fsguerreiro/My_thesis/figs/schemes.pptx

Measurements:
Air flow rate
Air flow temperature
Air flow relative humidity

FRONT VIEW

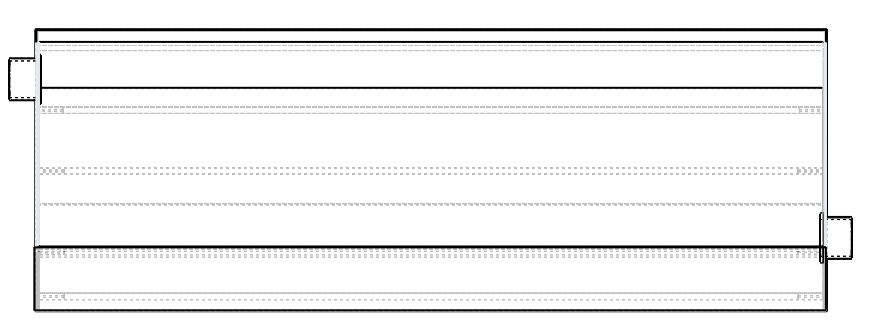
[picture p1: figure]

FAN

OUTLET

INLET

Pressure meter
ΔP = Poutlet - Pinlet

Measurements:
Air flow temperature
Air flow relative humidity

## Slide 2

Material and Instruments for 1 collector

Component | Dimension | | Instrument | Quantity | Range
Reflector Sheet | 1.32m x 1.25m | | Air Flow Meter | 1 | 0 - 20 m/s or 0 - 120 ft³/min
Tempered, Low-e Glass | 270mm x 1246mm x 4 mm | | Fan/Blower | 1 | 10 W
Wool | 1.32m x 1.25m x 5cm | | Pressure Meter | 1 | 0 - 100 Pa or 0 - 10 mmHg
Aluminium Sheet | 1.5m x 1.3m x 1.5mm | | Humidity Meter | 2 | 0 - 100% RH
2 Pipe Connection w/ flange | 10 cm long; 2.5 in of inner diameter | | Thermocouple | 14 | 0 - 200 ºC
Type of experiments w/ control system:
1. Set-point of air flow rate;
2. Set-point of outlet air temperature by manipulating air flow;
3. Set-point of energy delivered by manipulating air flow.

## Slide 3

## Slide 4

l

Absorber
surface

Absorber
hole

dH

## Slide 5

Absorber
hole

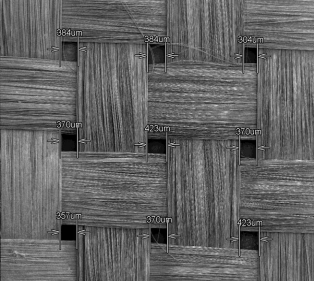
[picture p2: figure]

Absorber surface

l

φh

## Slide 6

y-axis (vertical)

Solar ray

xz plane (top view)

xy plane (cross section view)

z-axis

y-axis (vertical)

Solar ray

αs

z-axis

Solar ray

x-axis (south)

x-axis (south)

γs

γs

αs

x-axis (south)

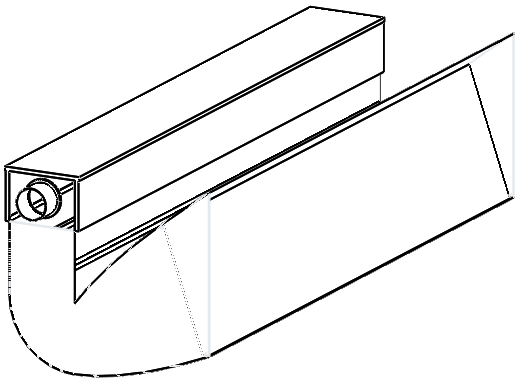
[picture p3: figure]

y-axis

z-axis

x-axis

## Slide 7

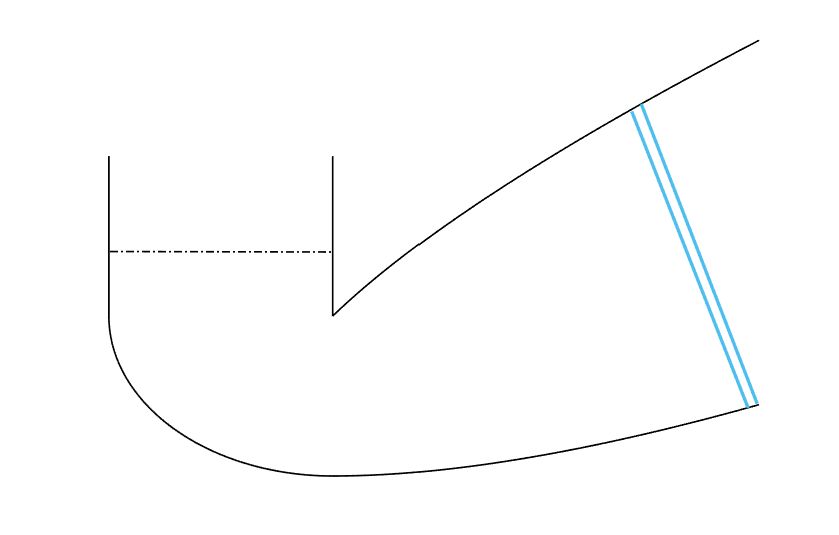
[picture p4: figure]

SOLAR
RADIATION

USEFUL
HEAT

CONVECTION
LOSS

Absorber

RADIATION
LOSS

SOLAR
RADIATION

CONVECTION
LOSS

Glazing

RADIATION
LOSS

## Slide 8

RADIAÇÃO
SOLAR

CALOR
ÚTIL

Absorvedor

PERDAS
CONVECTIVAS

PERDAS
RADIATIVAS

RADIAÇÃO
SOLAR
ABSORVIDA

PERDAS
CONVECTIVAS

Vidro

PERDAS
RADIATIVAS

## Slide 9

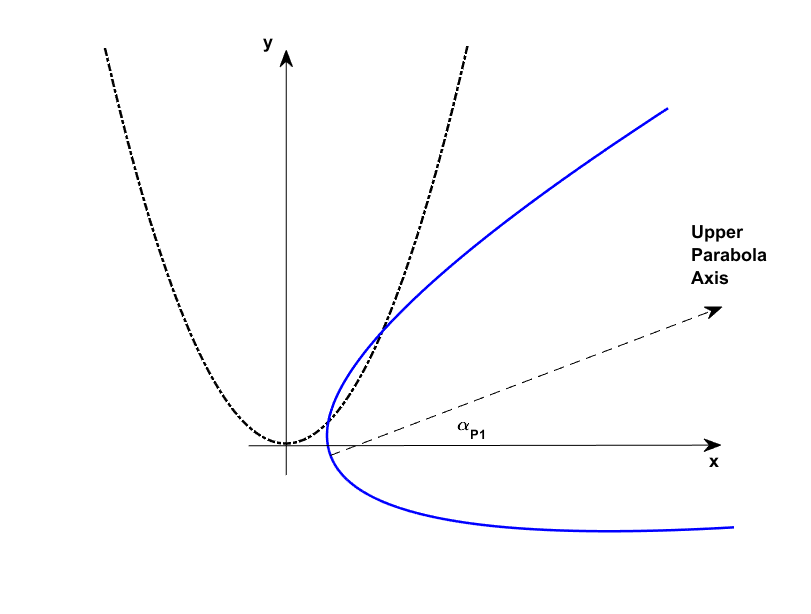
[picture p5: figure]

## Slide 10

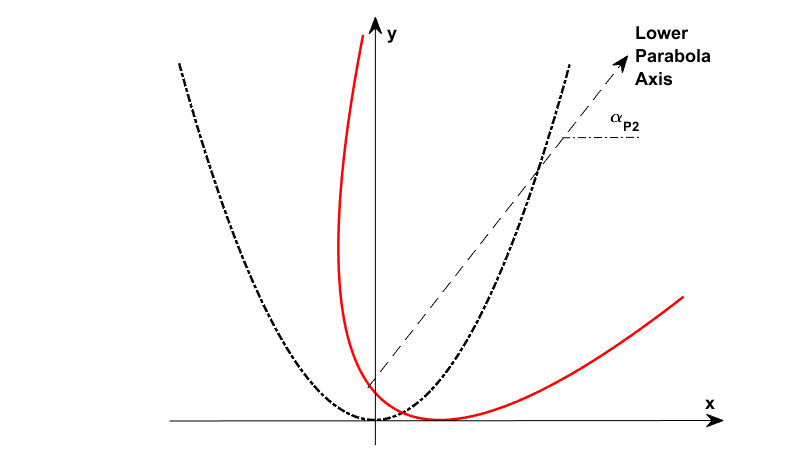
[picture p6: figure]

## Slide 11

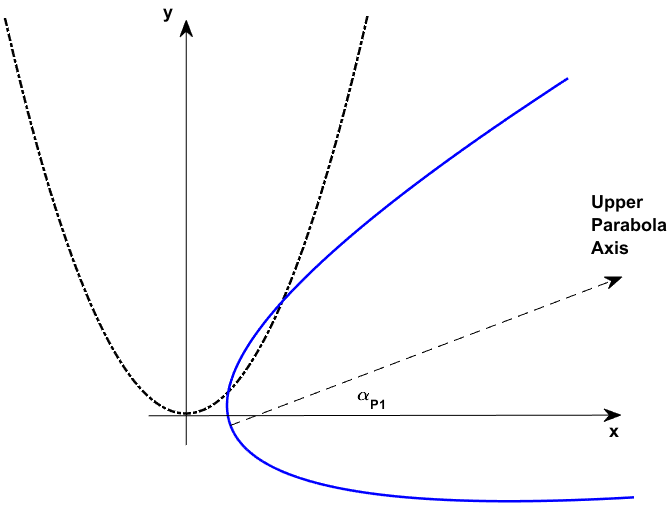
[picture p7: figure]
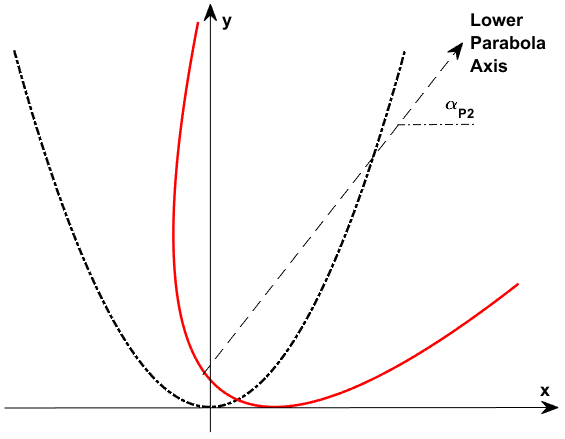
[picture p8: figure]

(a)

(b)

## Slide 12

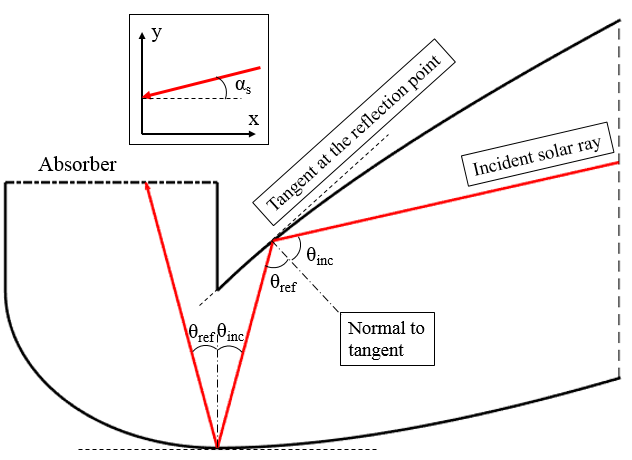
[picture p9: figure]
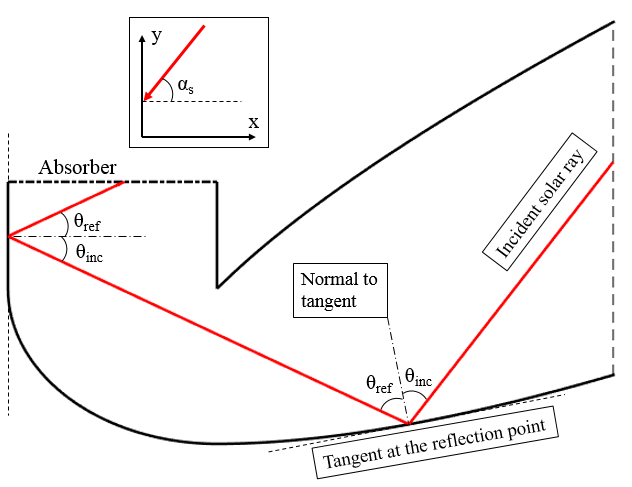
[picture p10: figure]

## Slide 13

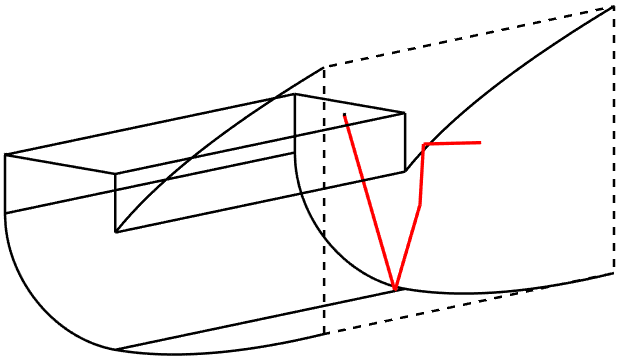
[picture p11: figure]

(a)

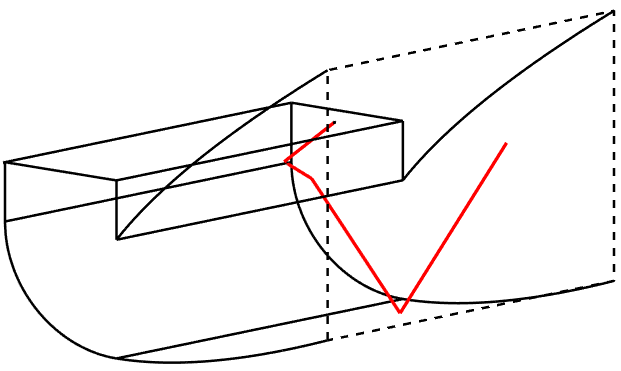
[picture p12: figure]

(d)

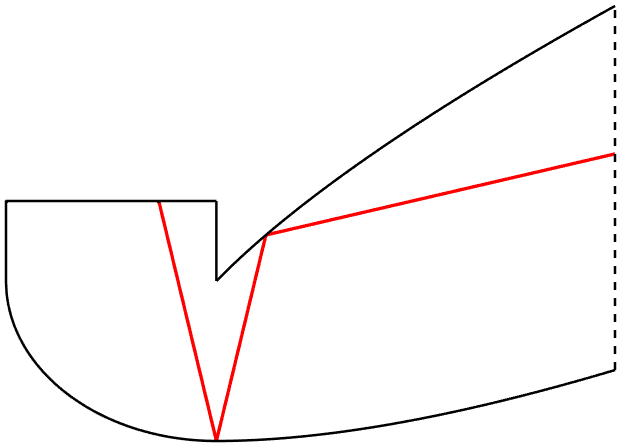
[picture p13: figure]

(b)

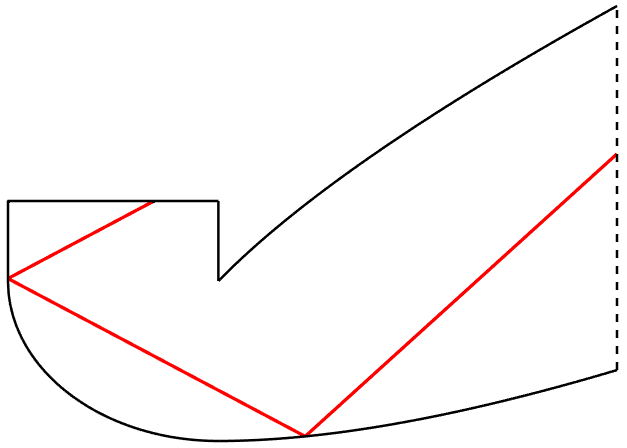
[picture p14: figure]

(e)

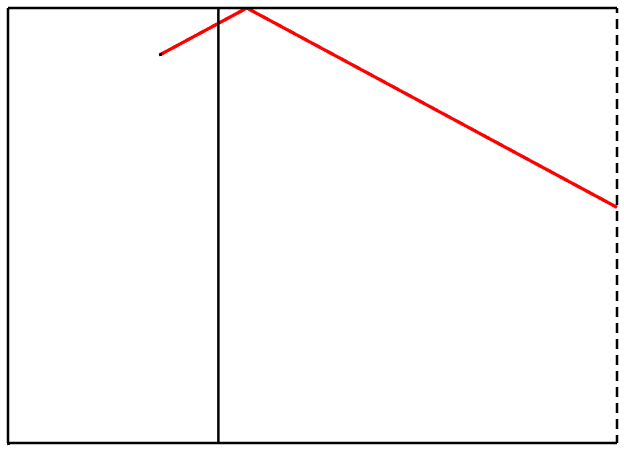
[picture p15: figure]
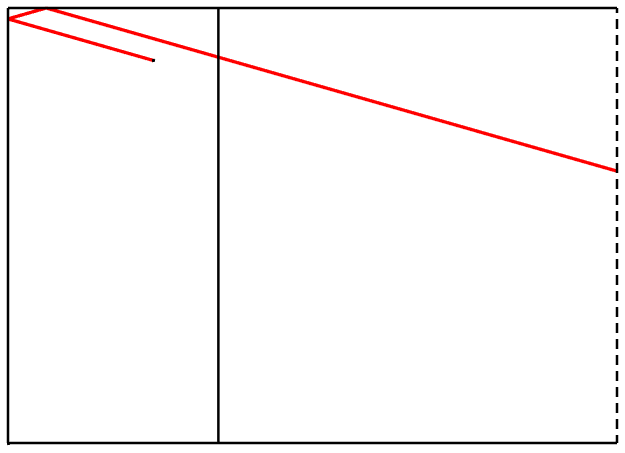
[picture p16: figure]

(c)

(f)

## Slide 14

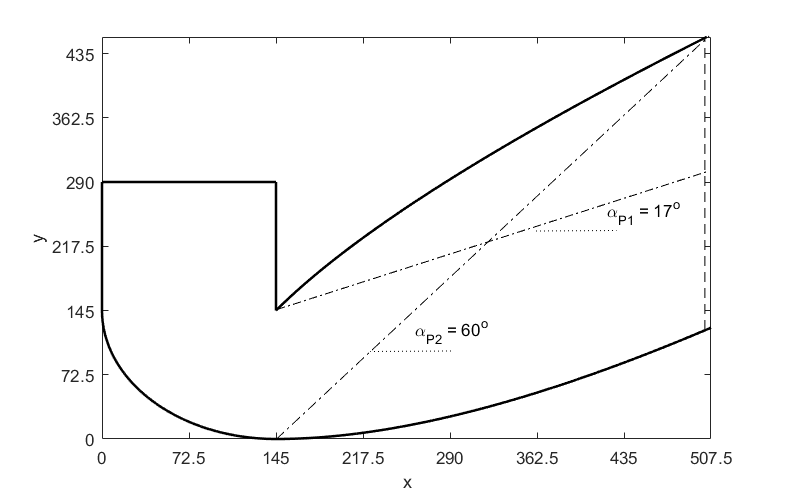
[picture p17: figure]

## Slide 15

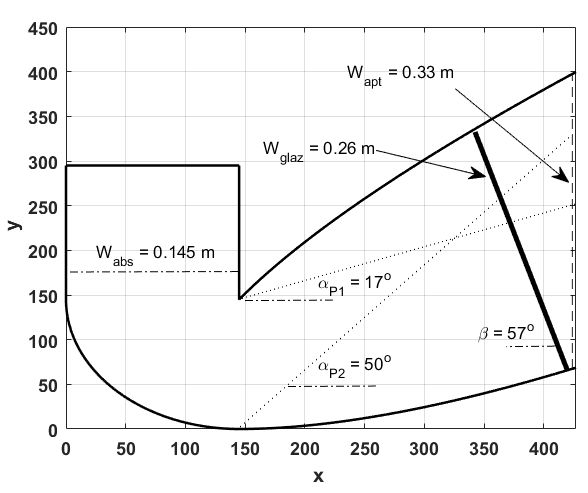
[picture p18: figure]

## Slide 16

POWERSUPPLY

FAN

OUTLET

PROTOTYPE

INLET

## Slide 17

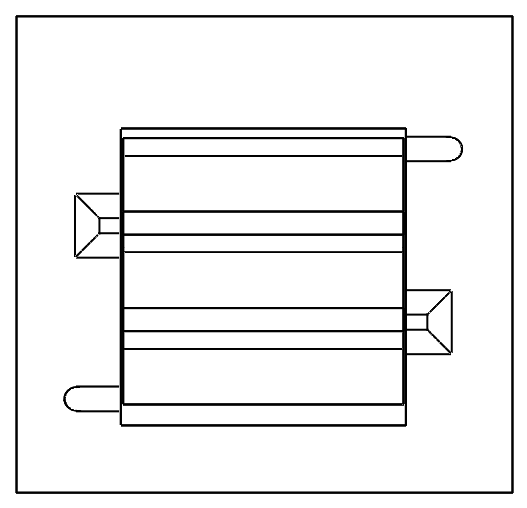
[picture p19: figure]

outlet

IACPC 3

IACPC 2

IACPC 1

inlet

## Slide 18

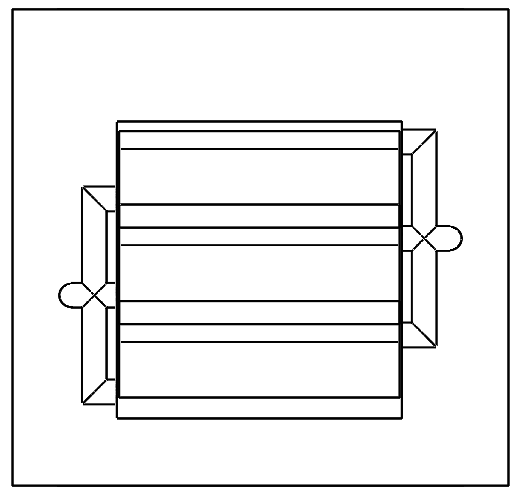
[picture p20: figure]

IACPC 3

IACPC 2

outlet

inlet

IACPC 1

## Slide 19

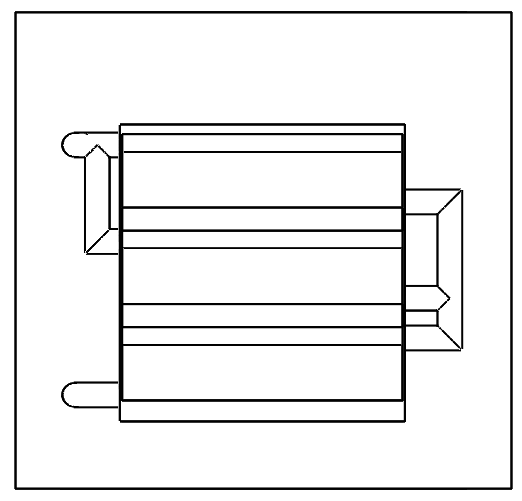
[picture p21: figure]

outlet

IACPC 3

IACPC 2

IACPC 1

inlet

## Slide 20

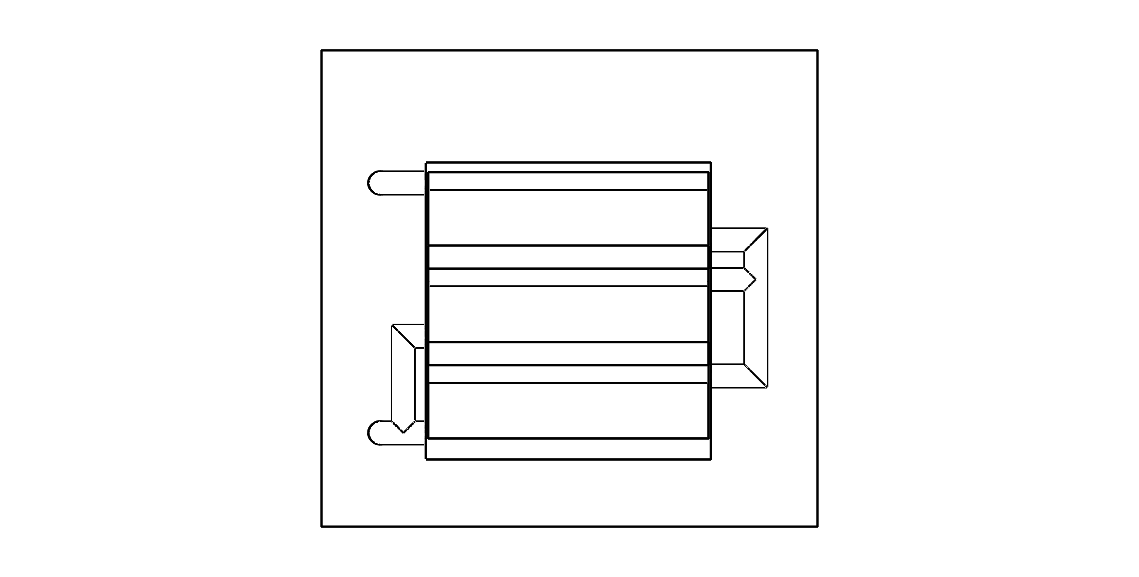
[picture p22: figure]

outlet

IACPC 3

IACPC 2

IACPC 1

inlet

## Slide 21

Main heater (gas burner)

Barley dryer

Auxiliary system (solar collector(s))
