fsguerreiro/My_thesis/figs/schematics_intro-eps-converted-to.pdf

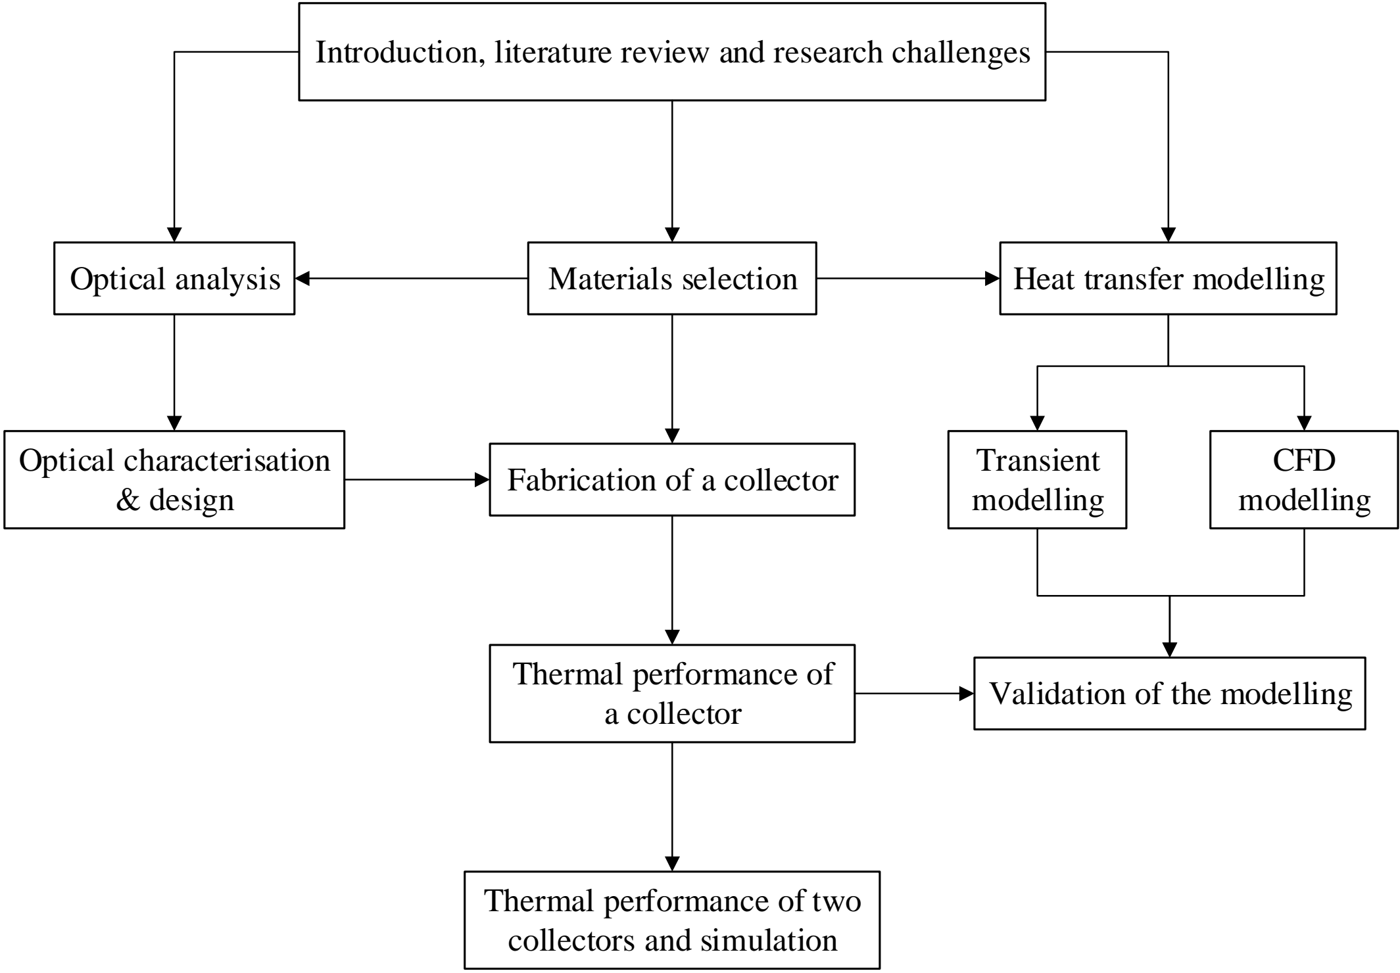
[picture p23: figure]
Materials selection; Fabrication of a collector; Optical analysis; Heat transfer modelling; Transient modelling; CFD modelling; Optical characterisation & design; Thermal performance of; a collector; Validation of the modelling; Thermal performance of two collectors and simulation

Introduction, literature review and research challenges
