fsguerreiro/My_thesis/figs/block_diagram-eps-converted-to.pdf

## AIR HEATING SYSTEM’S HEAT TRANSFER MODEL

Outlet air temperature (Tout)

Thermal efficiency (ηth)

Useful energy rate (Qu)

Airflow rate (Gair)

Ambient temperature (Tamb) and wind speed (vw)

Solar radiation (IT)

Inlet air temperature (Tin)
