fsguerreiro/My_thesis/figs/case_ch4-eps-converted-to.pdf

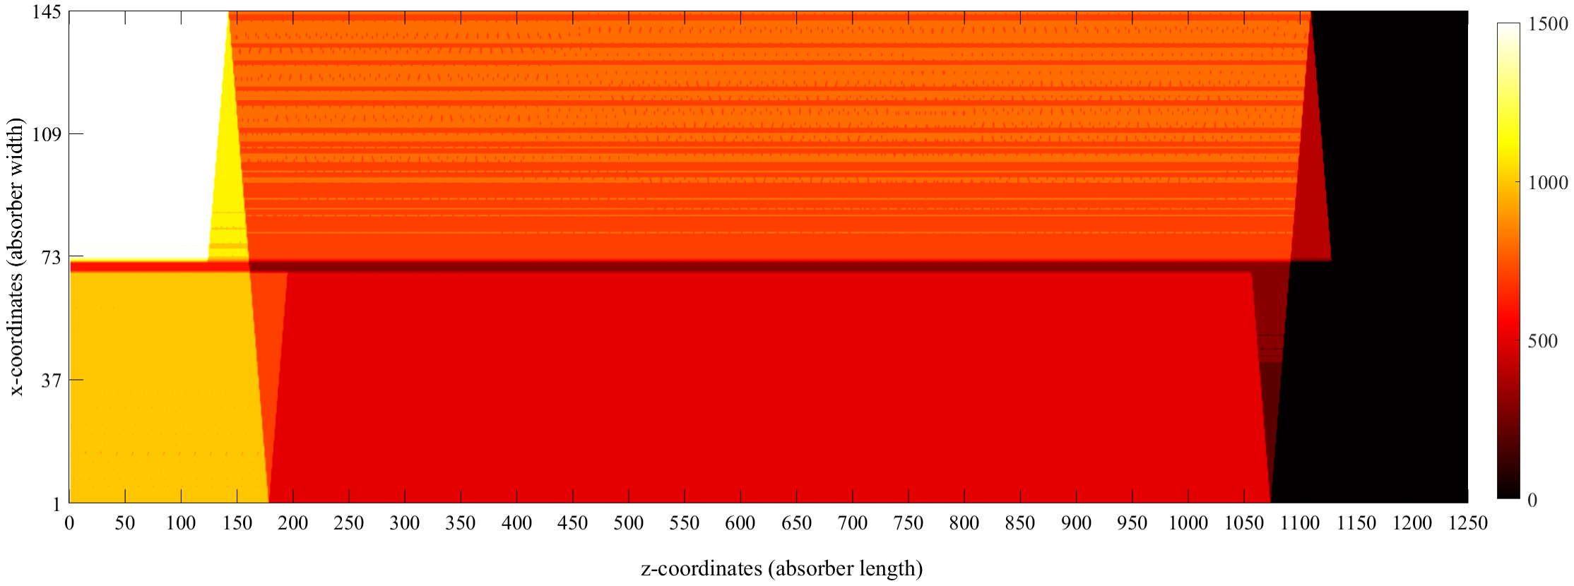
[picture p29: page 1]
