fsguerreiro/My_thesis/figs/3D-diagram-15-eps-converted-to.pdf

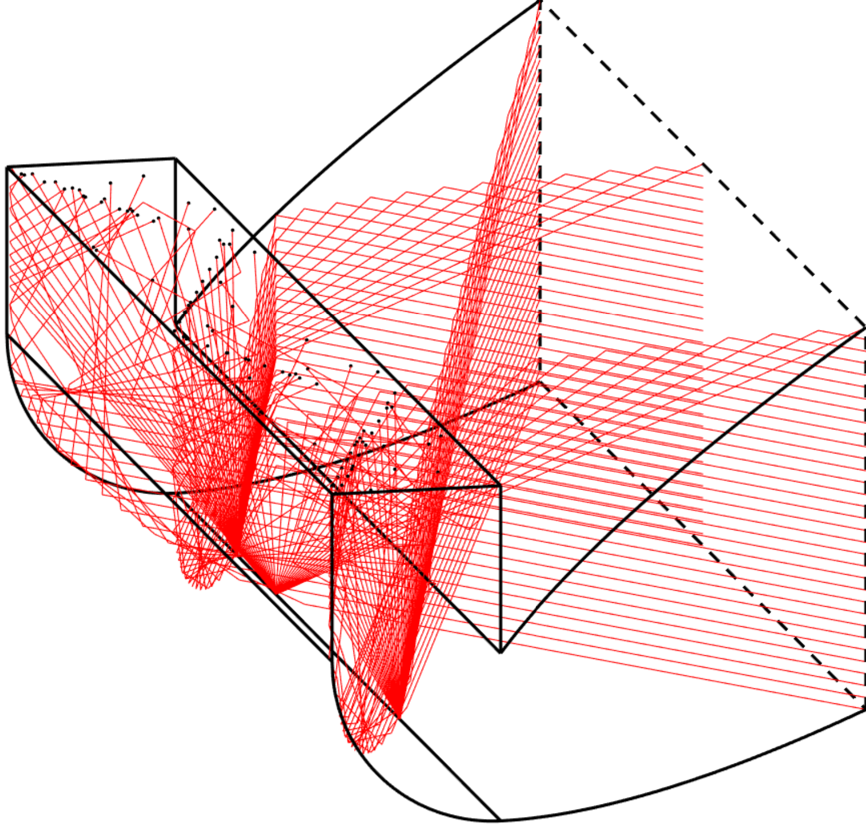
[picture p30: page 1]
