fsguerreiro/My_thesis/figs/3D-diagram-60-eps-converted-to.pdf

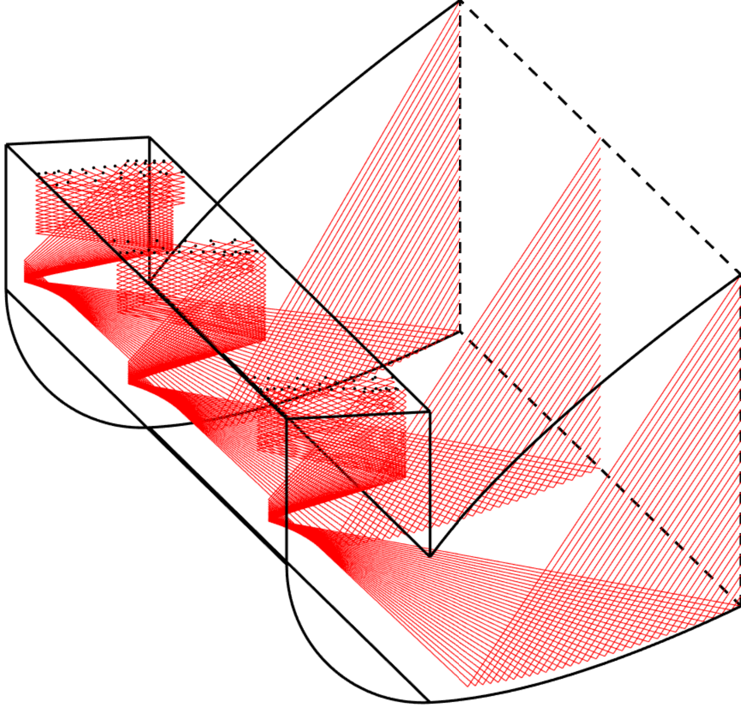
[picture p31: page 1]
