fsguerreiro/My_thesis/figs/cdf_Q-eps-converted-to.pdf

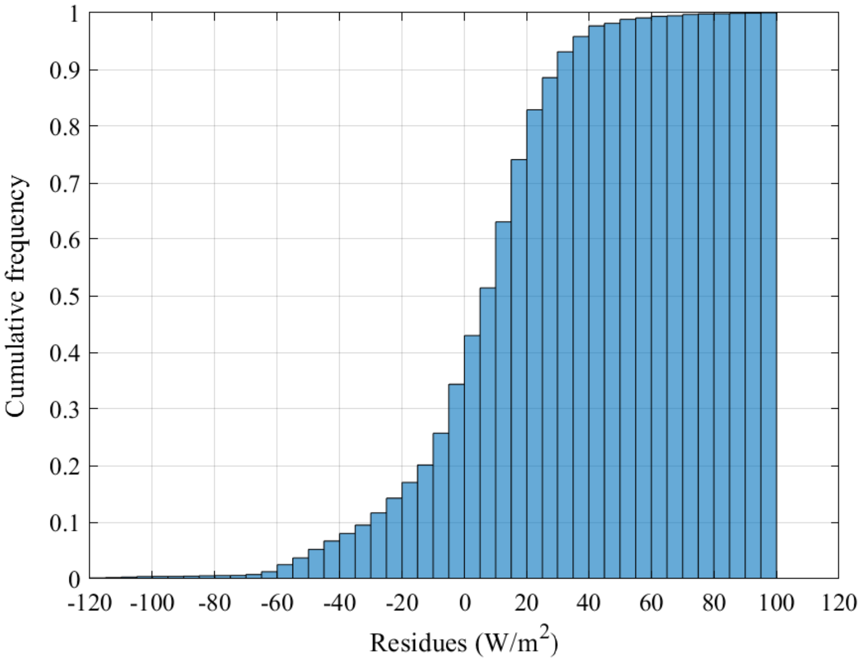
[picture p32: page 1]
