fsguerreiro/My_thesis/figs/cdf_T-eps-converted-to.pdf

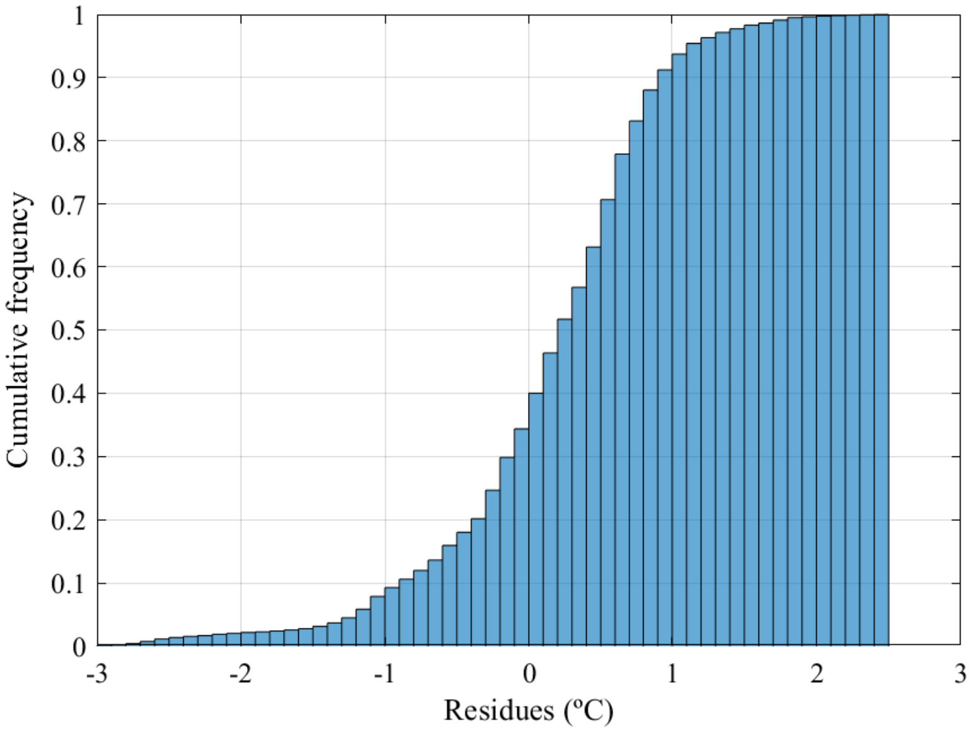
[picture p33: page 1]
