fsguerreiro/My_thesis/figs/collector3p-eps-converted-to.pdf

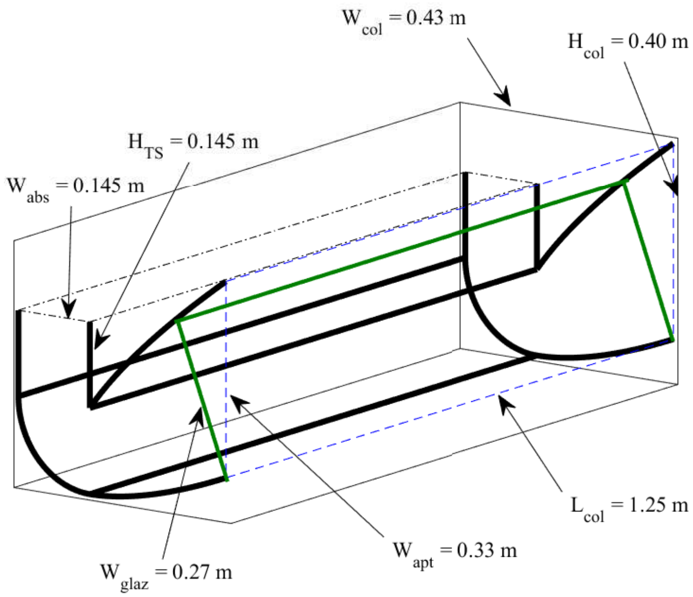
[picture p34: page 1]
