fsguerreiro/My_thesis/figs/energy-54-49-hts0-eps-converted-to.pdf

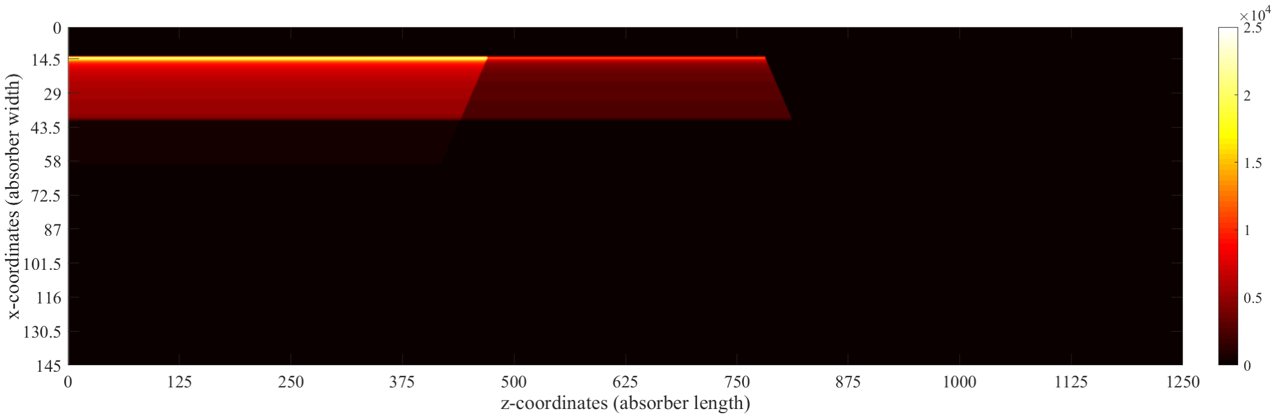
[picture p35: page 1]
