fsguerreiro/My_thesis/figs/Energy2D-hts0-eps-converted-to.pdf

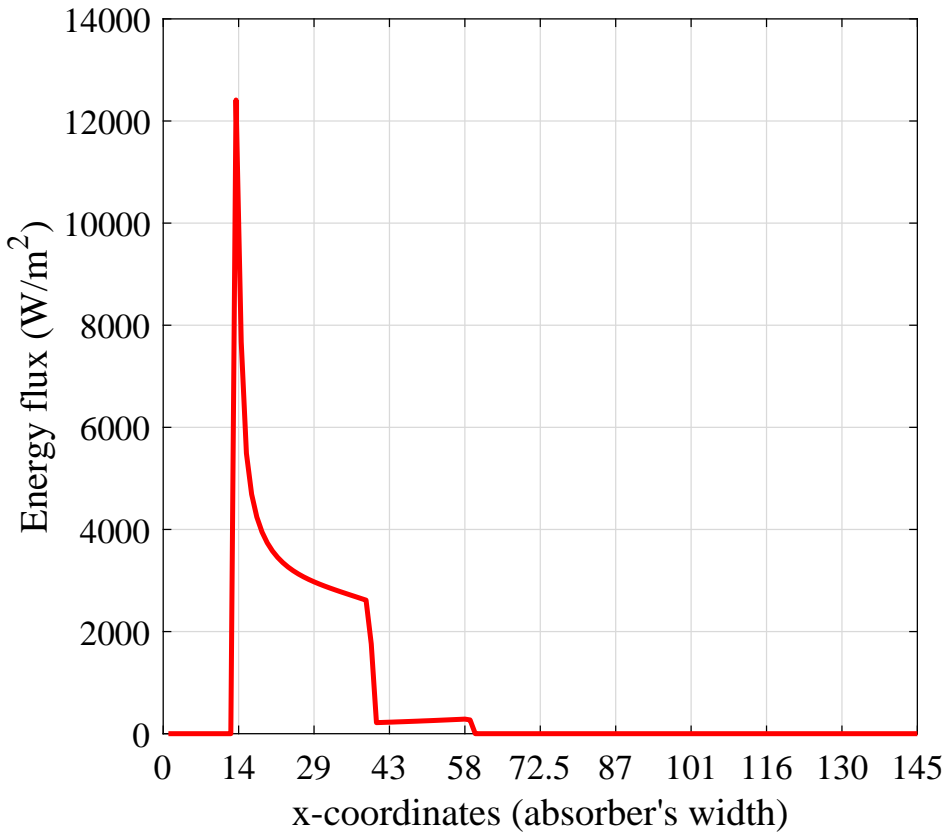
[picture p36: figure]
x-coordinates (absorber's width); Energy flux (W/m
