fsguerreiro/My_thesis/figs/Energy2D-hts145-eps-converted-to.pdf

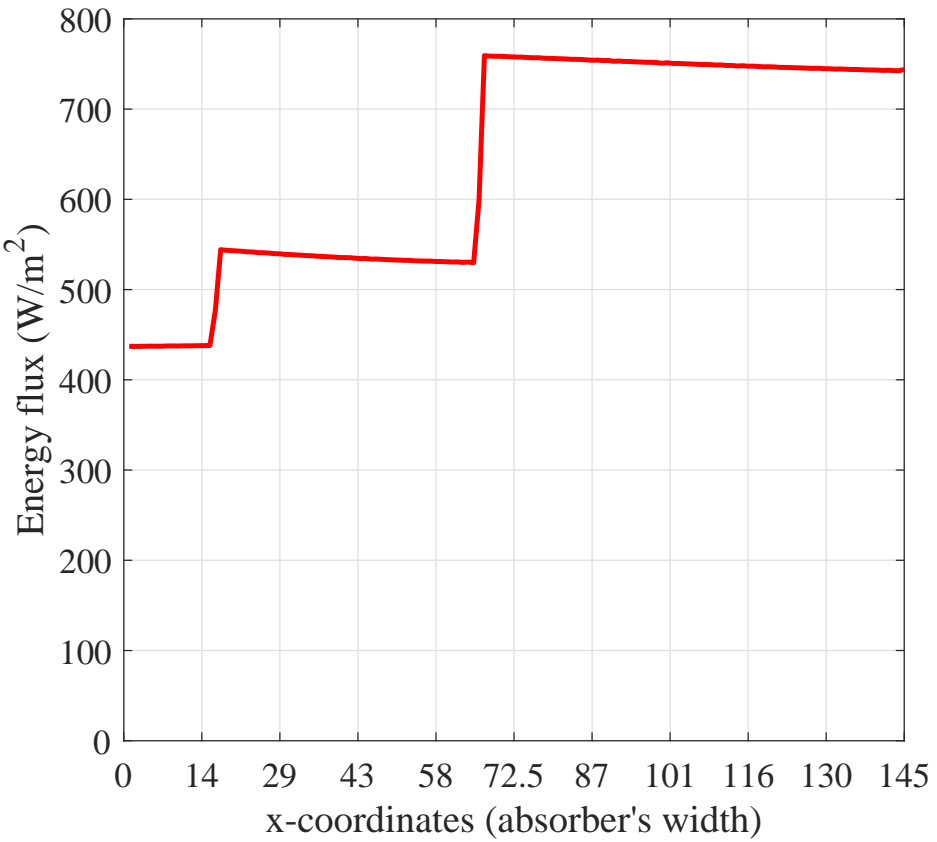
[picture p37: figure]
x-coordinates (absorber's width); Energy flux (W/m
