fsguerreiro/My_thesis/figs/Energy2D-hts72-eps-converted-to.pdf

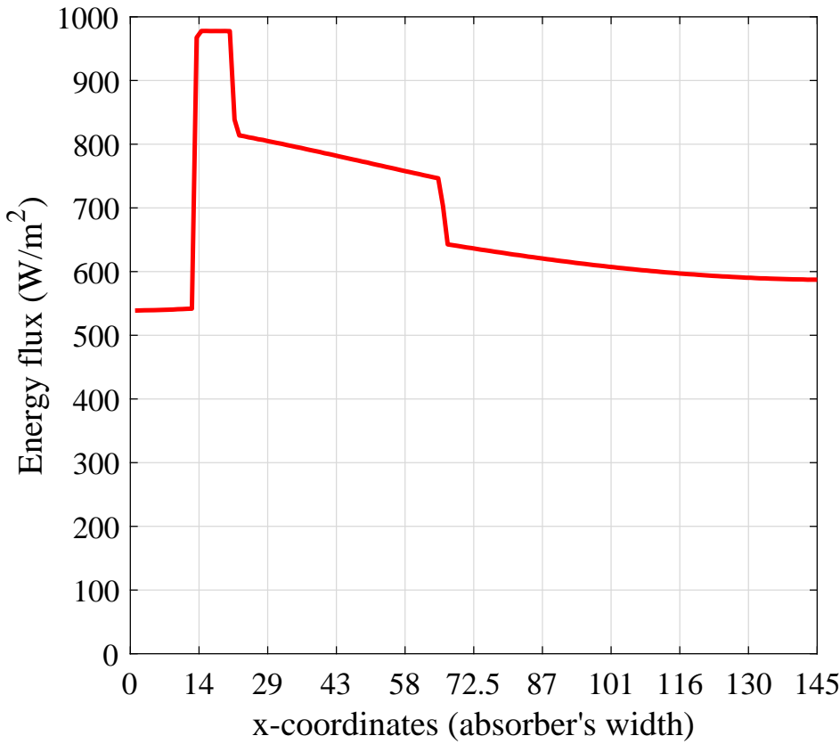
[picture p38: figure]
x-coordinates (absorber's width); Energy flux (W/m
