fsguerreiro/My_thesis/figs/Energy3D-hts0-eps-converted-to.pdf

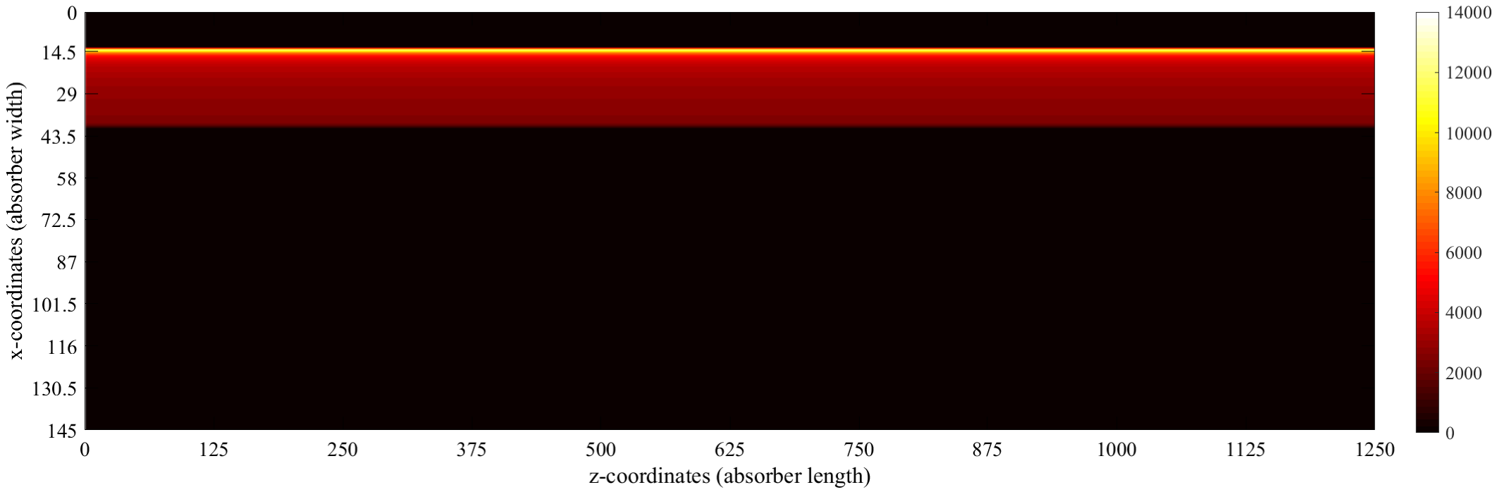
[picture p39: page 1]
