fsguerreiro/My_thesis/figs/opt-eff-time-eps-converted-to.pdf

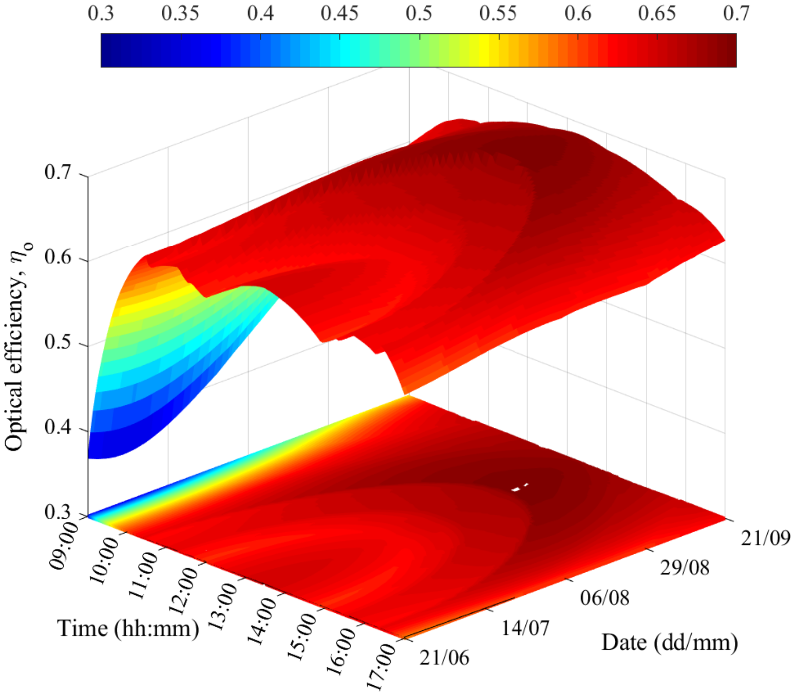
[picture p40: page 1]
