fsguerreiro/My_thesis/figs/2D-diagram-15.png

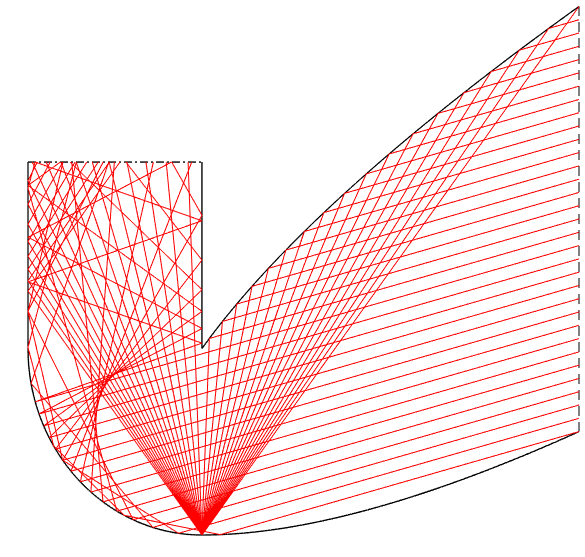
figs/2D-diagram-15.png
