fsguerreiro/My_thesis/figs/2D-diagram-60.png

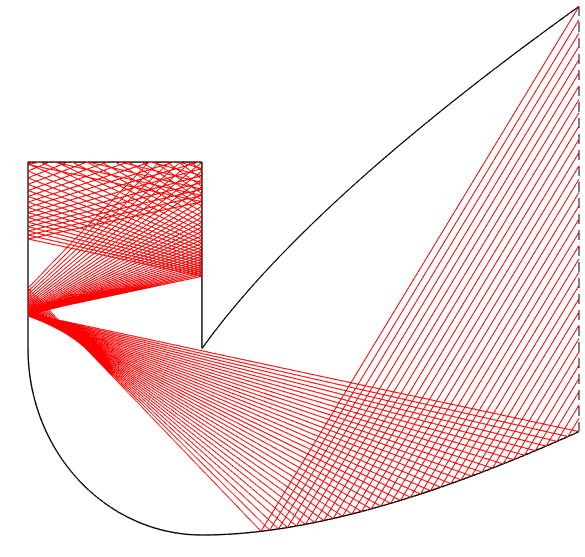
figs/2D-diagram-60.png
