fsguerreiro/My_thesis/figs/3D-diagram-1.png

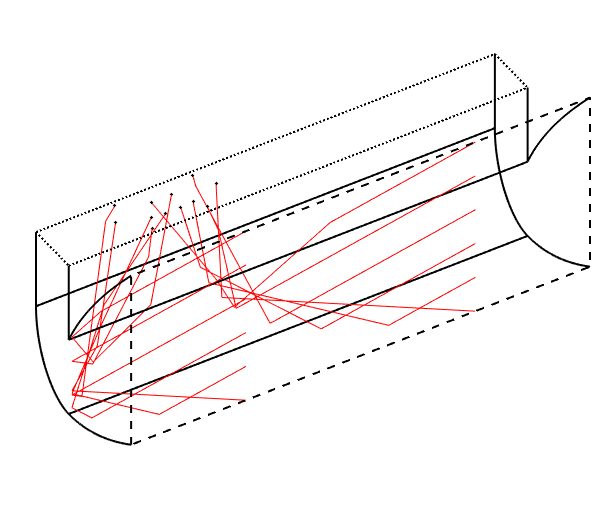
figs/3D-diagram-1.png
