fsguerreiro/My_thesis/figs/3D-diagram-15.png

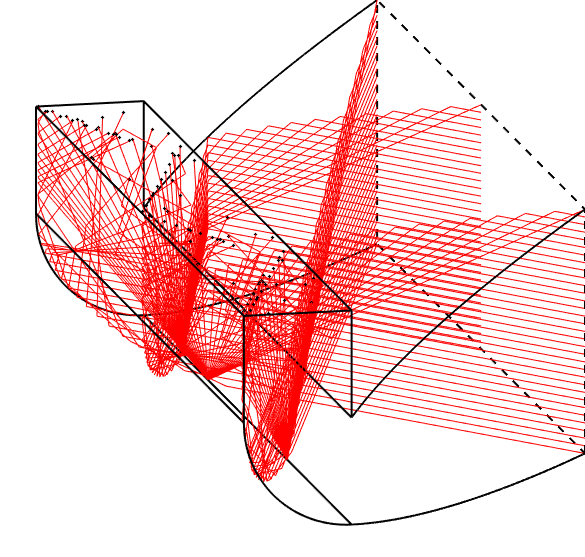
figs/3D-diagram-15.png
