fsguerreiro/My_thesis/figs/3D-diagram-60.png

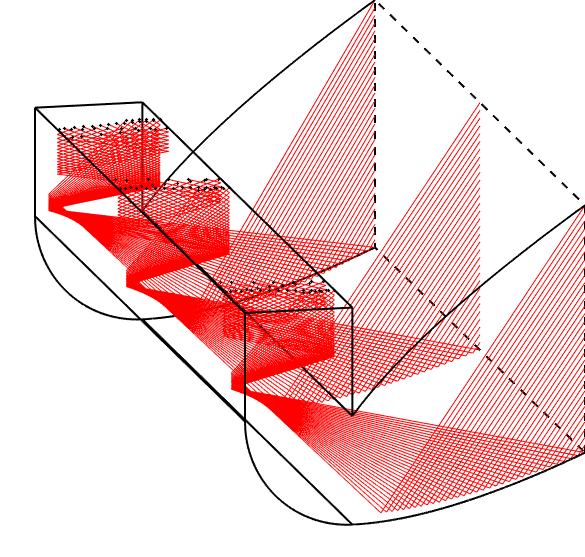
figs/3D-diagram-60.png
