fsguerreiro/My_thesis/figs/004-1.png

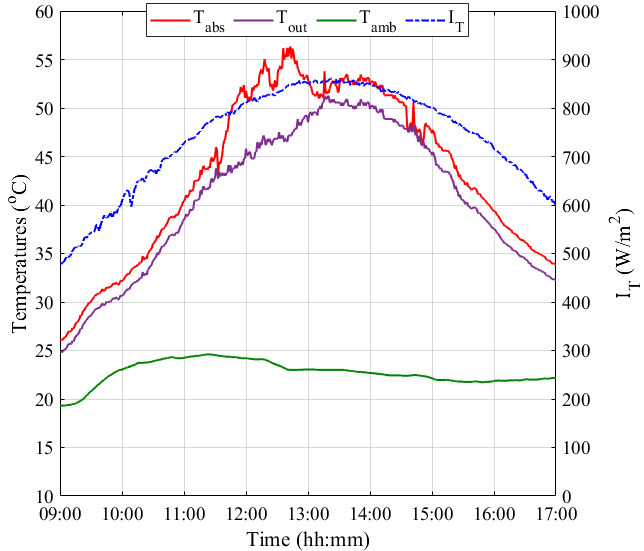
figs/004-1.png
