fsguerreiro/My_thesis/figs/004-2.png

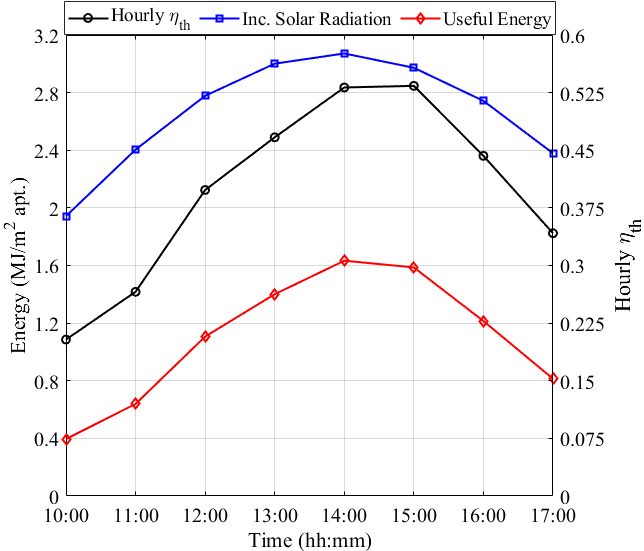
figs/004-2.png
