fsguerreiro/My_thesis/figs/004-3.png

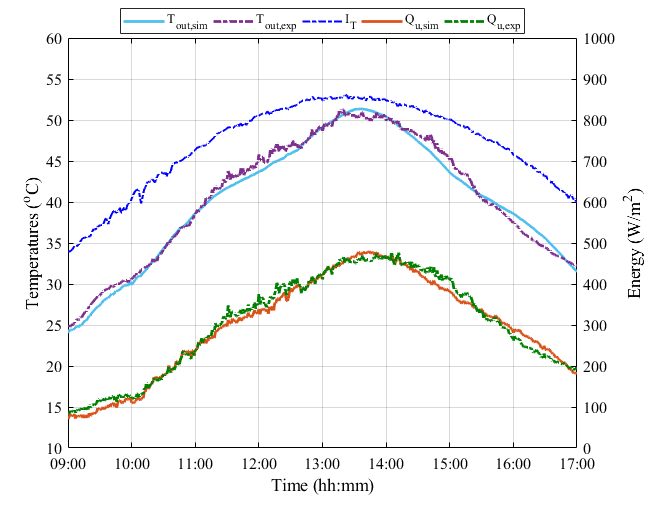
figs/004-3.png
