fsguerreiro/My_thesis/figs/004-residue-1.png

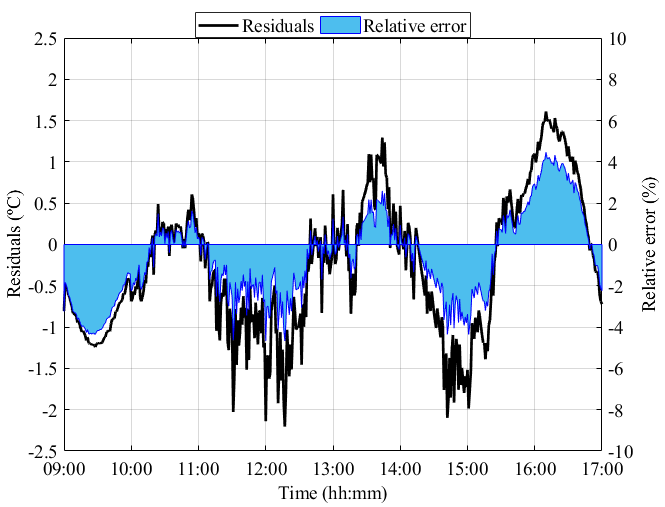
figs/004-residue-1.png
