fsguerreiro/My_thesis/figs/004-residue-2.png

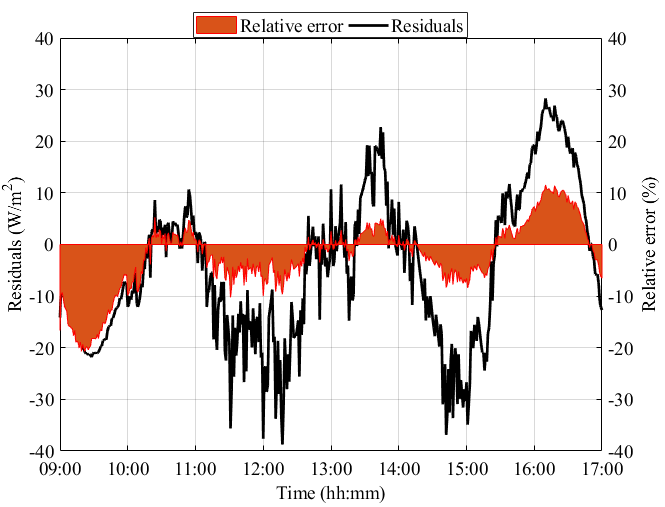
figs/004-residue-2.png
