fsguerreiro/My_thesis/figs/004-residue-3.png

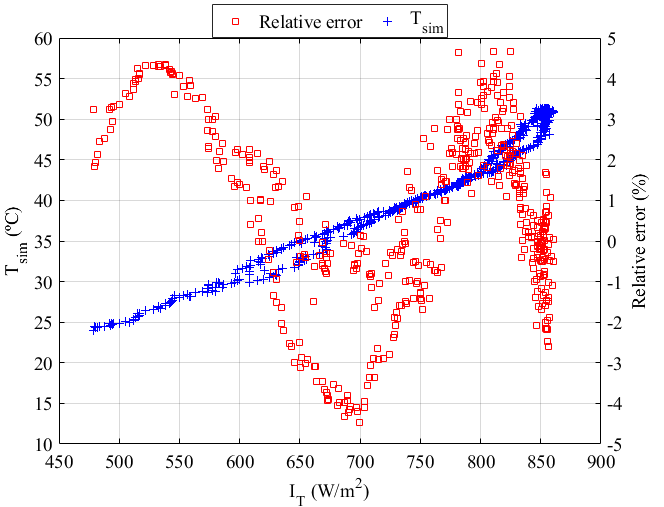
figs/004-residue-3.png
