fsguerreiro/My_thesis/figs/004-residue-4.png

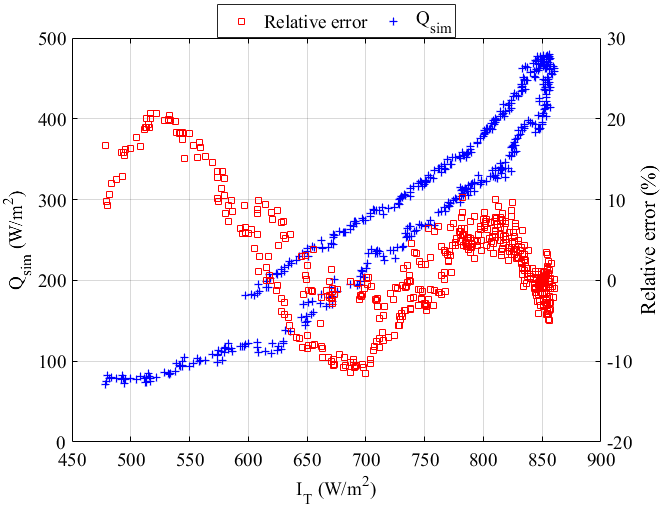
figs/004-residue-4.png
