fsguerreiro/My_thesis/figs/004-residue-5.png

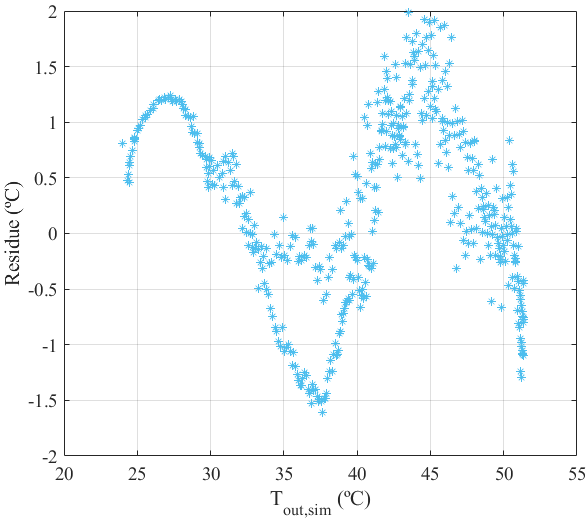
figs/004-residue-5.png
