fsguerreiro/My_thesis/figs/004-residue-6.png

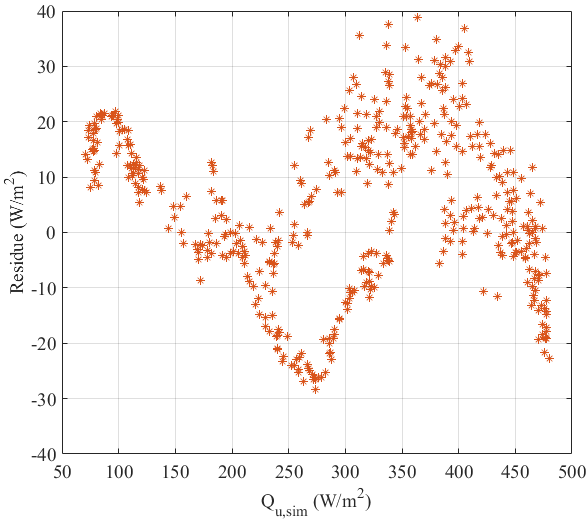
figs/004-residue-6.png
