fsguerreiro/My_thesis/figs/007-1.png

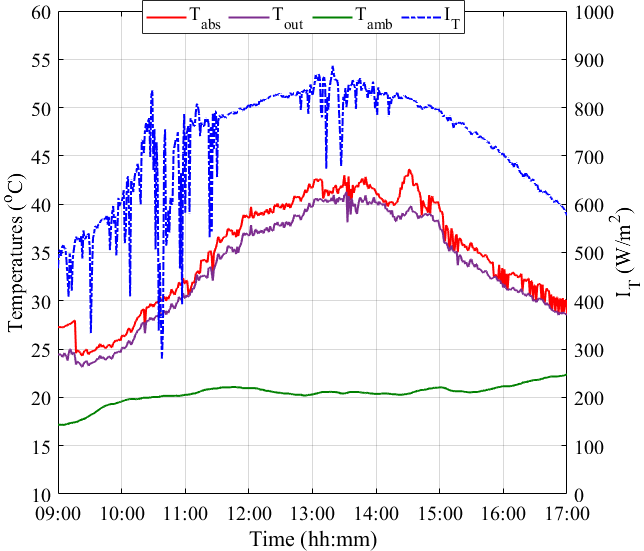
figs/007-1.png
