fsguerreiro/My_thesis/figs/007-2.png

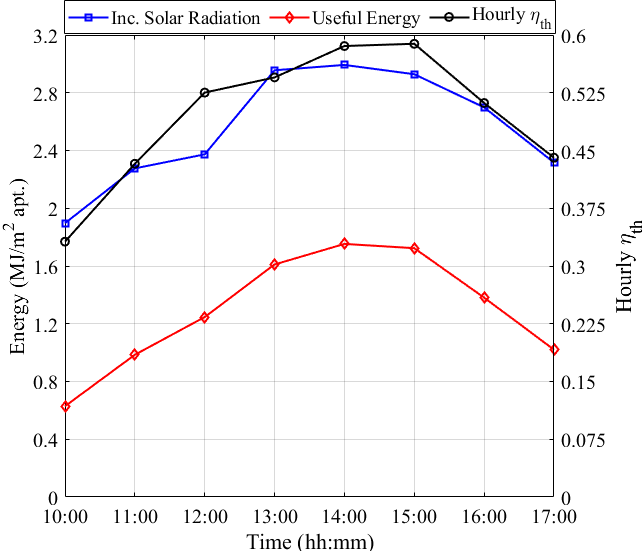
figs/007-2.png
