fsguerreiro/My_thesis/figs/007-3.png

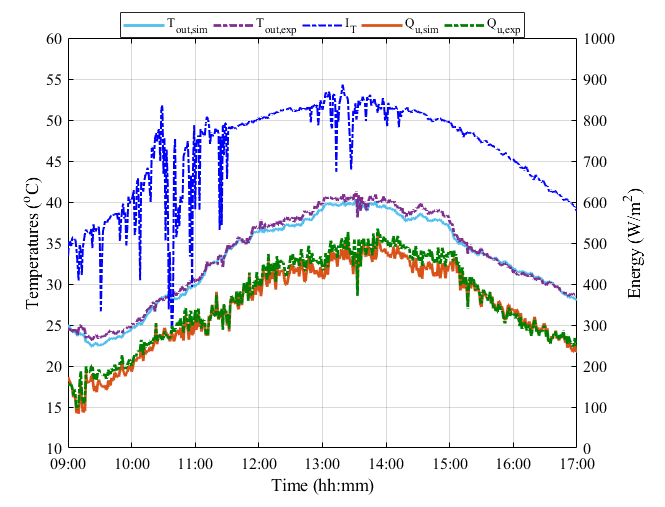
figs/007-3.png
