fsguerreiro/My_thesis/figs/007-residue-1.png

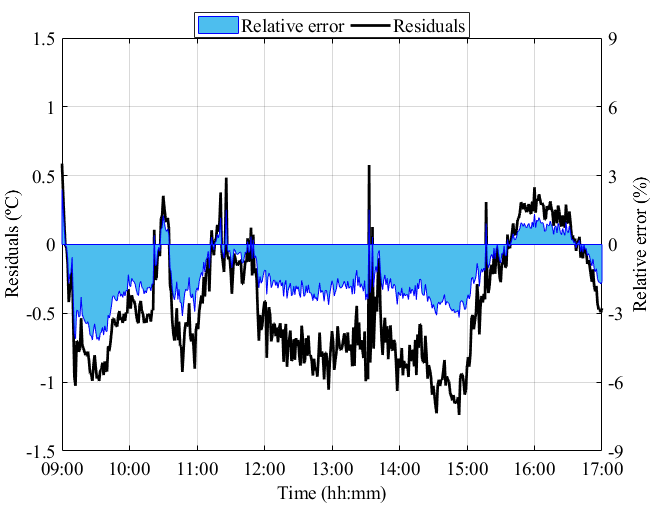
figs/007-residue-1.png
