fsguerreiro/My_thesis/figs/007-residue-2.png

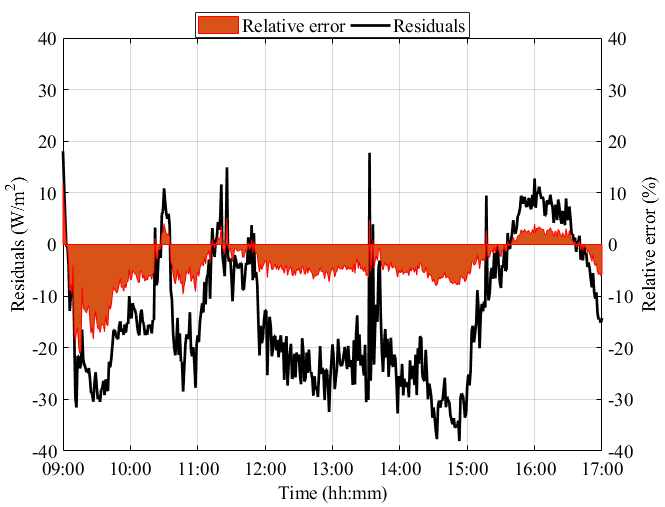
figs/007-residue-2.png
