fsguerreiro/My_thesis/figs/007-residue-3.png

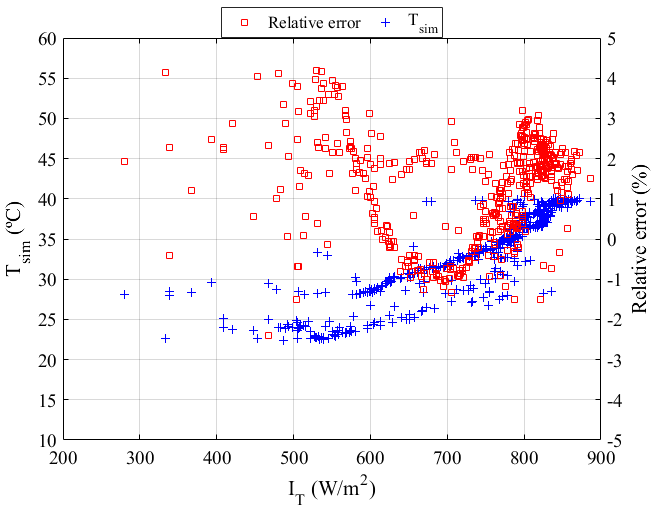
figs/007-residue-3.png
