fsguerreiro/My_thesis/figs/007-residue-4.png

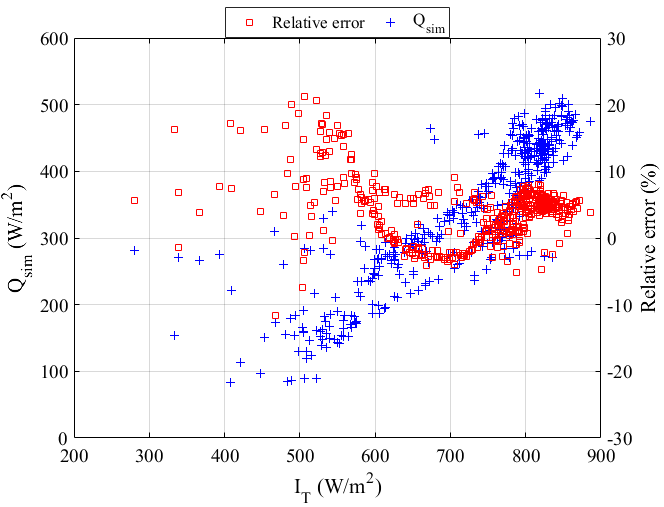
figs/007-residue-4.png
