fsguerreiro/My_thesis/figs/007-residue-5.png

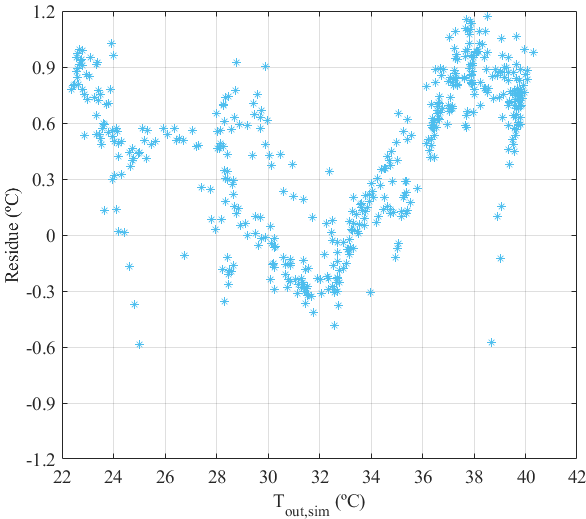
figs/007-residue-5.png
