fsguerreiro/My_thesis/figs/007-residue-6.png

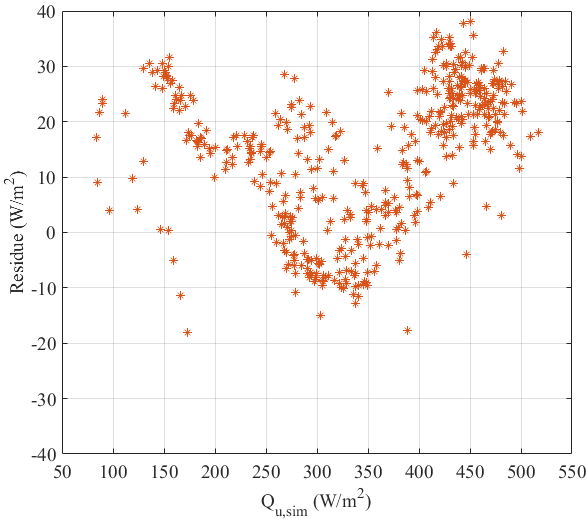
figs/007-residue-6.png
