fsguerreiro/My_thesis/figs/009-1.png

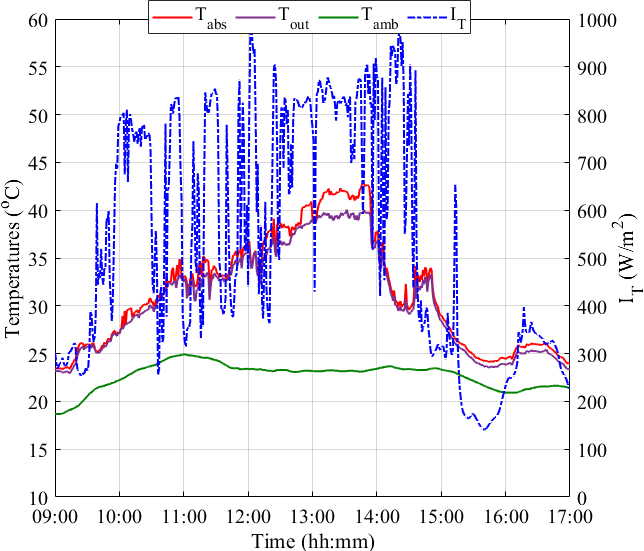
figs/009-1.png
