fsguerreiro/My_thesis/figs/009-2.png

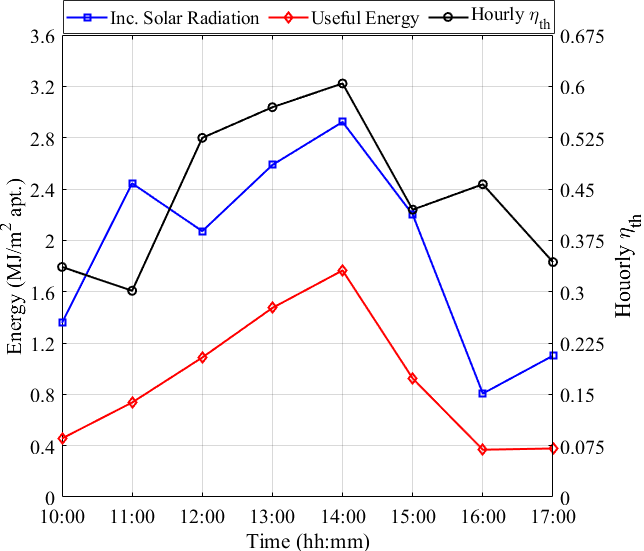
figs/009-2.png
