fsguerreiro/My_thesis/figs/009-3.png

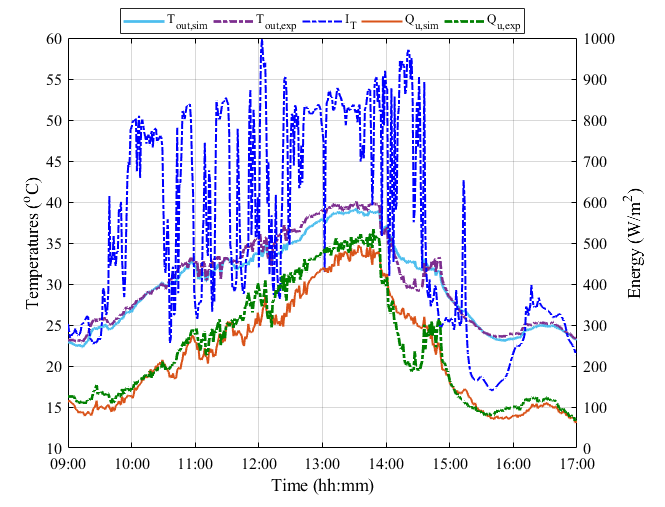
figs/009-3.png
