fsguerreiro/My_thesis/figs/009-residue-1.png

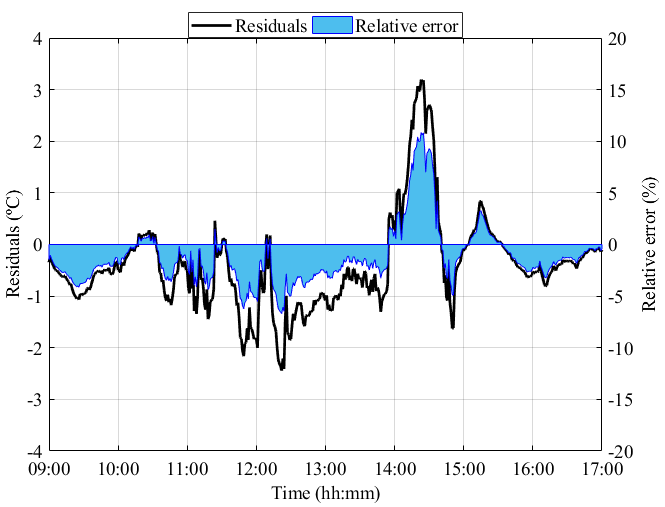
figs/009-residue-1.png
