fsguerreiro/My_thesis/figs/009-residue-2.png

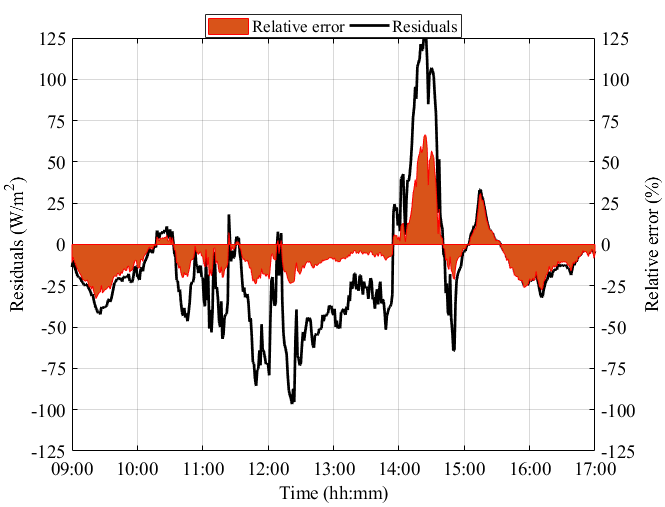
figs/009-residue-2.png
