fsguerreiro/My_thesis/figs/009-residue-3.png

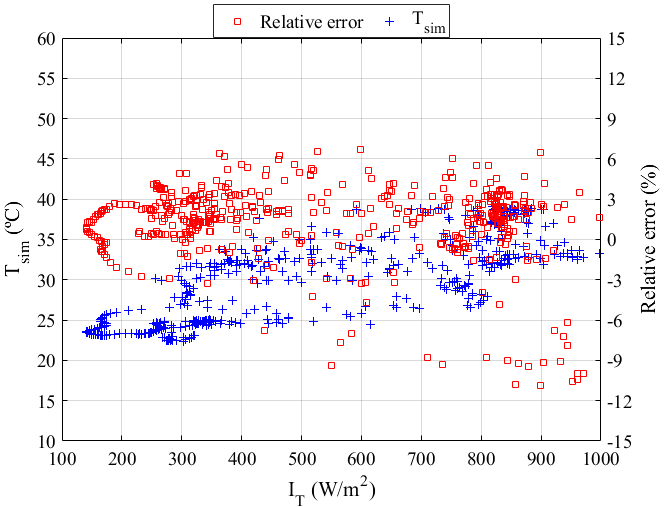
figs/009-residue-3.png
