fsguerreiro/My_thesis/figs/009-residue-4.png

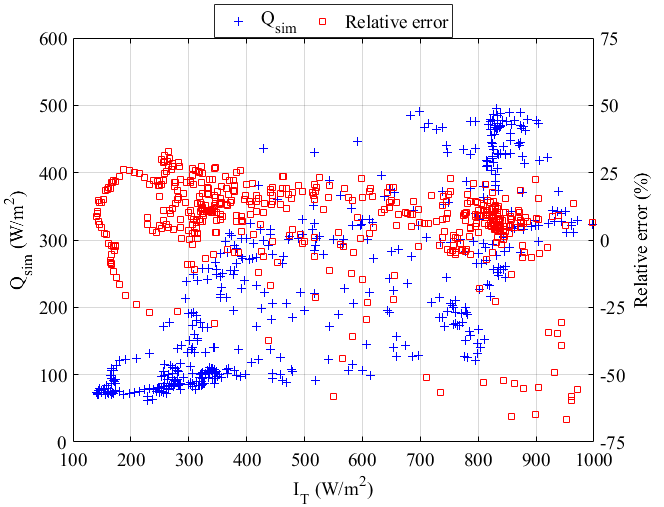
figs/009-residue-4.png
