fsguerreiro/My_thesis/figs/009-residue-5.png

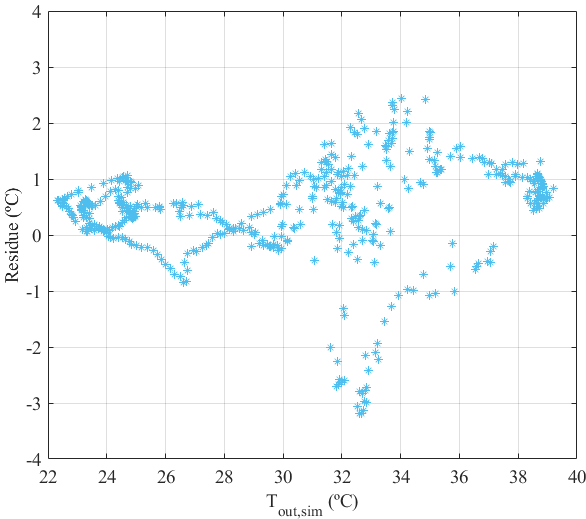
figs/009-residue-5.png
