fsguerreiro/My_thesis/figs/009-residue-6.png

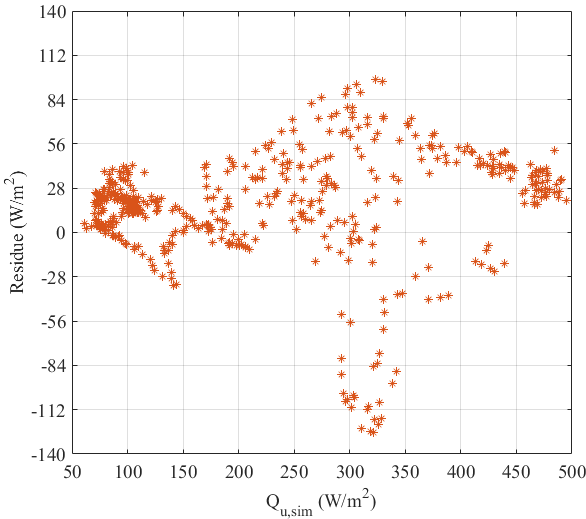
figs/009-residue-6.png
