fsguerreiro/My_thesis/figs/0055-1.png

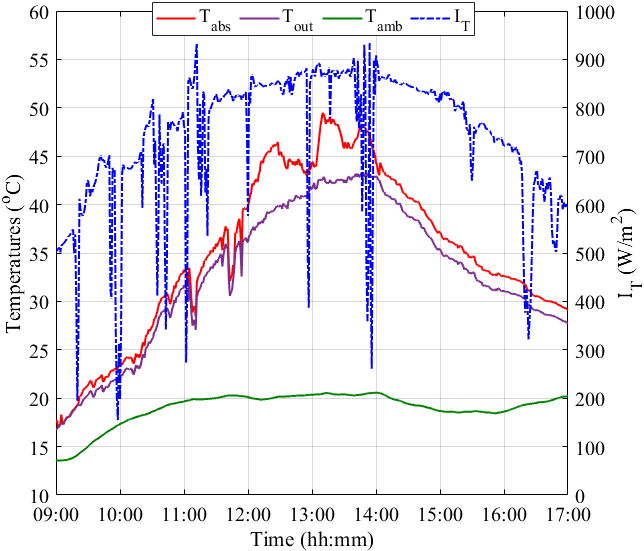
figs/0055-1.png
