fsguerreiro/My_thesis/figs/0055-2.png

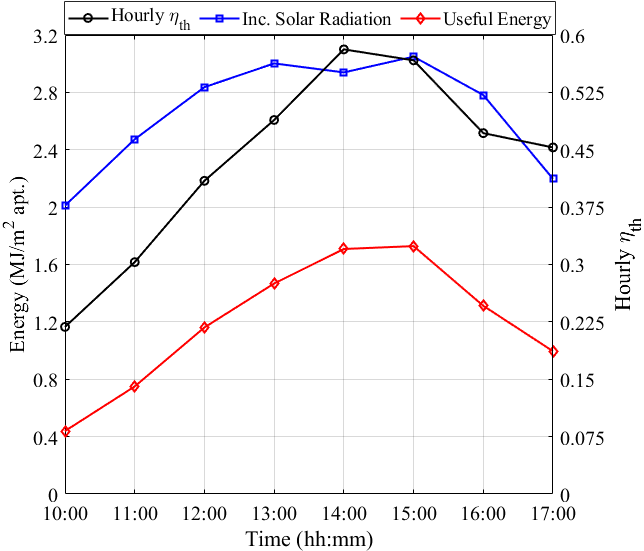
figs/0055-2.png
