fsguerreiro/My_thesis/figs/0055-residue-2.png

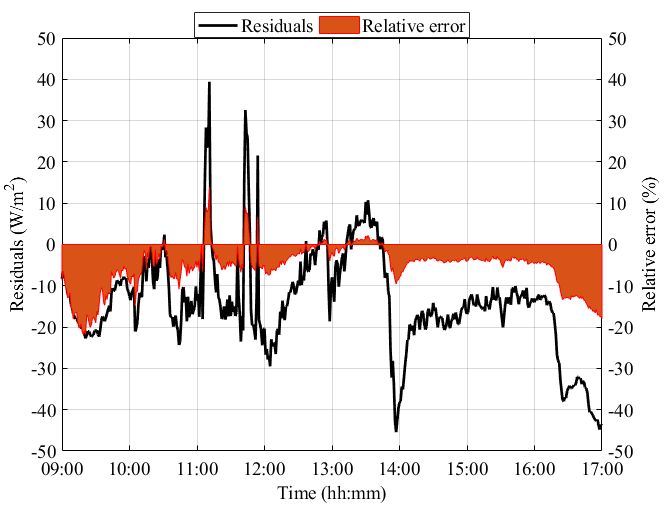
figs/0055-residue-2.png
