fsguerreiro/My_thesis/figs/0055-residue-3.png

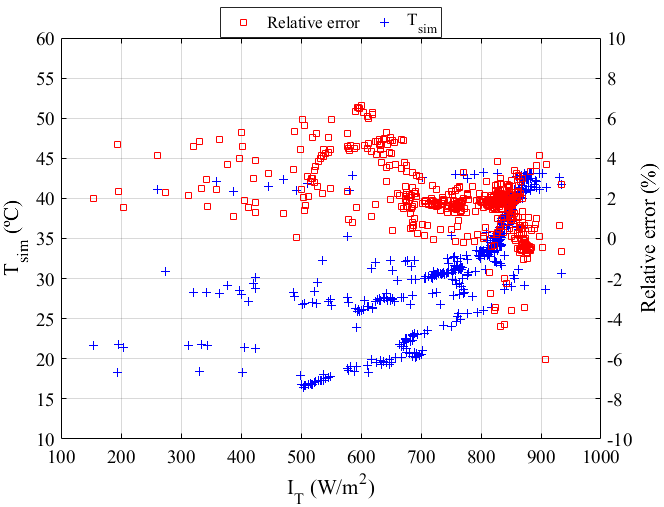
figs/0055-residue-3.png
