fsguerreiro/My_thesis/figs/0055-residue-4.png

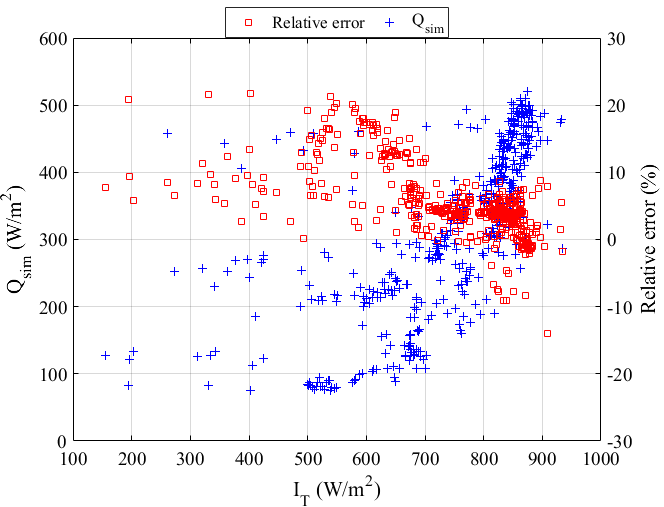
figs/0055-residue-4.png
