fsguerreiro/My_thesis/figs/0055-residue-5.png

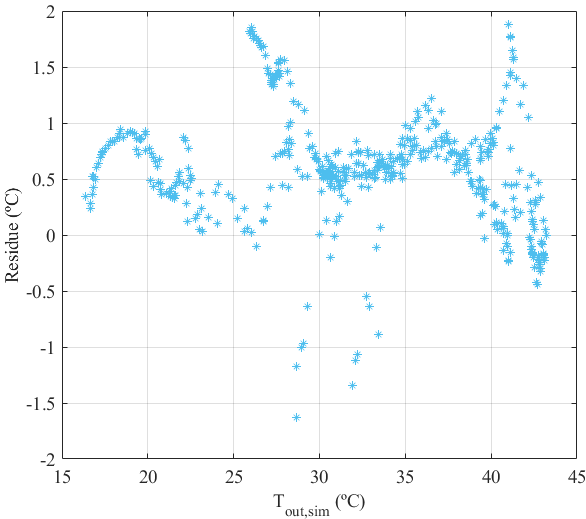
figs/0055-residue-5.png
