fsguerreiro/My_thesis/figs/0055-residue-6.png

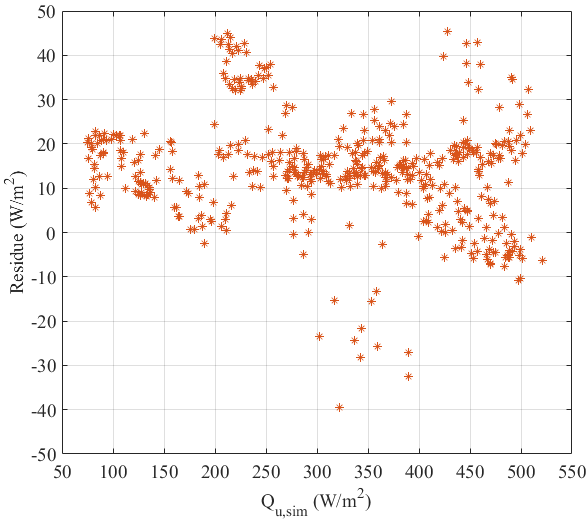
figs/0055-residue-6.png
