fsguerreiro/My_thesis/figs/0115-1.png

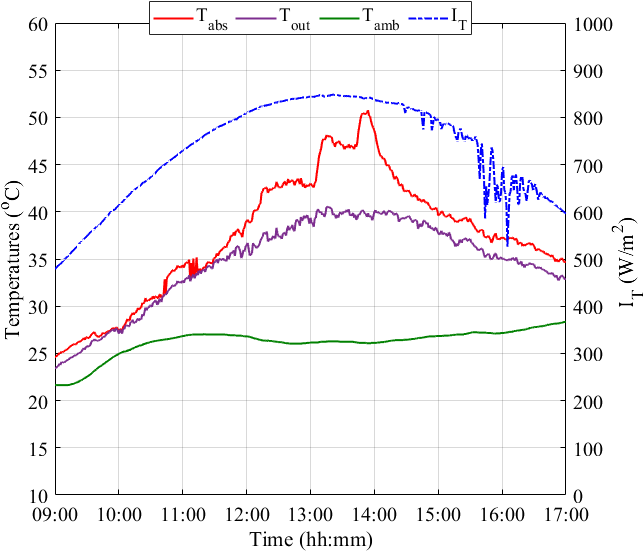
figs/0115-1.png
