fsguerreiro/My_thesis/figs/0115-2.png

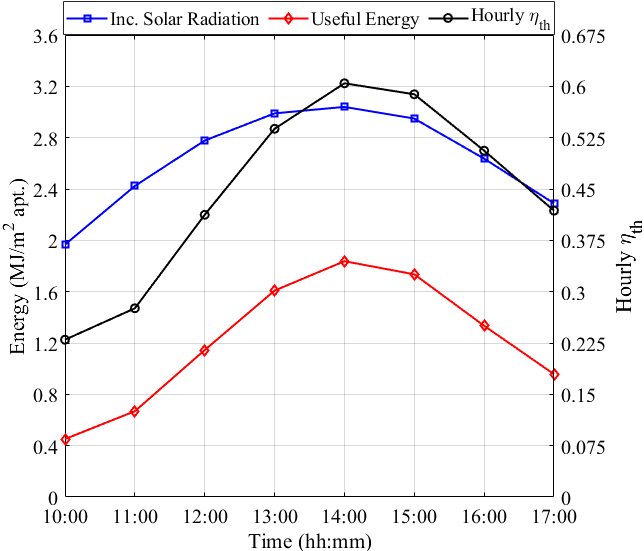
figs/0115-2.png
