fsguerreiro/My_thesis/figs/0115-3.png

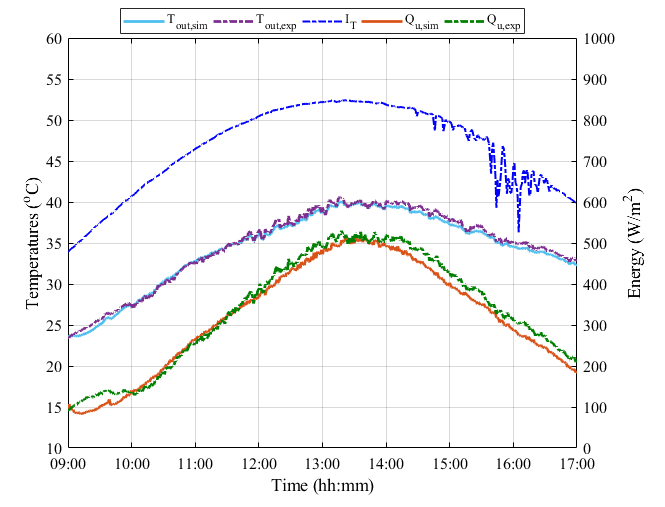
figs/0115-3.png
