fsguerreiro/My_thesis/figs/0115-residue-1.png

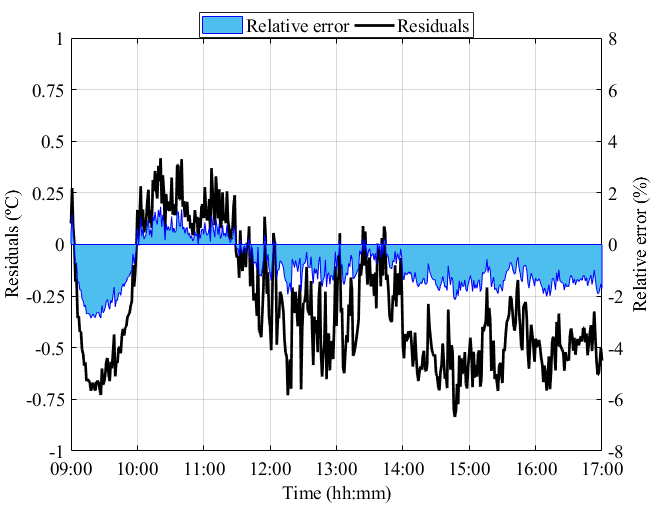
figs/0115-residue-1.png
