fsguerreiro/My_thesis/figs/0115-residue-2.png

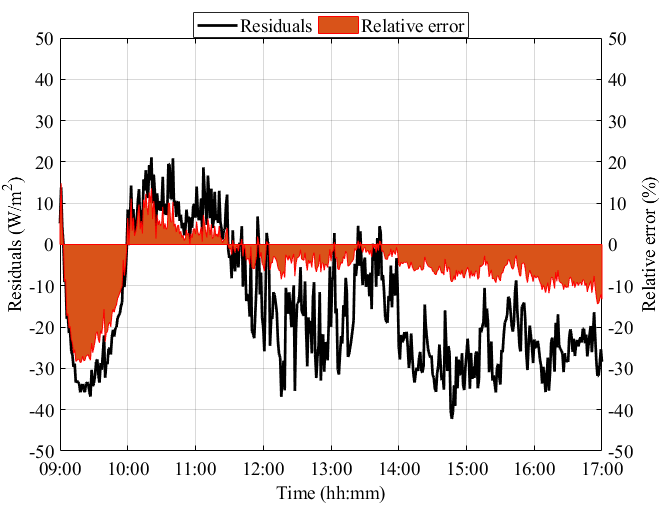
figs/0115-residue-2.png
