fsguerreiro/My_thesis/figs/0115-residue-3.png

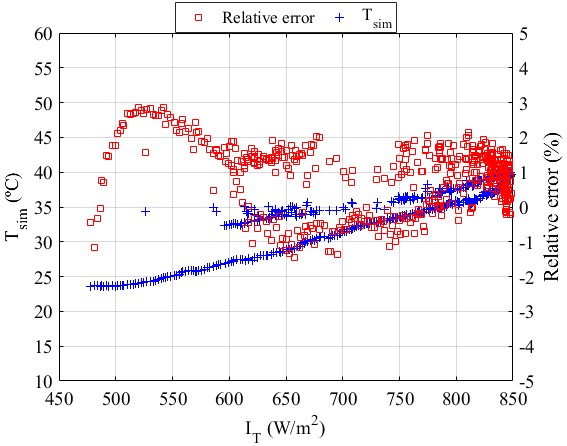
figs/0115-residue-3.png
