fsguerreiro/My_thesis/figs/0115-residue-4.png

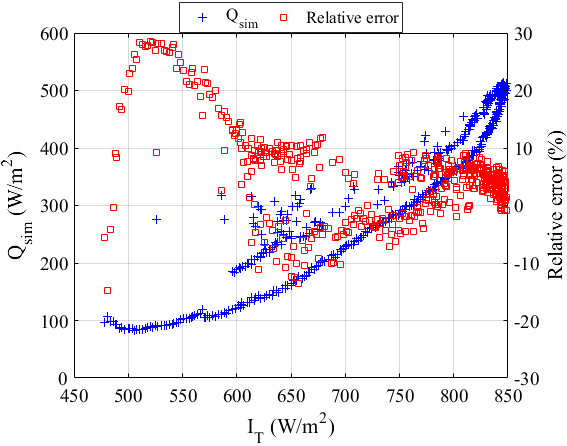
figs/0115-residue-4.png
