fsguerreiro/My_thesis/figs/0115-residue-5.png

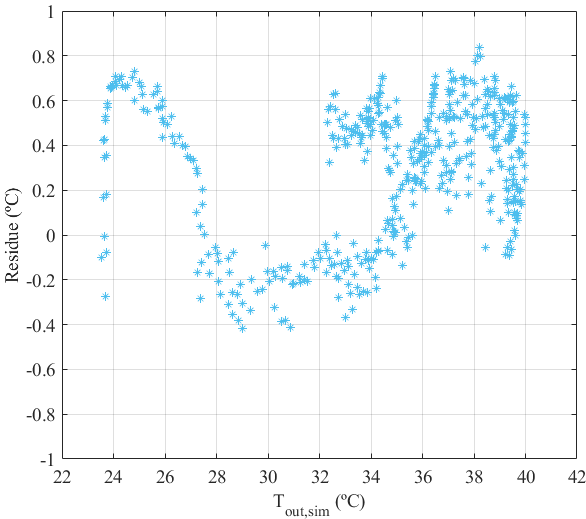
figs/0115-residue-5.png
