fsguerreiro/My_thesis/figs/0115-residue-6.png

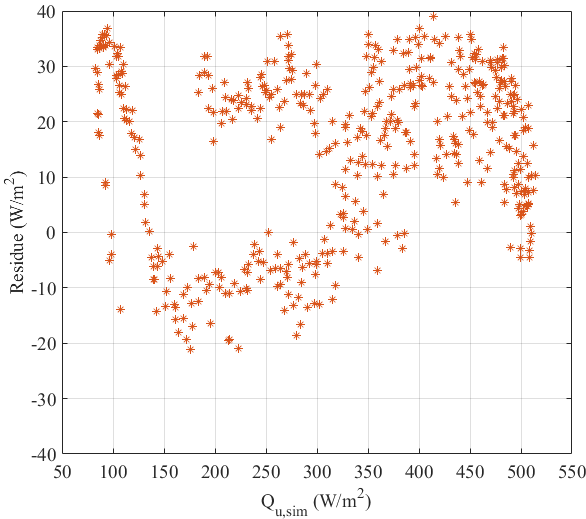
figs/0115-residue-6.png
