fsguerreiro/My_thesis/figs/absorber_thermocouple.PNG

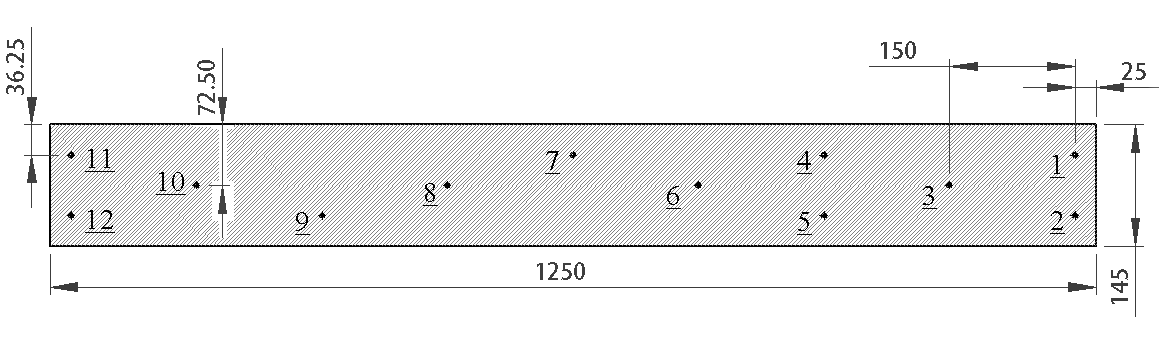
figs/absorber_thermocouple.PNG
