fsguerreiro/My_thesis/figs/acceptance-graph.png

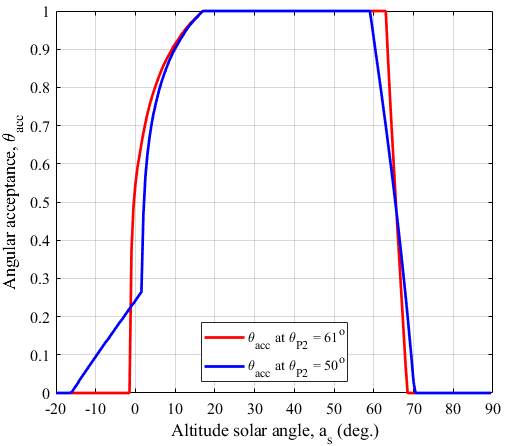
figs/acceptance-graph.png
