fsguerreiro/My_thesis/figs/ACPC.png

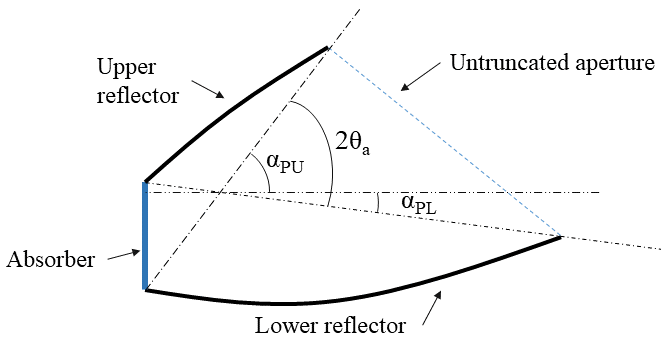
figs/ACPC.png
