fsguerreiro/My_thesis/figs/ACPCzac.PNG

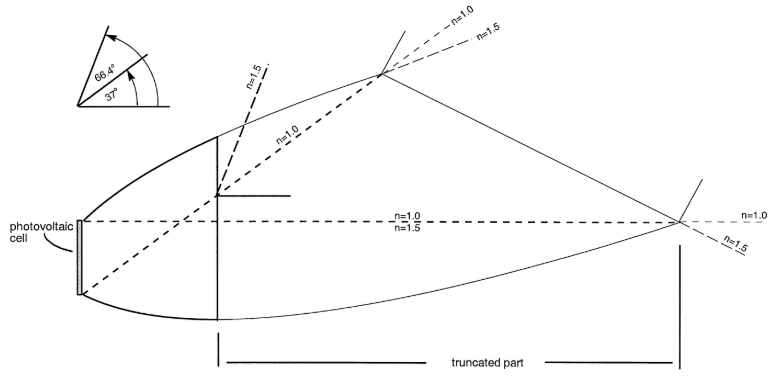
figs/ACPCzac.PNG
