fsguerreiro/My_thesis/figs/airflow_effect.png

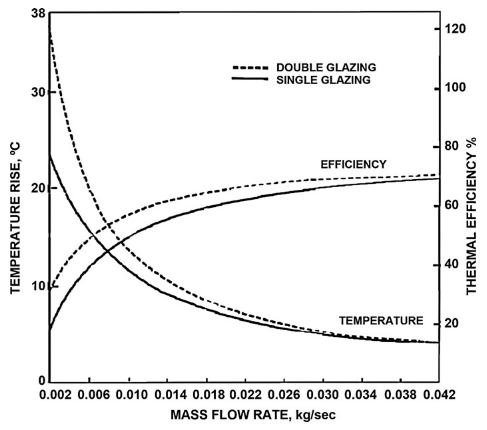
figs/airflow_effect.png
