fsguerreiro/My_thesis/figs/Alt_Azz2.png

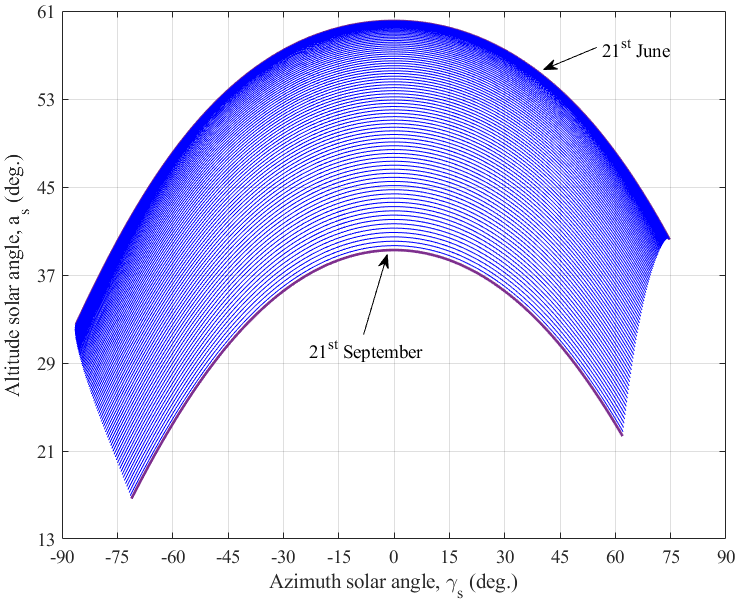
figs/Alt_Azz2.png
