fsguerreiro/My_thesis/figs/ang_acc2.jpg

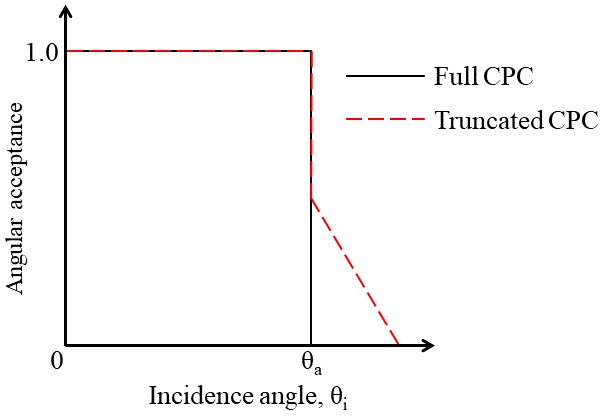
figs/ang_acc2.jpg
