fsguerreiro/My_thesis/figs/ang_acc.png

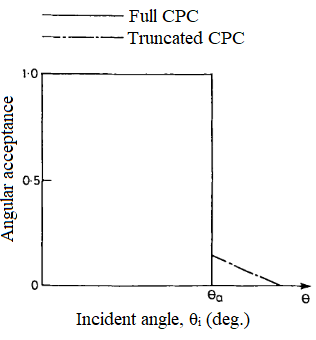
figs/ang_acc.png
