fsguerreiro/My_thesis/figs/array1.png

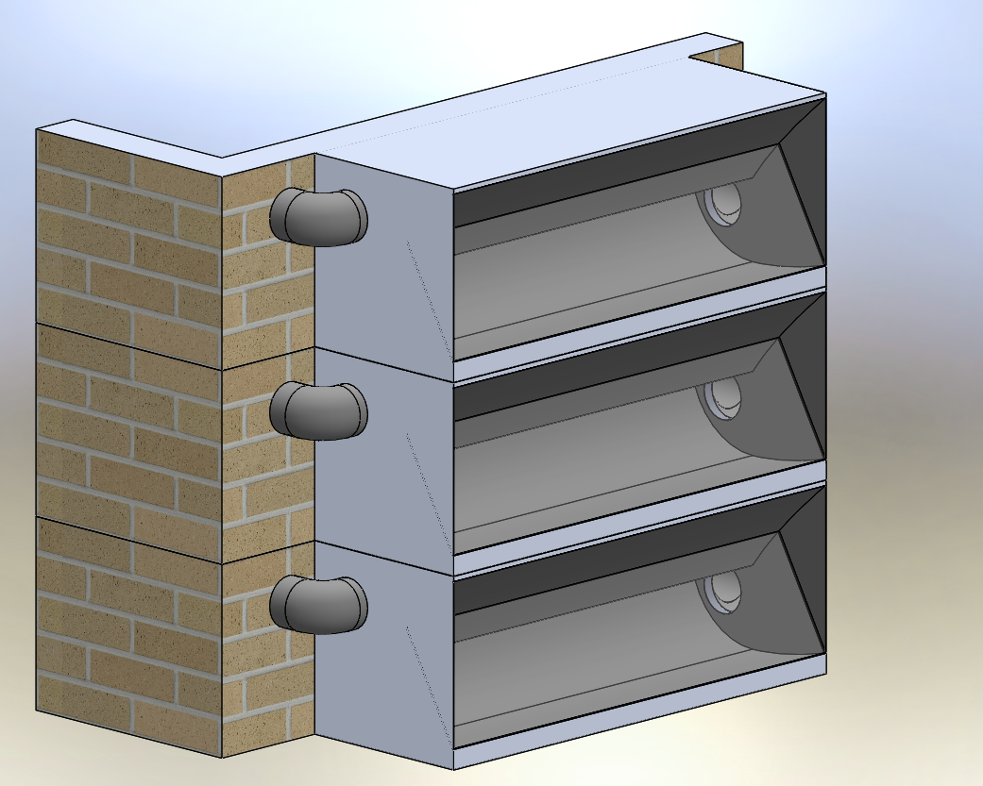
figs/array1.png
