fsguerreiro/My_thesis/figs/auxiliary.png

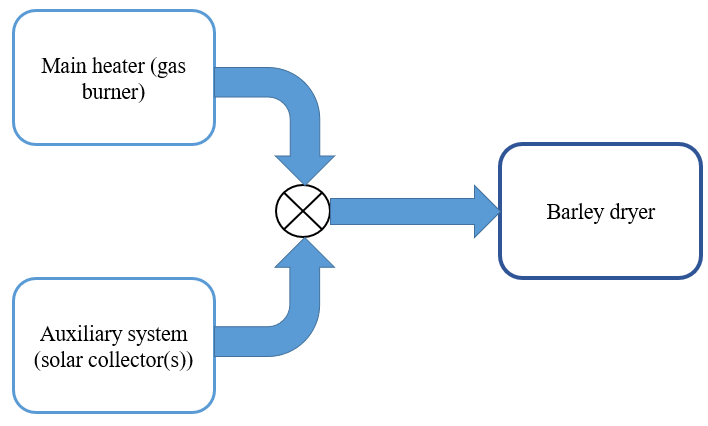
figs/auxiliary.png
