fsguerreiro/My_thesis/figs/block_diagram.png

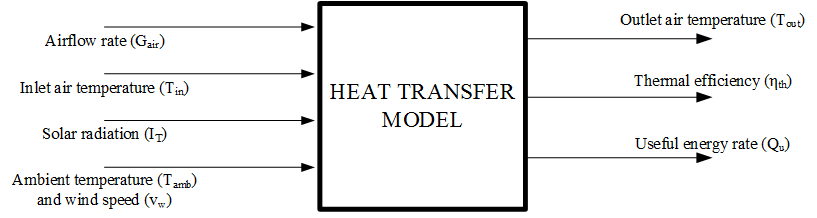
figs/block_diagram.png
