fsguerreiro/My_thesis/figs/carbonfiber2.png

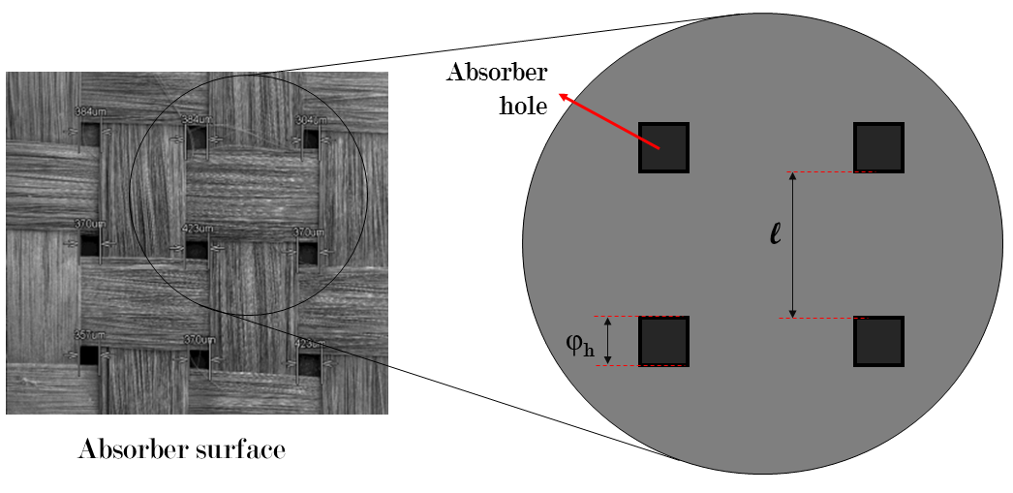
figs/carbonfiber2.png
