fsguerreiro/My_thesis/figs/CCPC.PNG

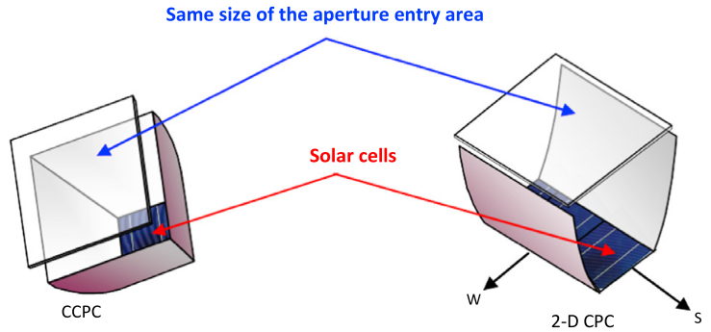
figs/CCPC.PNG
