fsguerreiro/My_thesis/figs/cdf_Q.png

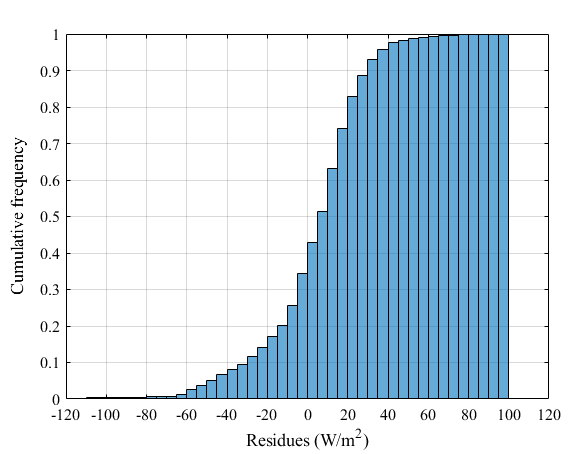
figs/cdf_Q.png
