fsguerreiro/My_thesis/figs/cdf_T.png

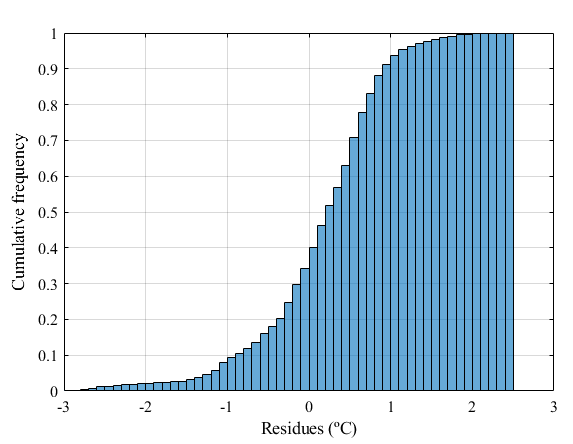
figs/cdf_T.png
