fsguerreiro/My_thesis/figs/CFmag.png

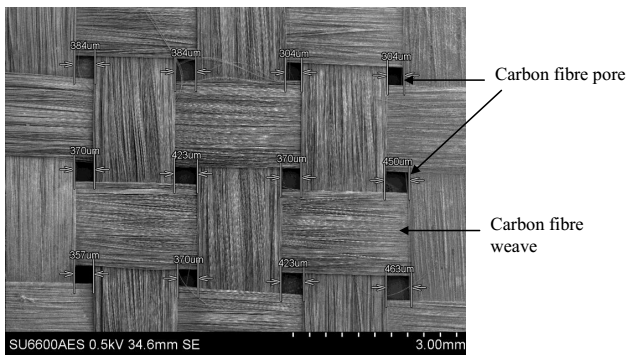
figs/CFmag.png
