fsguerreiro/My_thesis/figs/CFphoto.PNG

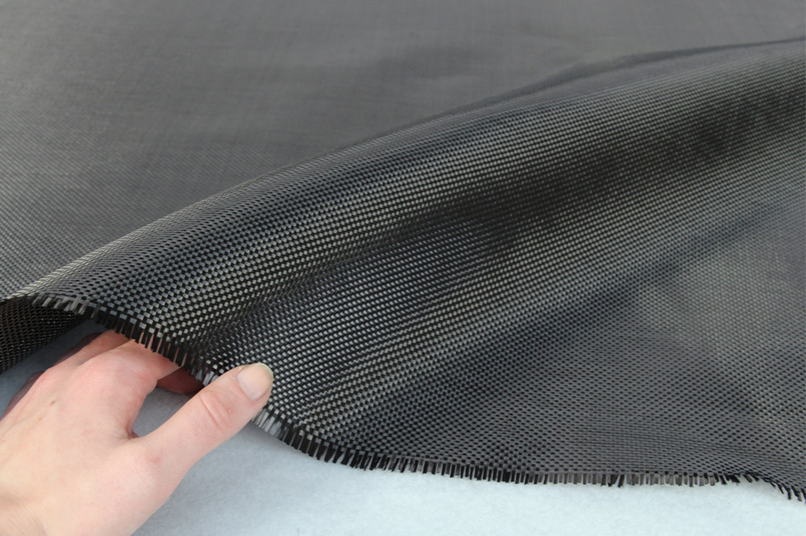
figs/CFphoto.PNG
