fsguerreiro/My_thesis/figs/col_rev.png

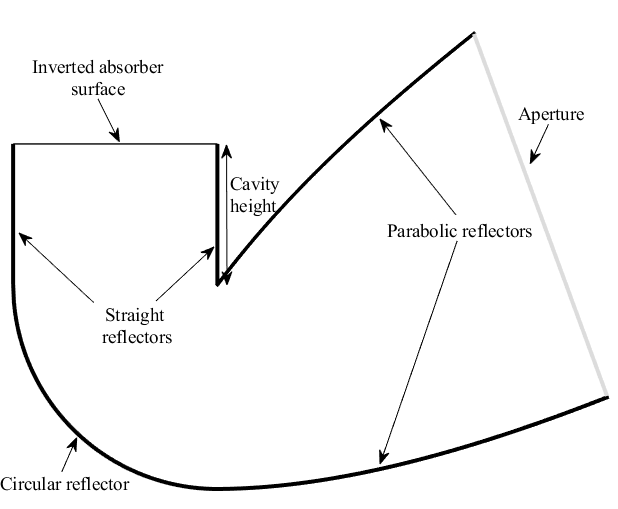
figs/col_rev.png
