fsguerreiro/My_thesis/figs/collector2p.png

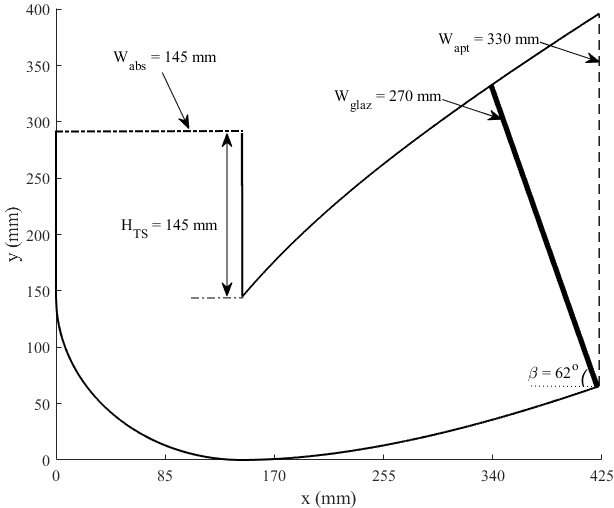
figs/collector2p.png
