fsguerreiro/My_thesis/figs/collector3D-3.PNG

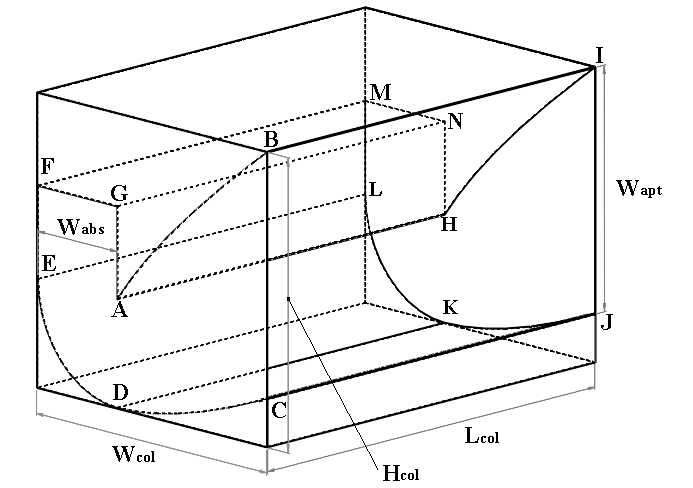
figs/collector3D-3.PNG
