fsguerreiro/My_thesis/figs/collector3D-c.PNG

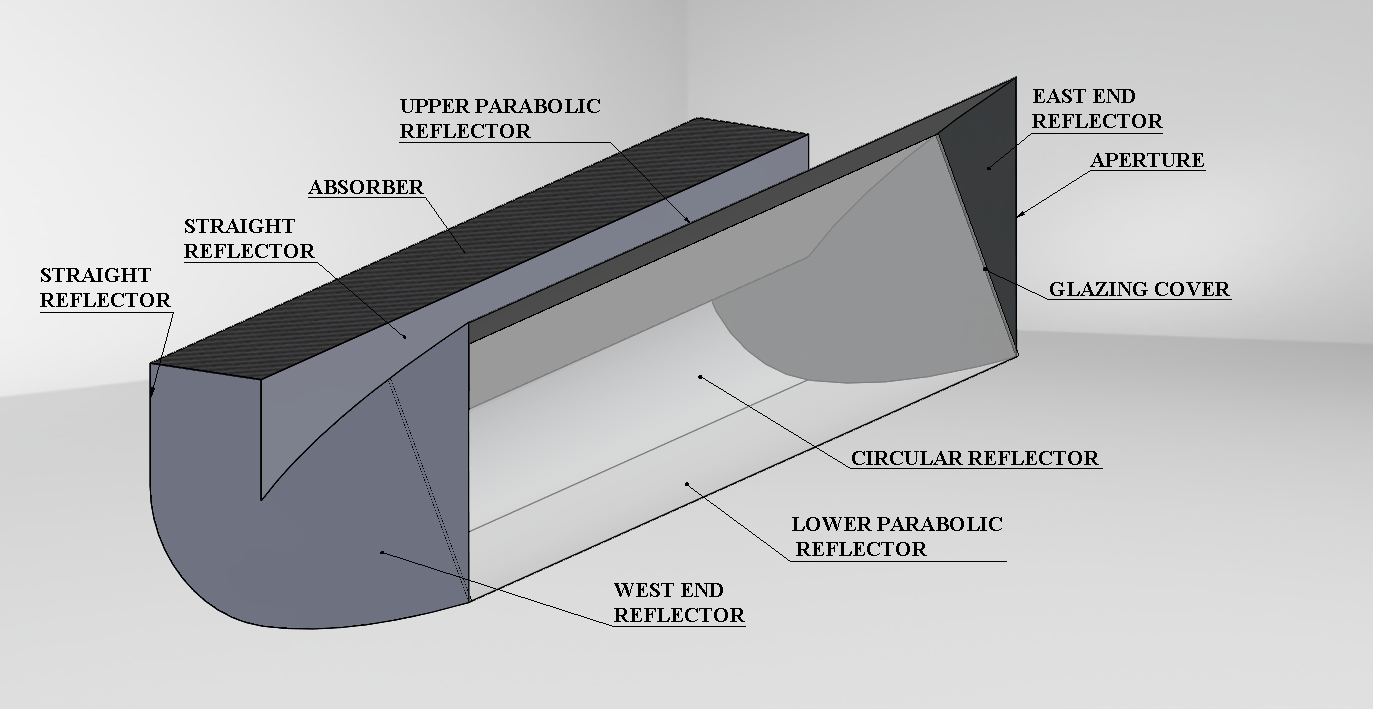
figs/collector3D-c.PNG
