fsguerreiro/My_thesis/figs/collector3D.PNG

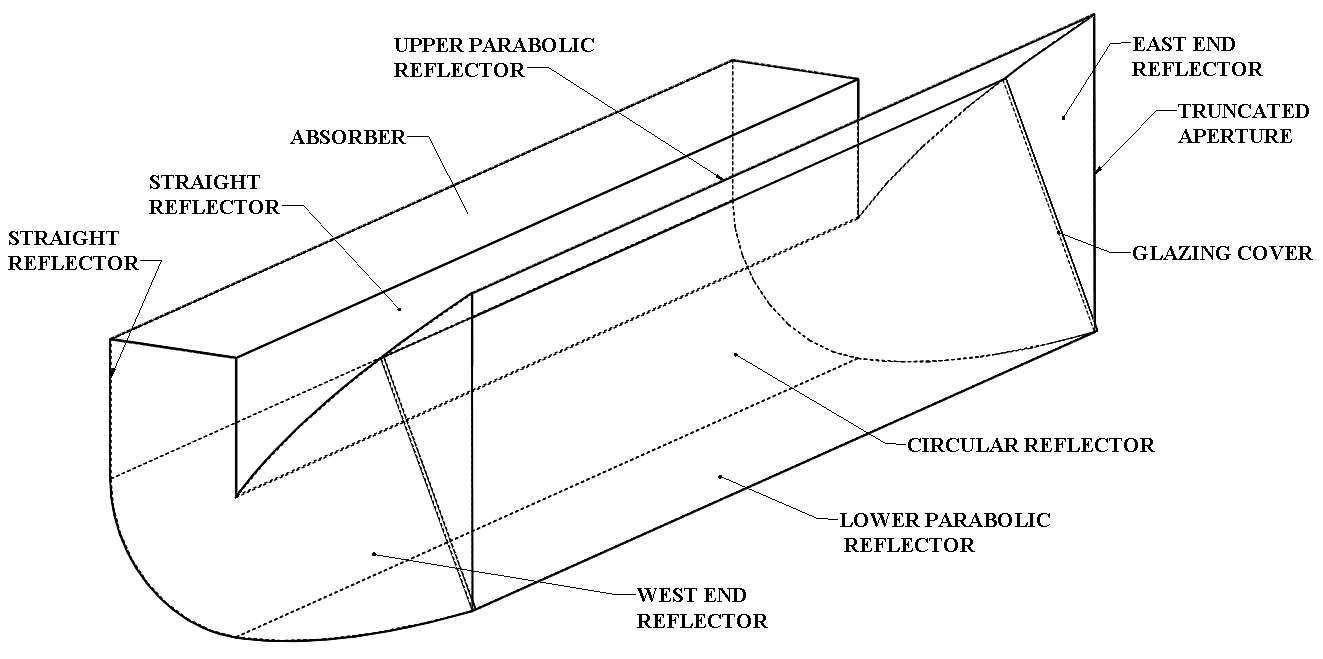
figs/collector3D.PNG
