fsguerreiro/My_thesis/figs/collector3p.jpg

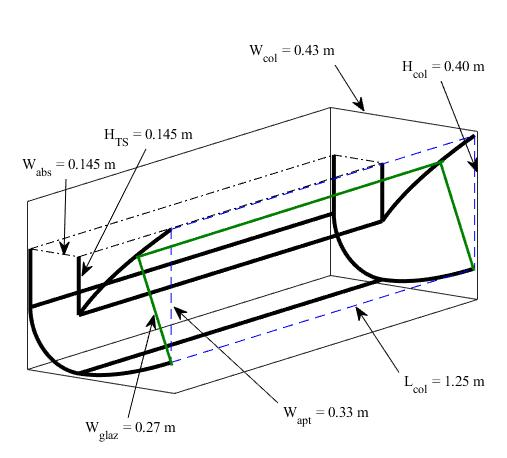
figs/collector3p.jpg
