fsguerreiro/My_thesis/figs/collector_HT.png

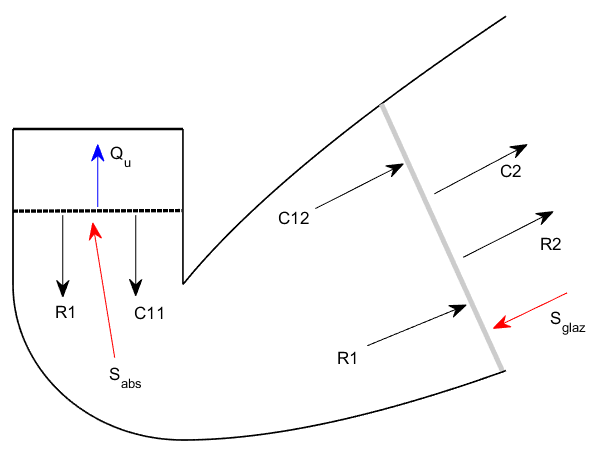
figs/collector_HT.png
