fsguerreiro/My_thesis/figs/collectors-61-50.png

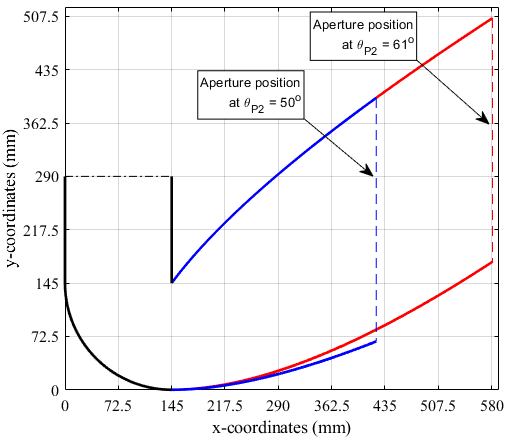
figs/collectors-61-50.png
