fsguerreiro/My_thesis/figs/combo1-23.png

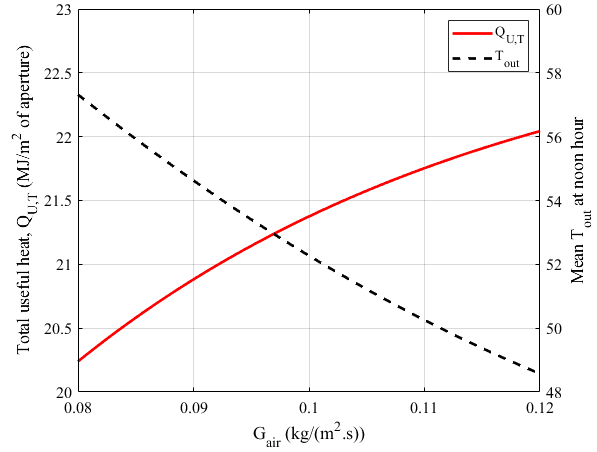
figs/combo1-23.png
