fsguerreiro/My_thesis/figs/combo12-3.png

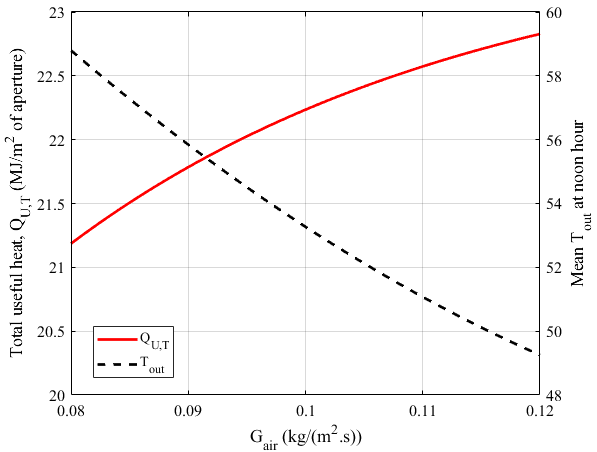
figs/combo12-3.png
