fsguerreiro/My_thesis/figs/contour_dT.png

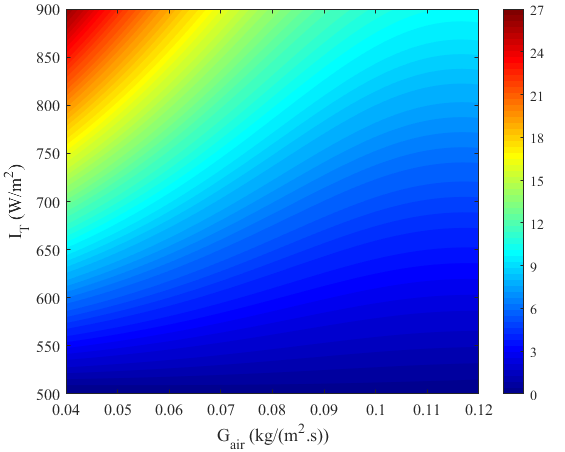
figs/contour_dT.png
