fsguerreiro/My_thesis/figs/contour_Q.png

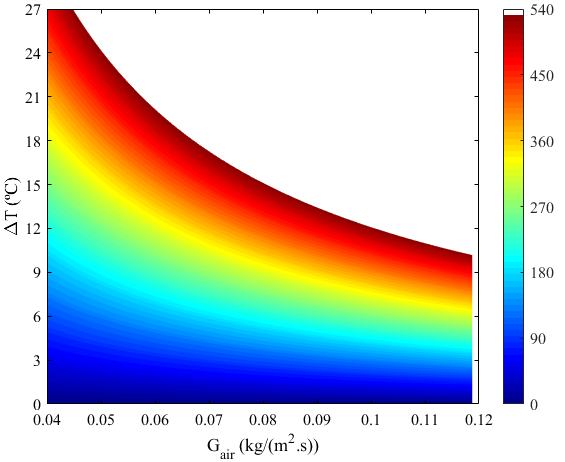
figs/contour_Q.png
