fsguerreiro/My_thesis/figs/cooker.PNG

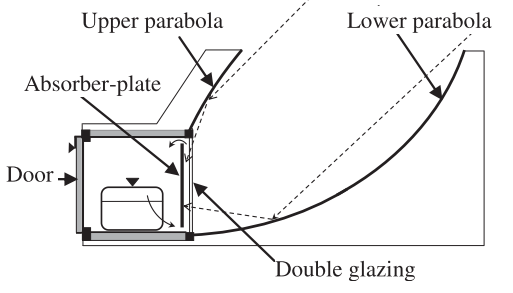
figs/cooker.PNG
