fsguerreiro/My_thesis/figs/CPC1.png

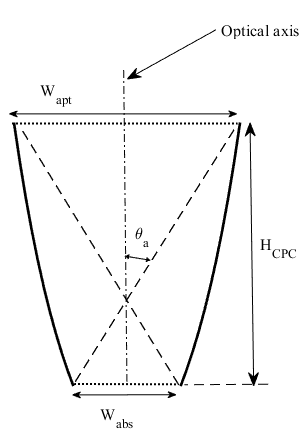
figs/CPC1.png
