fsguerreiro/My_thesis/figs/CPC3.png

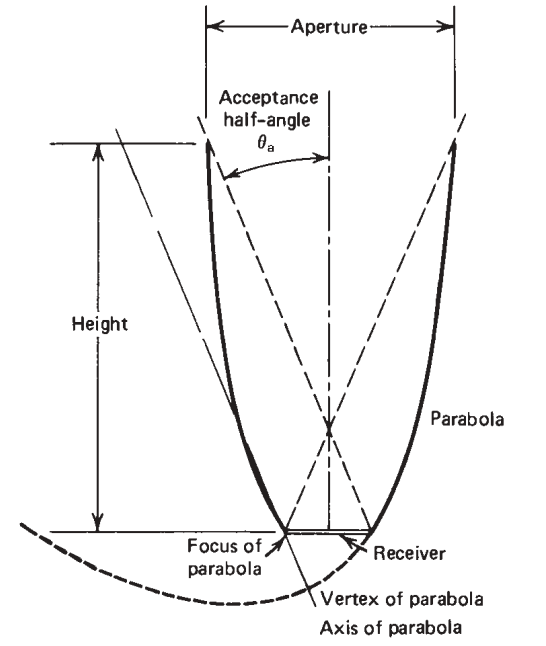
figs/CPC3.png
