fsguerreiro/My_thesis/figs/CPC-2D-3D.png

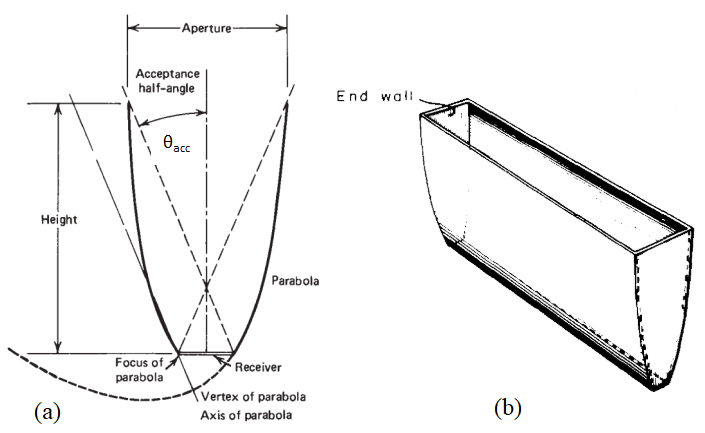
figs/CPC-2D-3D.png
