fsguerreiro/My_thesis/figs/CPCbasic.png

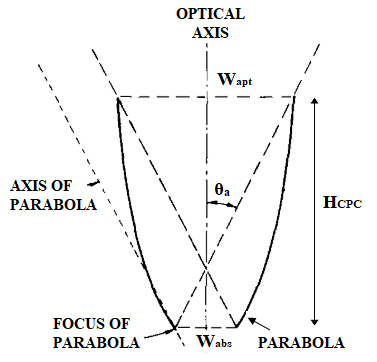
figs/CPCbasic.png
