fsguerreiro/My_thesis/figs/CSview2.png

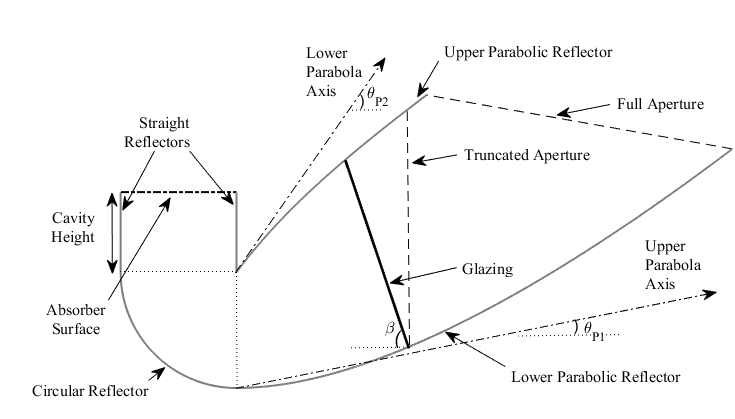
figs/CSview2.png
