fsguerreiro/My_thesis/figs/curve_efficiency1.png

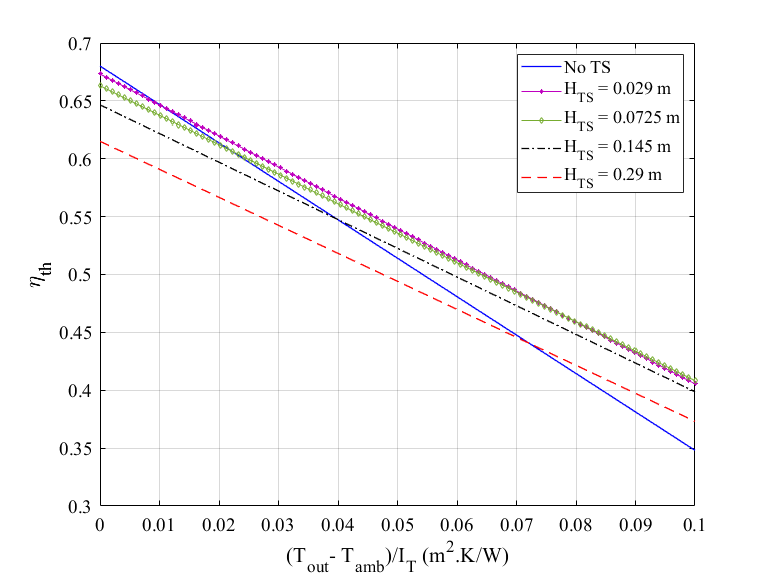
figs/curve_efficiency1.png
