fsguerreiro/My_thesis/figs/D-Combo1-23.png

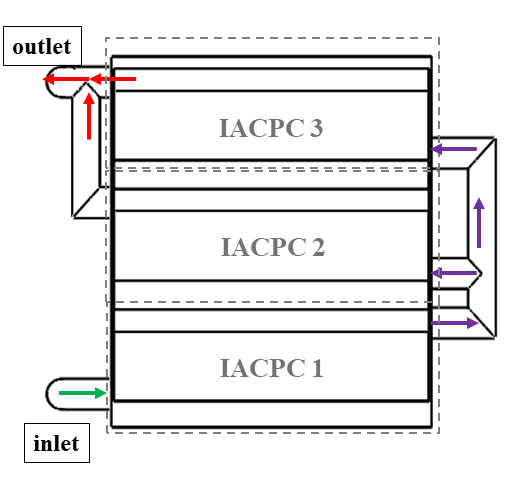
figs/D-Combo1-23.png
