fsguerreiro/My_thesis/figs/D-Combo12-3.png

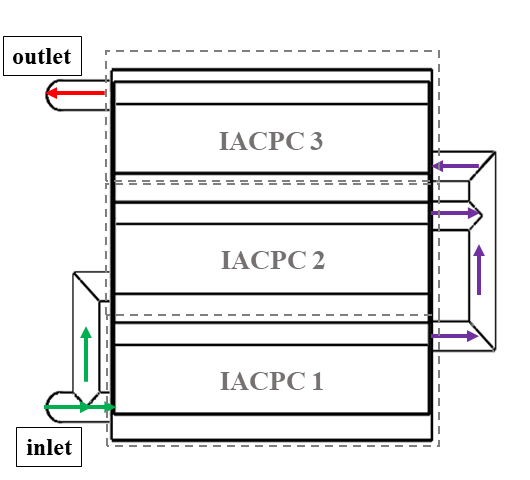
figs/D-Combo12-3.png
