fsguerreiro/My_thesis/figs/D-Parallel.png

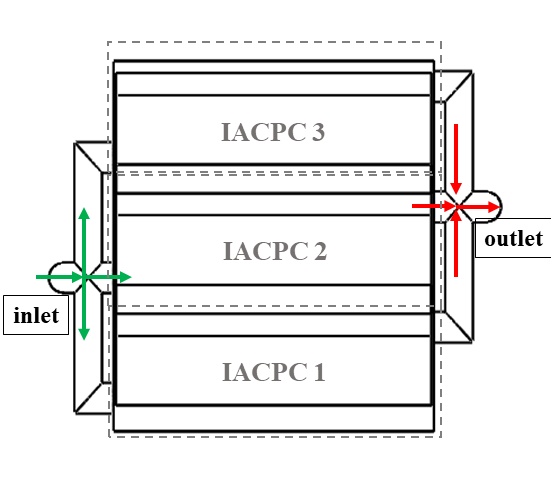
figs/D-Parallel.png
