fsguerreiro/My_thesis/figs/double_pass.png

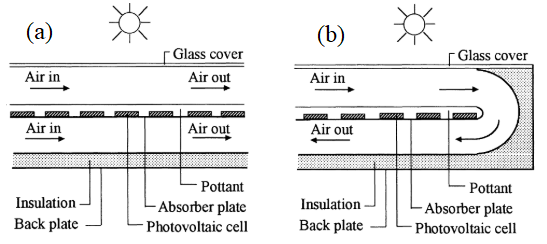
figs/double_pass.png
