fsguerreiro/My_thesis/figs/dP-Gair.png

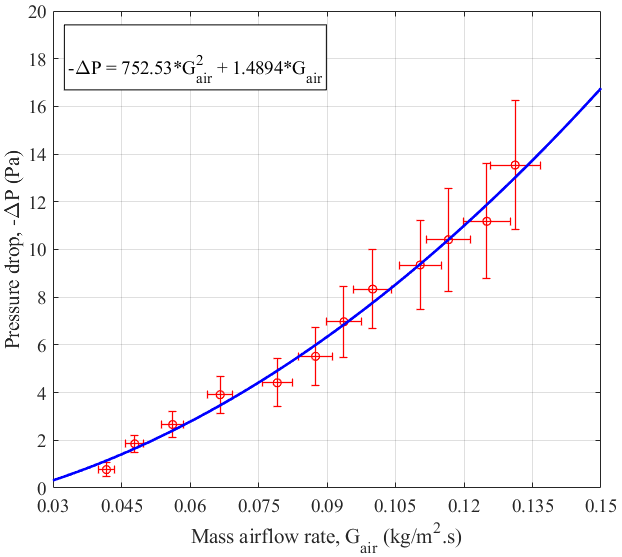
figs/dP-Gair.png
