fsguerreiro/My_thesis/figs/Drawing-Series.png

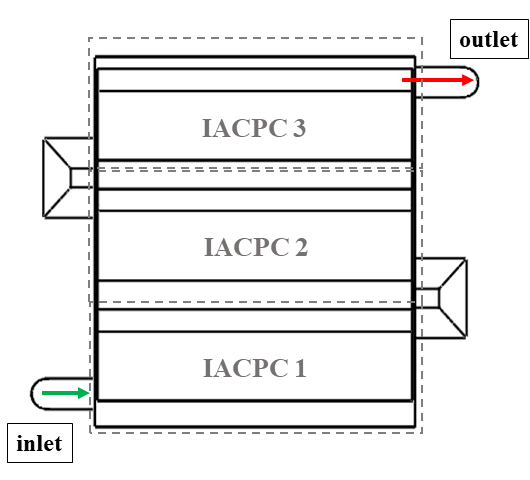
figs/Drawing-Series.png
