fsguerreiro/My_thesis/figs/drawing_connection_series.PNG

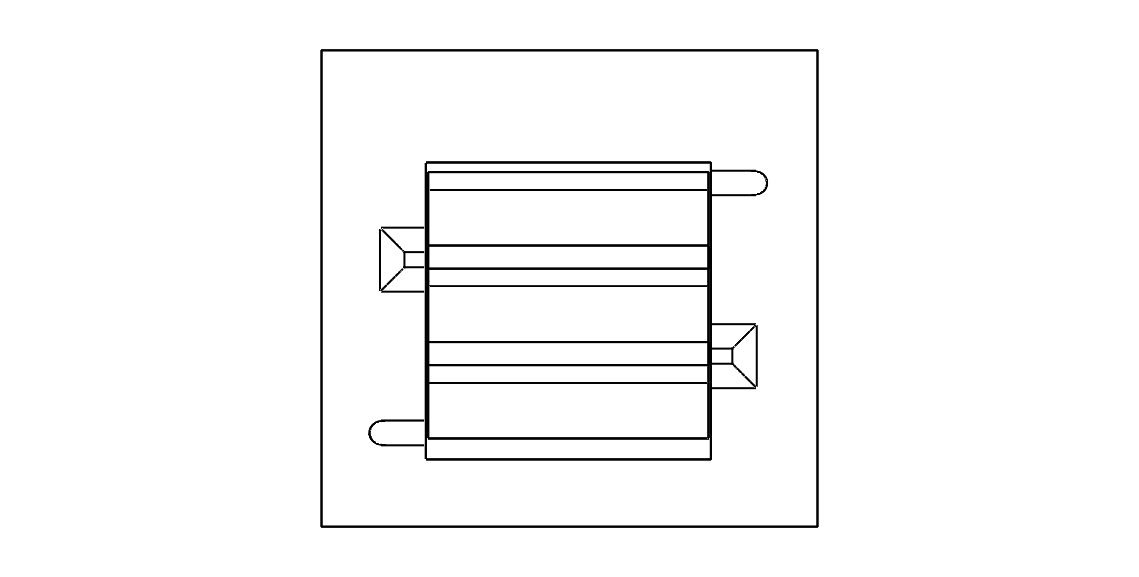
figs/drawing_connection_series.PNG
