fsguerreiro/My_thesis/figs/dry_high_1col.png

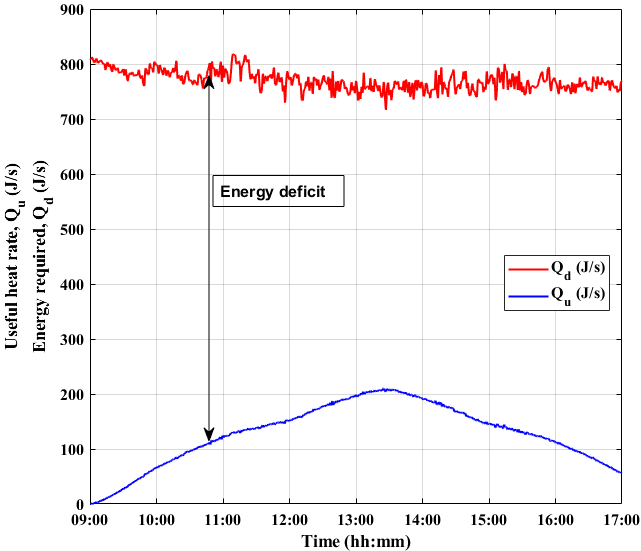
figs/dry_high_1col.png
