fsguerreiro/My_thesis/figs/dry_high_2col.png

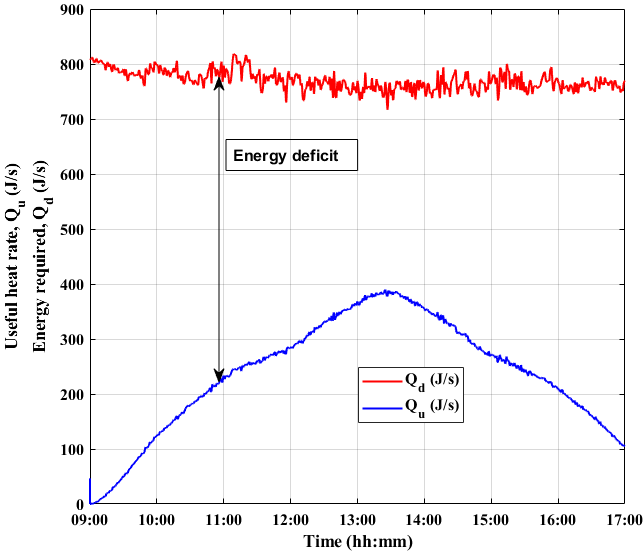
figs/dry_high_2col.png
