fsguerreiro/My_thesis/figs/dry_high_3col.png

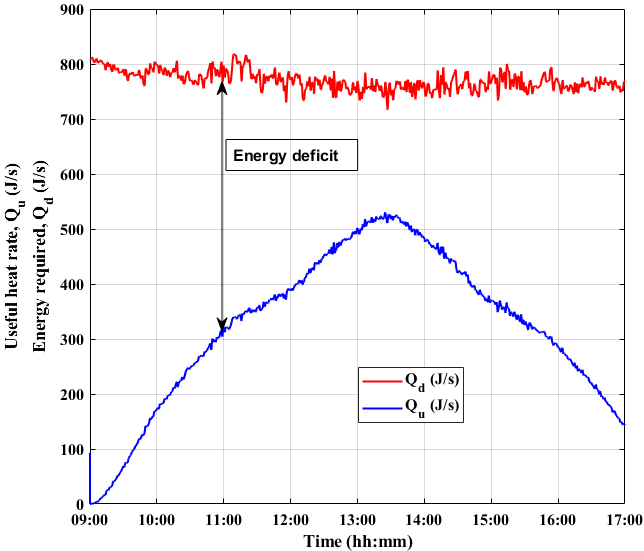
figs/dry_high_3col.png
