fsguerreiro/My_thesis/figs/dry_low_1col.png

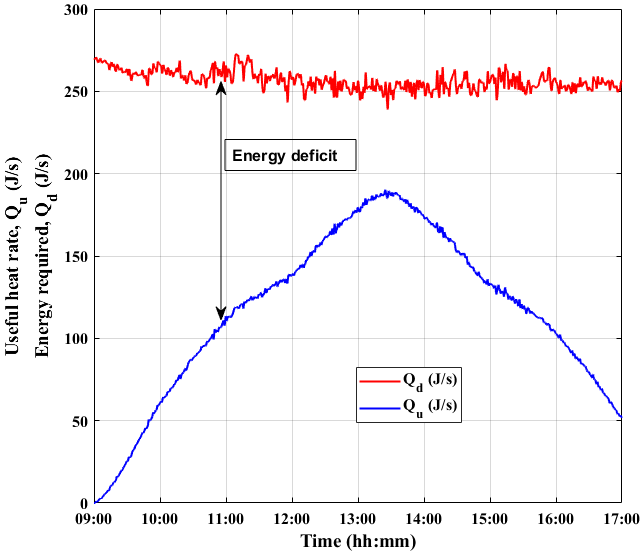
figs/dry_low_1col.png
