fsguerreiro/My_thesis/figs/dry_low_2col.png

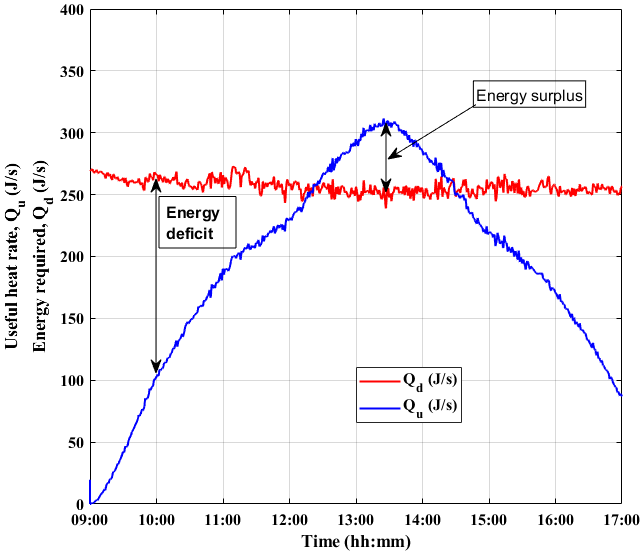
figs/dry_low_2col.png
