fsguerreiro/My_thesis/figs/dry_low_3col.png

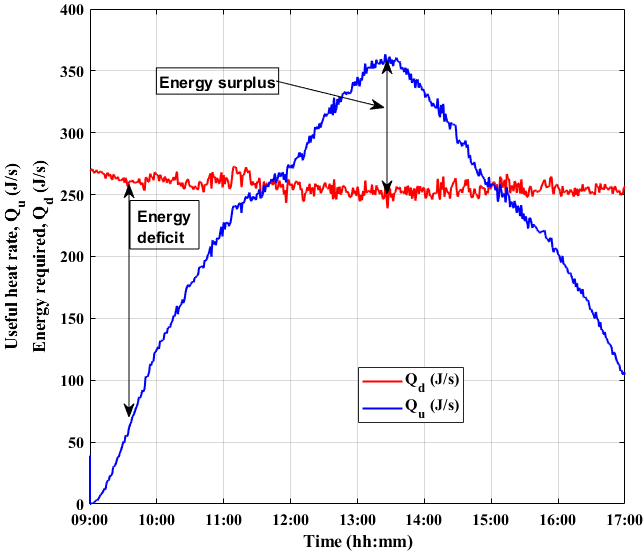
figs/dry_low_3col.png
