fsguerreiro/My_thesis/figs/dT-Gair2.png

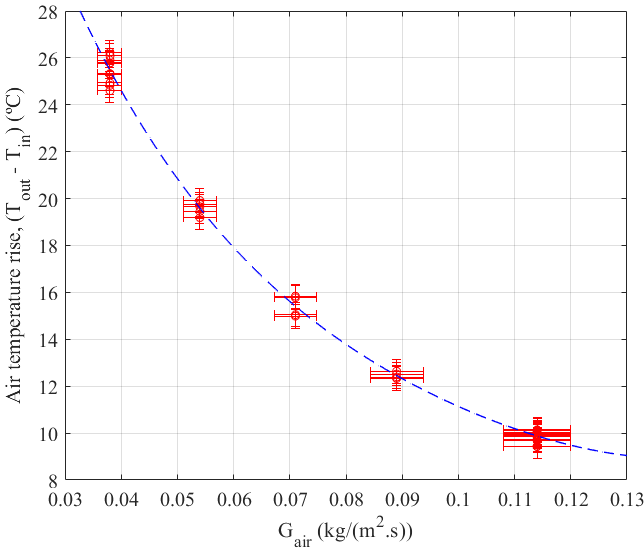
figs/dT-Gair2.png
