fsguerreiro/My_thesis/figs/ef-Gair2.png

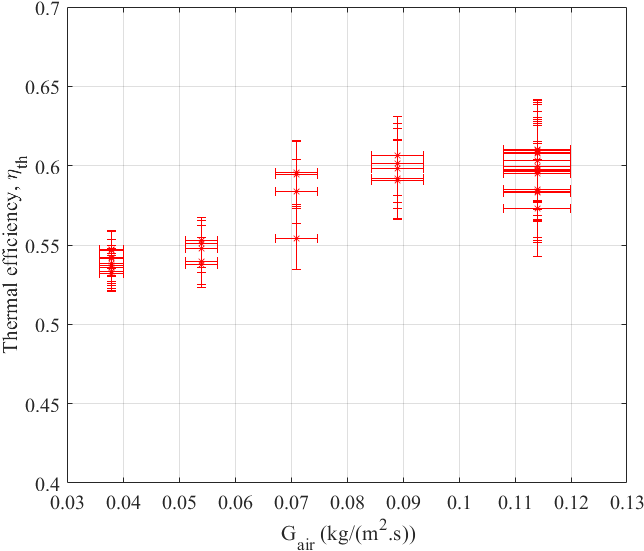
figs/ef-Gair2.png
