fsguerreiro/My_thesis/figs/ef_curve2.png

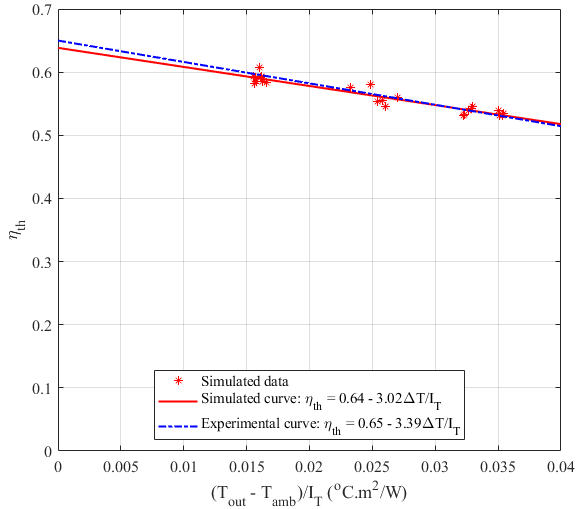
figs/ef_curve2.png
