fsguerreiro/My_thesis/figs/ef_curve.png

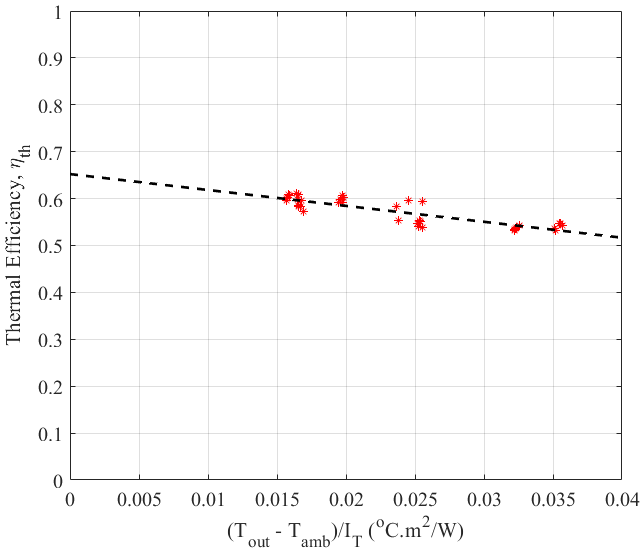
figs/ef_curve.png
