fsguerreiro/My_thesis/figs/eff-alphaP2.png

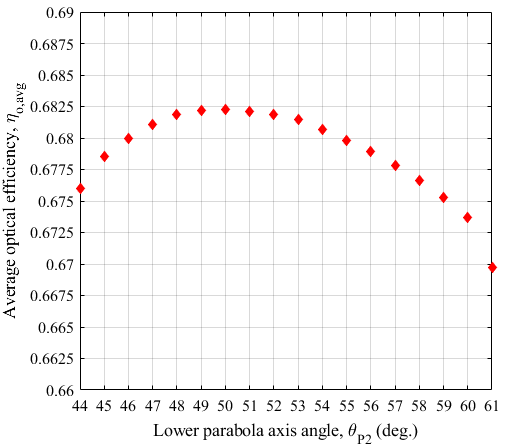
figs/eff-alphaP2.png
