fsguerreiro/My_thesis/figs/eff-length.jpg

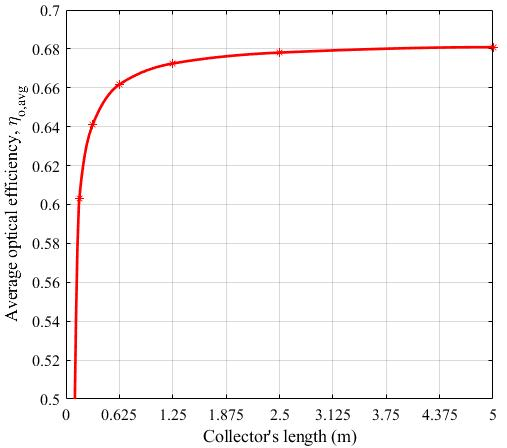
figs/eff-length.jpg
