fsguerreiro/My_thesis/figs/eff-time-L.png

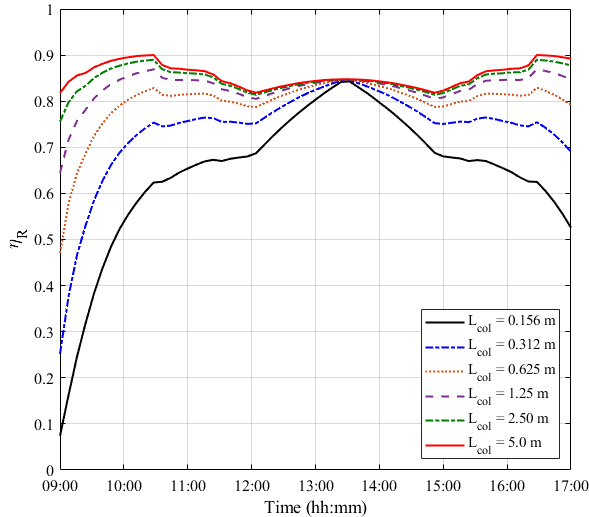
figs/eff-time-L.png
