fsguerreiro/My_thesis/figs/eff-time-paxis.png

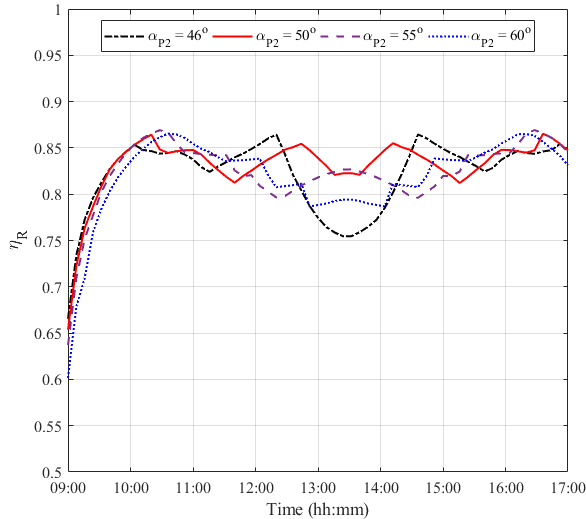
figs/eff-time-paxis.png
