fsguerreiro/My_thesis/figs/eff_curve_series.png

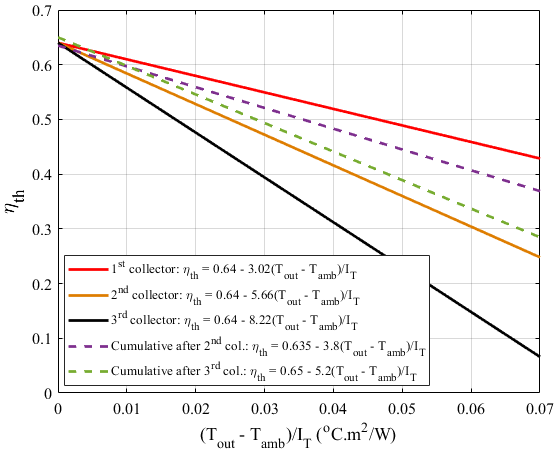
figs/eff_curve_series.png
