fsguerreiro/My_thesis/figs/eff_L.png

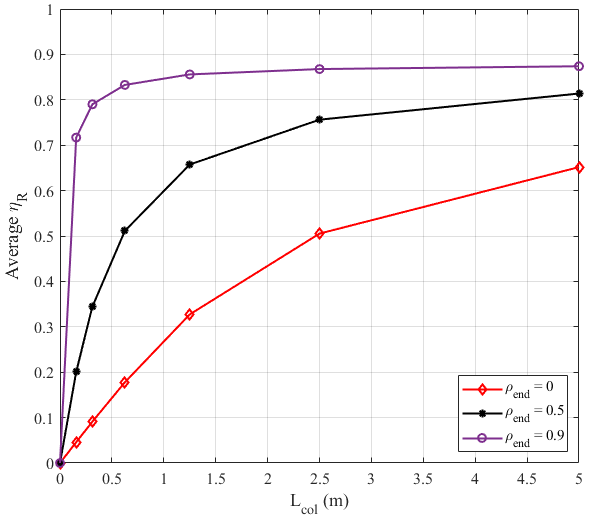
figs/eff_L.png
