fsguerreiro/My_thesis/figs/eff_length.png

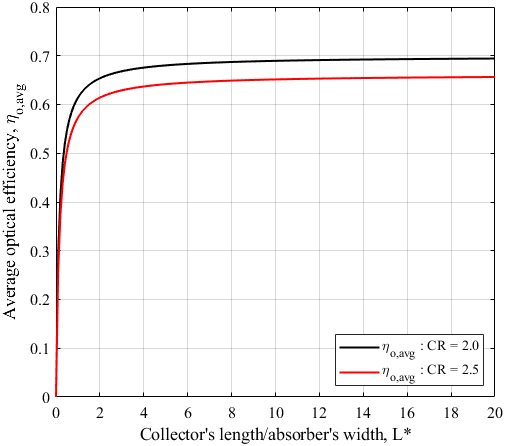
figs/eff_length.png
