fsguerreiro/My_thesis/figs/eff_Paxis_tilt.png

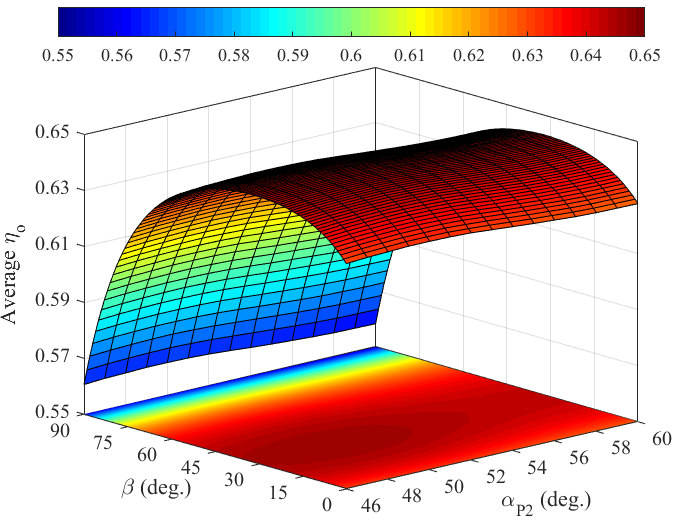
figs/eff_Paxis_tilt.png
