fsguerreiro/My_thesis/figs/eff_time_ref.png

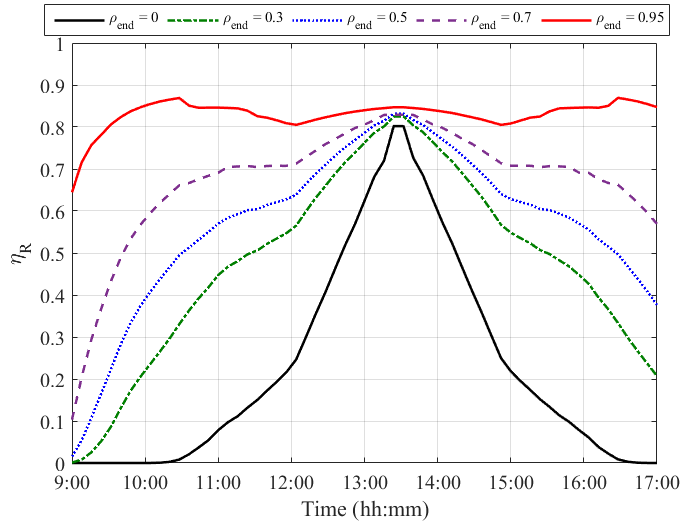
figs/eff_time_ref.png
