fsguerreiro/My_thesis/figs/Energy2D-hts0.png

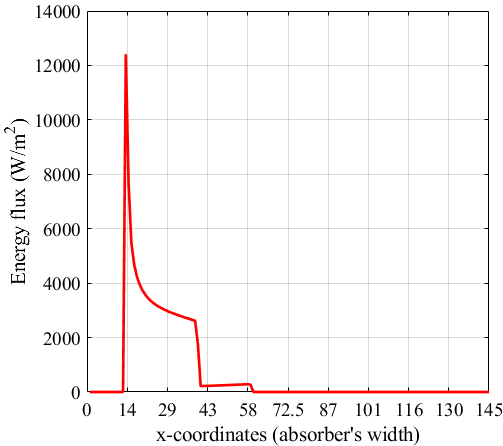
figs/Energy2D-hts0.png
