fsguerreiro/My_thesis/figs/Energy2D-hts72.png

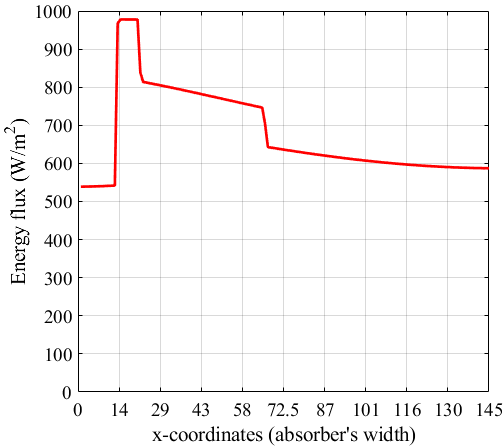
figs/Energy2D-hts72.png
