fsguerreiro/My_thesis/figs/Energy2D-hts145.png

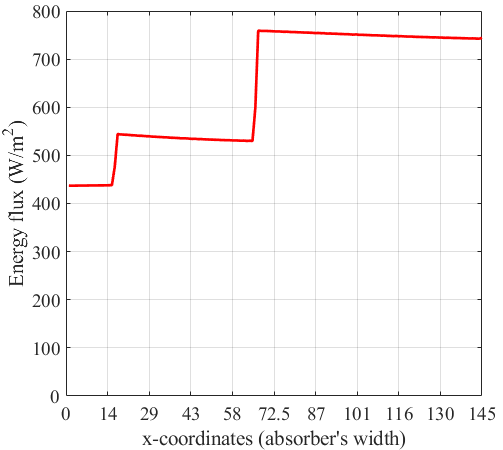
figs/Energy2D-hts145.png
