fsguerreiro/My_thesis/figs/energy-54-49-hts145.png

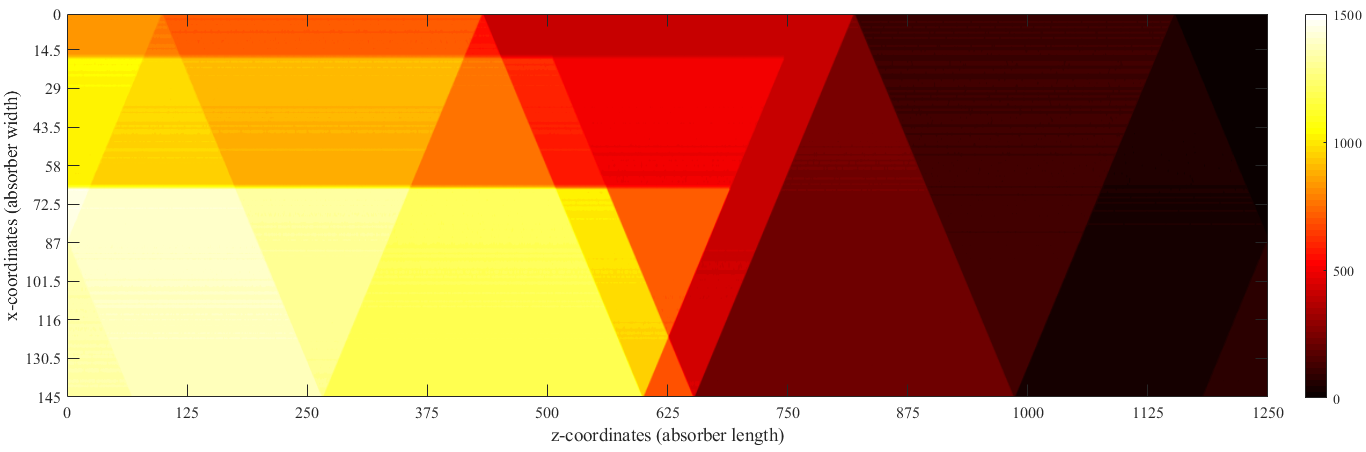
figs/energy-54-49-hts145.png
