fsguerreiro/My_thesis/figs/exp_curve.png

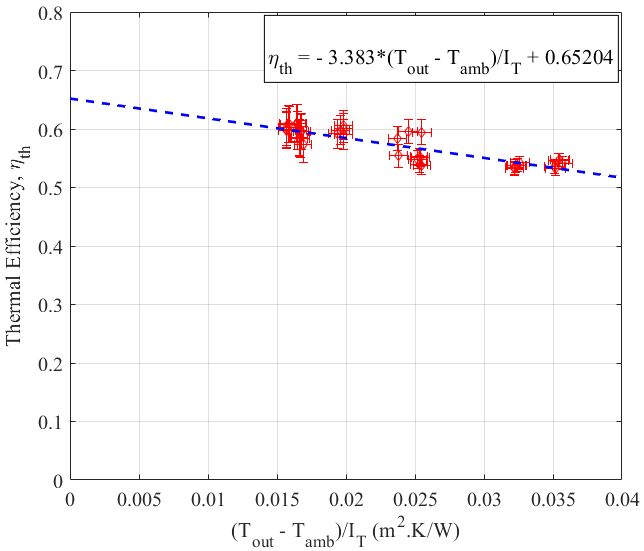
figs/exp_curve.png
