fsguerreiro/My_thesis/figs/fig_primary3.PNG

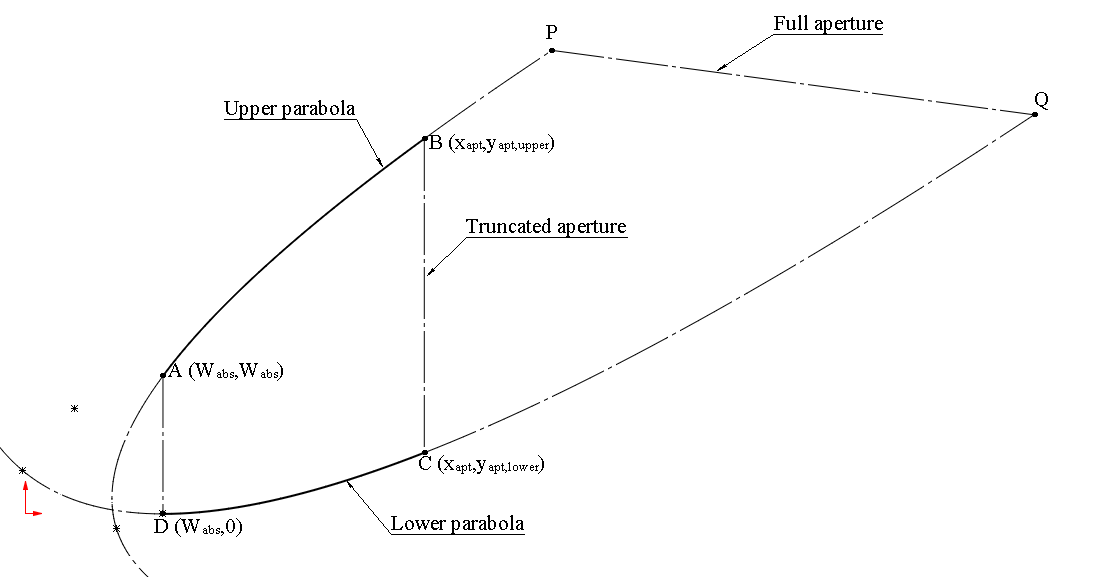
figs/fig_primary3.PNG
