fsguerreiro/My_thesis/figs/figTS.png

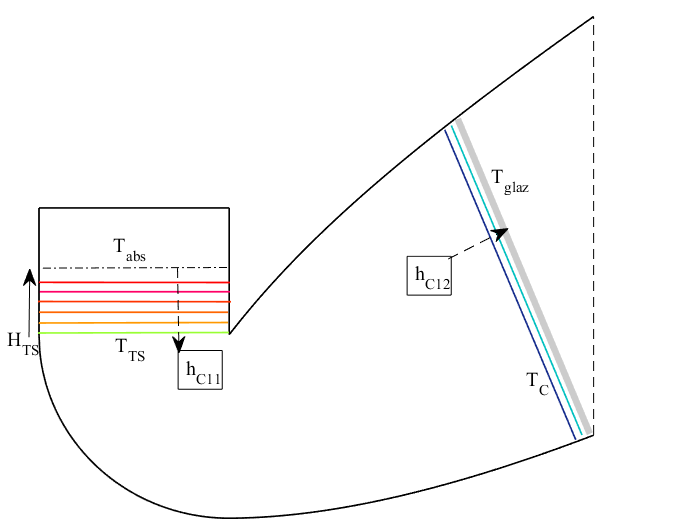
figs/figTS.png
