fsguerreiro/My_thesis/figs/Figure_orientation.png

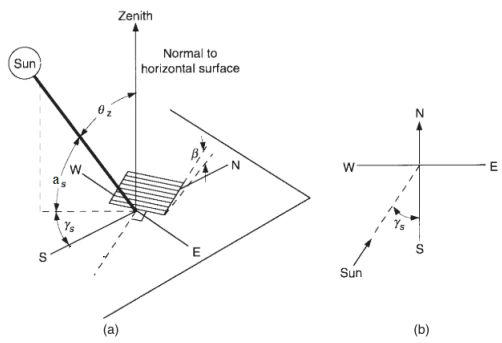
figs/Figure_orientation.png
