fsguerreiro/My_thesis/figs/Gair_V.png

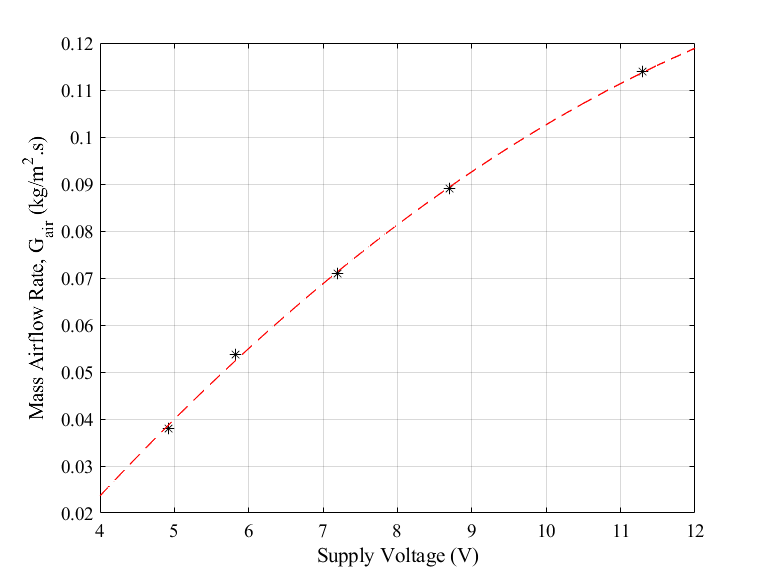
figs/Gair_V.png
