fsguerreiro/My_thesis/figs/glass_thermocouple.PNG

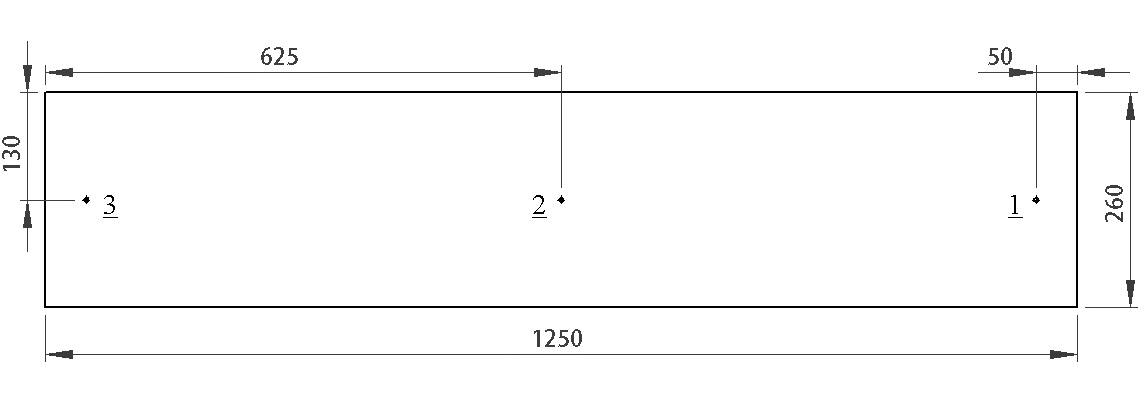
figs/glass_thermocouple.PNG
