fsguerreiro/My_thesis/figs/glazed.png

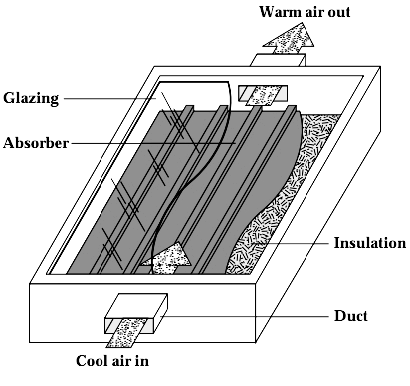
figs/glazed.png
