fsguerreiro/My_thesis/figs/hyperboloid2.PNG

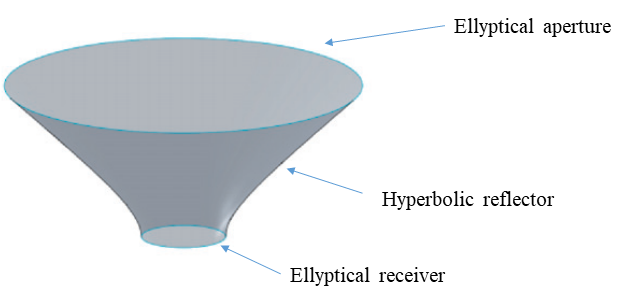
figs/hyperboloid2.PNG
