fsguerreiro/My_thesis/figs/ICS.PNG

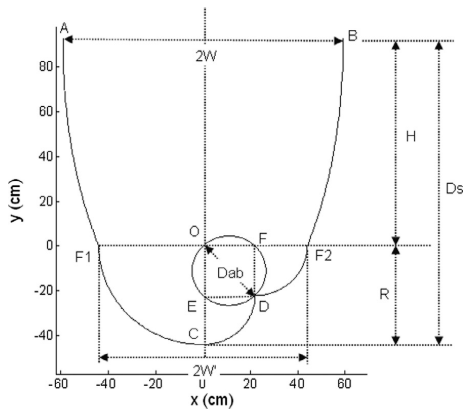
figs/ICS.PNG
