fsguerreiro/My_thesis/figs/length.png

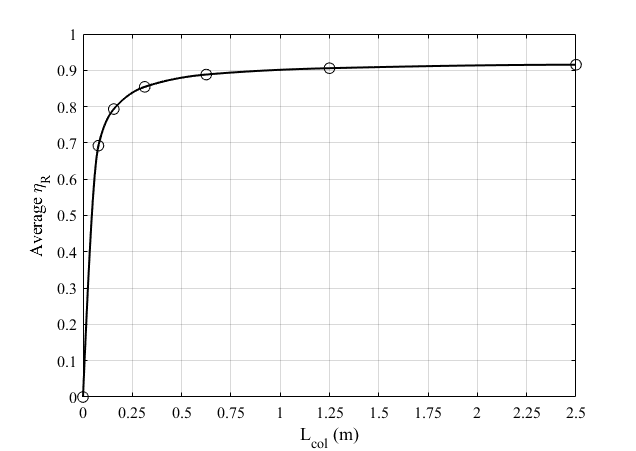
figs/length.png
