fsguerreiro/My_thesis/figs/modified_area.png

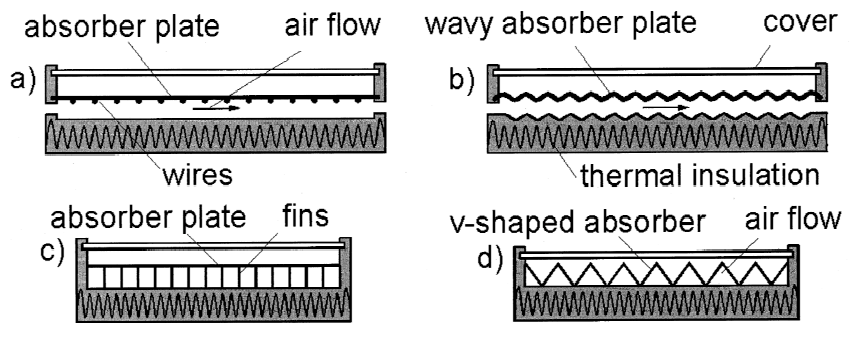
figs/modified_area.png
