fsguerreiro/My_thesis/figs/opt-avg-hts.png

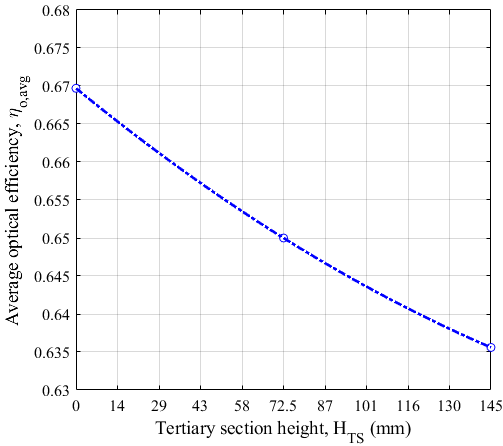
figs/opt-avg-hts.png
