fsguerreiro/My_thesis/figs/opt-eff-3hts.png

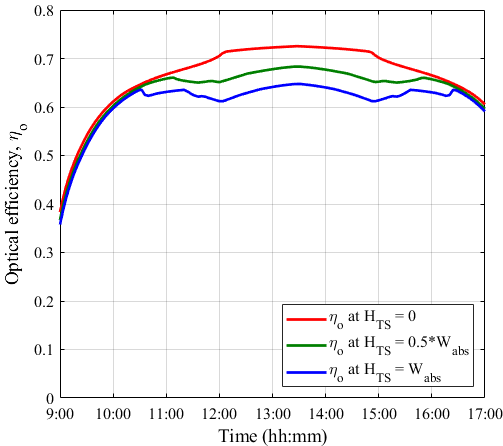
figs/opt-eff-3hts.png
