fsguerreiro/My_thesis/figs/optical_fluxogram.png

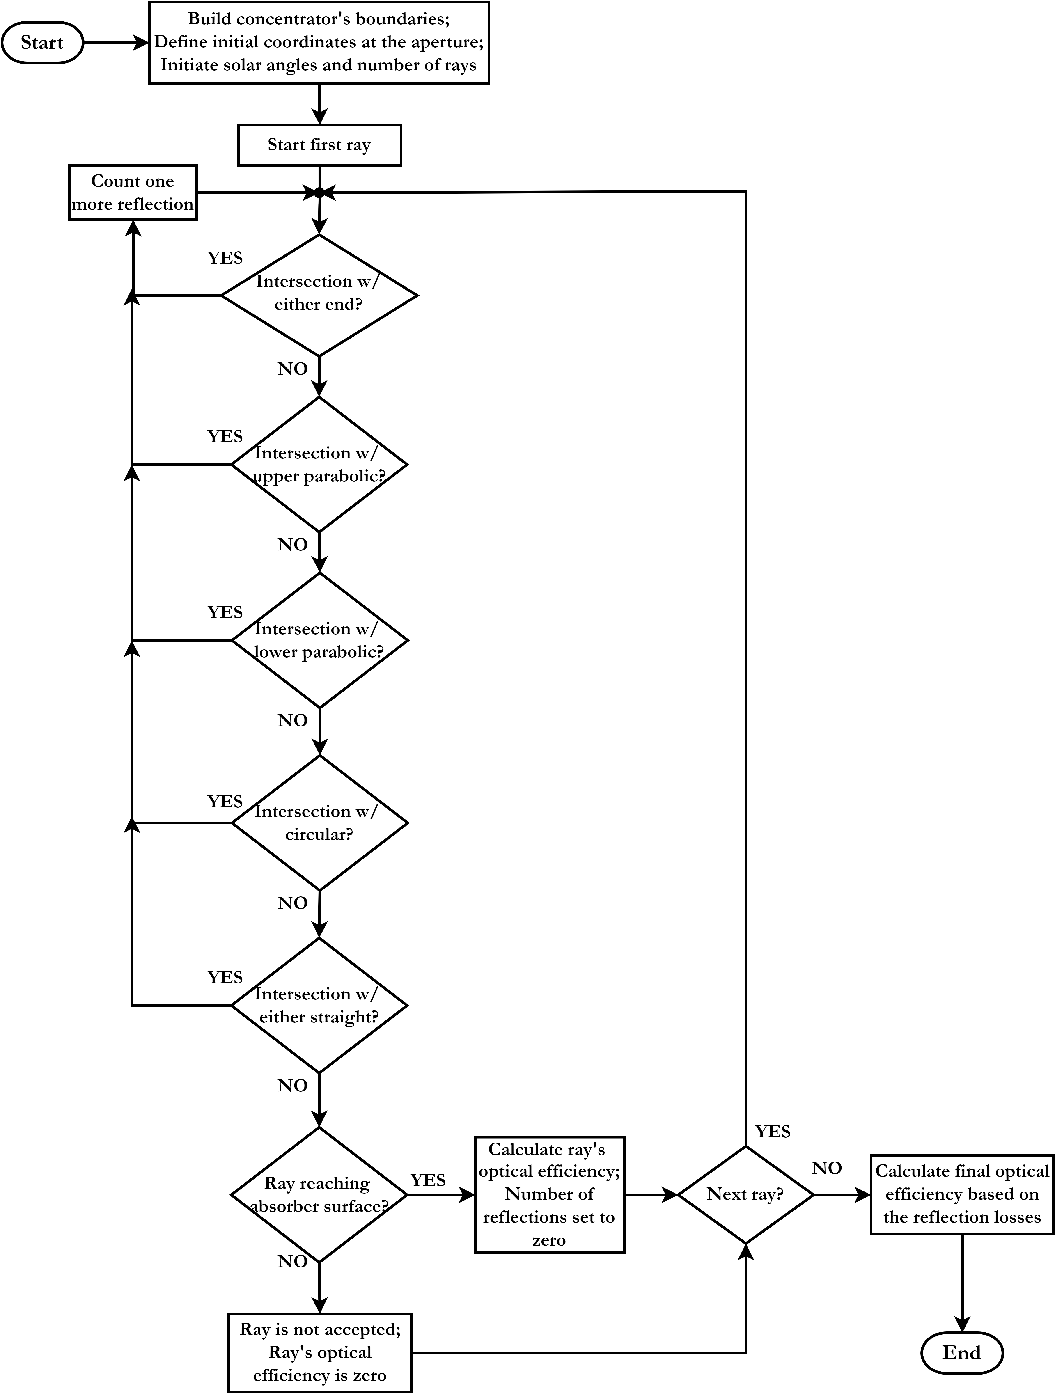
figs/optical_fluxogram.png
