fsguerreiro/My_thesis/figs/orientation3D.png

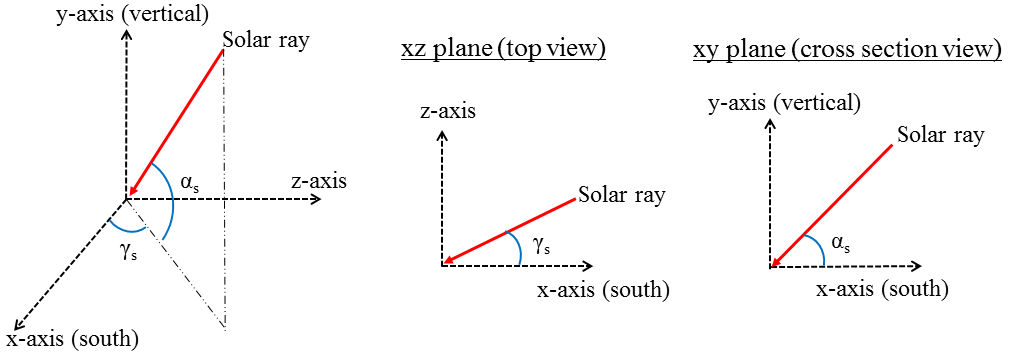
figs/orientation3D.png
