fsguerreiro/My_thesis/figs/P_V.png

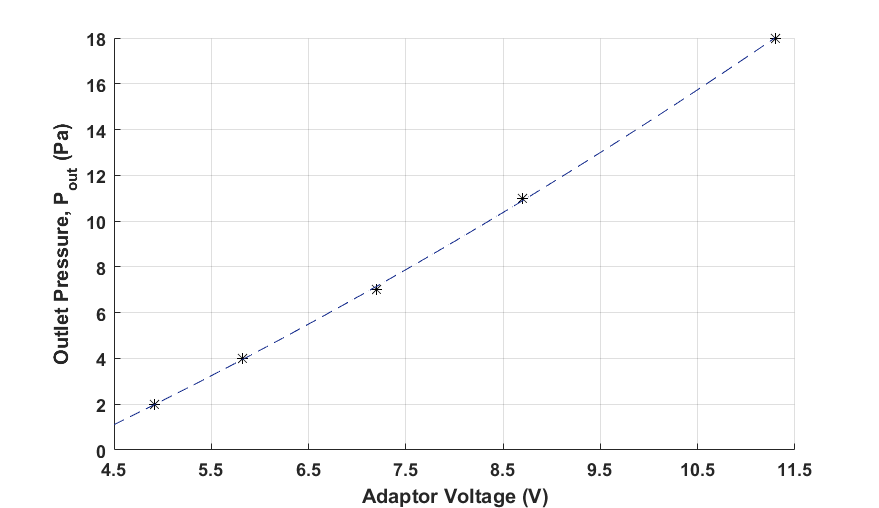
figs/P_V.png
