fsguerreiro/My_thesis/figs/pitch.png

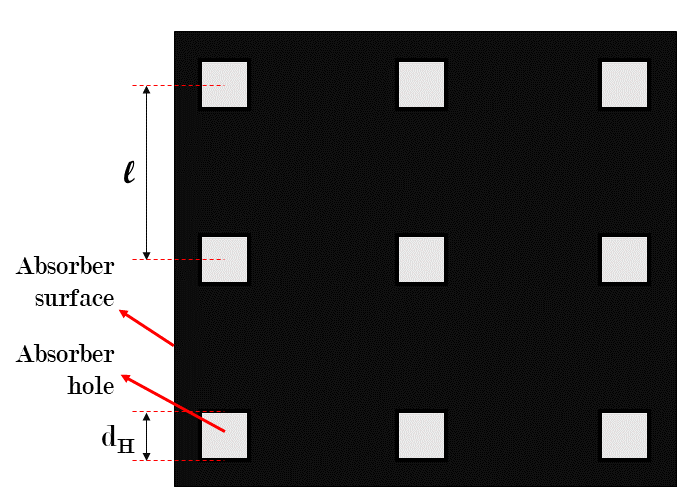
figs/pitch.png
