fsguerreiro/My_thesis/figs/QL_QU_x_hTS.png

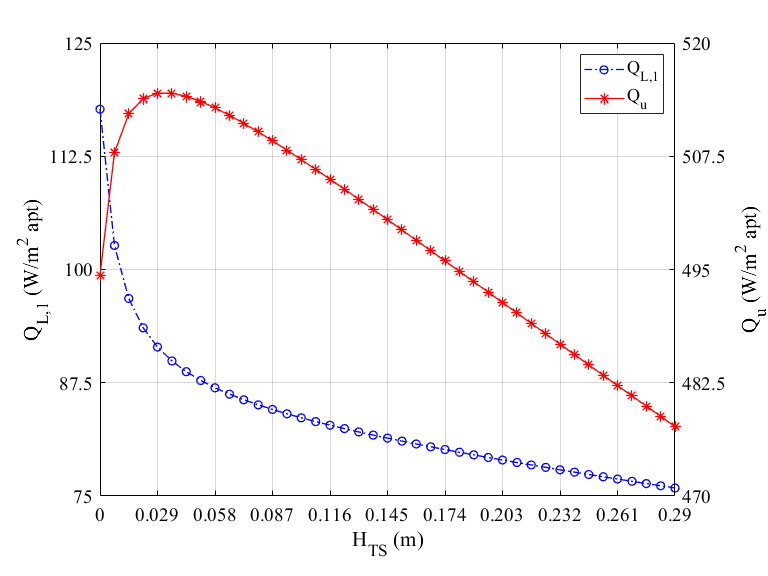
figs/QL_QU_x_hTS.png
