fsguerreiro/My_thesis/figs/QL_x_GT_emit.png

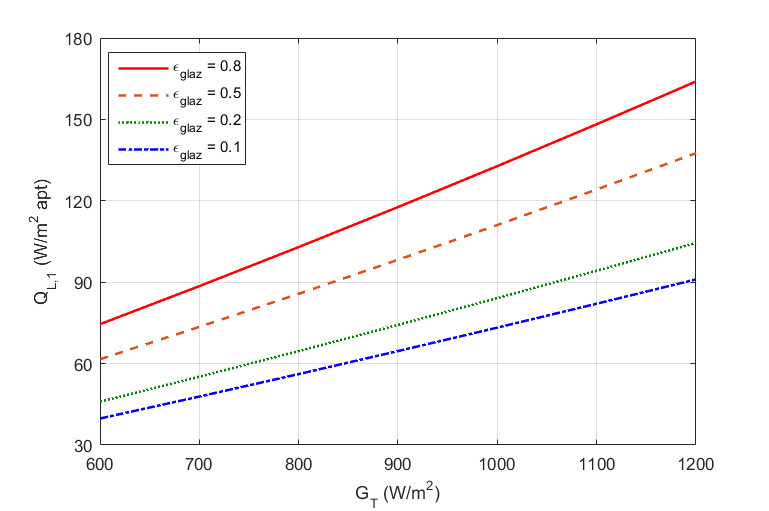
figs/QL_x_GT_emit.png
