fsguerreiro/My_thesis/figs/Qu-Tout-Gair-parallel.png

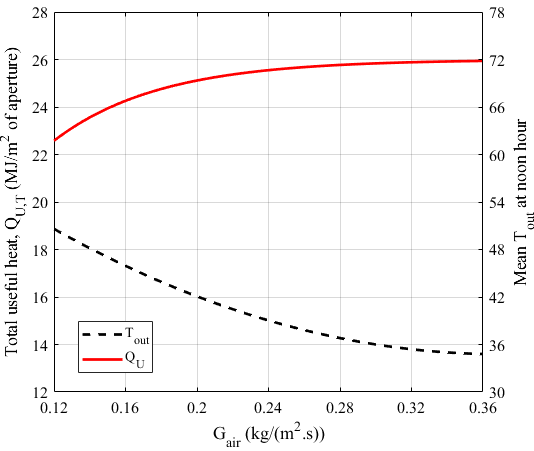
figs/Qu-Tout-Gair-parallel.png
