fsguerreiro/My_thesis/figs/Qu-Tout-Gair-series.png

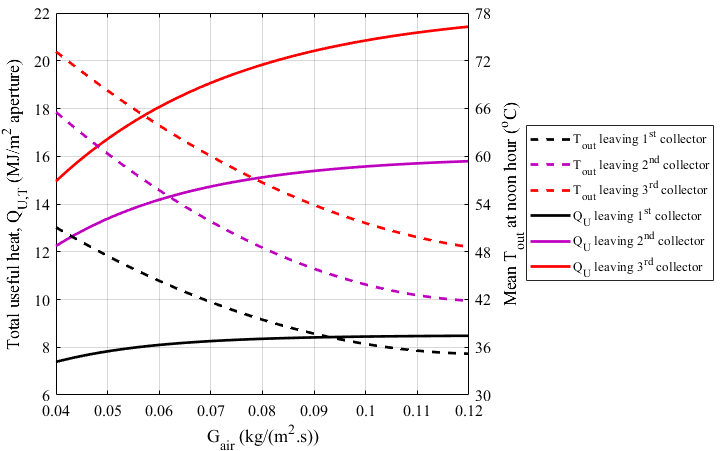
figs/Qu-Tout-Gair-series.png
