fsguerreiro/My_thesis/figs/QU_Tout_Gair.png

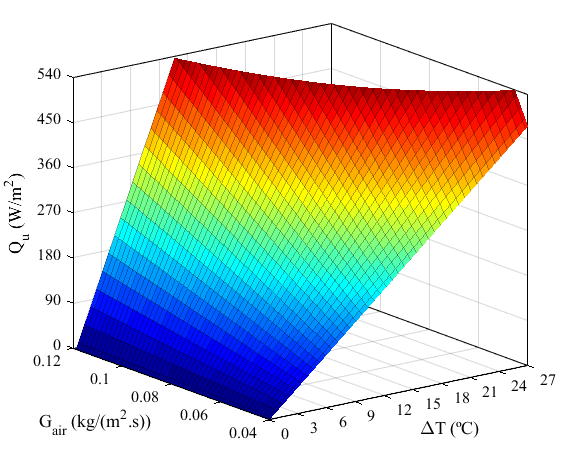
figs/QU_Tout_Gair.png
