fsguerreiro/My_thesis/figs/Qut-all.png

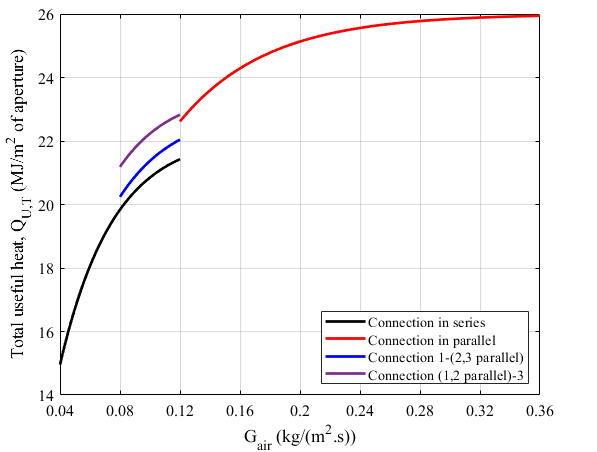
figs/Qut-all.png
