fsguerreiro/My_thesis/figs/ref_point.png

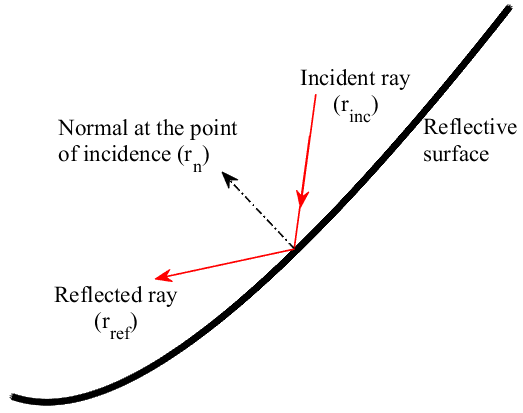
figs/ref_point.png
