fsguerreiro/My_thesis/figs/reflectance.png

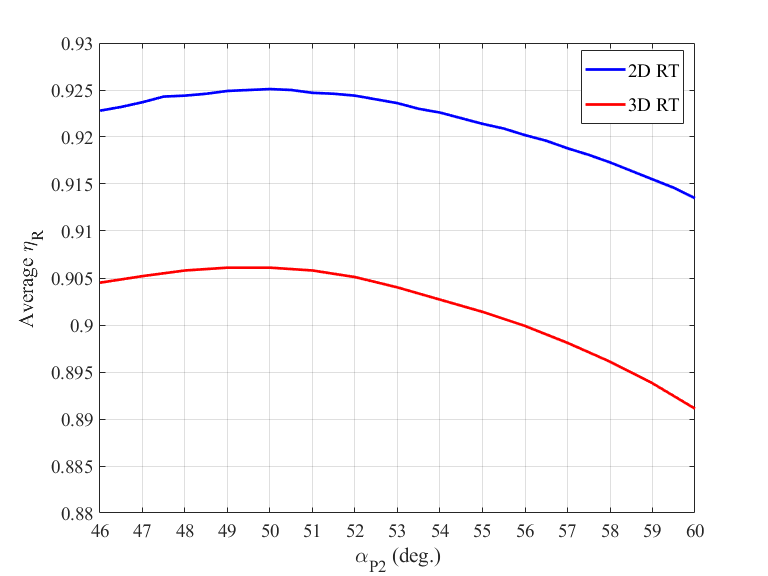
figs/reflectance.png
