fsguerreiro/My_thesis/figs/reflector_region.png

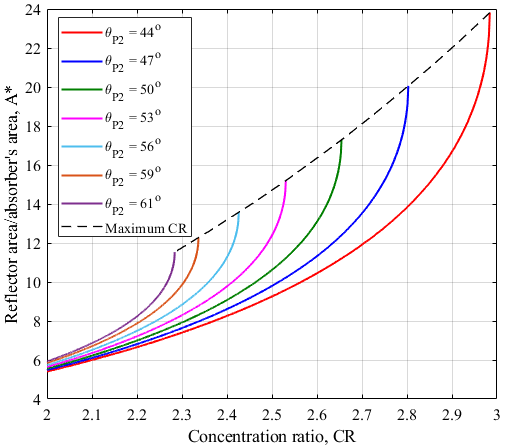
figs/reflector_region.png
