fsguerreiro/My_thesis/figs/residueQ_it.png

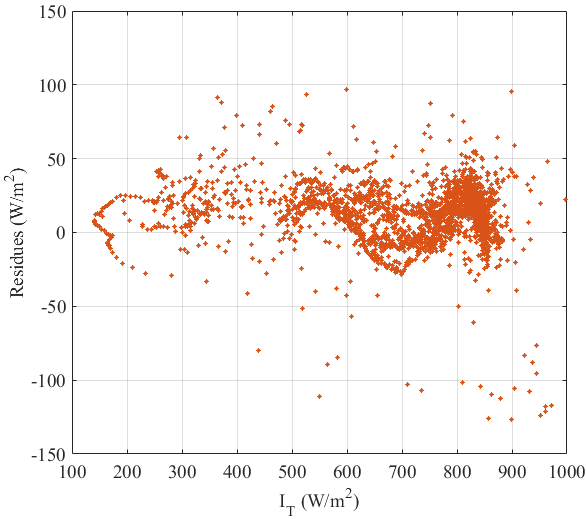
figs/residueQ_it.png
