fsguerreiro/My_thesis/figs/residueT_it.png

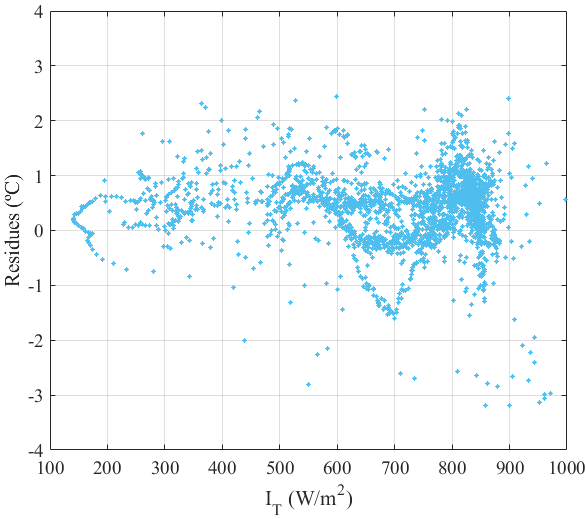
figs/residueT_it.png
