fsguerreiro/My_thesis/figs/resistances.png

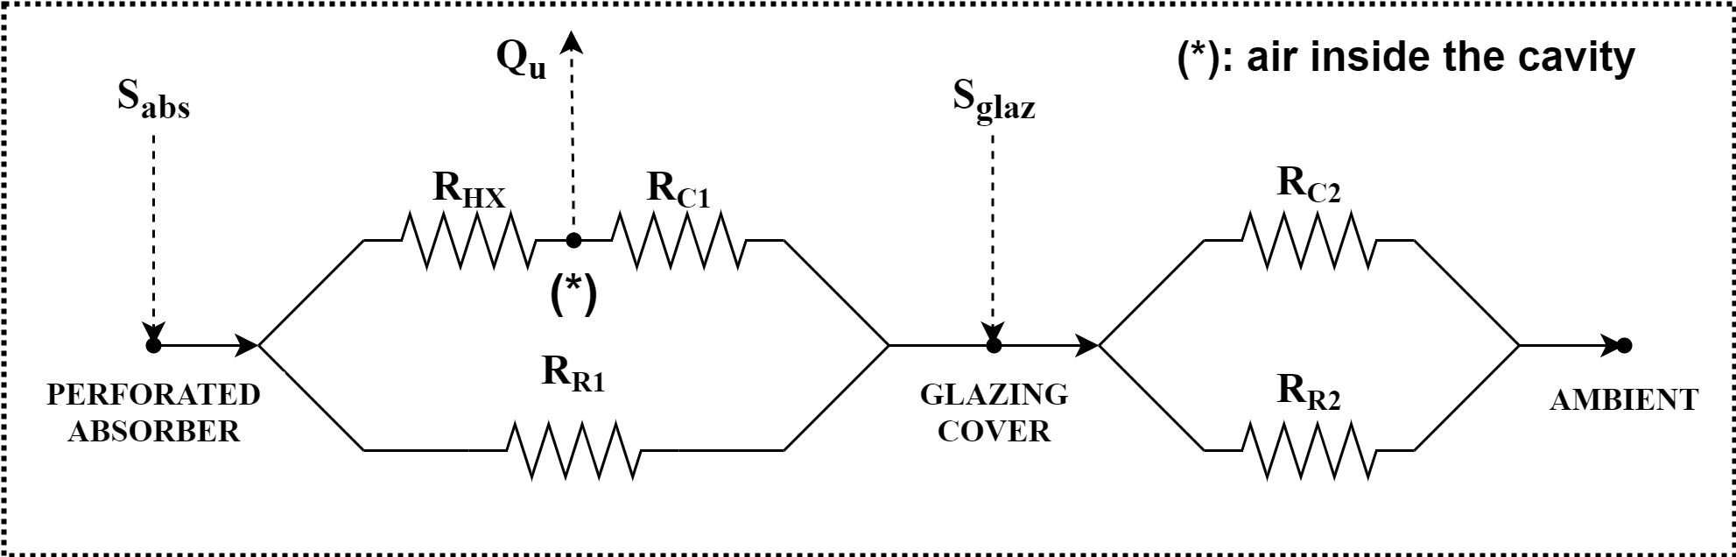
figs/resistances.png
