fsguerreiro/My_thesis/figs/rotCPC.PNG

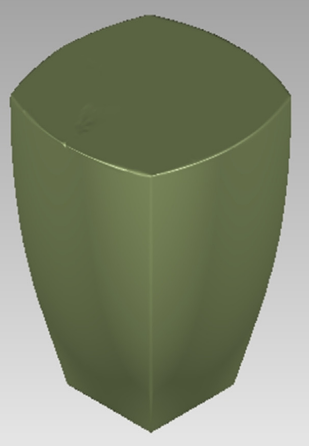
figs/rotCPC.PNG
