fsguerreiro/My_thesis/figs/RT2D-hts0.png

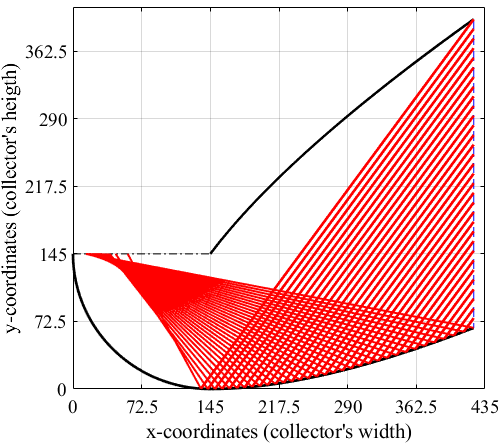
figs/RT2D-hts0.png
