fsguerreiro/My_thesis/figs/RT2D-hts72.png

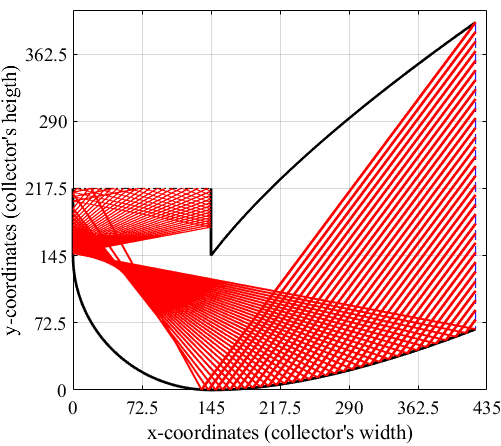
figs/RT2D-hts72.png
