fsguerreiro/My_thesis/figs/RT3D.png

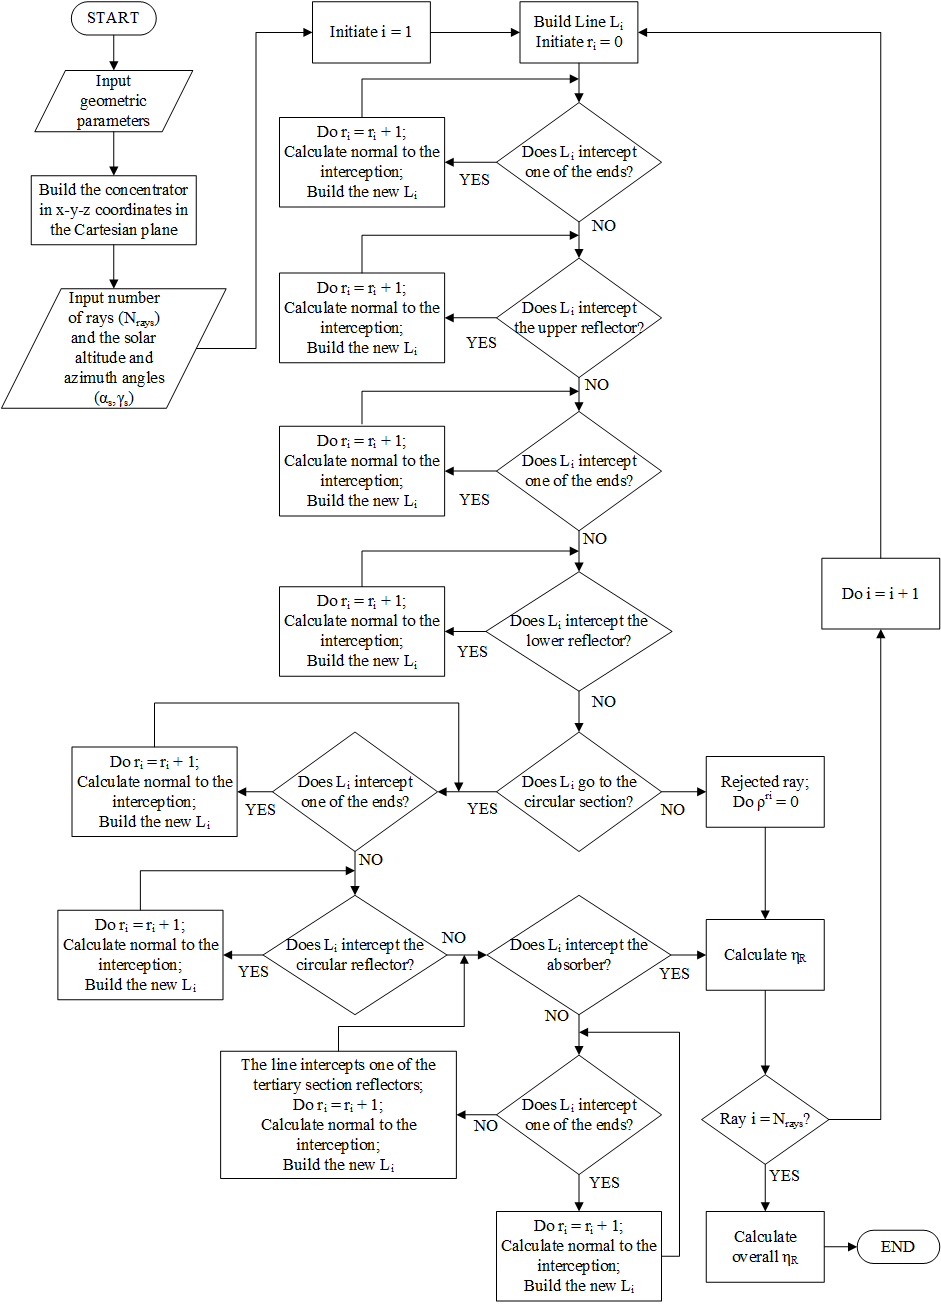
figs/RT3D.png
