fsguerreiro/My_thesis/figs/RTvisual2D.png

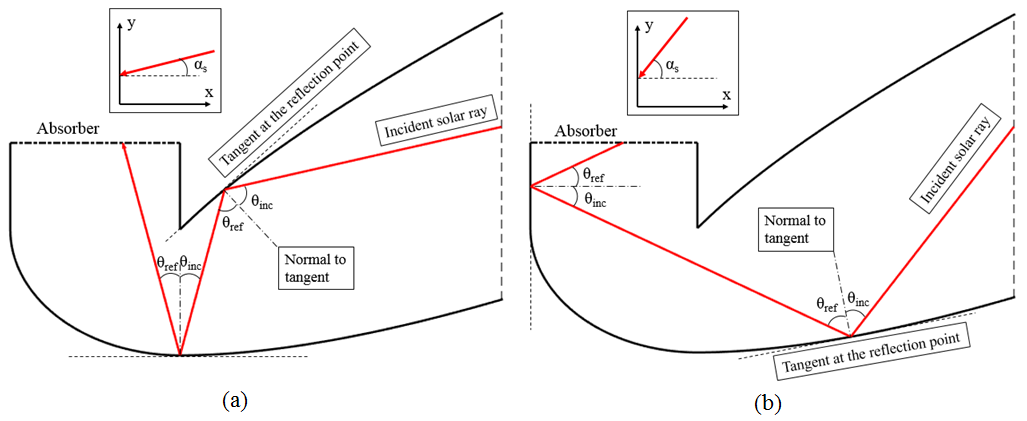
figs/RTvisual2D.png
