fsguerreiro/My_thesis/figs/scheme_prototype.jpg

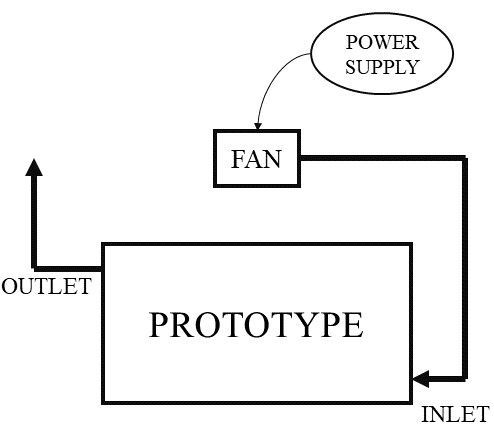
figs/scheme_prototype.jpg
