fsguerreiro/My_thesis/figs/scheme_prototype.png

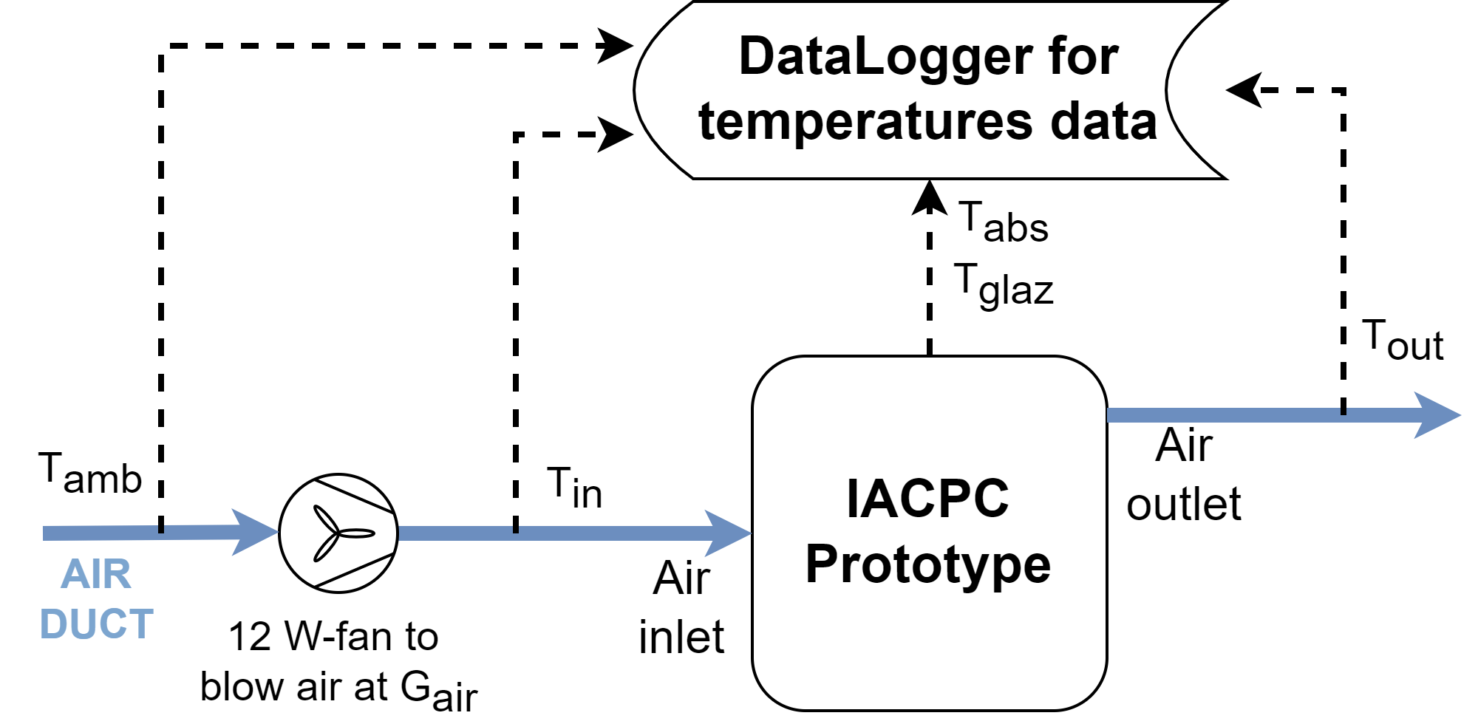
figs/scheme_prototype.png
