fsguerreiro/My_thesis/figs/series-parallel.png

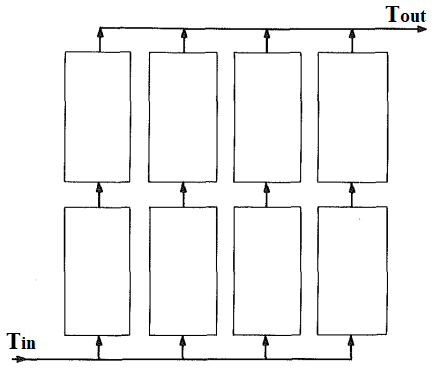
figs/series-parallel.png
