fsguerreiro/My_thesis/figs/series_1.png

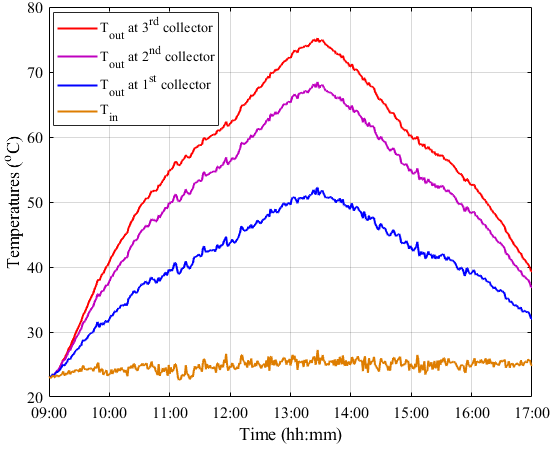
figs/series_1.png
