fsguerreiro/My_thesis/figs/series_1st.png

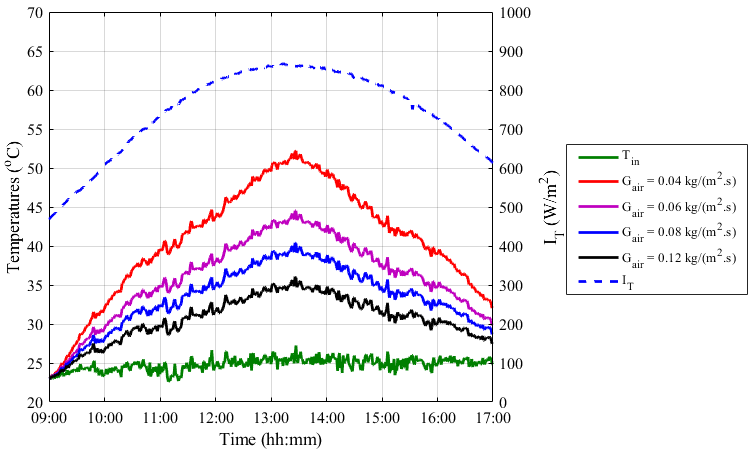
figs/series_1st.png
