fsguerreiro/My_thesis/figs/series_2.png

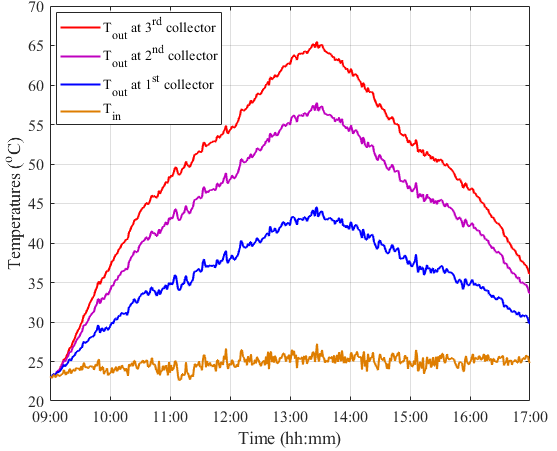
figs/series_2.png
