fsguerreiro/My_thesis/figs/series_2nd.png

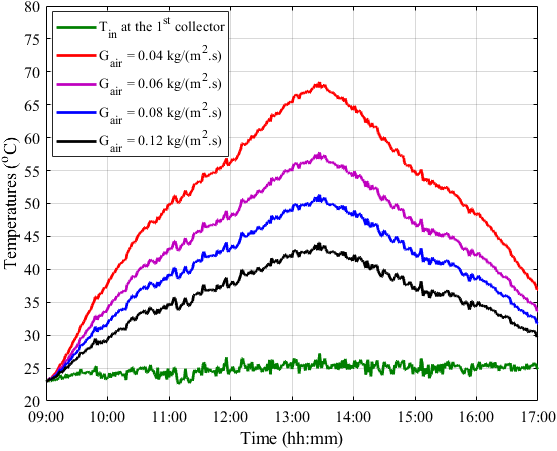
figs/series_2nd.png
