fsguerreiro/My_thesis/figs/series_3.png

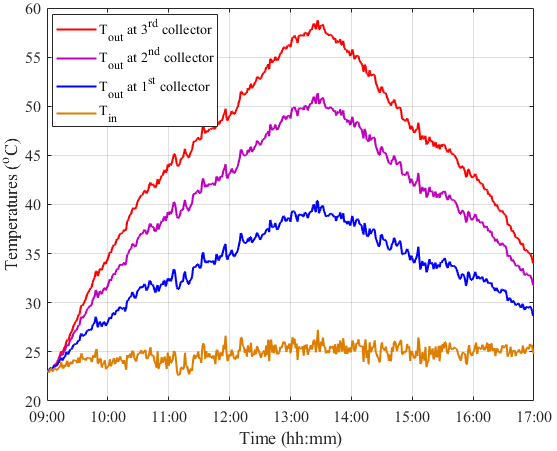
figs/series_3.png
