fsguerreiro/My_thesis/figs/series_3rd.png

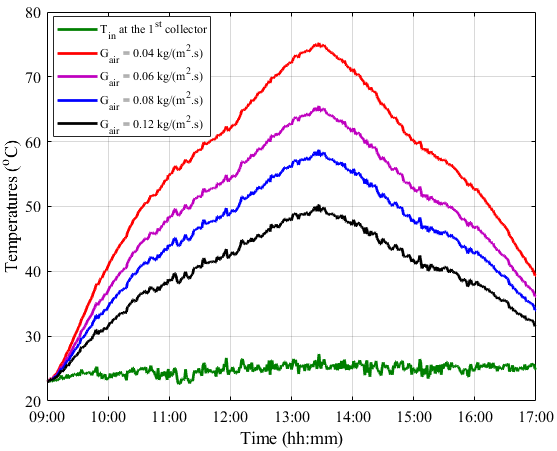
figs/series_3rd.png
