fsguerreiro/My_thesis/figs/series_4.png

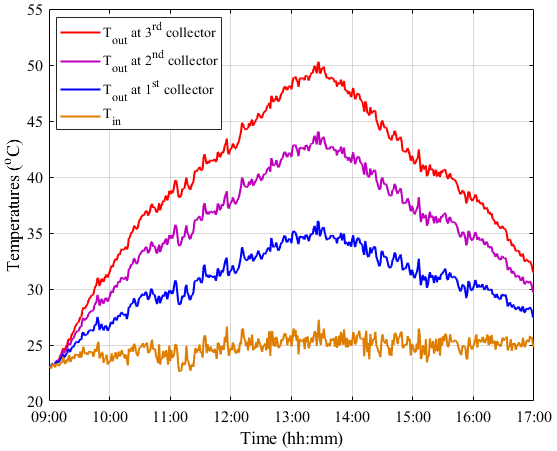
figs/series_4.png
