fsguerreiro/My_thesis/figs/series_5.png

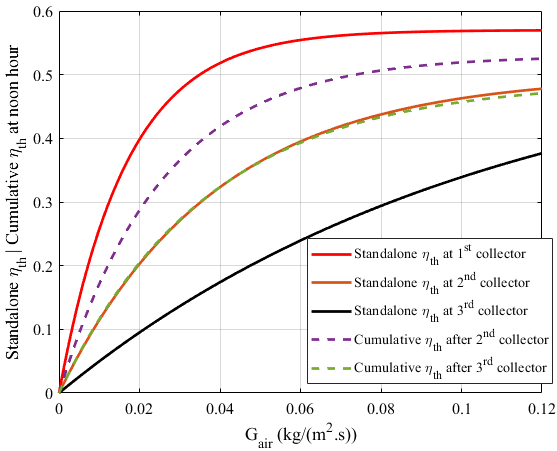
figs/series_5.png
