fsguerreiro/My_thesis/figs/series_qu.png

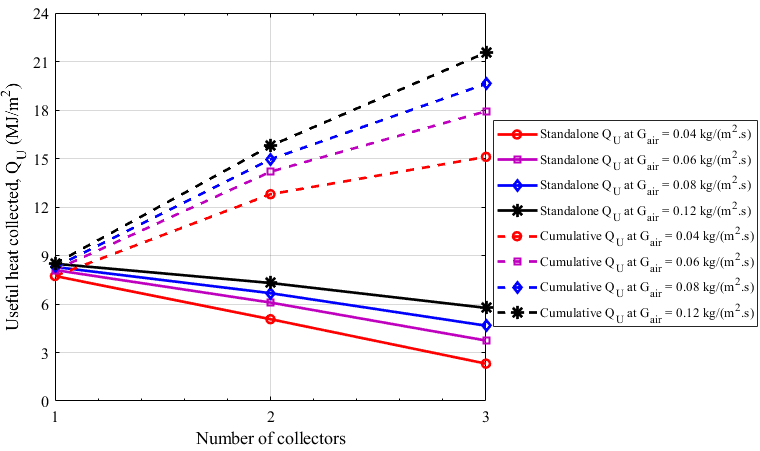
figs/series_qu.png
