fsguerreiro/My_thesis/figs/size_region2.png

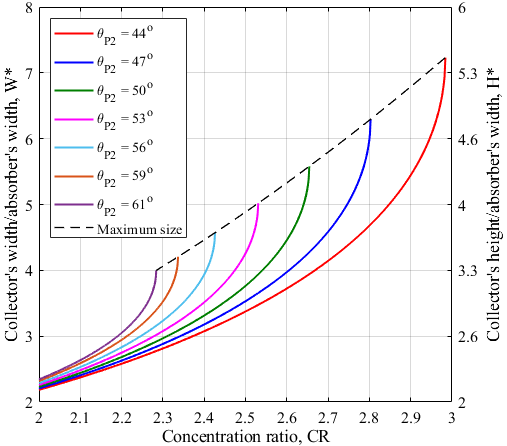
figs/size_region2.png
