fsguerreiro/My_thesis/figs/size_region3.png

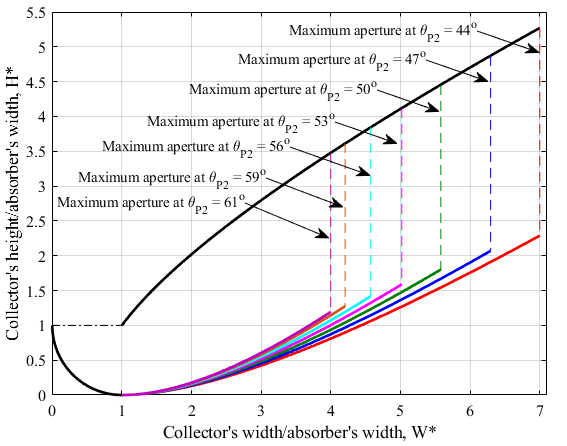
figs/size_region3.png
