fsguerreiro/My_thesis/figs/Structure1.PNG

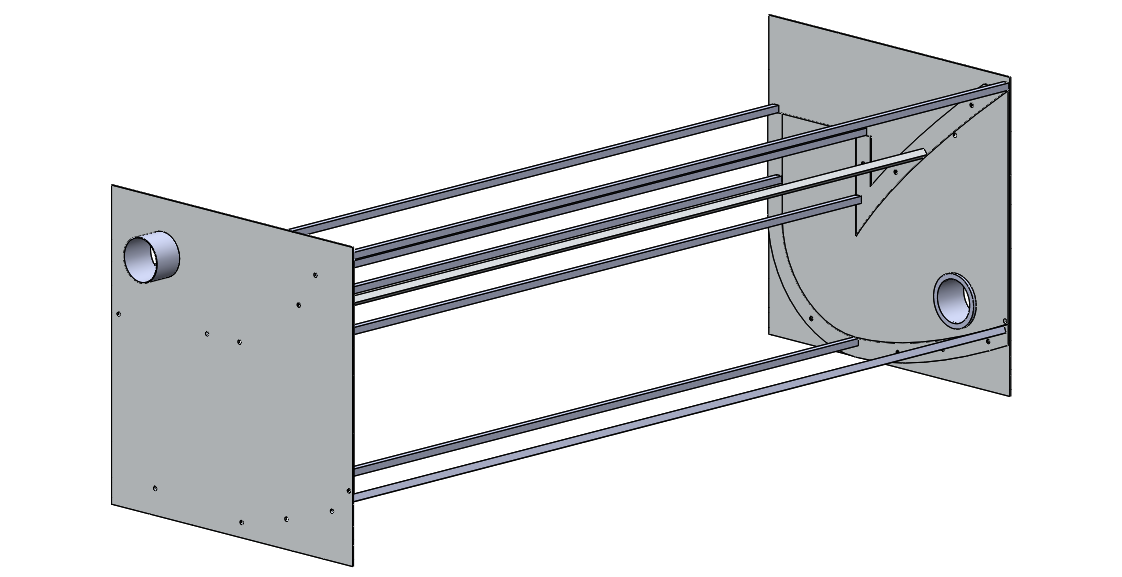
figs/Structure1.PNG
