fsguerreiro/My_thesis/figs/system-drying.png

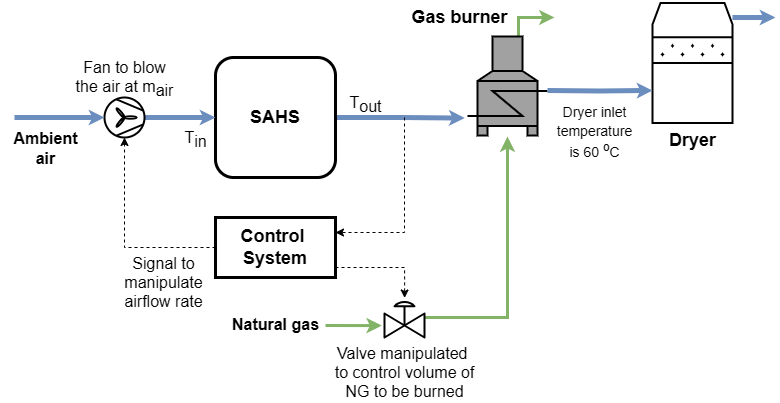
figs/system-drying.png
