fsguerreiro/My_thesis/figs/thermal_network.png

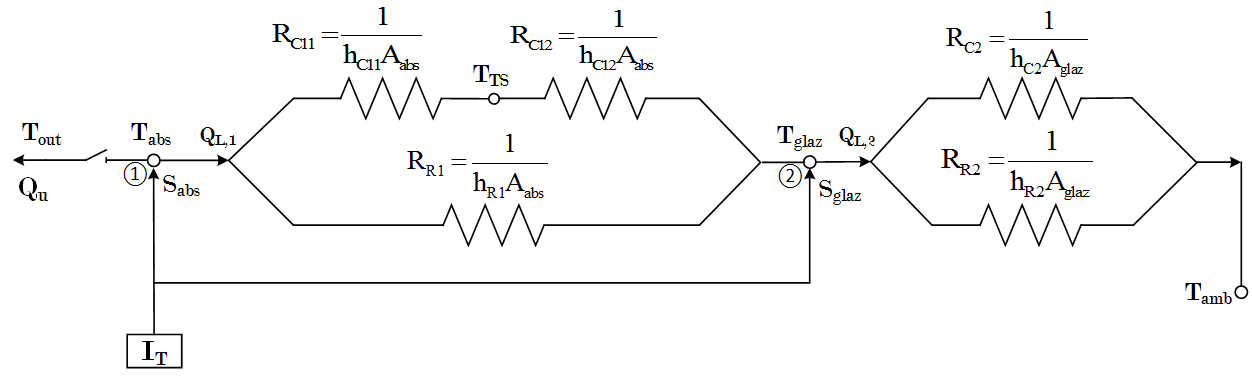
figs/thermal_network.png
