fsguerreiro/My_thesis/figs/thermocouples.png

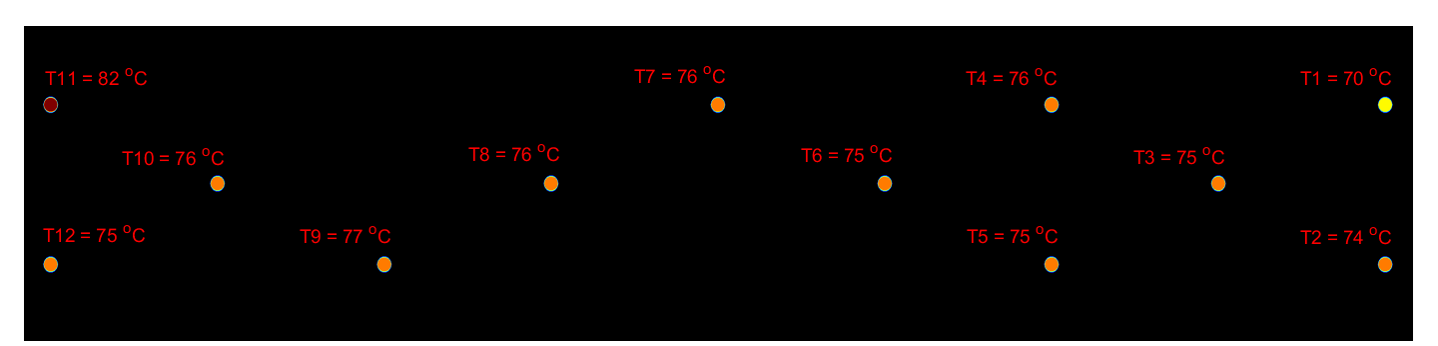
figs/thermocouples.png
