fsguerreiro/My_thesis/figs/three_sections.PNG

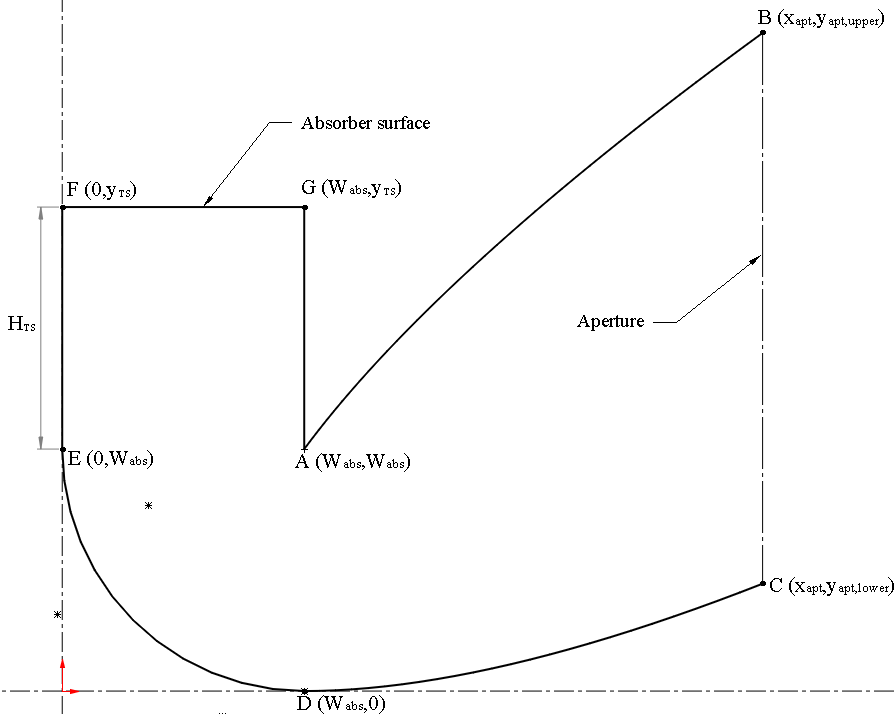
figs/three_sections.PNG
