fsguerreiro/My_thesis/figs/time_and_date.png

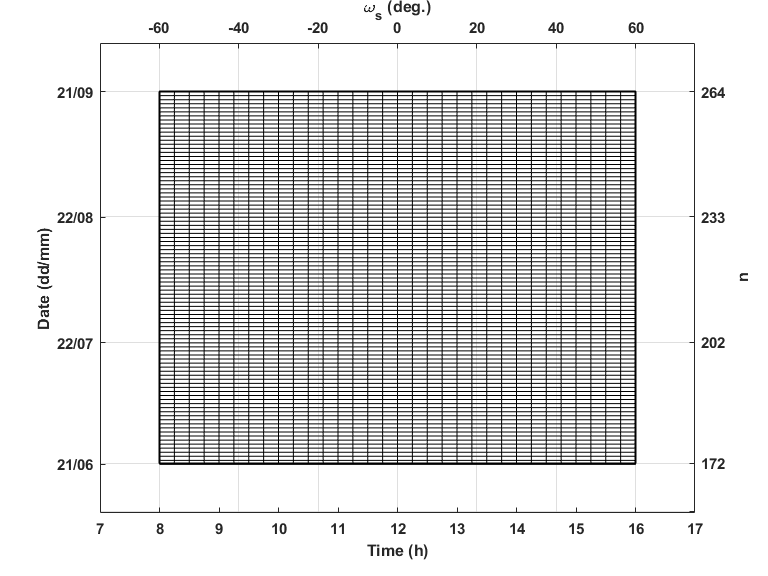
figs/time_and_date.png
