fsguerreiro/My_thesis/figs/totalE_dry_1col.png

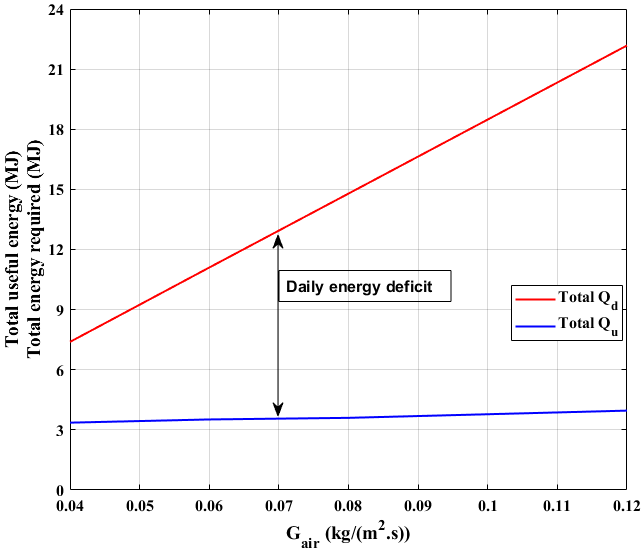
figs/totalE_dry_1col.png
