fsguerreiro/My_thesis/figs/Tout-all.png

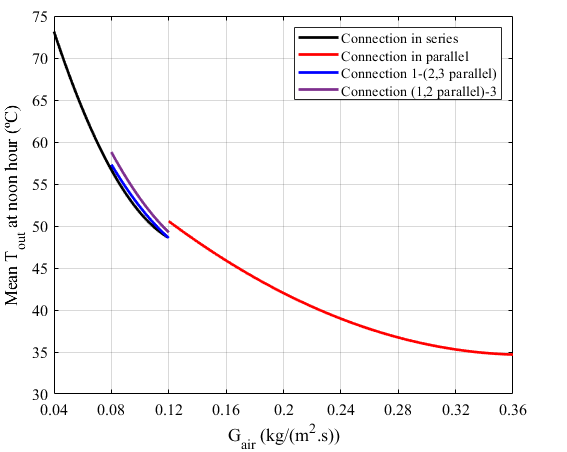
figs/Tout-all.png
