fsguerreiro/My_thesis/figs/Tout-Gair.png

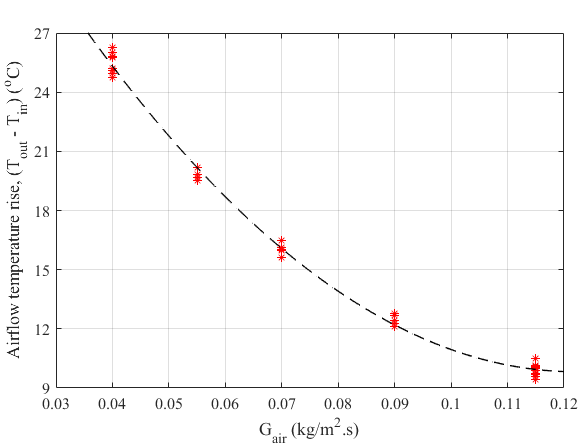
figs/Tout-Gair.png
