fsguerreiro/My_thesis/figs/Touts_sim.png

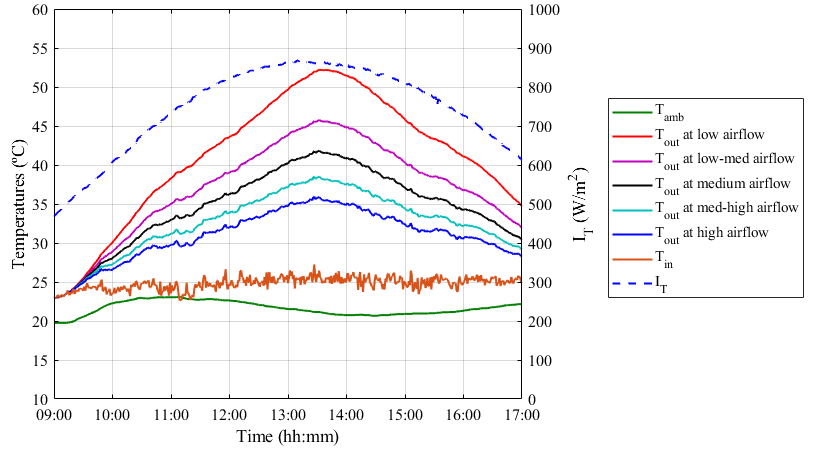
figs/Touts_sim.png
