fsguerreiro/My_thesis/figs/transm-time.png

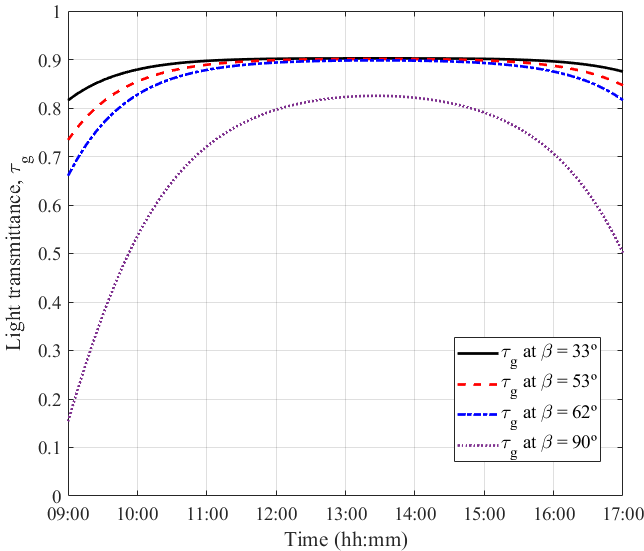
figs/transm-time.png
