fsguerreiro/My_thesis/figs/transm.png

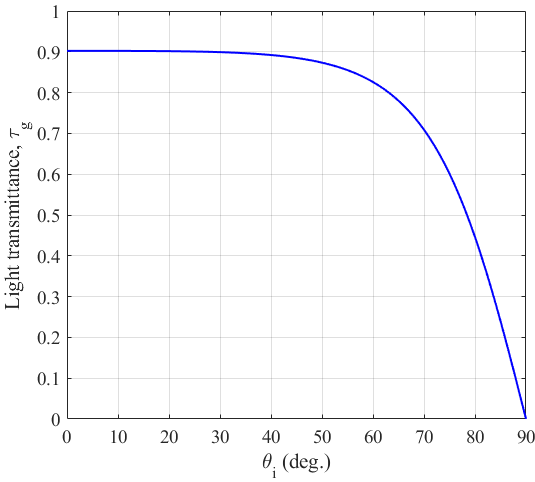
figs/transm.png
