fsguerreiro/My_thesis/figs/TS0-1.png

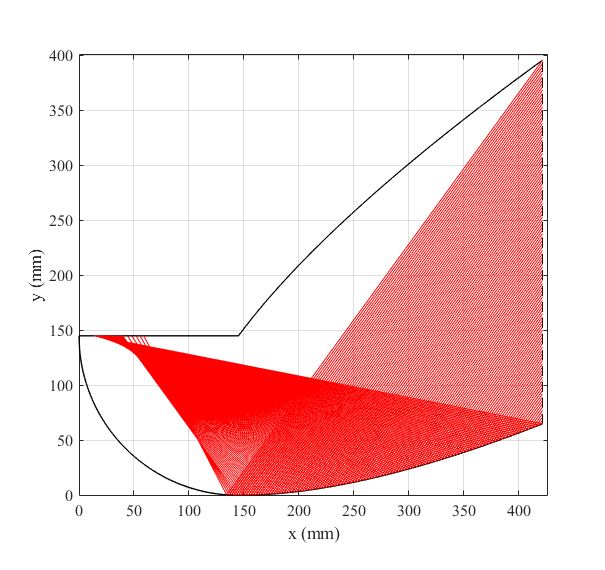
figs/TS0-1.png
