fsguerreiro/My_thesis/figs/TS0-22.png

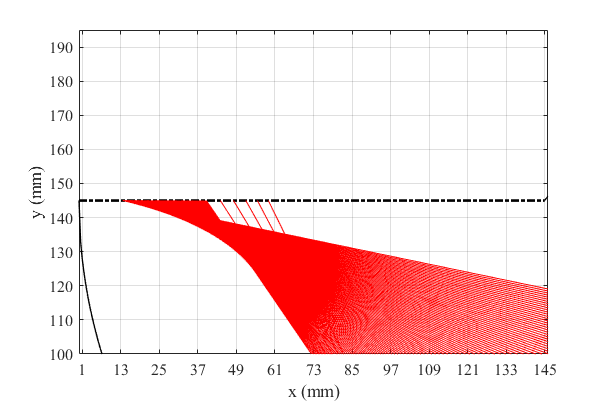
figs/TS0-22.png
