fsguerreiro/My_thesis/figs/TS0_Energy.png

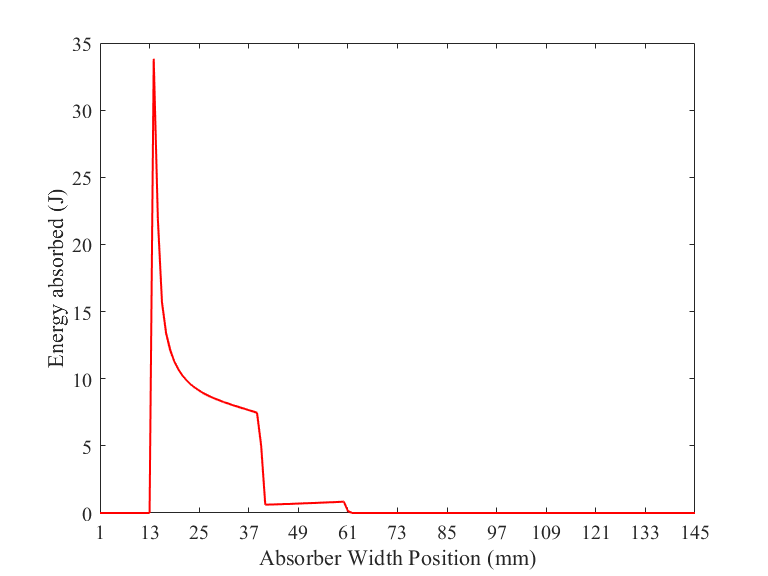
figs/TS0_Energy.png
