fsguerreiro/My_thesis/figs/TS72-1.png

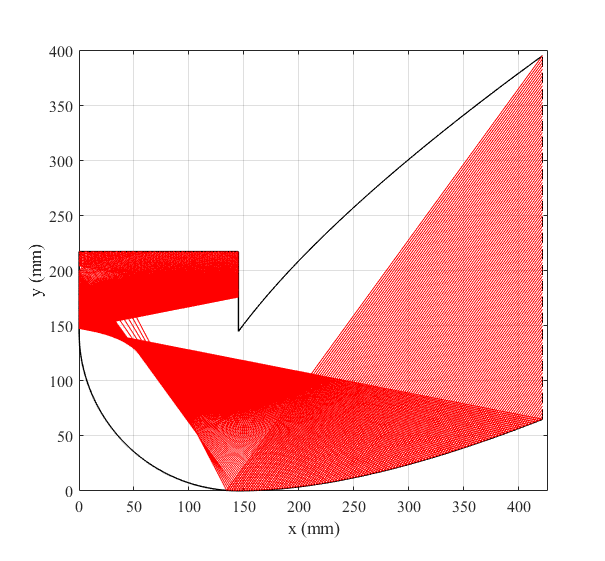
figs/TS72-1.png
