fsguerreiro/My_thesis/figs/TS72-22.png

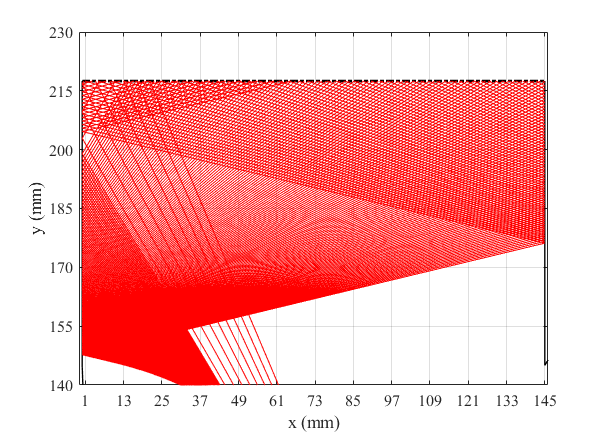
figs/TS72-22.png
