fsguerreiro/My_thesis/figs/TS72-Energy.png

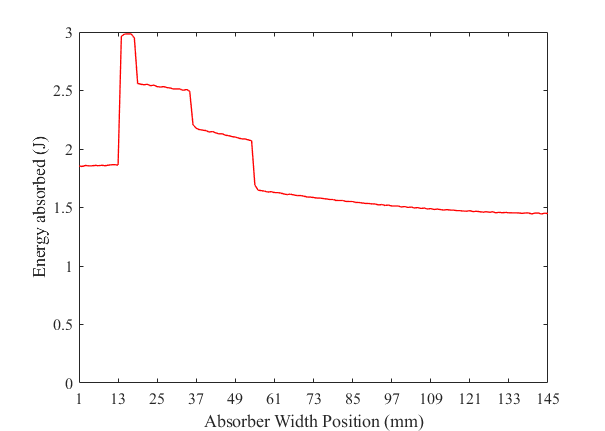
figs/TS72-Energy.png
