fsguerreiro/My_thesis/figs/TS145-1.png

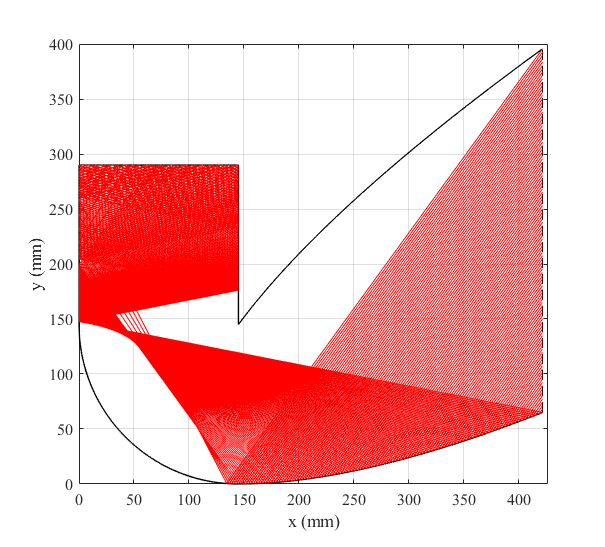
figs/TS145-1.png
