fsguerreiro/My_thesis/figs/TS145-22.png

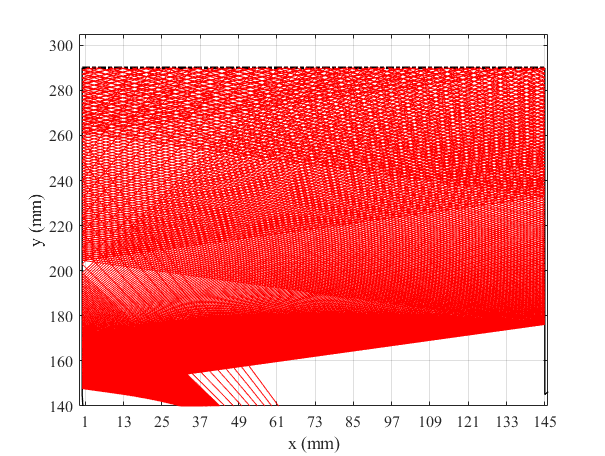
figs/TS145-22.png
