fsguerreiro/My_thesis/figs/TS145-Energy.png

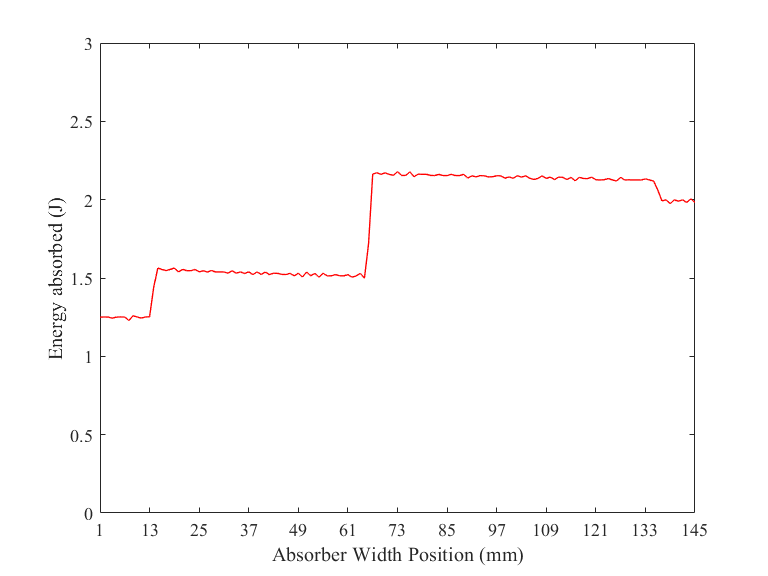
figs/TS145-Energy.png
