fsguerreiro/My_thesis/figs/unglazed-glazed.png

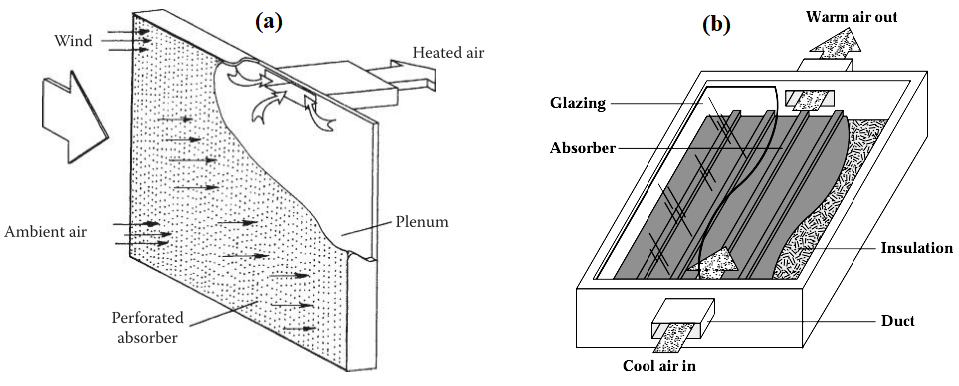
figs/unglazed-glazed.png
