fsguerreiro/My_thesis/figs/unit3.png

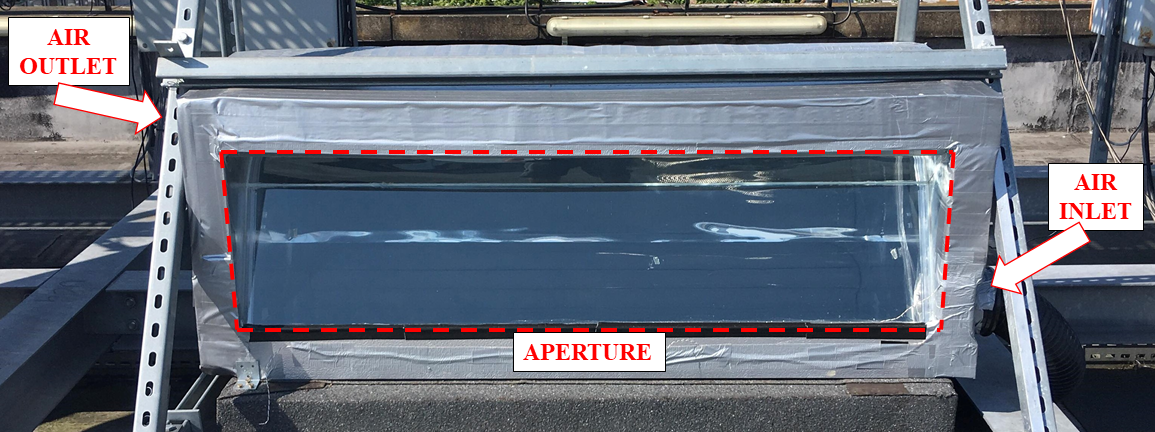
figs/unit3.png
