fsguerreiro/My_thesis/figs/untruncated.png

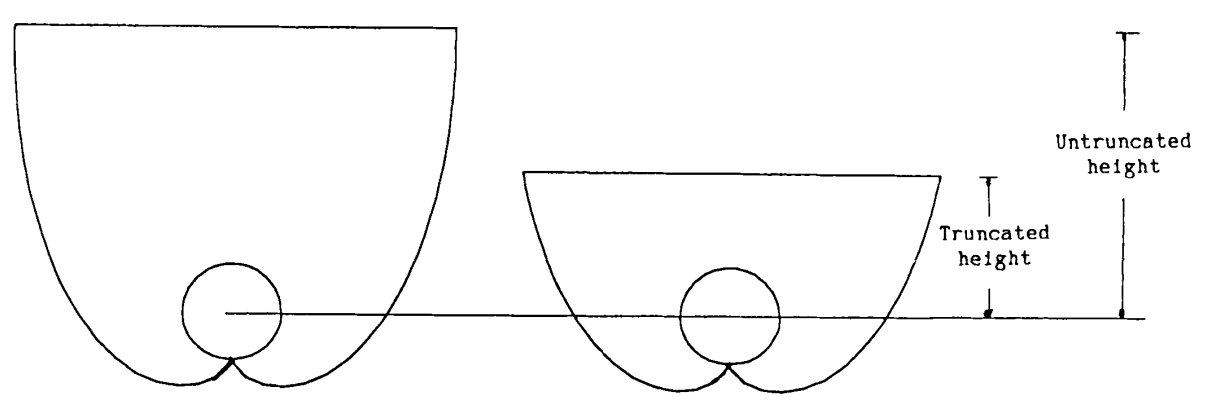
figs/untruncated.png
