fsguerreiro/My_thesis/figs/zero1.png

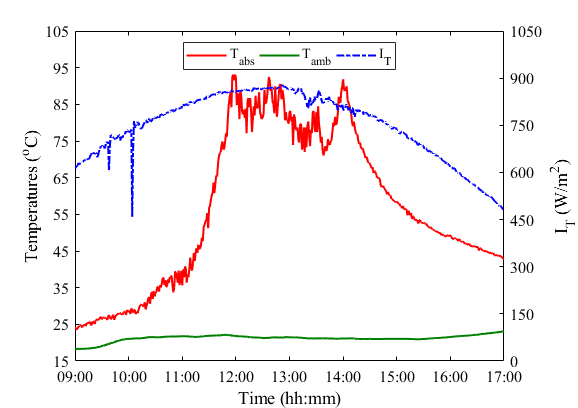
figs/zero1.png
