fsguerreiro/My_thesis/figs/zero12.png

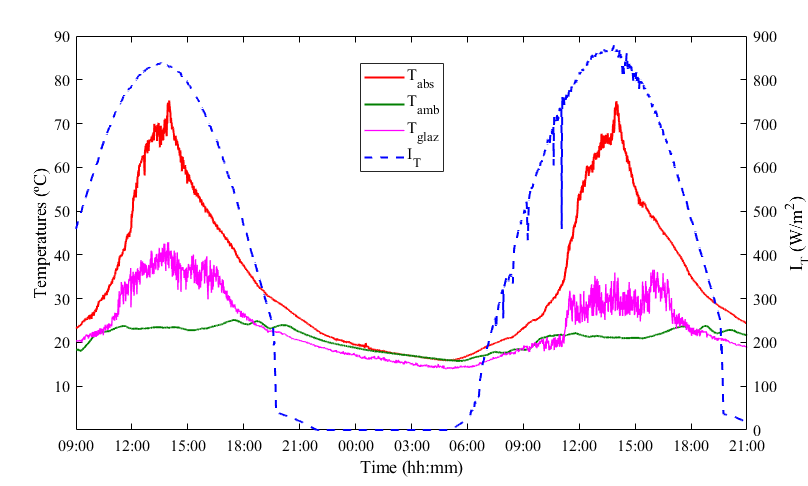
figs/zero12.png
