fsguerreiro/My_thesis/figs/cost-weight.png

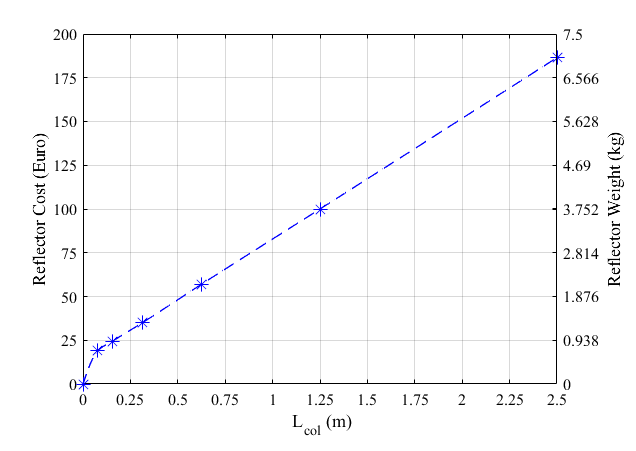
figs/cost-weight.png
