fsguerreiro/My_thesis/figs/assembly2.png

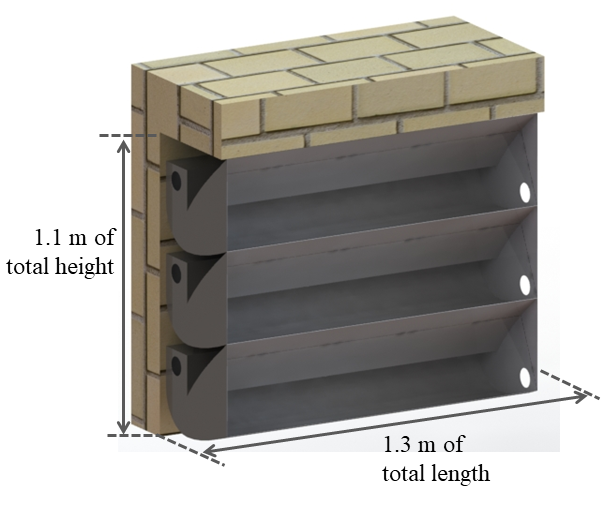
figs/assembly2.png
