fsguerreiro/My_thesis/figs/RTassembly.png

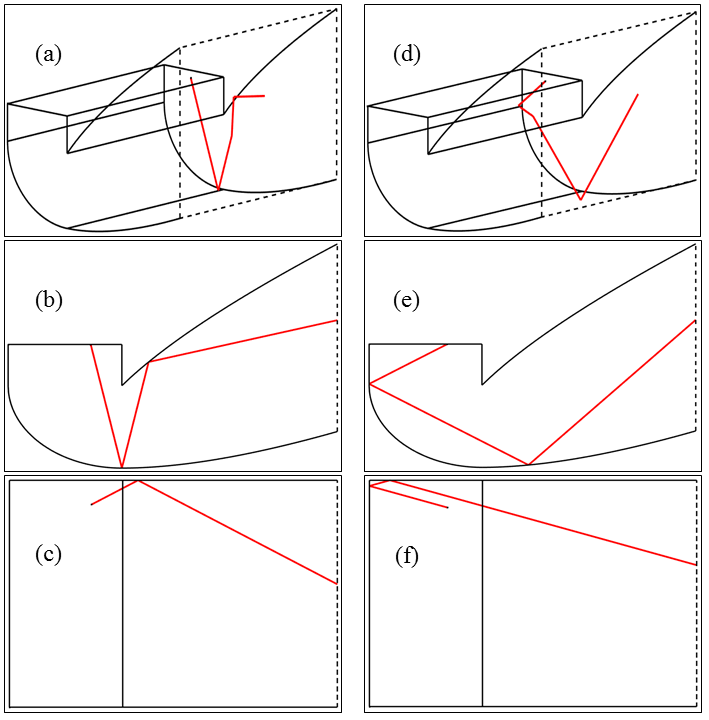
figs/RTassembly.png
