fsguerreiro/My_thesis/figs/004-3-eps-converted-to.pdf

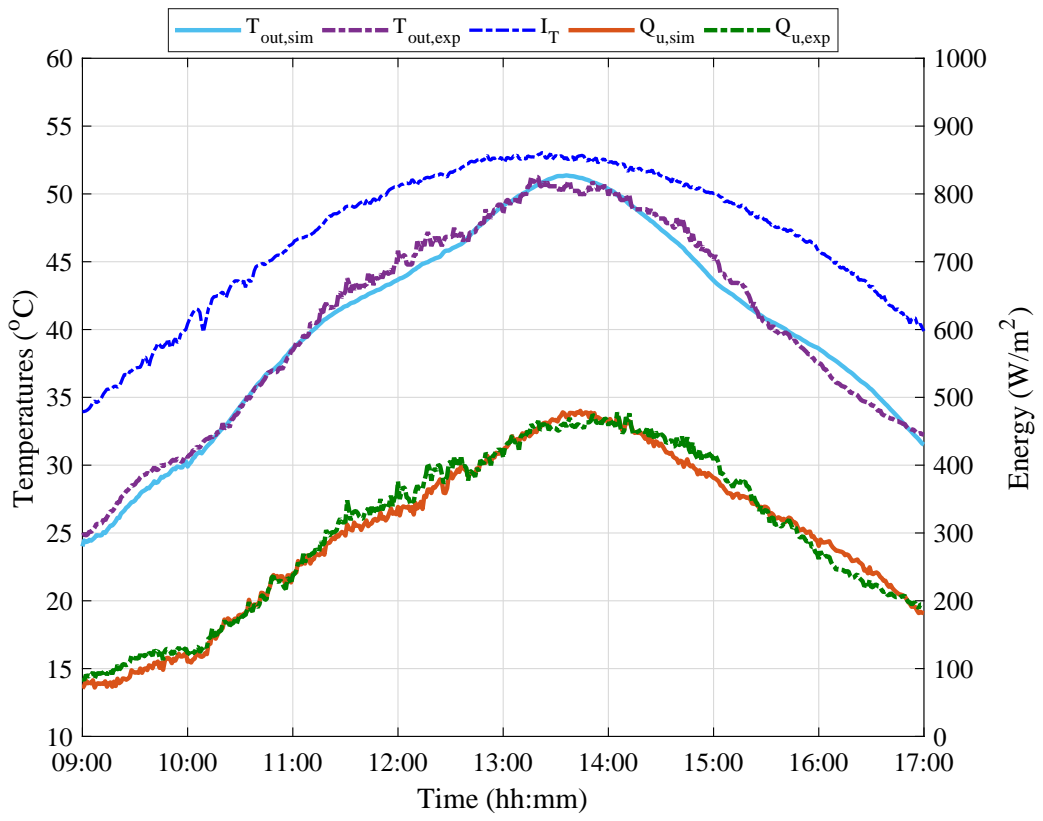
[picture p242: page 1]
Temperatures (; Energy (W/m; Tout,sim; Tout,exp; Qu,sim; Qu,exp

Time (hh:mm)
