fsguerreiro/My_thesis/figs/0055-1-eps-converted-to.pdf

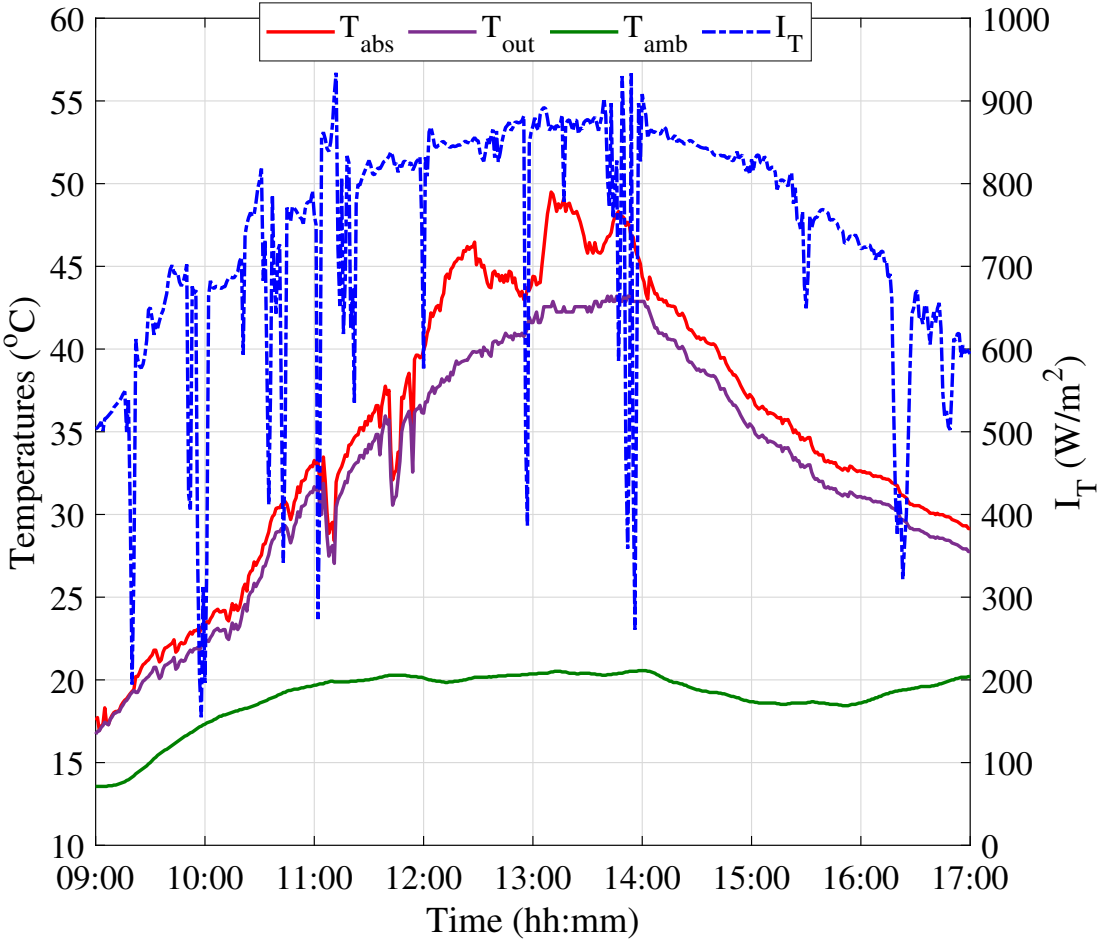
[picture p243: page 1]
Temperatures (; abs; out; amb

Time (hh:mm)
