fsguerreiro/My_thesis/figs/0055-3-eps-converted-to.pdf

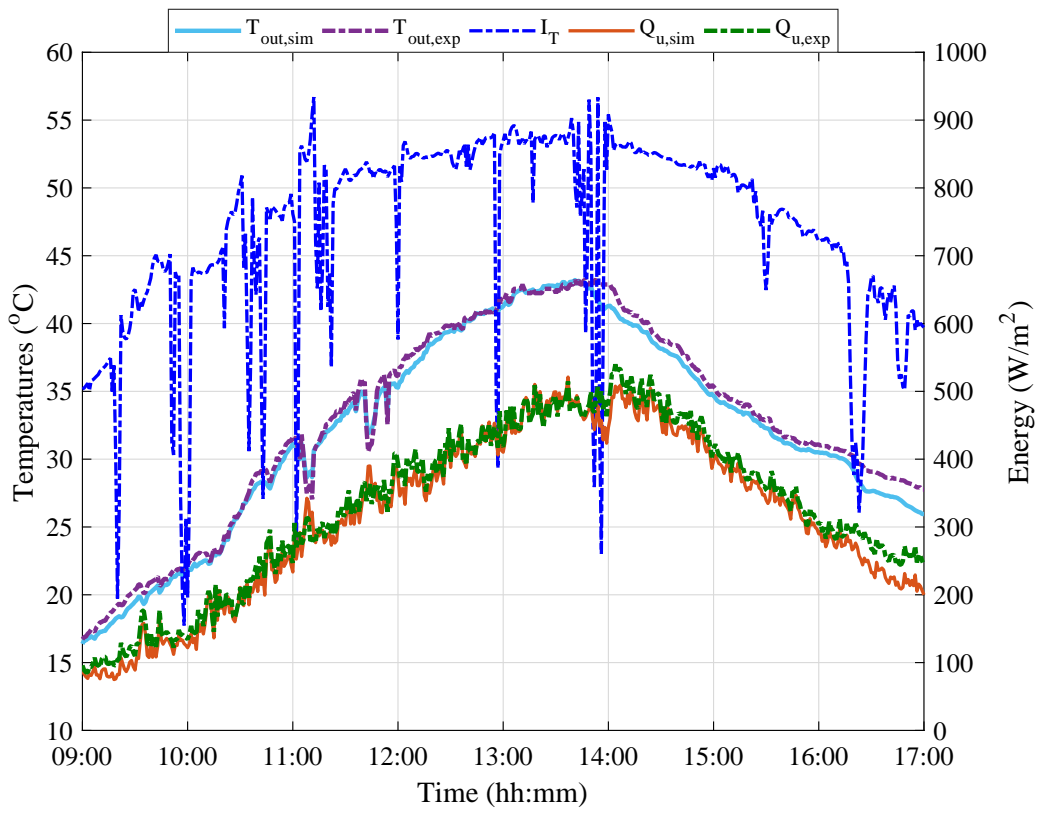
[picture p244: page 1]
Temperatures (; Energy (W/m; Tout,sim; Tout,exp; Qu,sim; Qu,exp

Time (hh:mm)
