fsguerreiro/My_thesis/figs/007-1-eps-converted-to.pdf

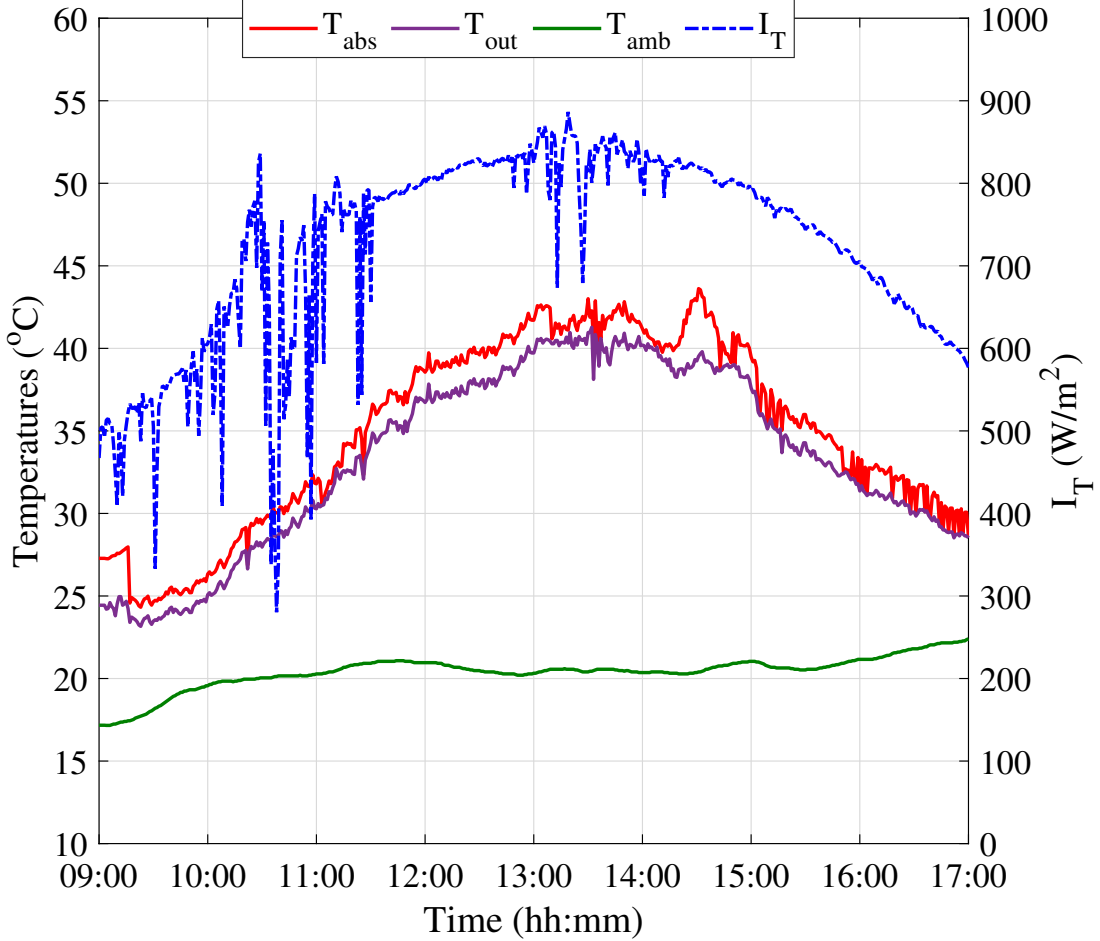
[picture p245: page 1]
Temperatures (; abs; out; amb

Time (hh:mm)
