fsguerreiro/My_thesis/figs/009-1-eps-converted-to.pdf

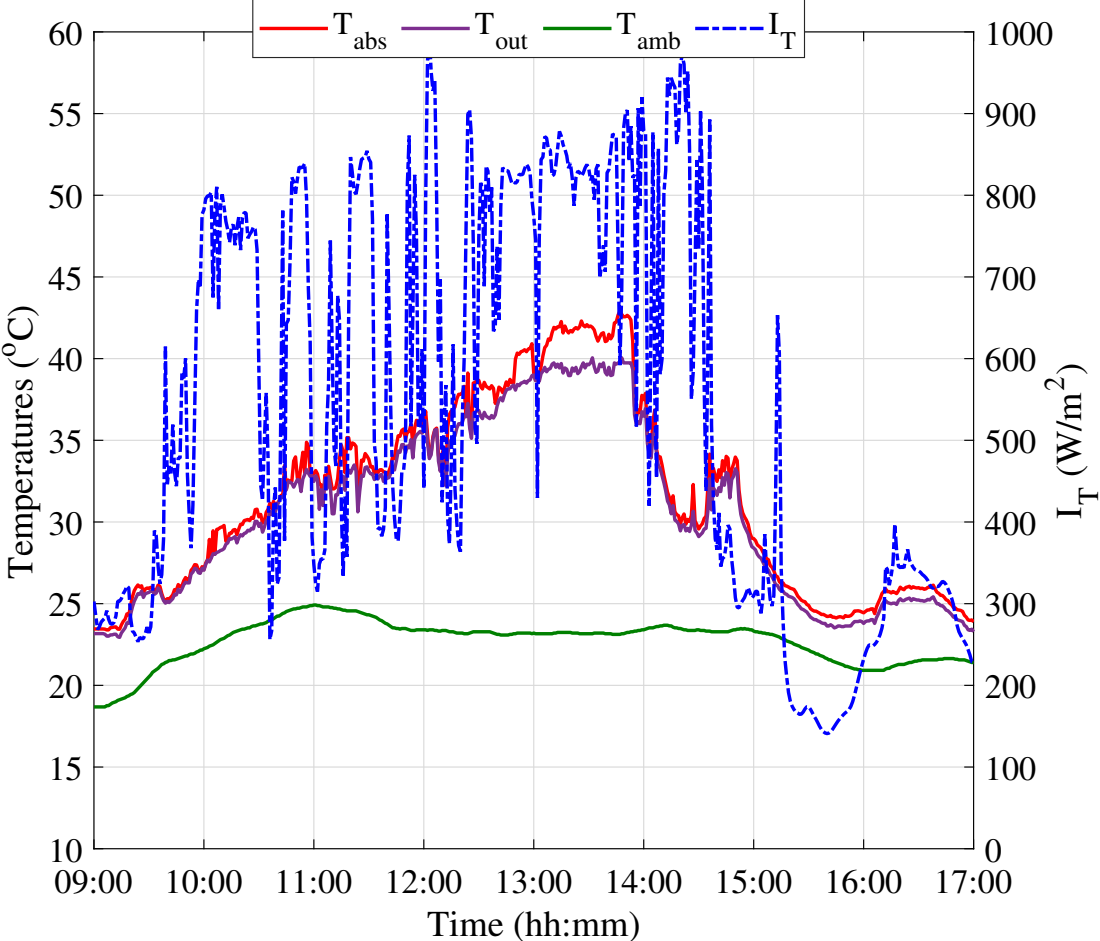
[picture p247: page 1]
Temperatures (; abs; out; amb

Time (hh:mm)
