fsguerreiro/My_thesis/figs/0115-1-eps-converted-to.pdf

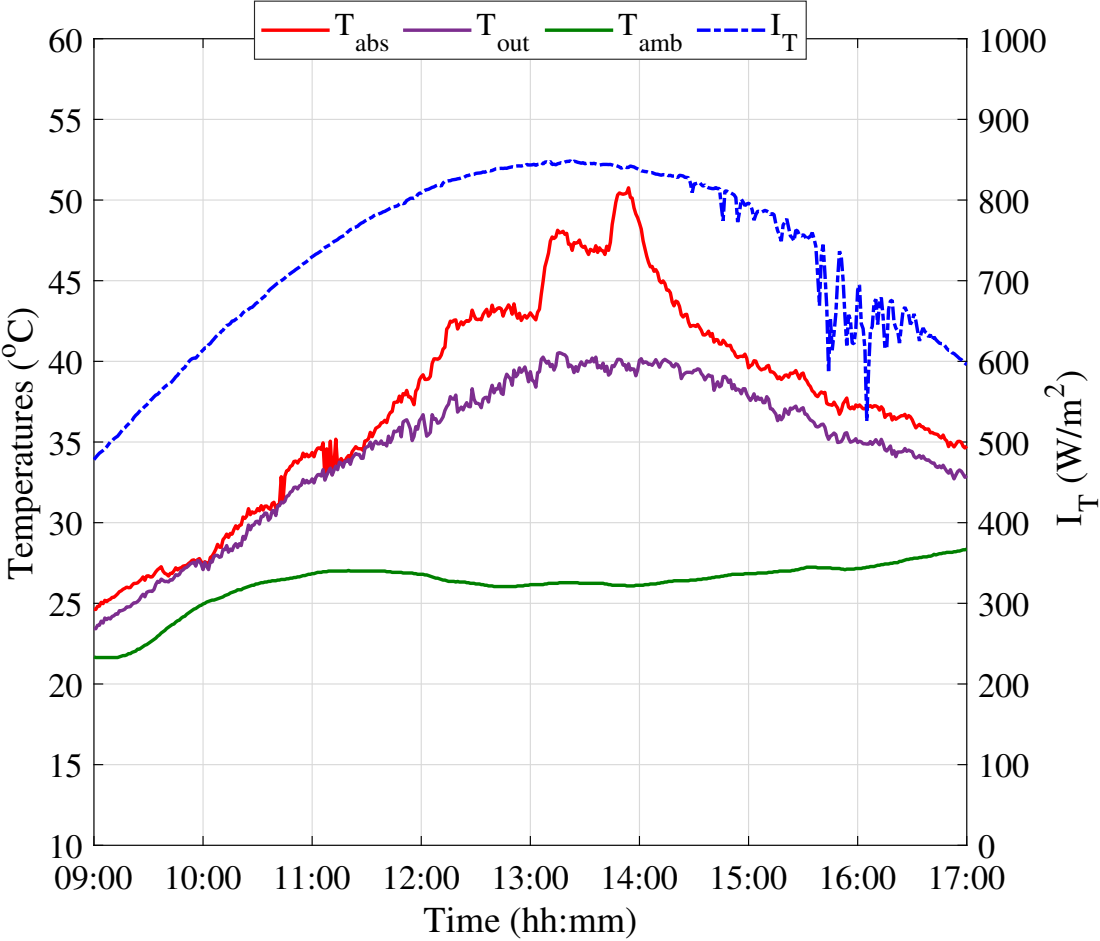
[picture p249: page 1]
Temperatures (; abs; out; amb

Time (hh:mm)
