fsguerreiro/My_thesis/figs/0115-3-eps-converted-to.pdf

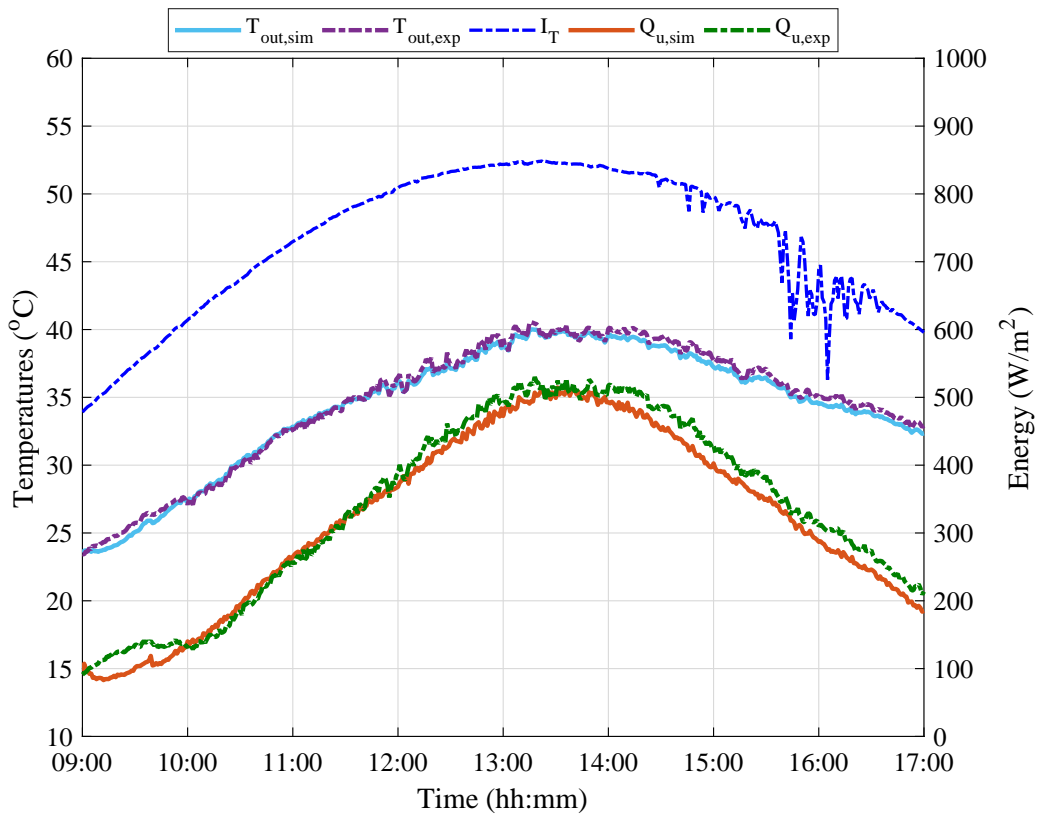
[picture p250: page 1]
Temperatures (; Energy (W/m; Tout,sim; Tout,exp; Qu,sim; Qu,exp

Time (hh:mm)
