fsguerreiro/My_thesis/figs/collector2p-eps-converted-to.pdf

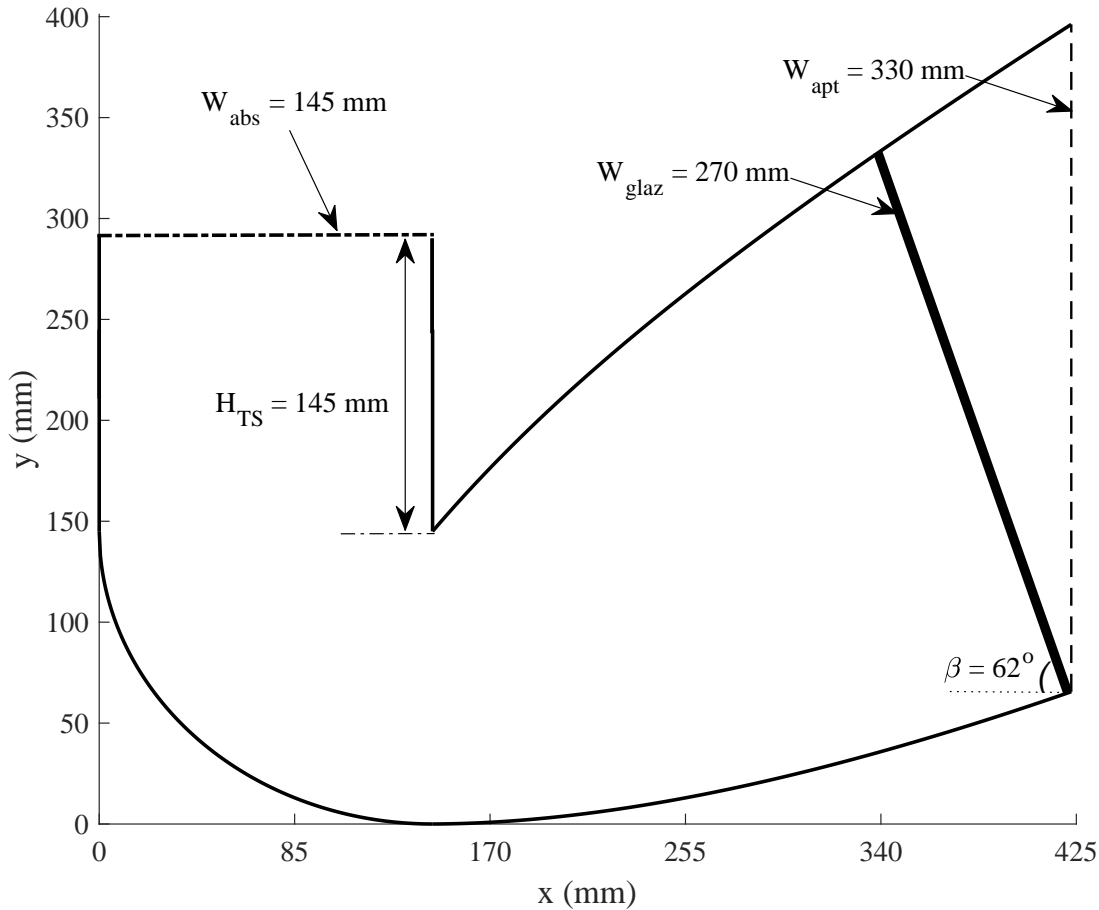
[picture p251: page 1]
apt; Wglaz = 270 mm; Wabs = 145 mm; HTS = 145 mm
