fsguerreiro/My_thesis/figs/dry_high_1col-eps-converted-to.pdf

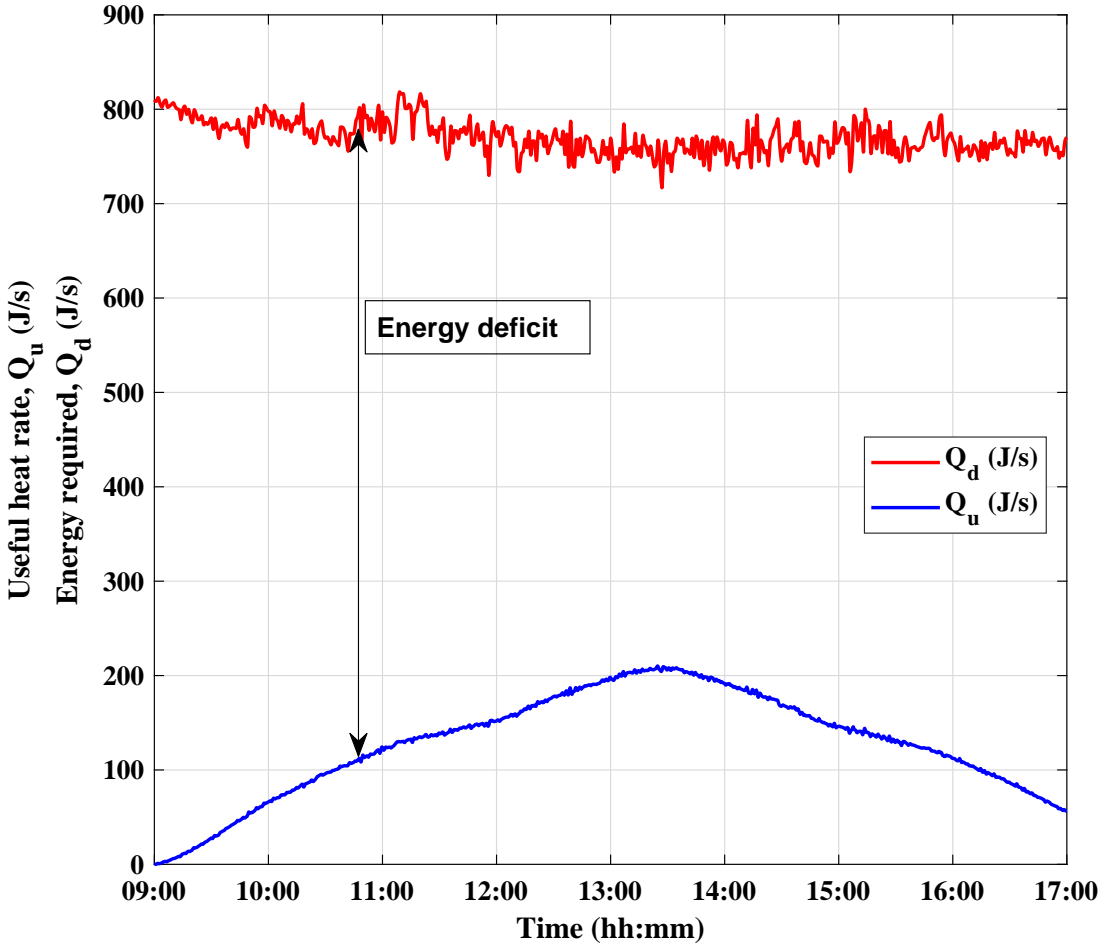
[picture p252: page 1]
Energy required, Q

Energy deficit

Useful heat rate, Q

Qd | (J/s)
Qu | (J/s)

Time (hh:mm)
