fsguerreiro/My_thesis/figs/dry_low_1col-eps-converted-to.pdf

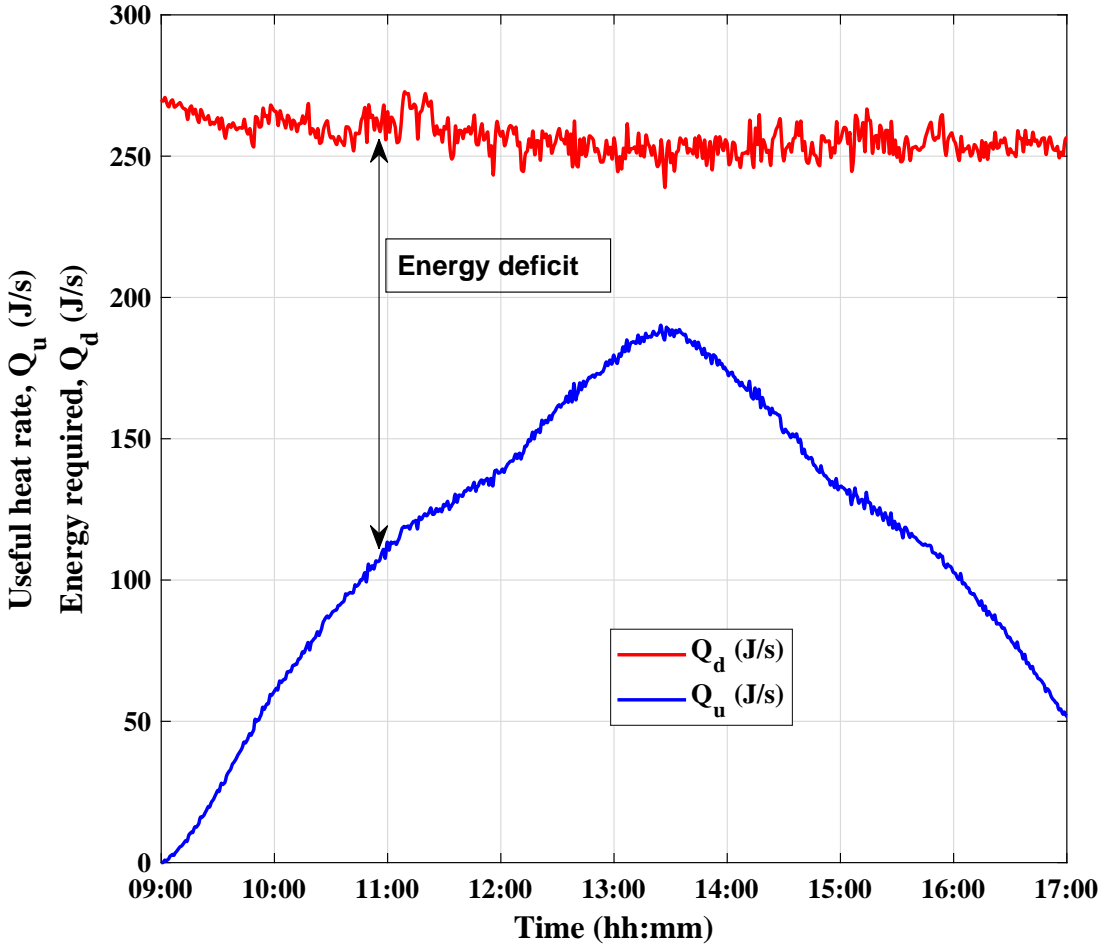
[picture p253: page 1]
Energy required, Q; Energy deficit

Useful heat rate, Q

Time (hh:mm)
