fsguerreiro/My_thesis/figs/dry_low_2col-eps-converted-to.pdf

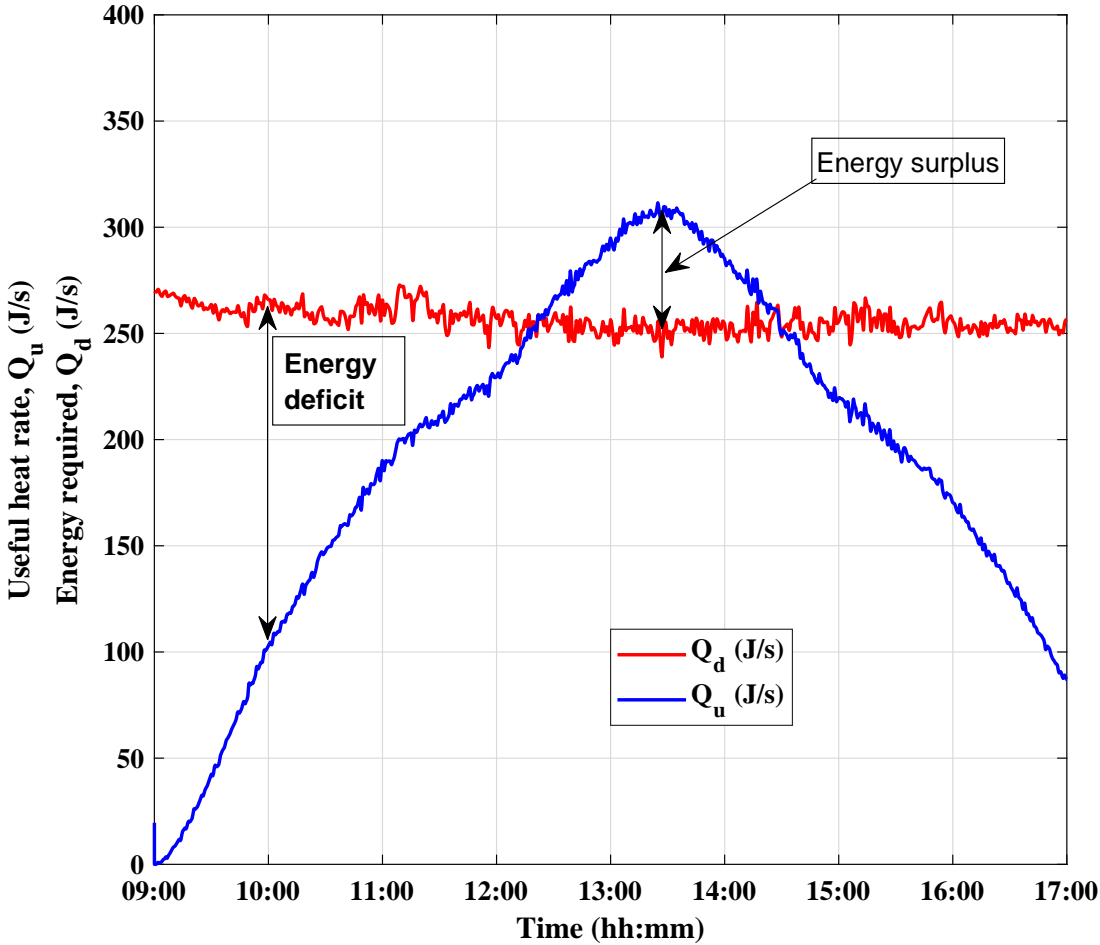
[picture p254: page 1]
Energy required, Q; Energy deficit; Energy surplus

Useful heat rate, Q

Qd | (J/s)
Qu | (J/s)

Time (hh:mm)
