fsguerreiro/My_thesis/figs/dT-Gair2-eps-converted-to.pdf

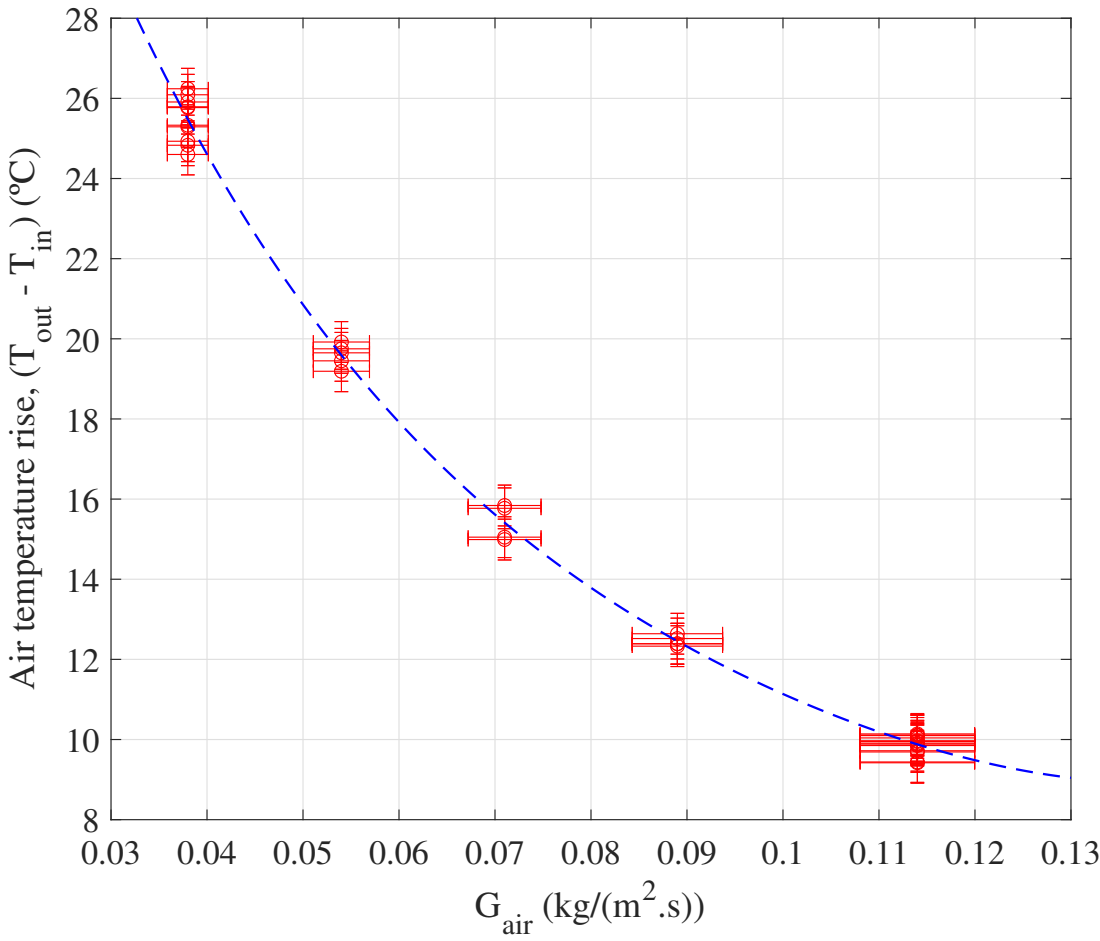
[picture p255: page 1]

Air temperature rise, (Tout - Tin) (ºC)

Gair (kg/(m²
