fsguerreiro/My_thesis/figs/Gair_V-eps-converted-to.pdf

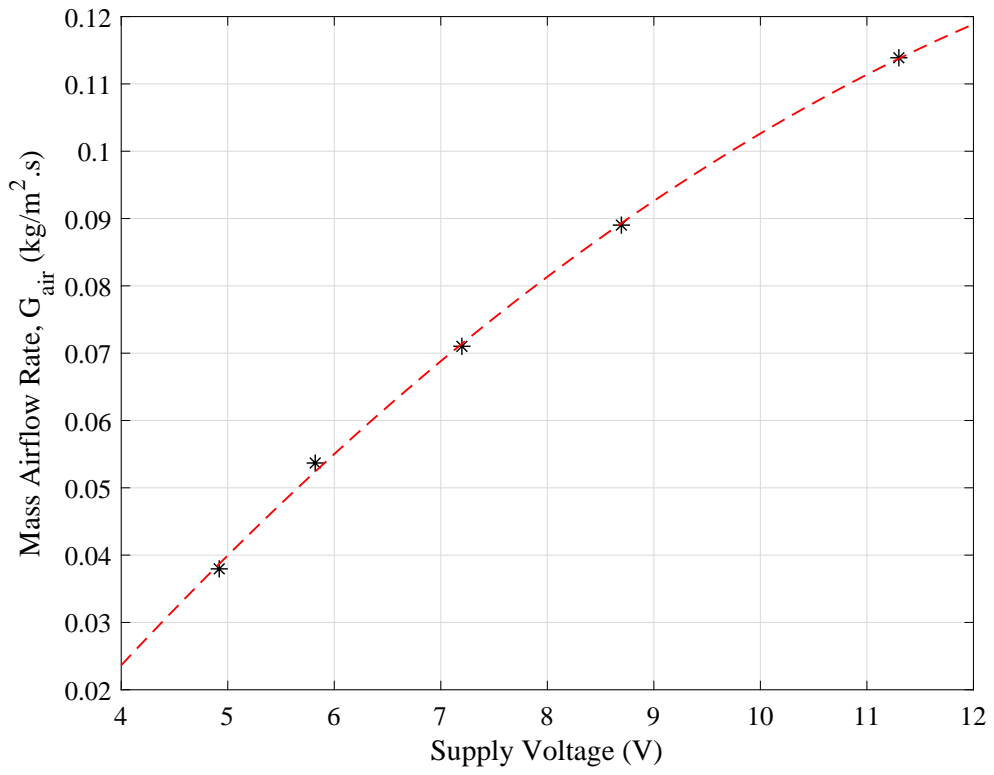
[picture p256: page 1]
Supply Voltage (V)

Mass Airflow Rate, Gair (kg/m
