fsguerreiro/My_thesis/figs/004-residue-5-eps-converted-to.pdf

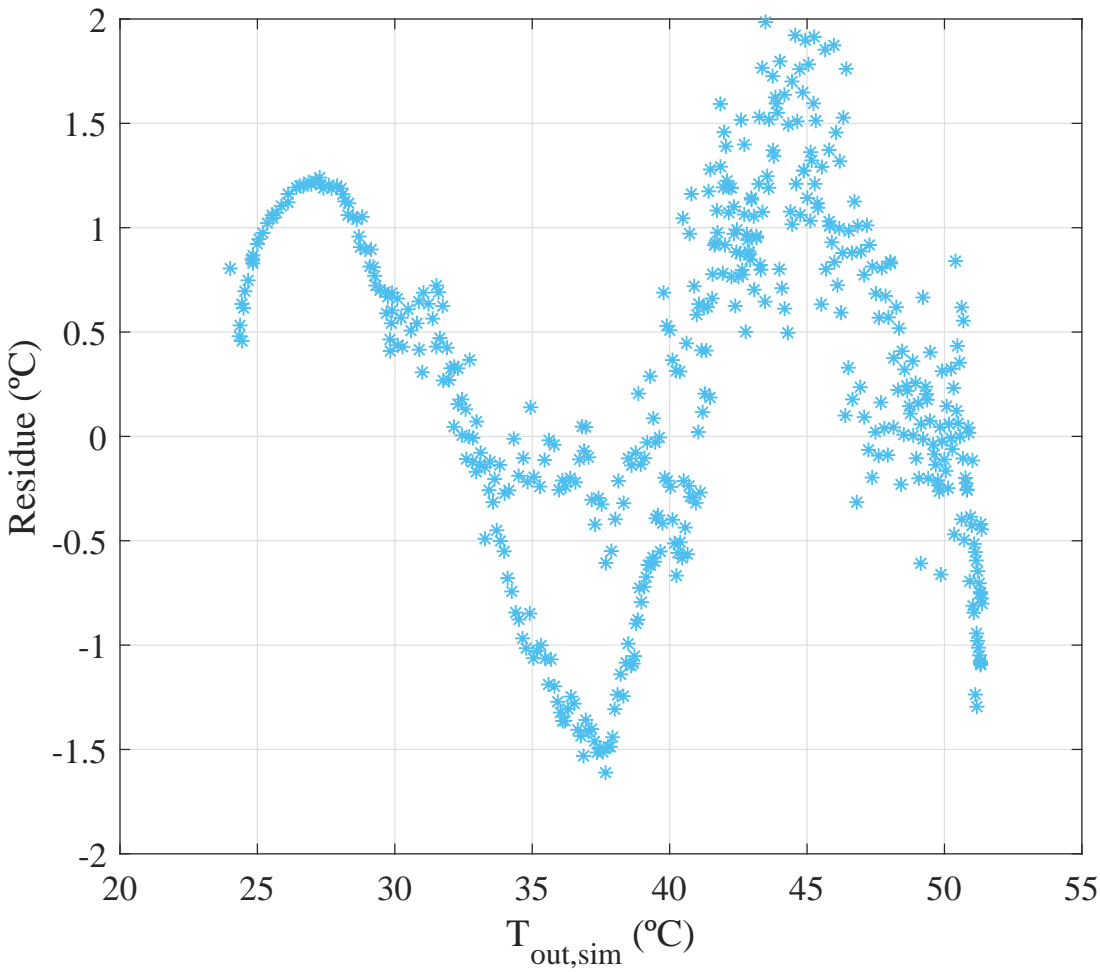
[picture p260: page 1]
Residue (ºC)

out,sim (ºC)
