fsguerreiro/My_thesis/figs/004-residue-6-eps-converted-to.pdf

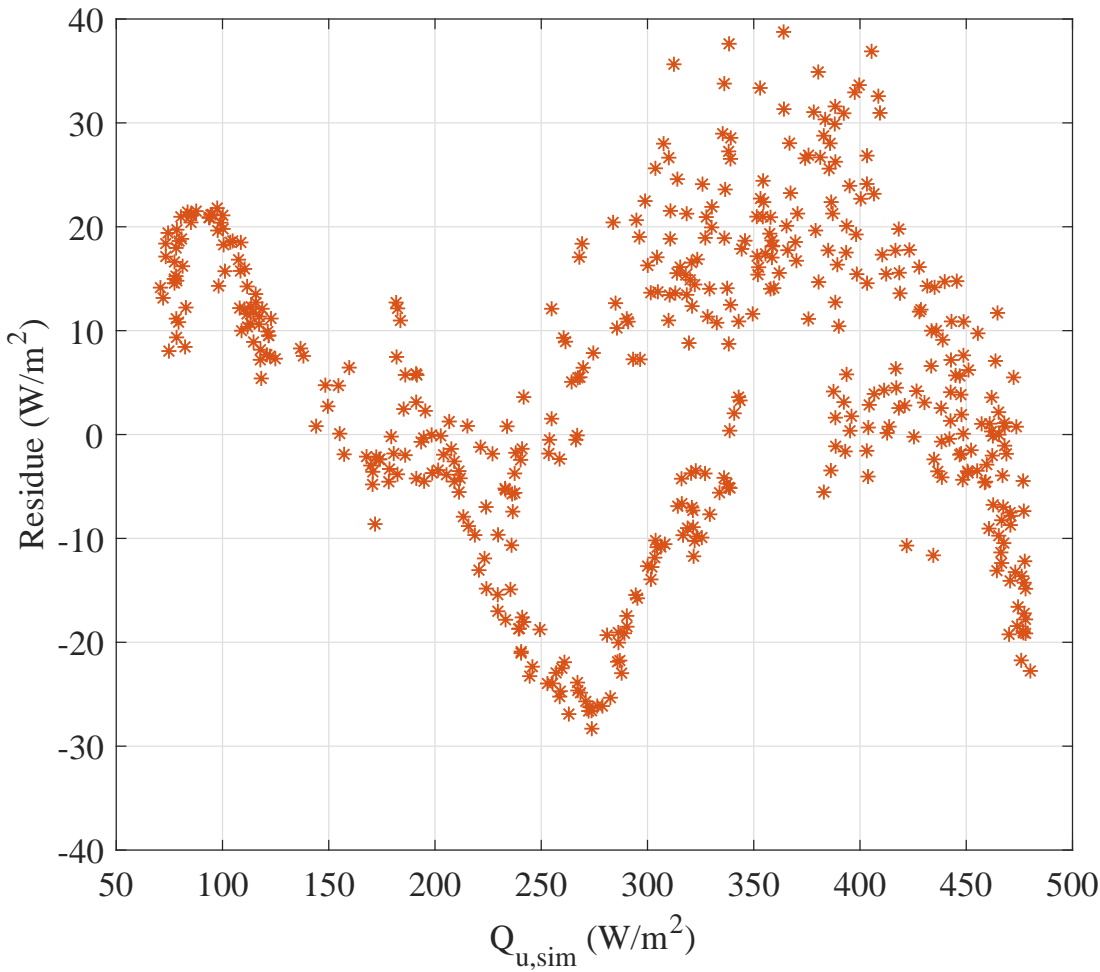
[picture p261: page 1]
Residue (W/m

Qu,sim (W/m²
