fsguerreiro/My_thesis/figs/0055-residue-5-eps-converted-to.pdf

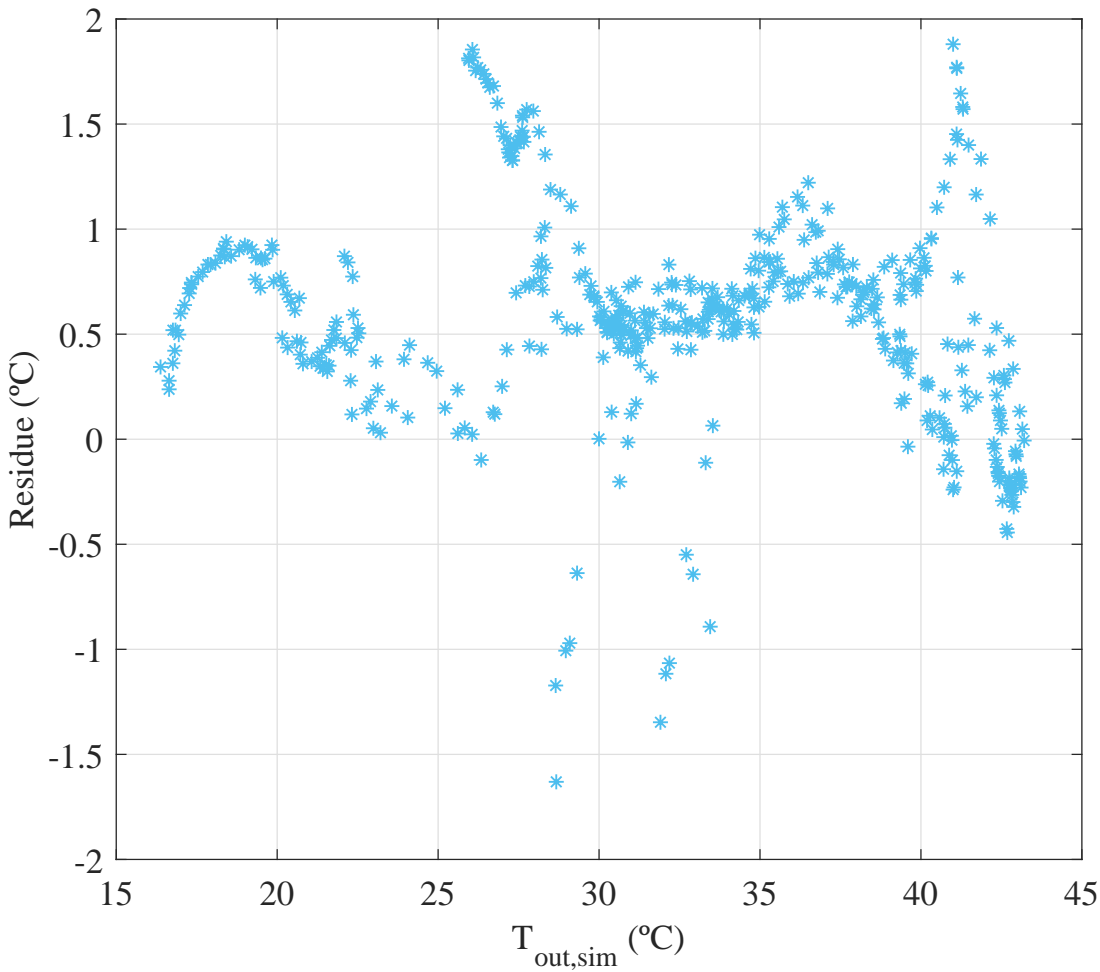
[picture p263: page 1]
Residue (ºC)

out,sim (ºC)
