fsguerreiro/My_thesis/figs/0055-residue-6-eps-converted-to.pdf

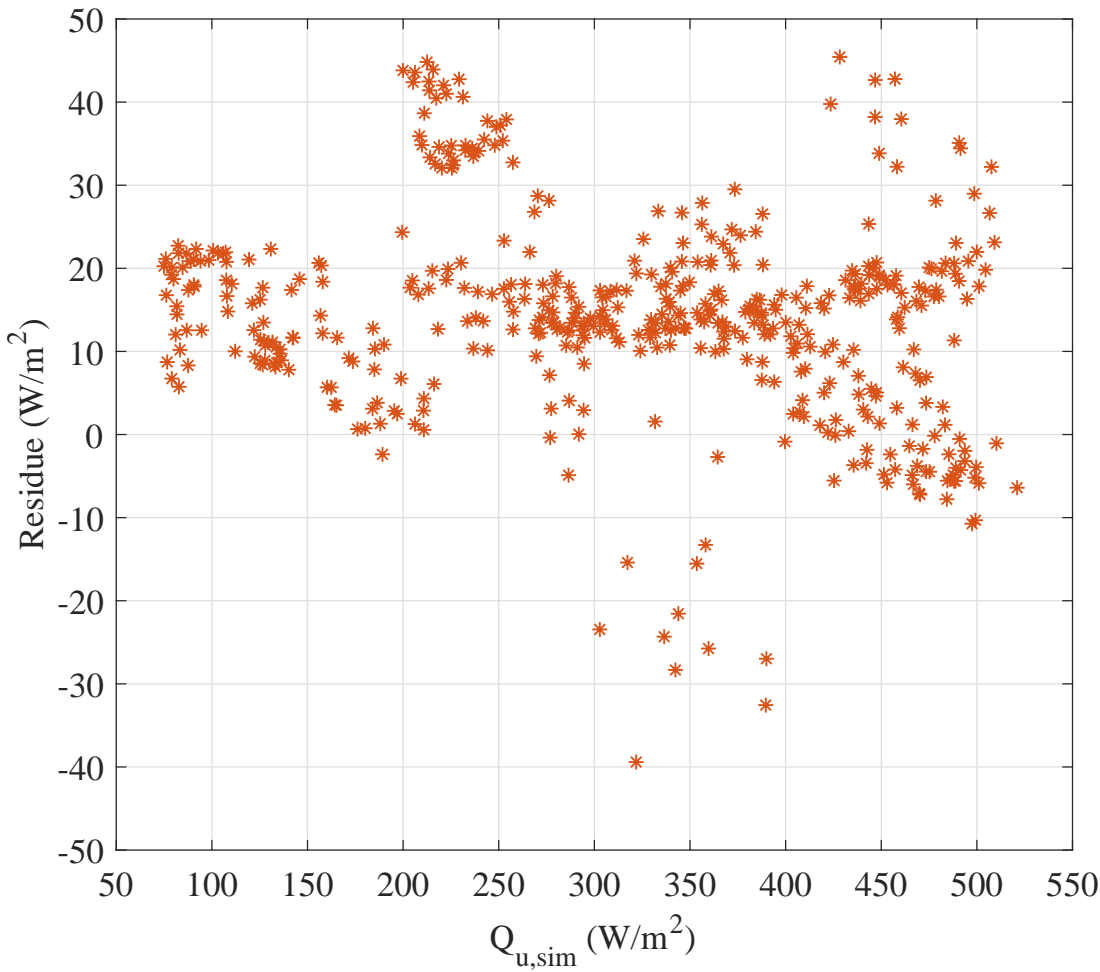
[picture p264: page 1]
Residue (W/m

Qu,sim (W/m²
