fsguerreiro/My_thesis/figs/007-residue-5-eps-converted-to.pdf

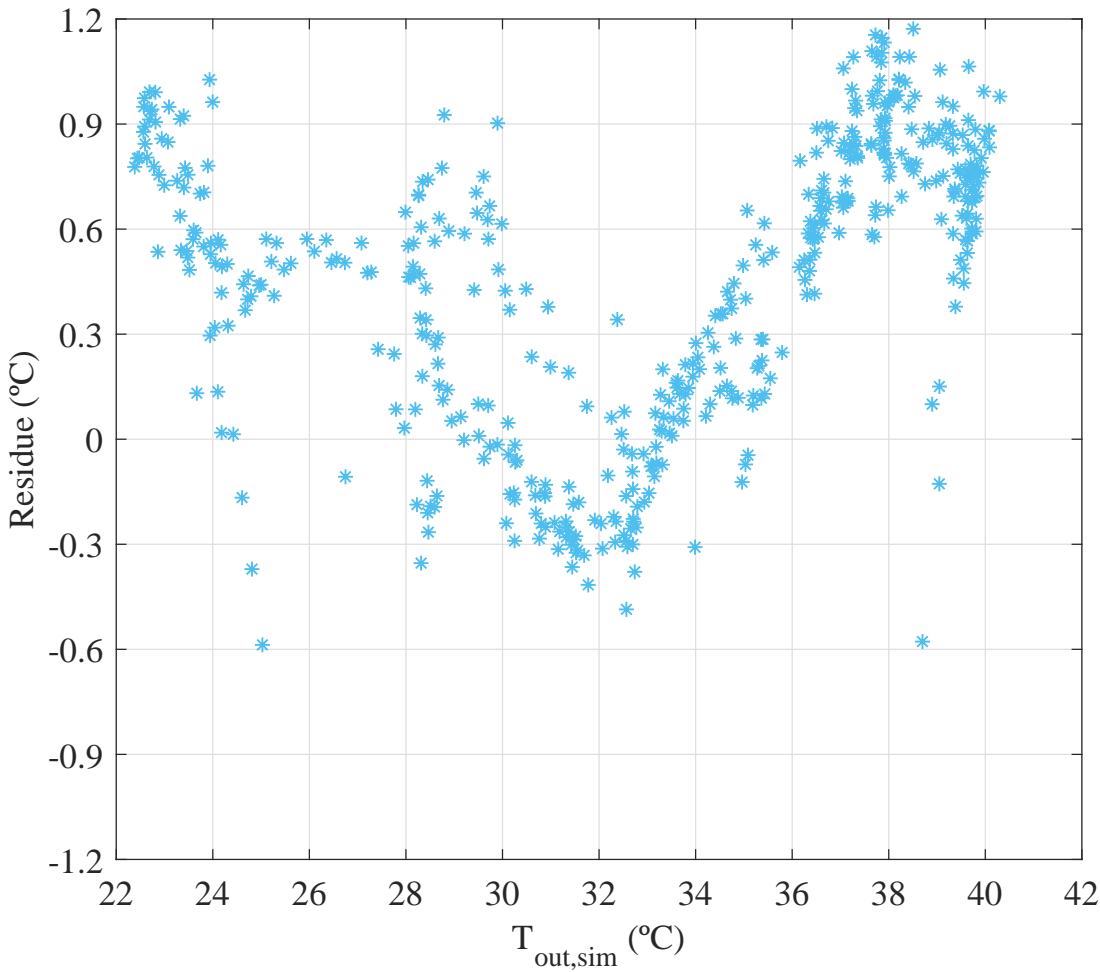
[picture p266: page 1]
Residue (ºC)

out,sim (ºC)
