fsguerreiro/My_thesis/figs/007-residue-6-eps-converted-to.pdf

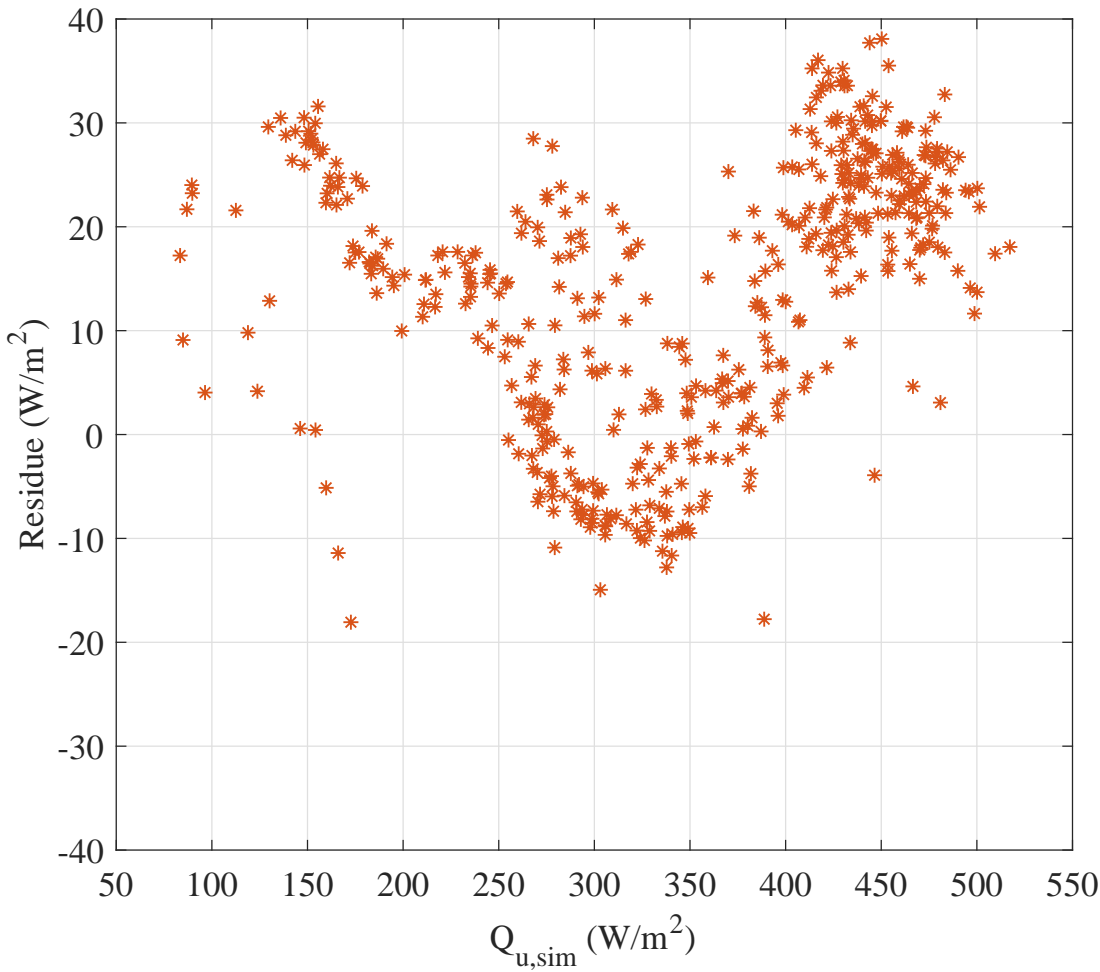
[picture p267: page 1]
Residue (W/m

Qu,sim (W/m²
