fsguerreiro/My_thesis/figs/009-2-eps-converted-to.pdf

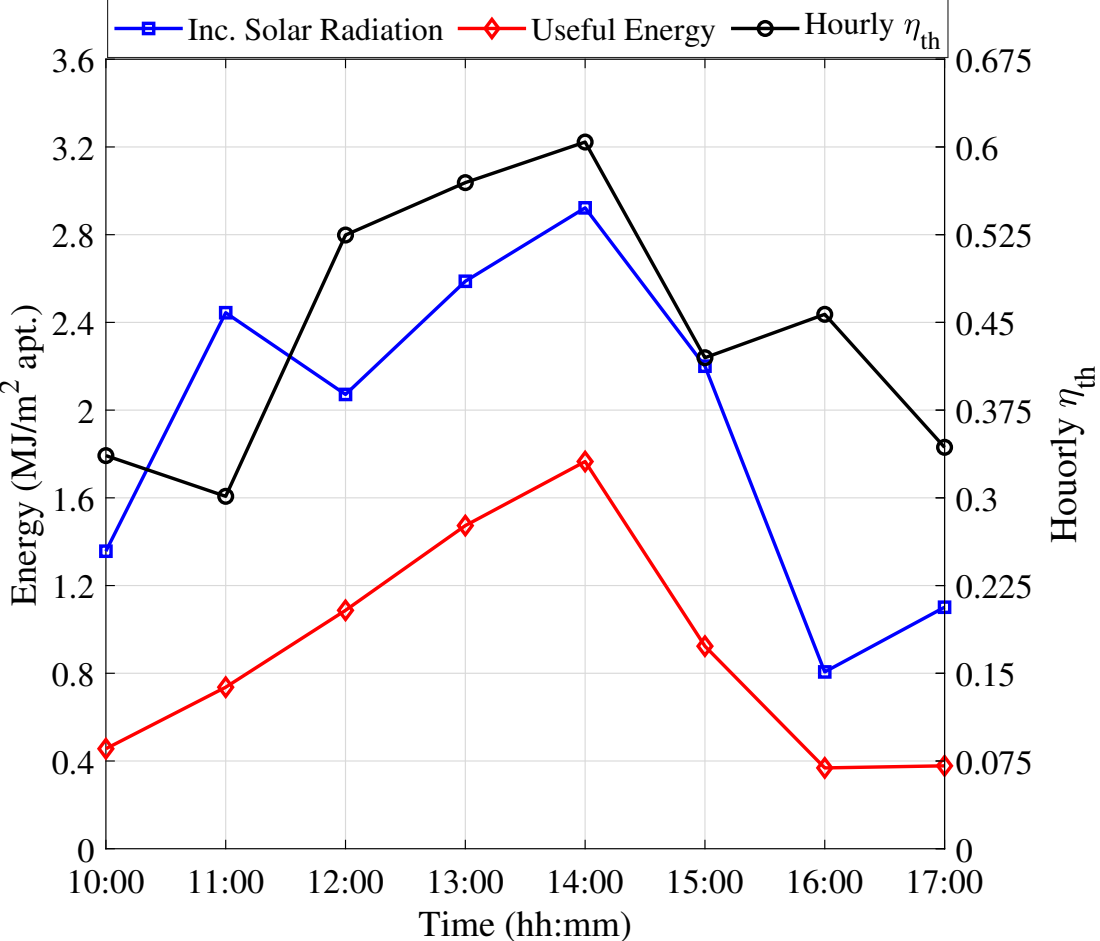
[picture p268: page 1]
Energy (MJ/m; 2 apt.); Houorly th; Inc. Solar Radiation; Useful Energy; Hourly th

Time (hh:mm)
