fsguerreiro/My_thesis/figs/009-residue-5-eps-converted-to.pdf

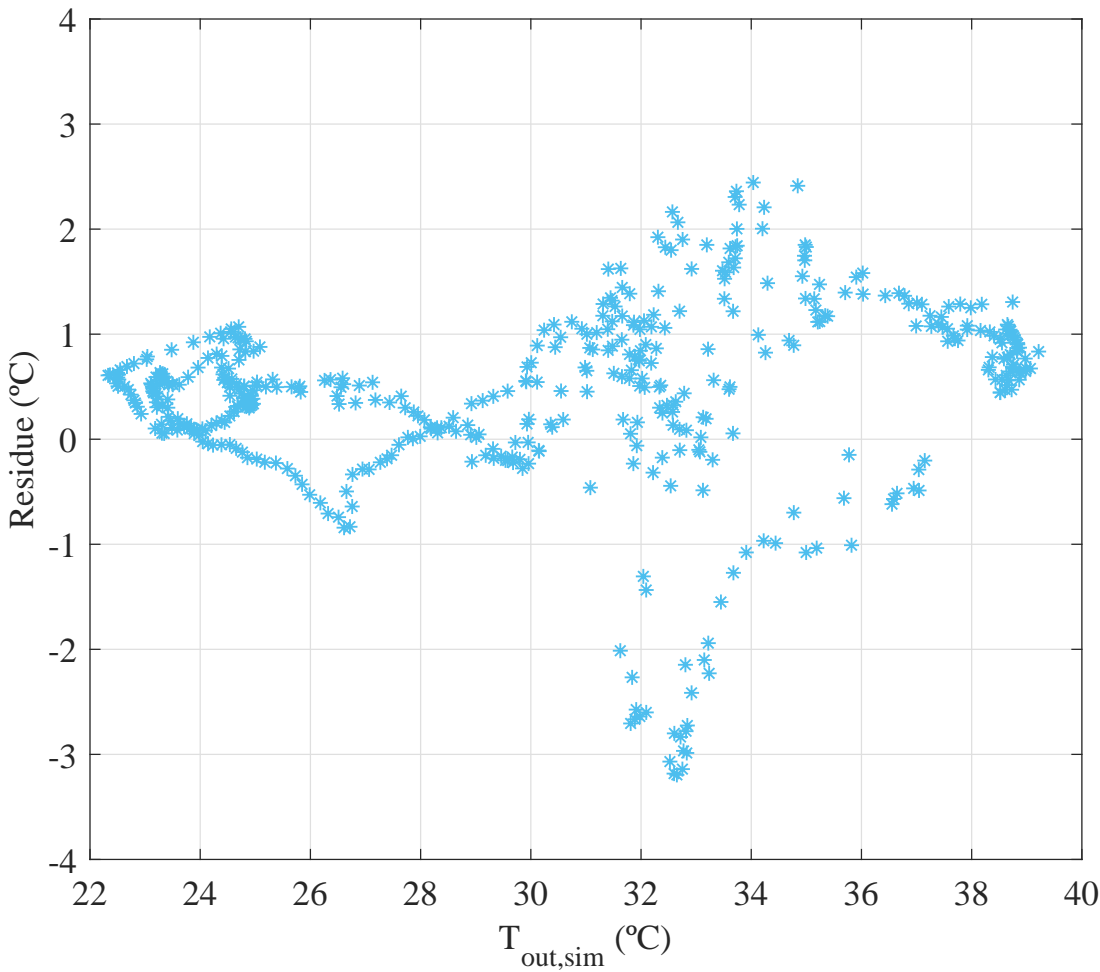
[picture p269: page 1]
Residue (ºC)

out,sim (ºC)
