fsguerreiro/My_thesis/figs/009-residue-6-eps-converted-to.pdf

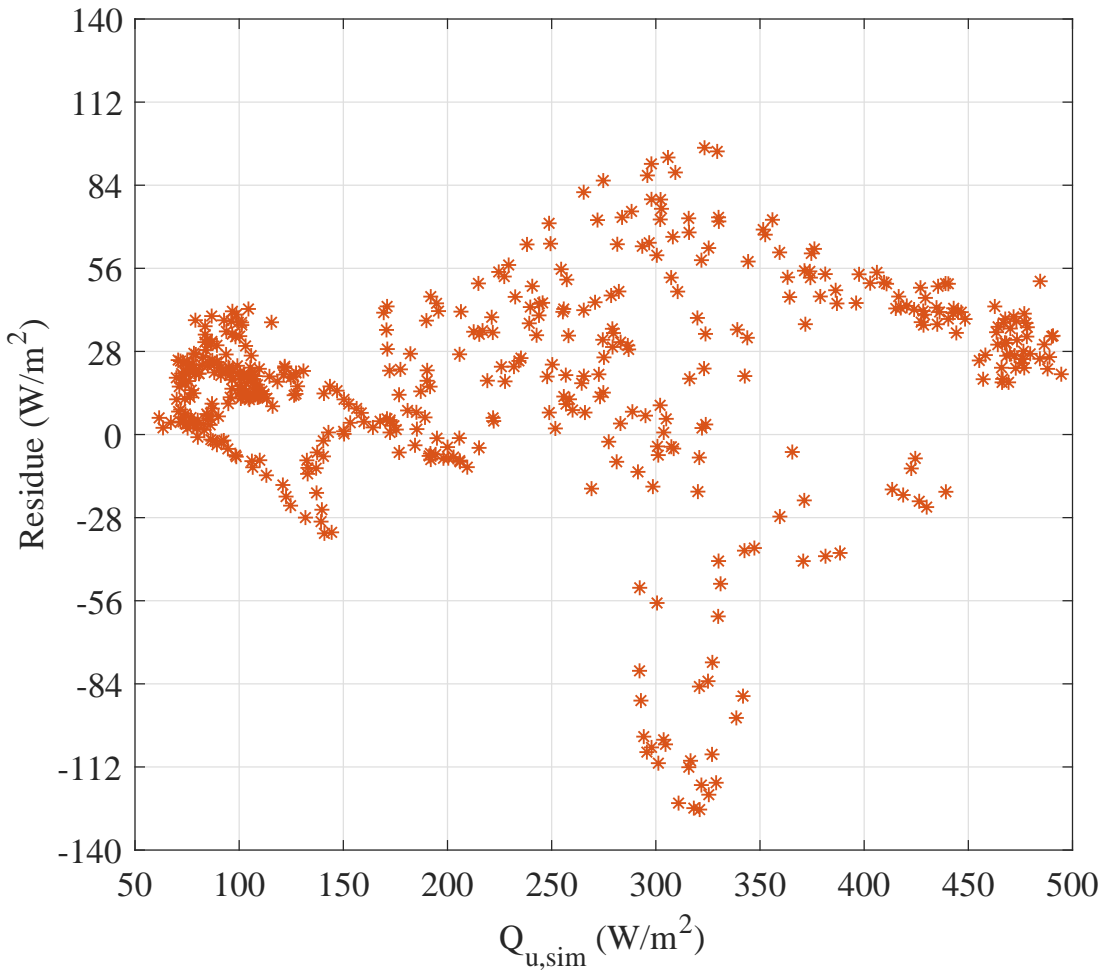
[picture p270: page 1]
Residue (W/m

Qu,sim (W/m²
