fsguerreiro/My_thesis/figs/0115-2-eps-converted-to.pdf

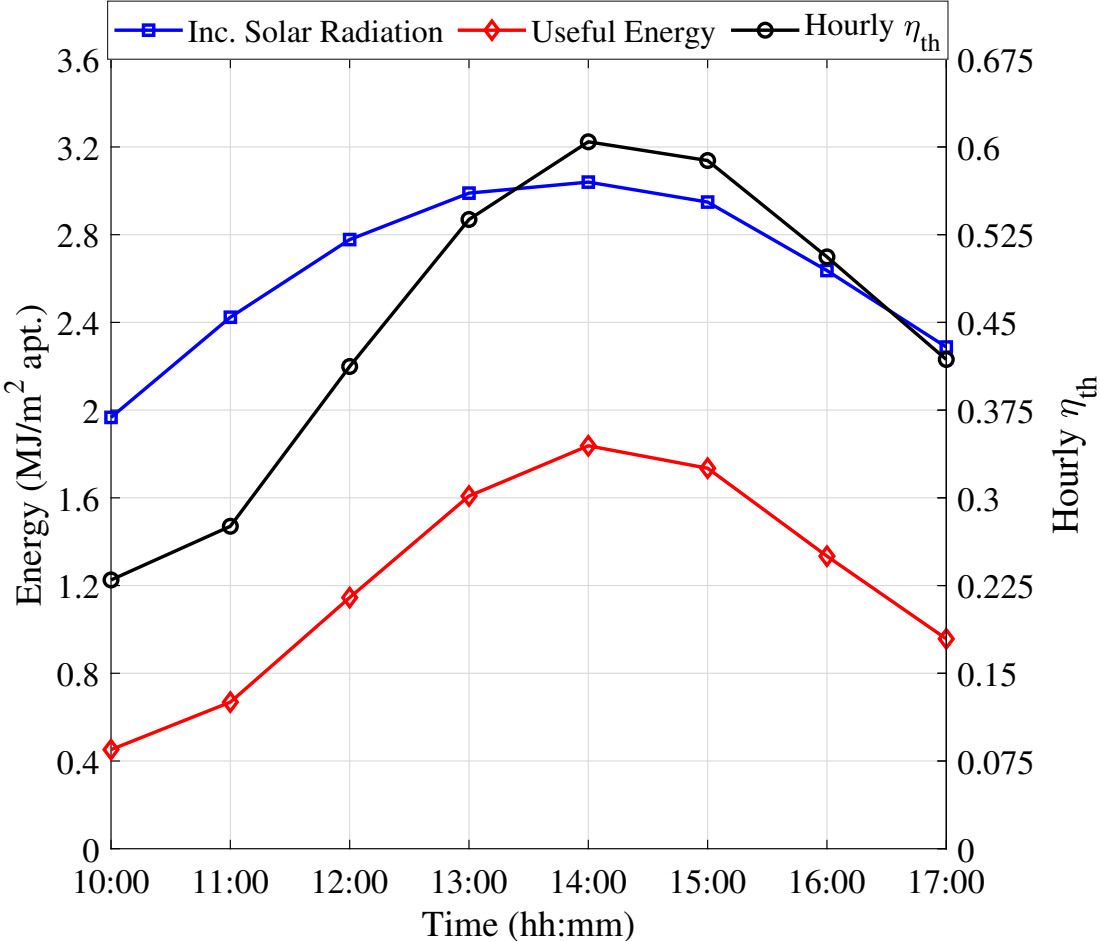
[picture p271: page 1]
Energy (MJ/m; 2 apt.); Hourly th; Inc. Solar Radiation; Useful Energy

Time (hh:mm)
