fsguerreiro/My_thesis/figs/0115-residue-5-eps-converted-to.pdf

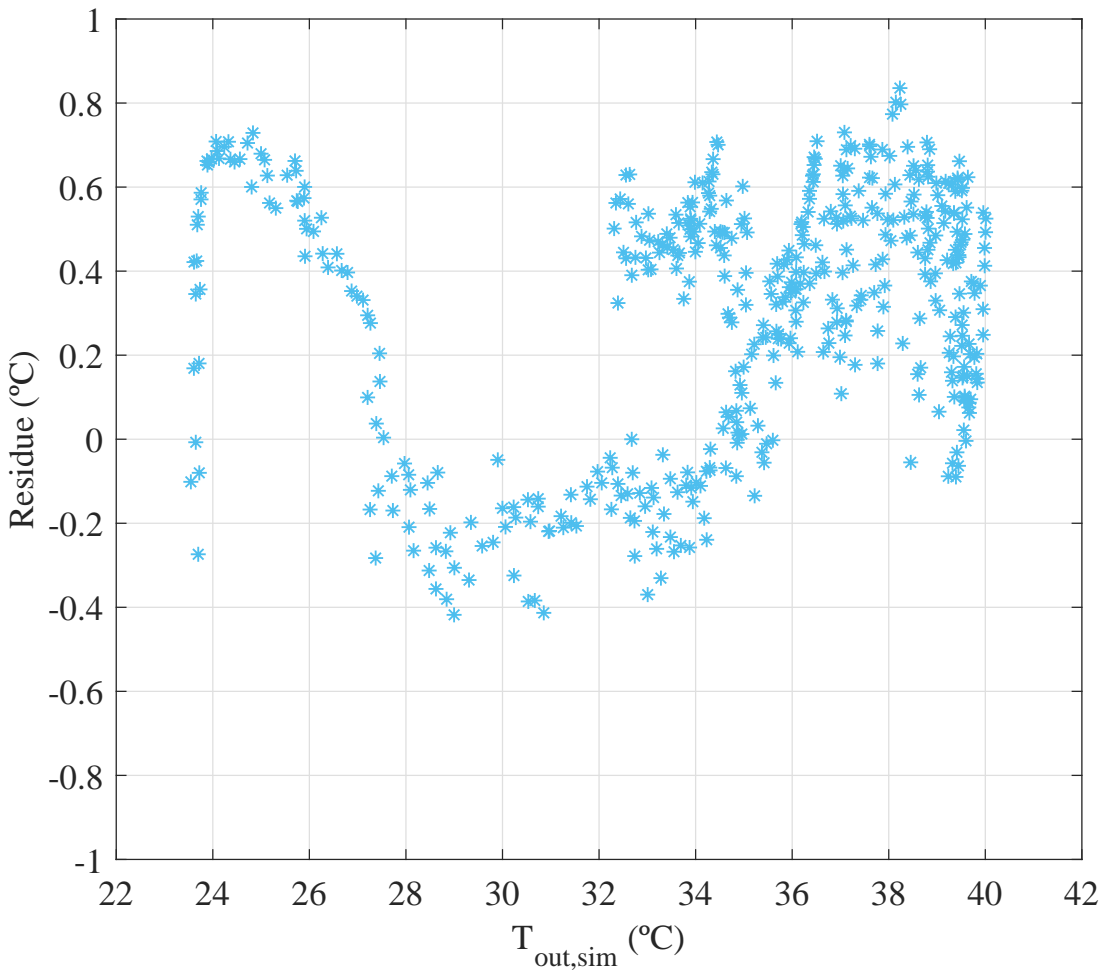
[picture p272: page 1]
Residue (ºC)

out,sim (ºC)
