fsguerreiro/My_thesis/figs/0115-residue-6-eps-converted-to.pdf

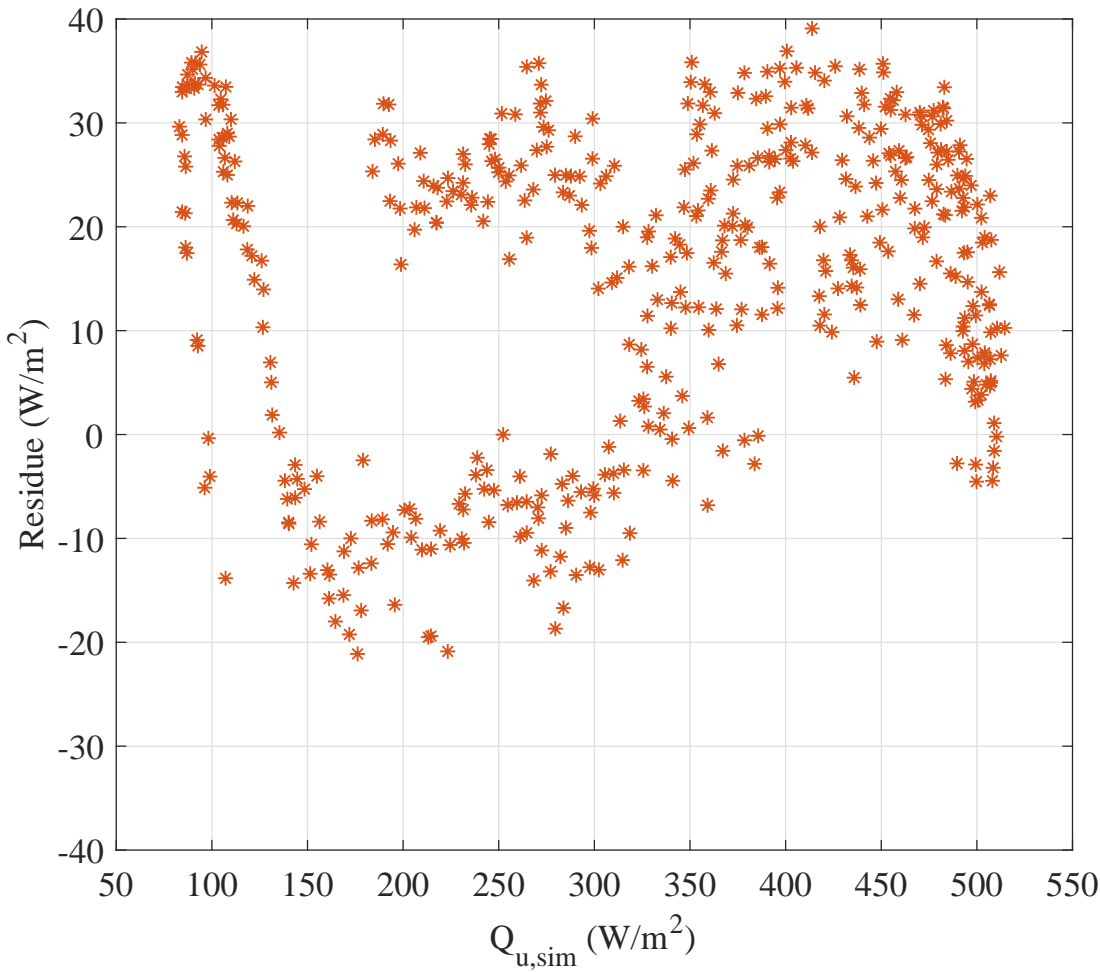
[picture p273: page 1]
Residue (W/m

Qu,sim (W/m²
