fsguerreiro/My_thesis/figs/2D-diagram-15-eps-converted-to.pdf

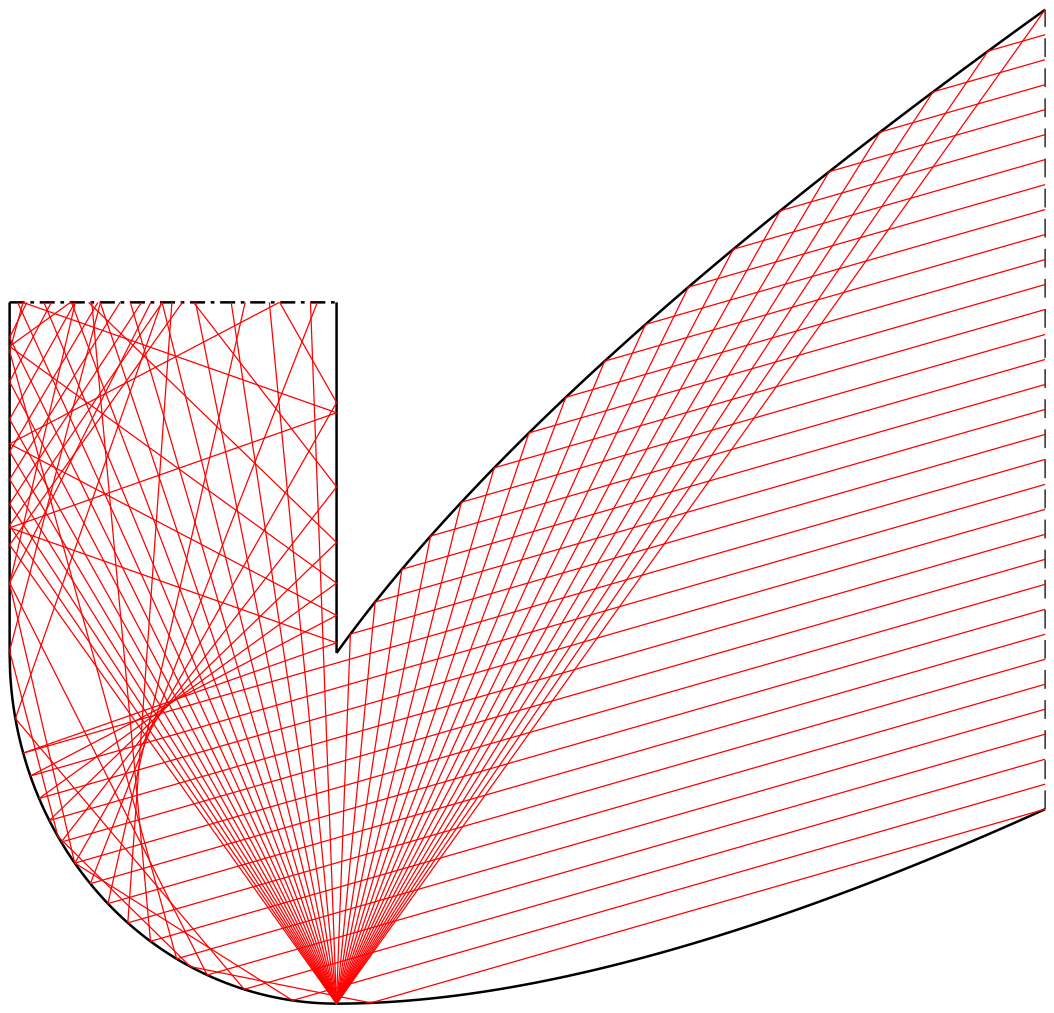
[picture p274: page 1]
