fsguerreiro/My_thesis/figs/2D-diagram-60-eps-converted-to.pdf

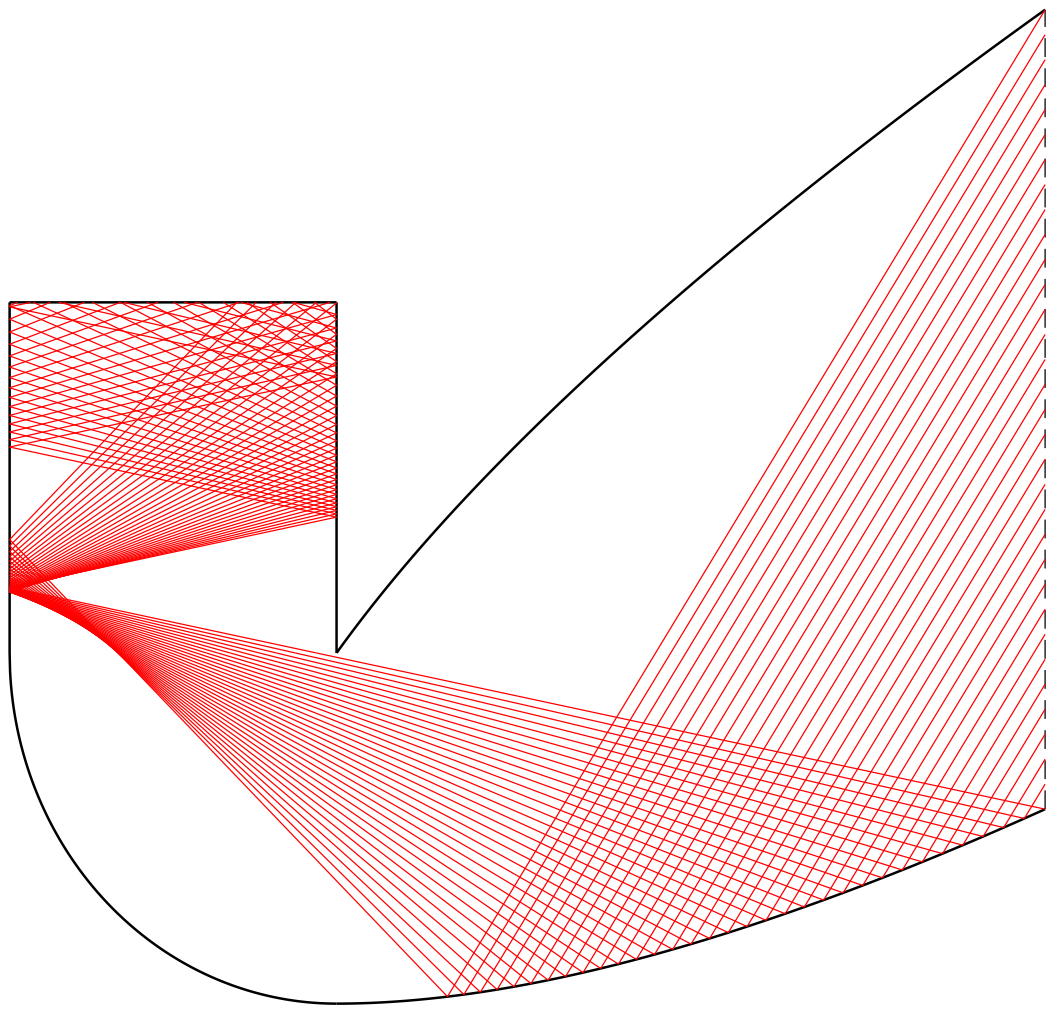
[picture p275: page 1]
