fsguerreiro/My_thesis/figs/acceptance-graph-eps-converted-to.pdf

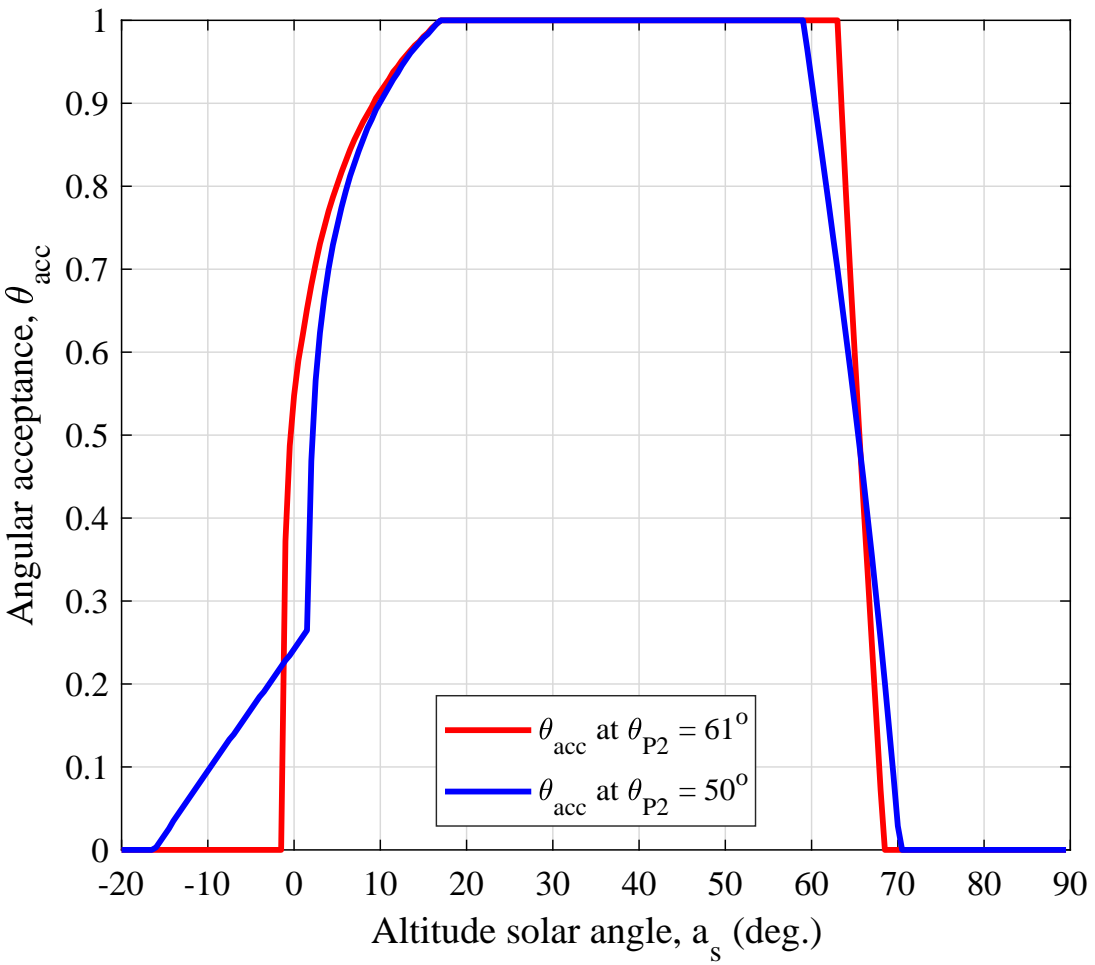
[picture p276: page 1]
(deg.)

Angular acceptance, acc

at acc | P2 = 61o

at acc | P2 = 50o

Altitude solar angle, a
