fsguerreiro/My_thesis/figs/Alt_Azz2-eps-converted-to.pdf

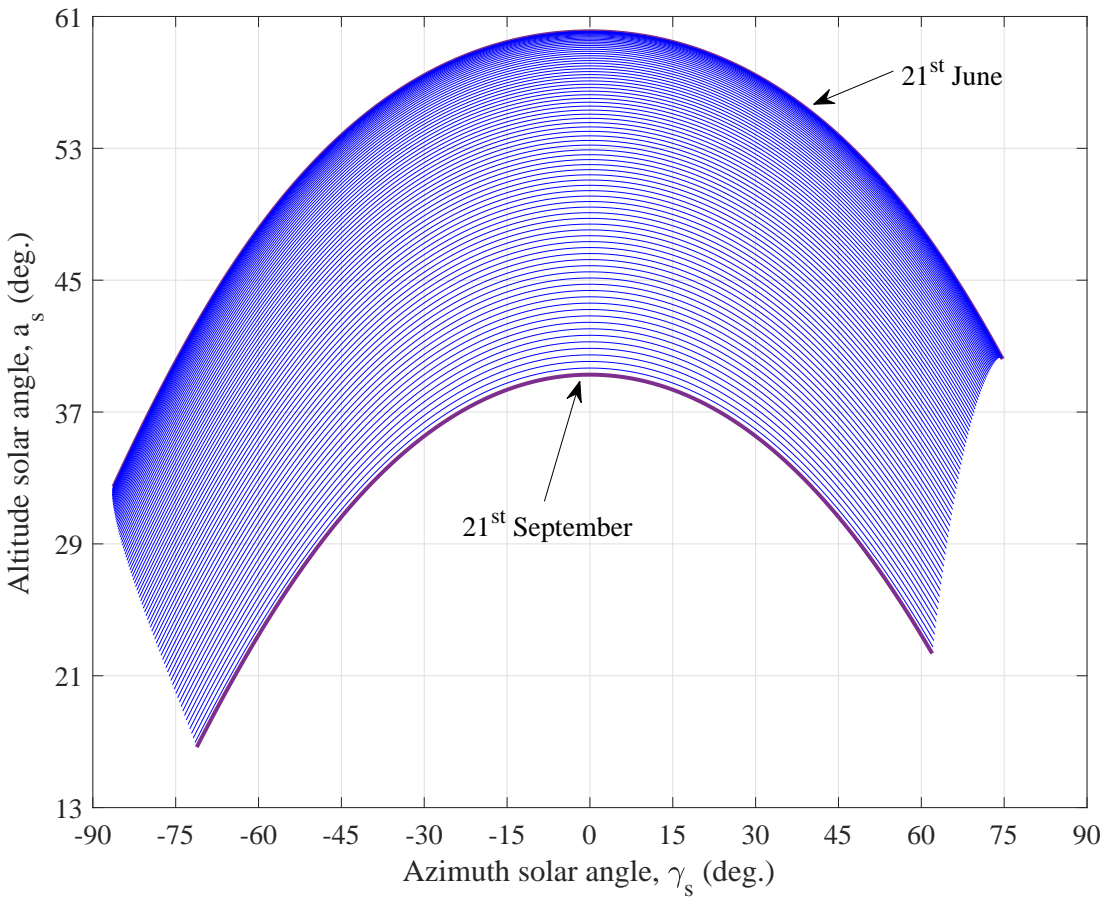
[picture p277: page 1]
(deg.); s (deg.); 21st September; 21st June

Altitude solar angle, a

Azimuth solar angle,
