fsguerreiro/My_thesis/figs/Ceff_region2-eps-converted-to.pdf

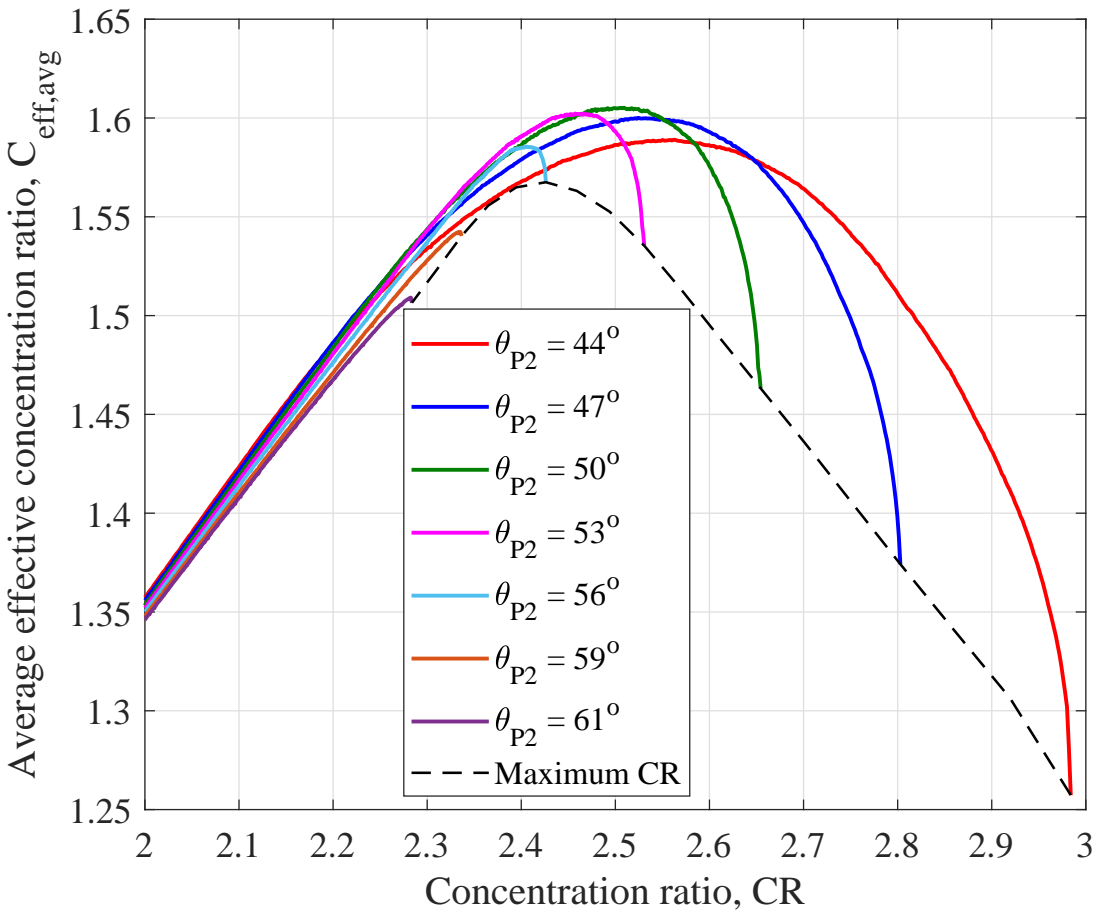
[picture p278: page 1]

Average effective concentration ratio, Ceff,avg

P2 = 61o Maximum CR

Concentration ratio, CR
