fsguerreiro/My_thesis/figs/col_rev-eps-converted-to.pdf

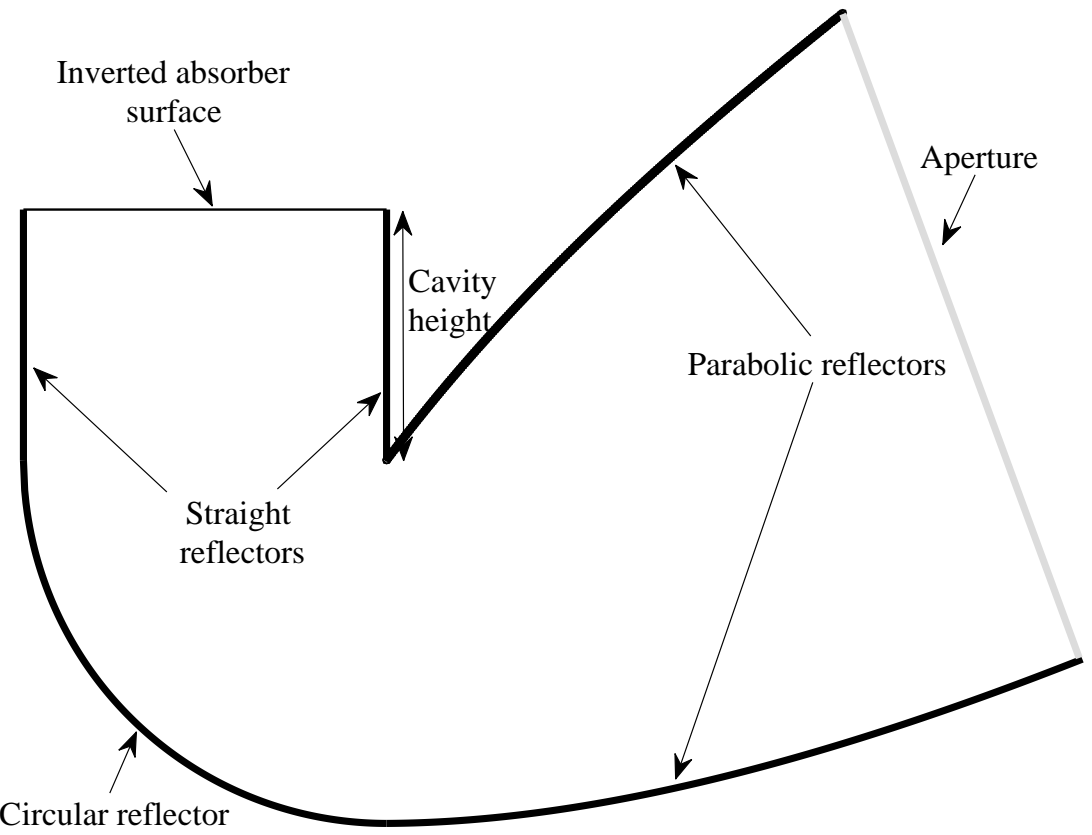
[picture p279: page 1]
Aperture; Parabolic reflectors; Straight reflectors; Inverted absorber surface; Cavity height; Circular reflector
