fsguerreiro/My_thesis/figs/collectors-61-50-eps-converted-to.pdf

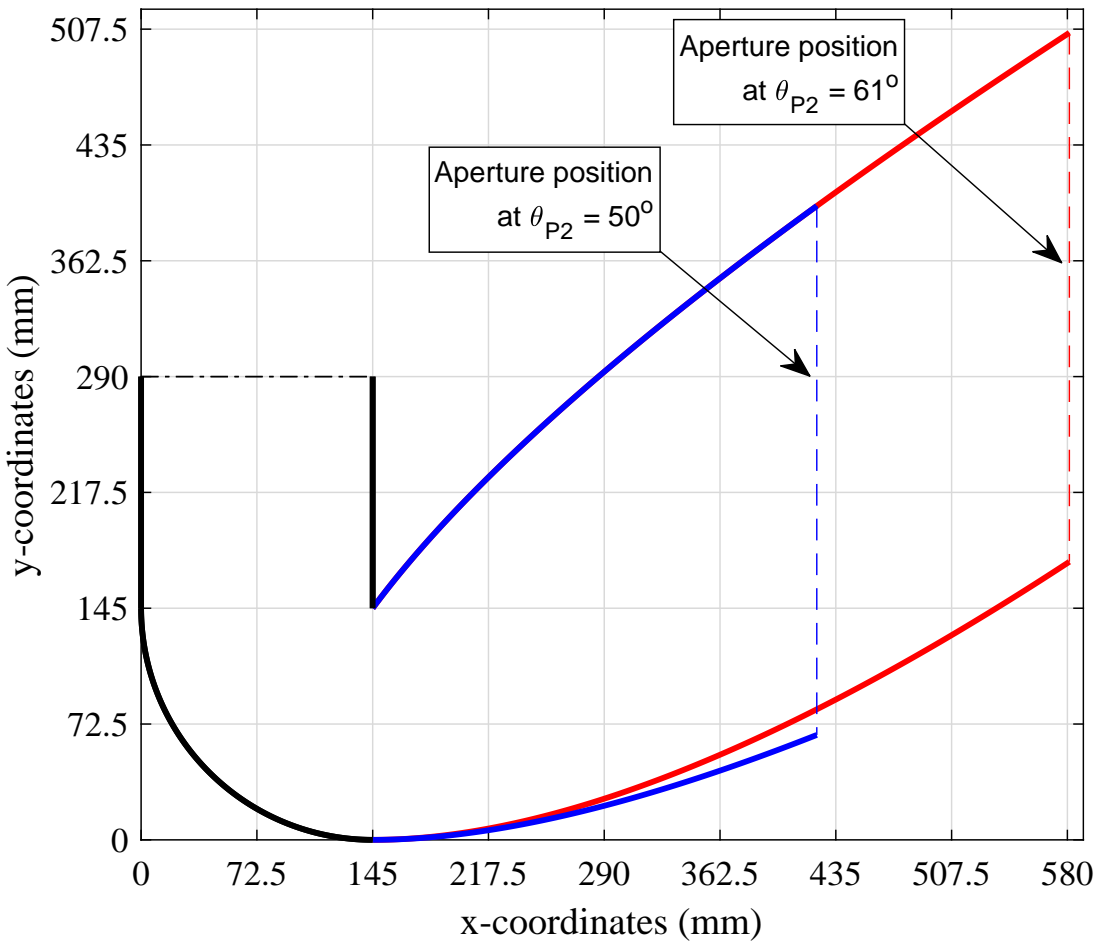
[picture p280: page 1]
x-coordinates (mm); y-coordinates (mm)

Aperture position | at P2 = 61o

Aperture position | at P2 = 50o
