fsguerreiro/My_thesis/figs/contour_dT-eps-converted-to.pdf

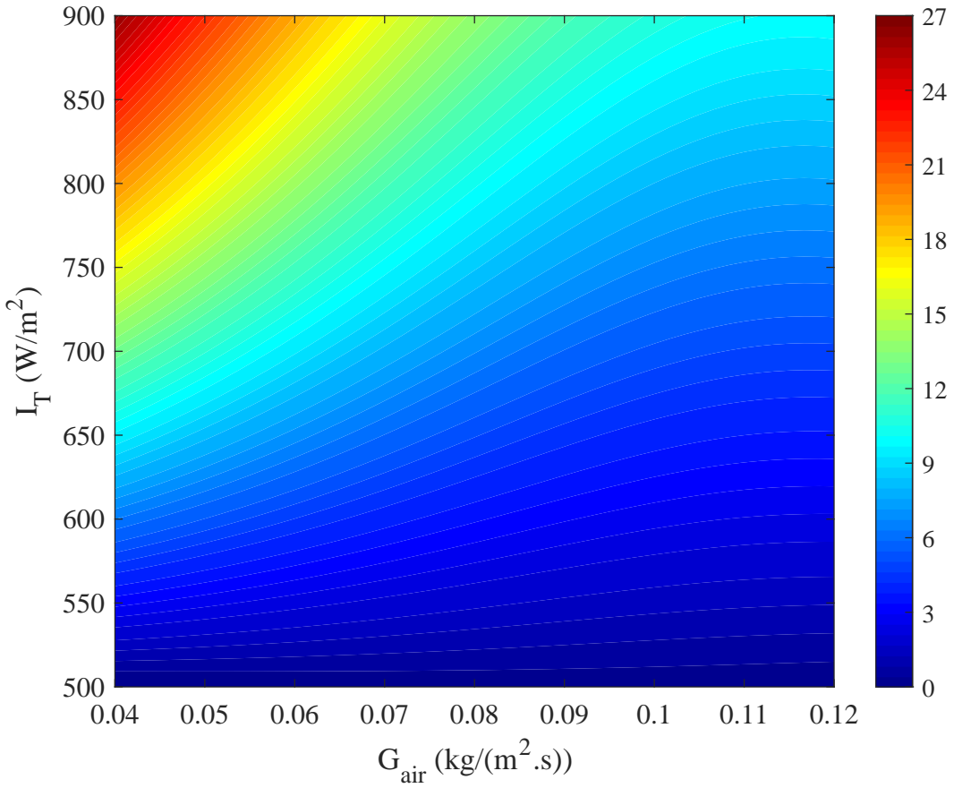
[picture p281: page 1]

Gair (kg/(m²
