fsguerreiro/My_thesis/figs/contour_Q-eps-converted-to.pdf

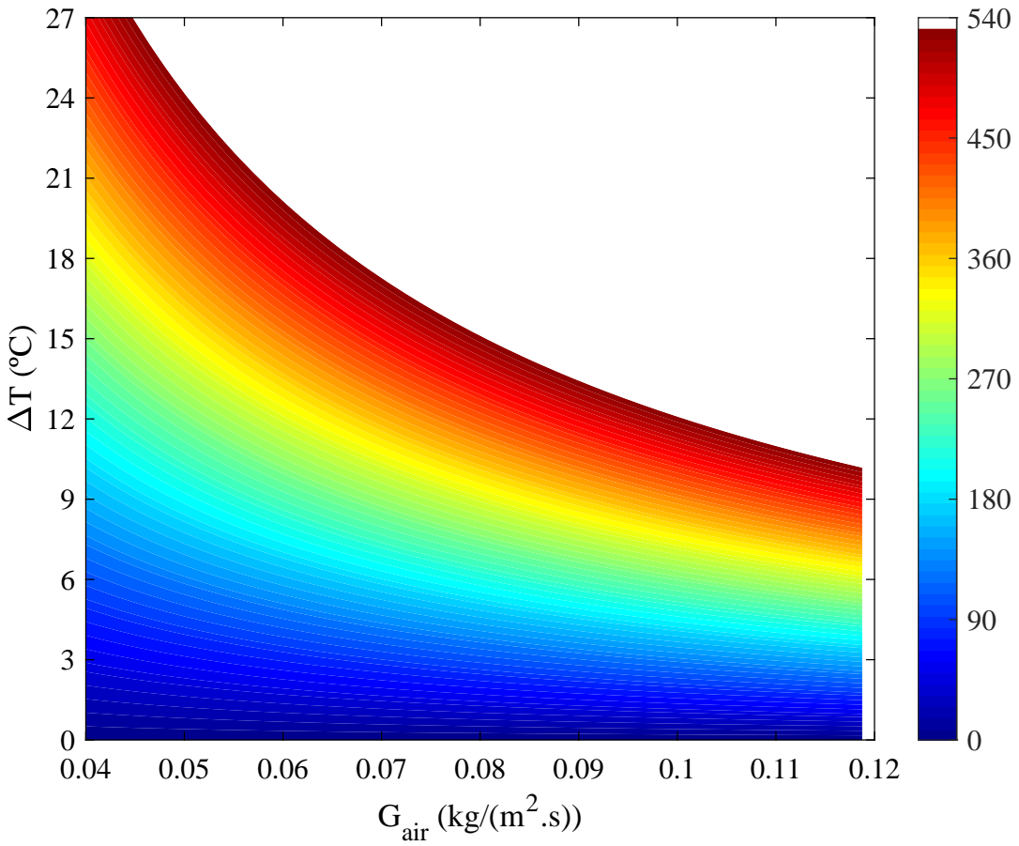
[picture p282: page 1]

Gair (kg/(m²
