fsguerreiro/My_thesis/figs/CSview-eps-converted-to.pdf

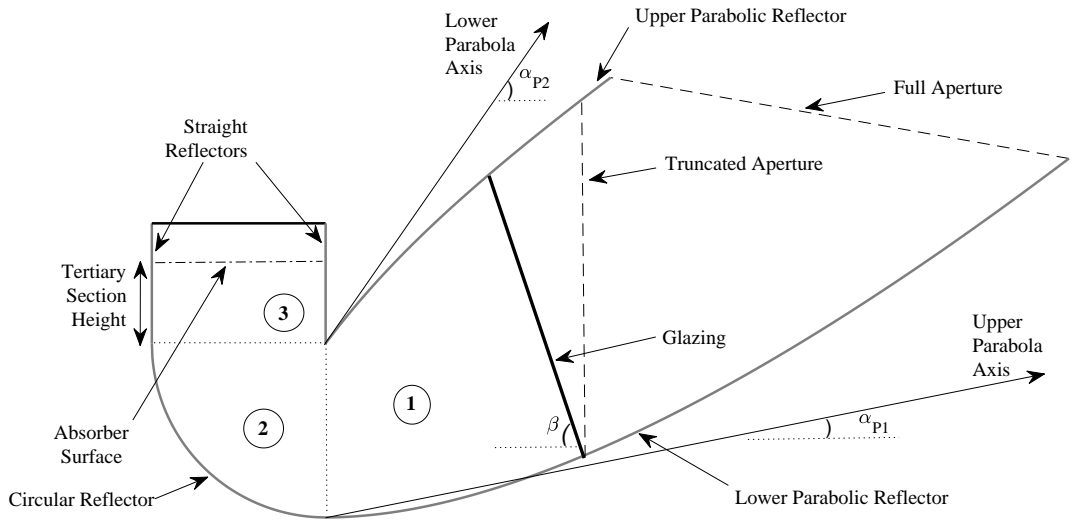
[picture p283: page 1]
Lower; Upper Parabolic Reflector; Parabola Axis; Straight Reflectors; Tertiary Section Height; Circular Reflector; Lower Parabolic Reflector; Upper Parabola Axis; Glazing; Truncated Aperture; Full Aperture; Absorber Surface
