fsguerreiro/My_thesis/figs/CSview2-eps-converted-to.pdf

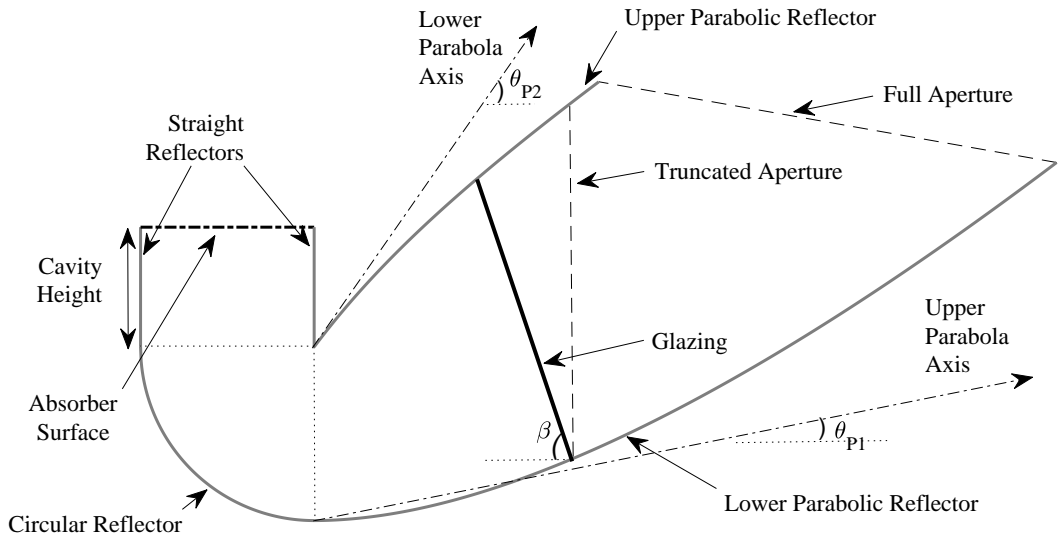
[picture p284: page 1]
Straight Reflectors; Glazing; Truncated Aperture; Full Aperture; Circular Reflector; Upper Parabola Axis; Lower Parabola Axis; Absorber Surface; Cavity Height

Upper Parabolic Reflector

Lower Parabolic Reflector
