fsguerreiro/My_thesis/figs/curve_efficiency1-eps-converted-to.pdf

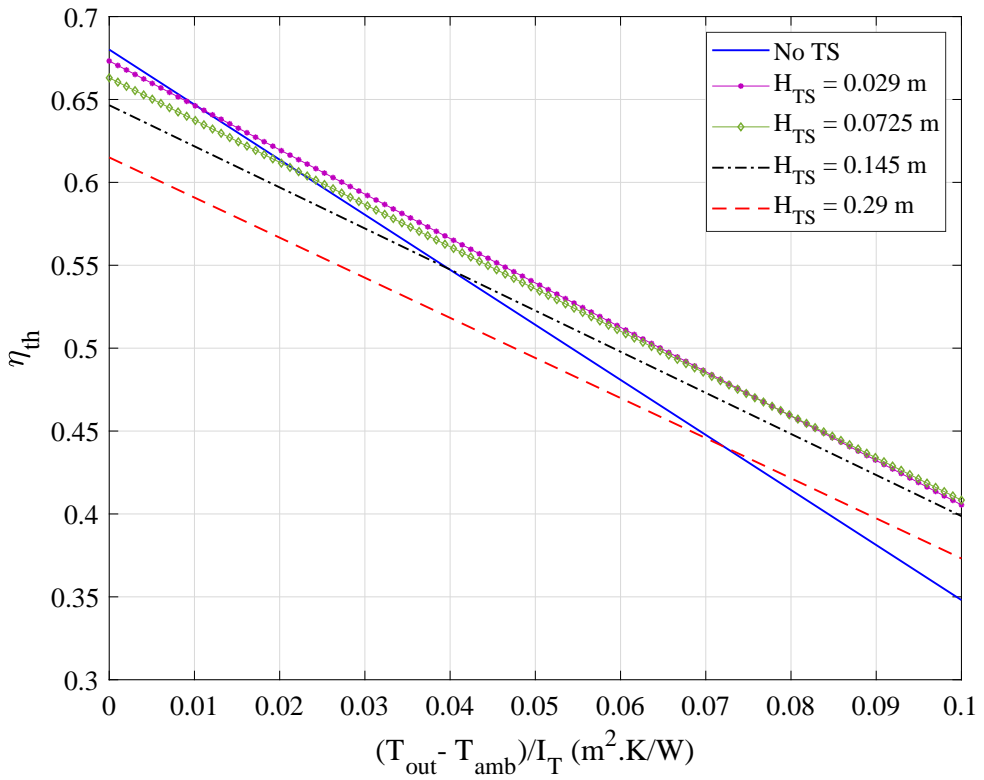
[picture p285: page 1]
out; - Tamb)/IT

No TS HTS = 0.029 m

HTS = 0.0725 m HTS = 0.145 m

HTS = 0.29 m
