fsguerreiro/My_thesis/figs/ef-Gair2-eps-converted-to.pdf

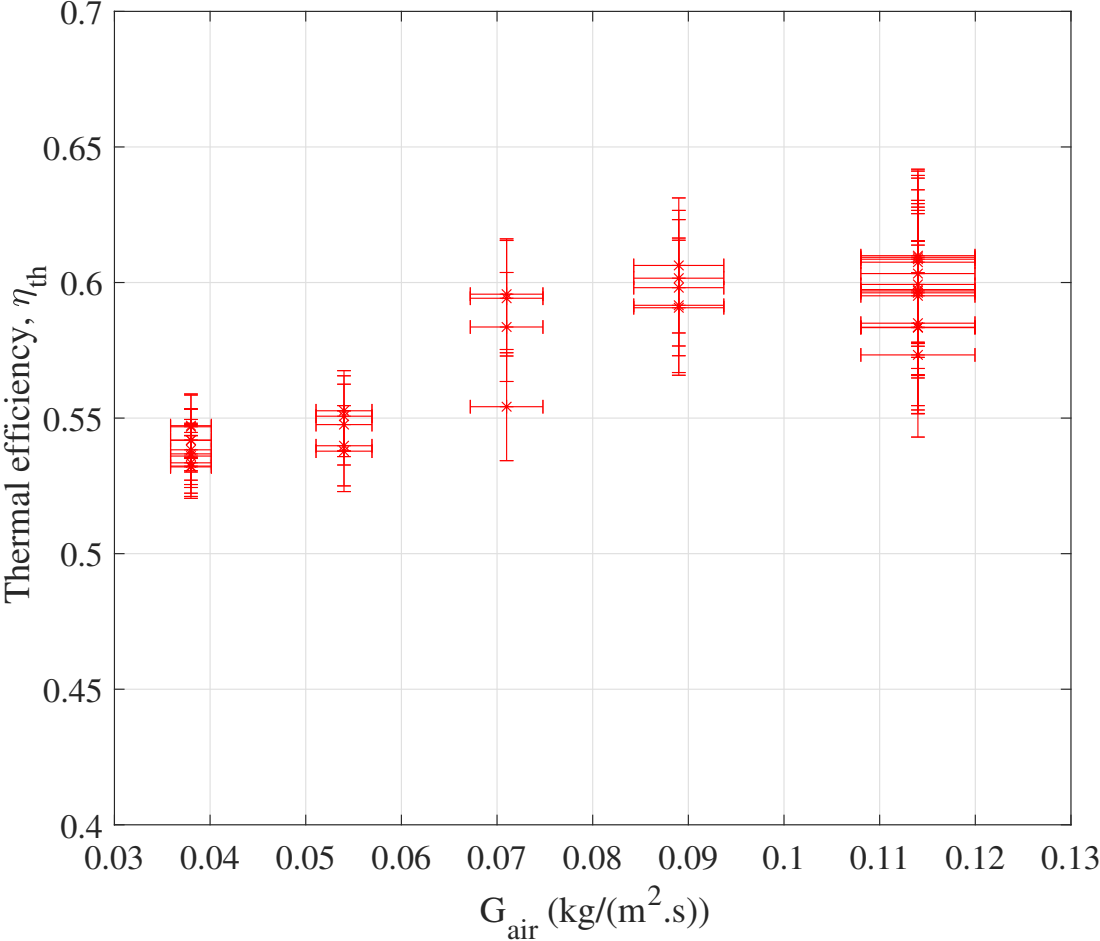
[picture p286: page 1]

Thermal efficiency, th

Gair (kg/(m²
