fsguerreiro/My_thesis/figs/ef_curve2-eps-converted-to.pdf

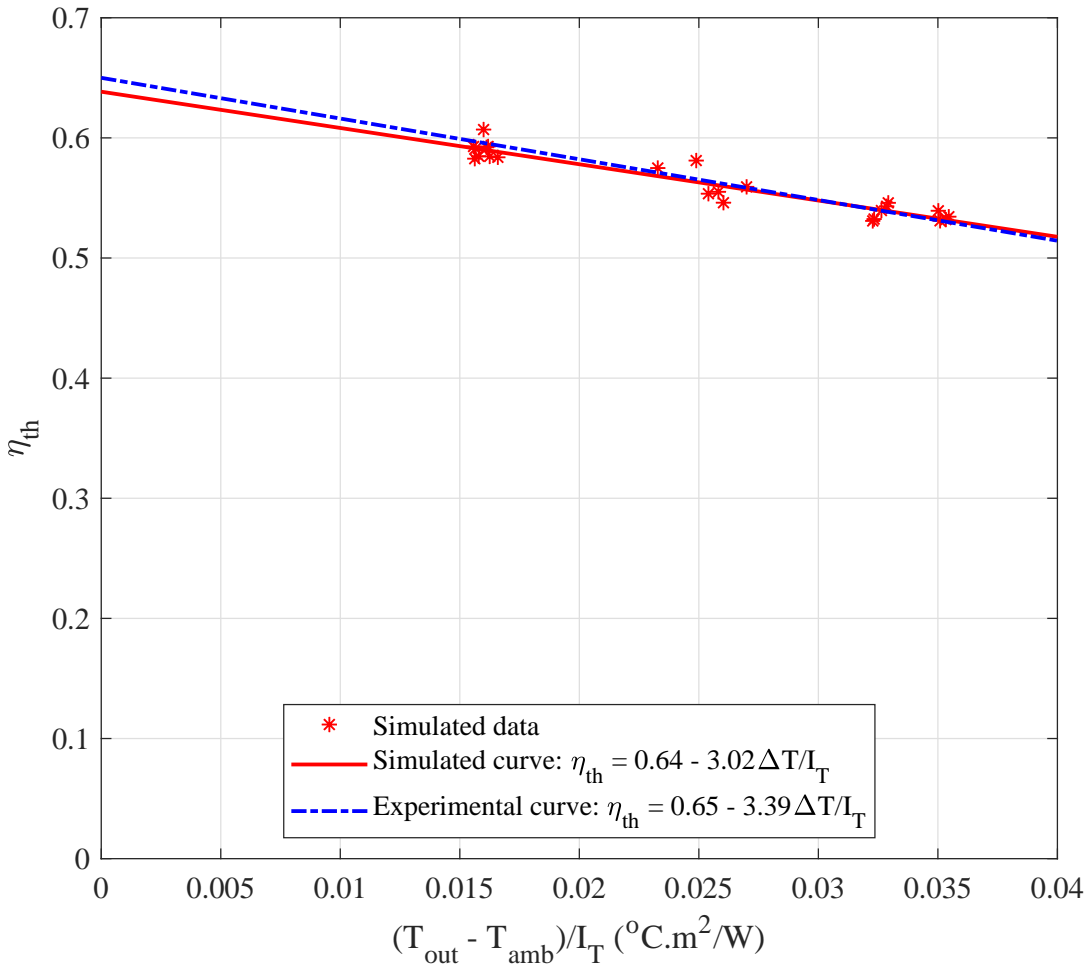
[picture p287: page 1]

Simulated data
Simulated curve: Experimental curve: th = 0.65 - 3.39 | th = 0.64 - 3.02 T/IT | T/IT

(Tout - Tamb)/IT
