fsguerreiro/My_thesis/figs/eff-alphaP2-eps-converted-to.pdf

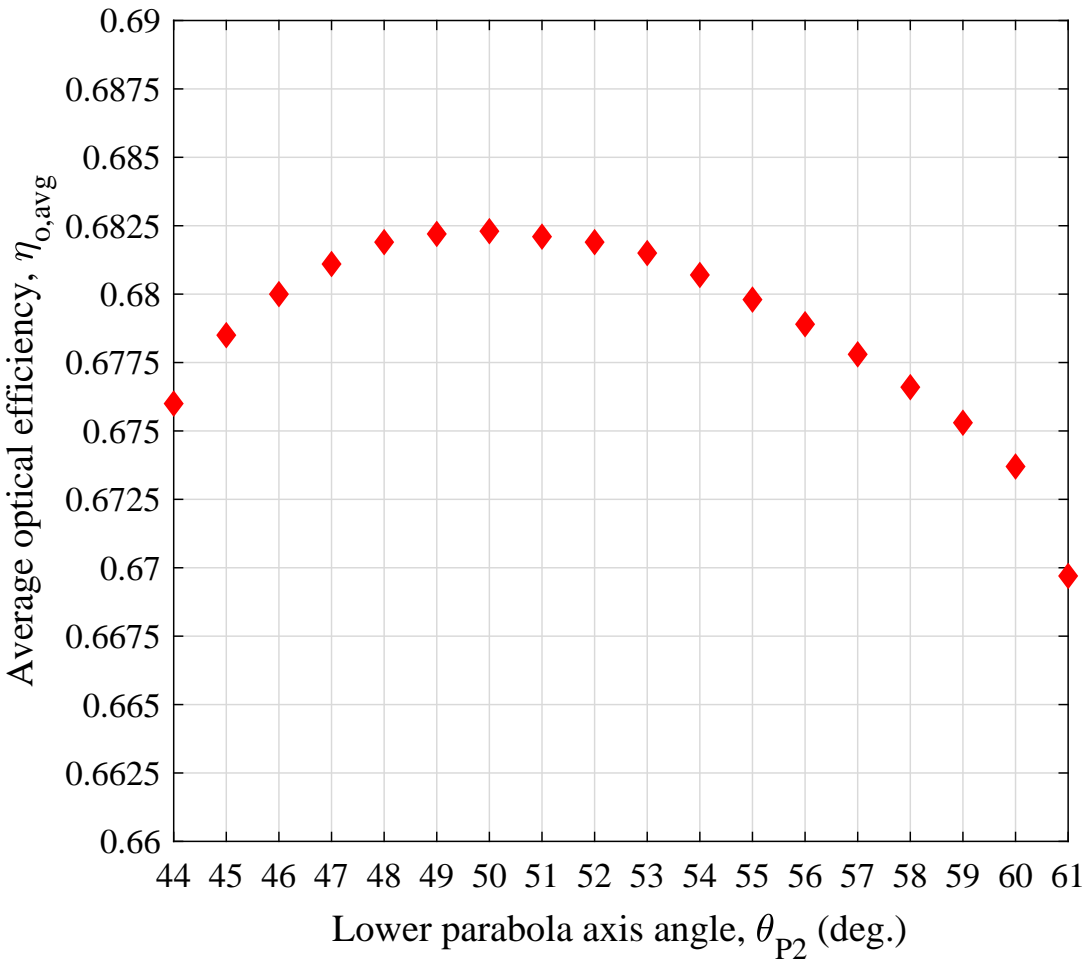
[picture p288: page 1]

Average optical efficiency, o,avg

Lower parabola axis angle, P2 (deg.)
