fsguerreiro/My_thesis/figs/eff-length-eps-converted-to.pdf

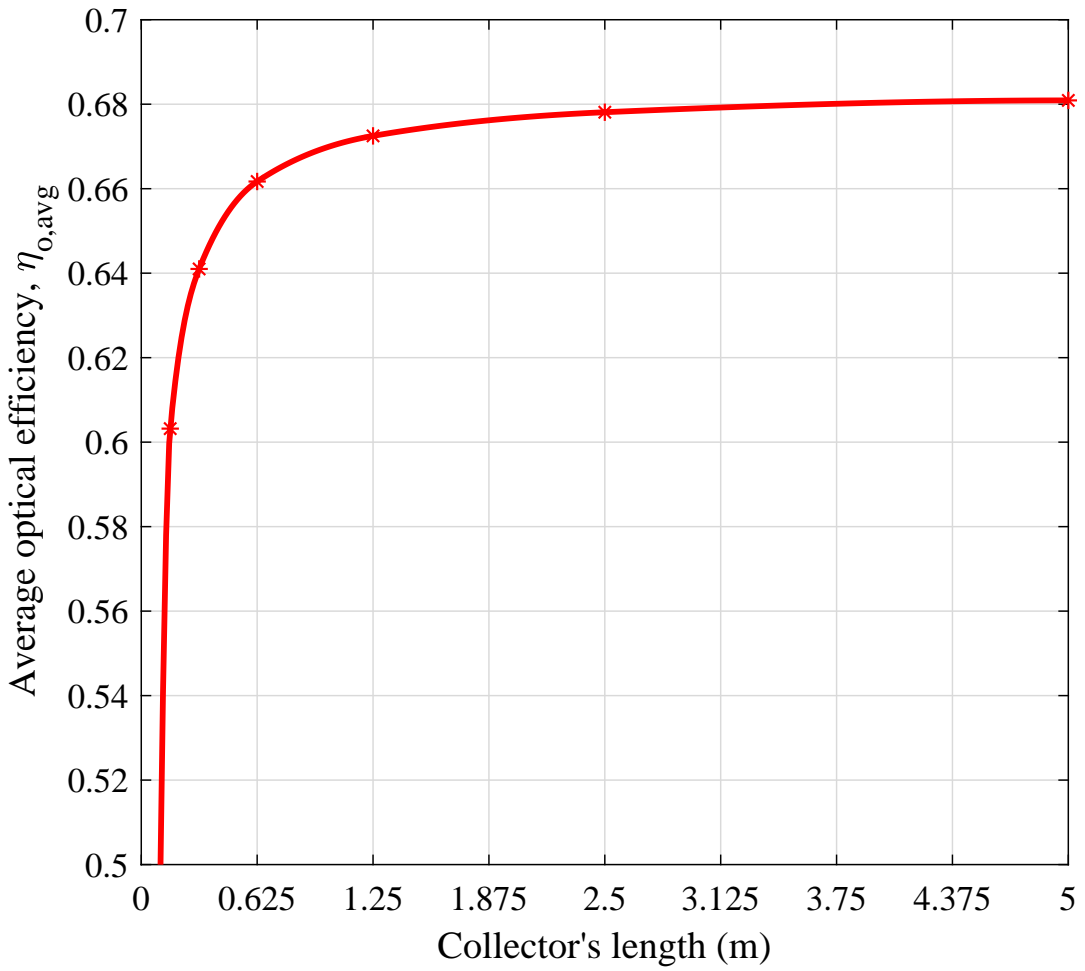
[picture p289: page 1]
Collector's length (m)

Average optical efficiency, o,avg
