fsguerreiro/My_thesis/figs/eff_length-eps-converted-to.pdf

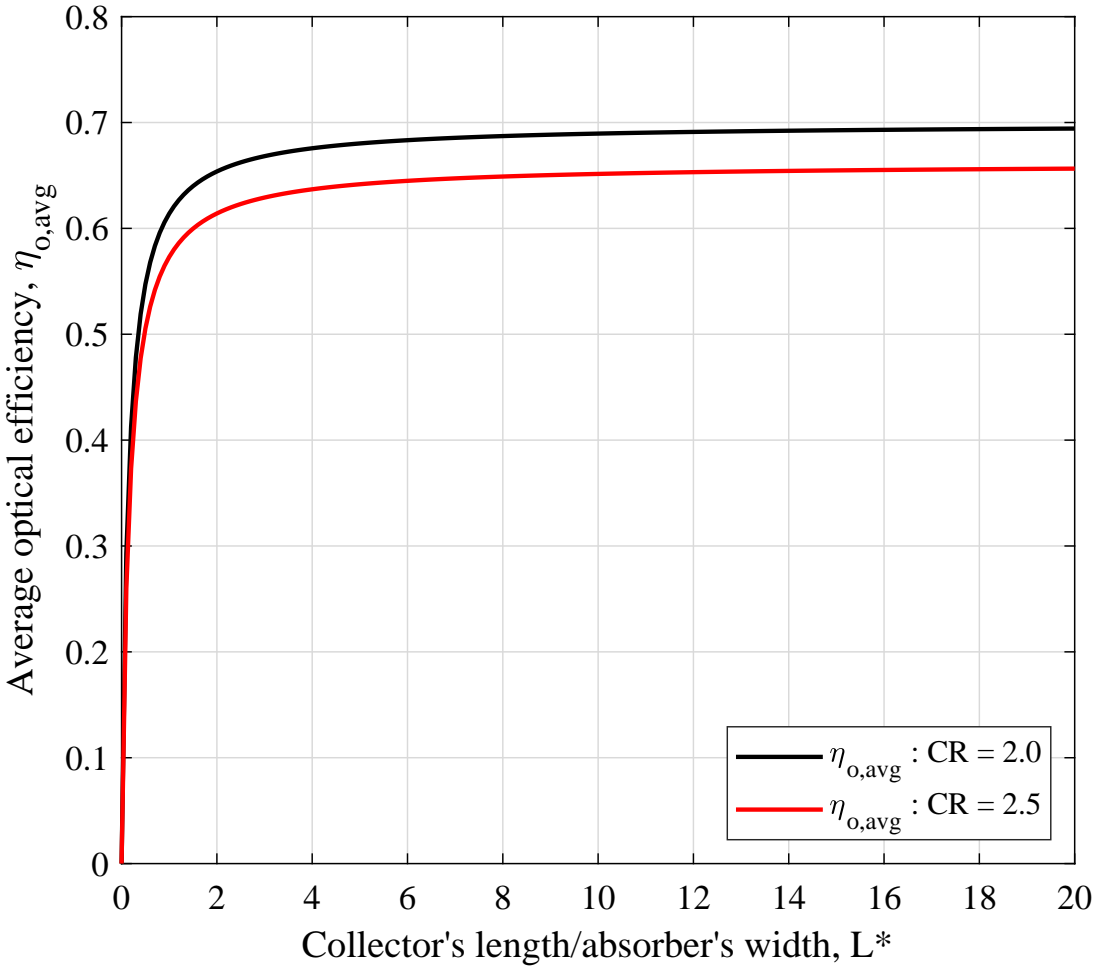
[picture p290: page 1]

Average optical efficiency, o,avg

: CR = 2.0
o,avg | : CR = 2.5

Collector's length/absorber's width, L*
