fsguerreiro/My_thesis/figs/eff_region2-eps-converted-to.pdf

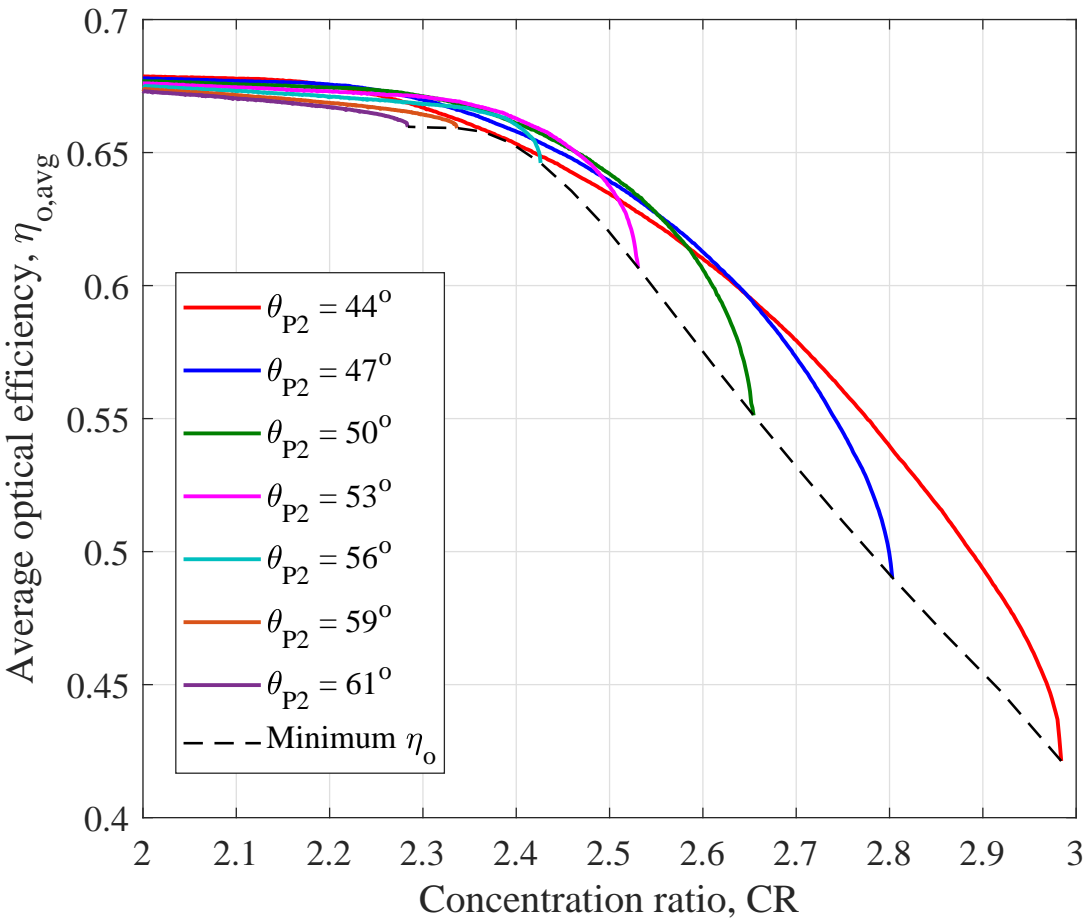
[picture p291: page 1]

Average optical efficiency, o,avg

Minimum | o

Concentration ratio, CR
