fsguerreiro/My_thesis/figs/exp_curve-eps-converted-to.pdf

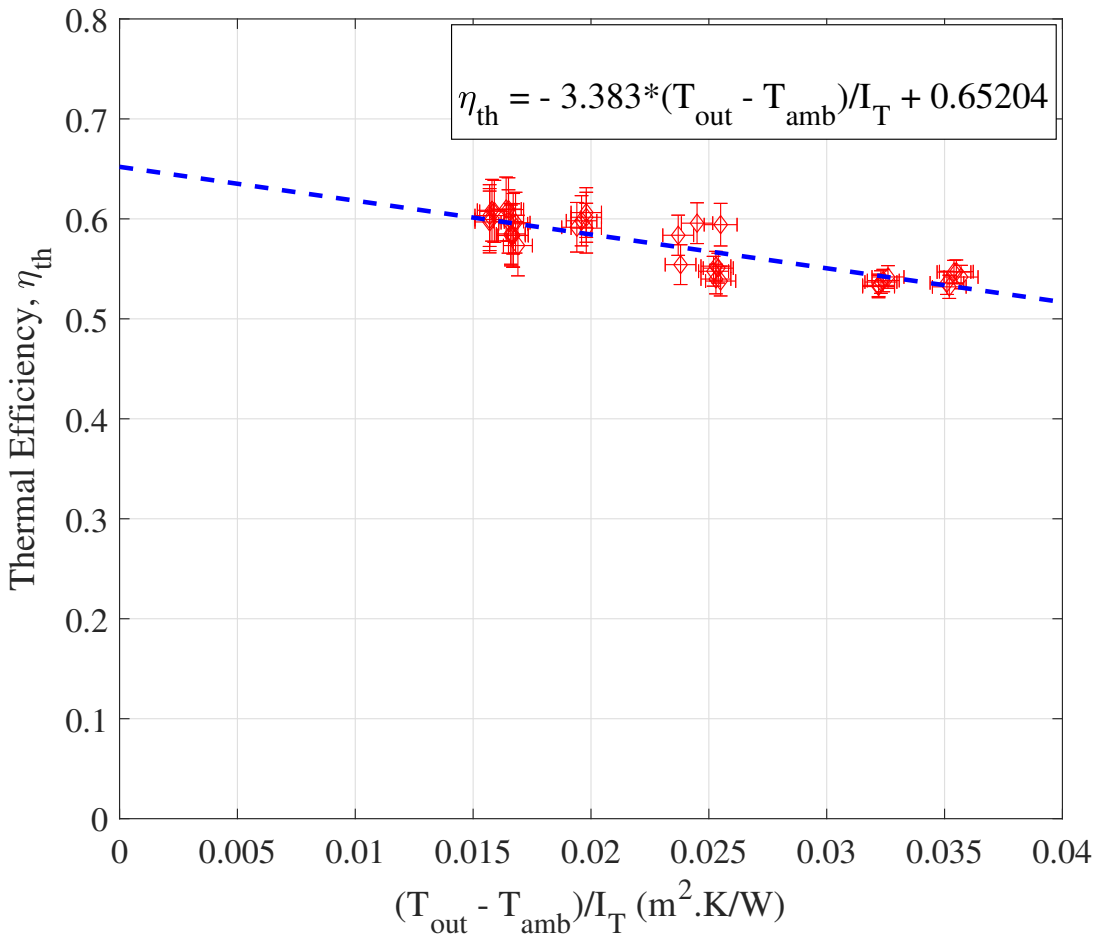
[picture p292: page 1]
out; - Tamb)/IT

Thermal Efficiency, th
