fsguerreiro/My_thesis/figs/figTS-eps-converted-to.pdf

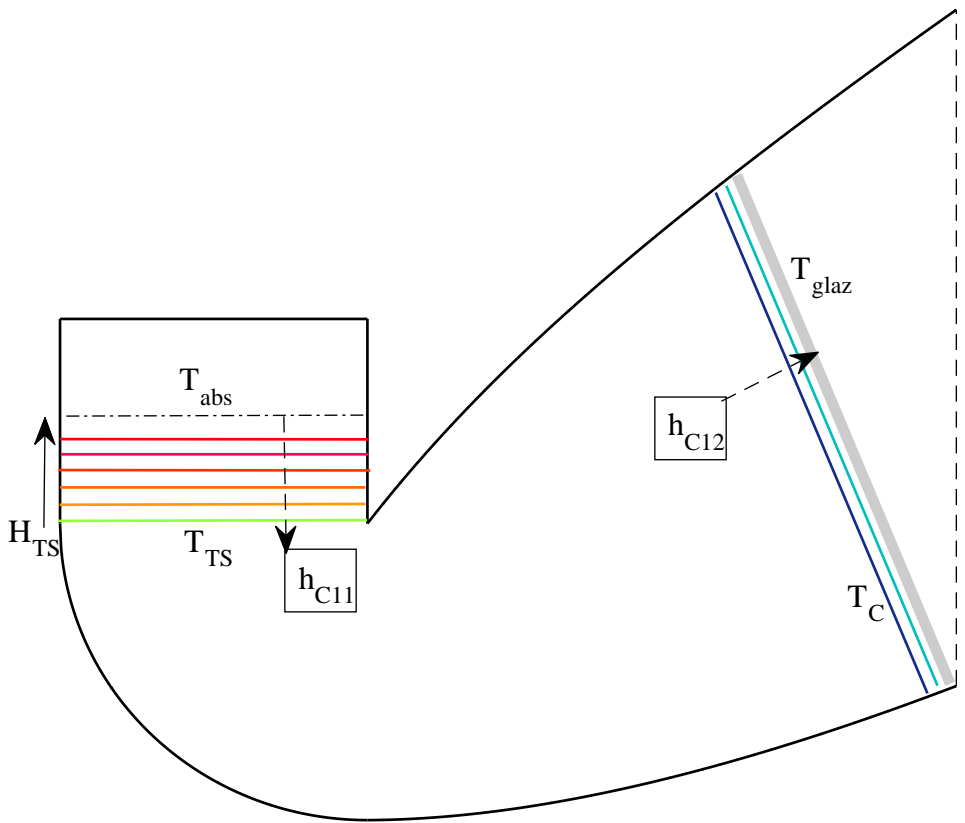
[picture p293: page 1]
TglazT; Tabs; TTS; HTS
