fsguerreiro/My_thesis/figs/length-eps-converted-to.pdf

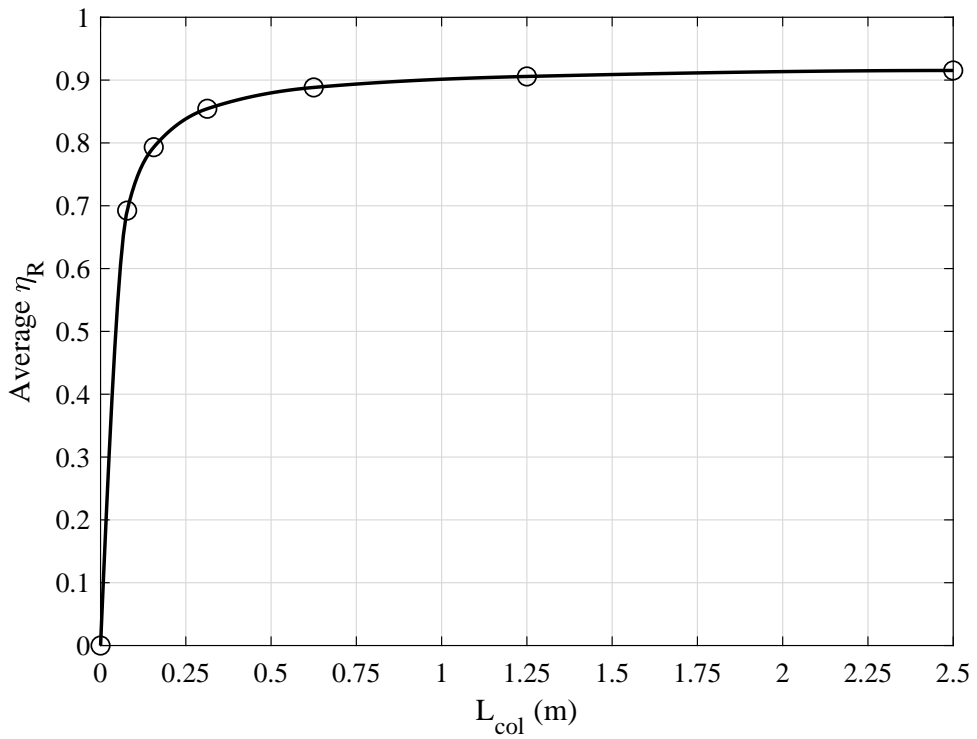
[picture p294: page 1]
Lcol (m); Average
