fsguerreiro/My_thesis/figs/length_variance-eps-converted-to.pdf

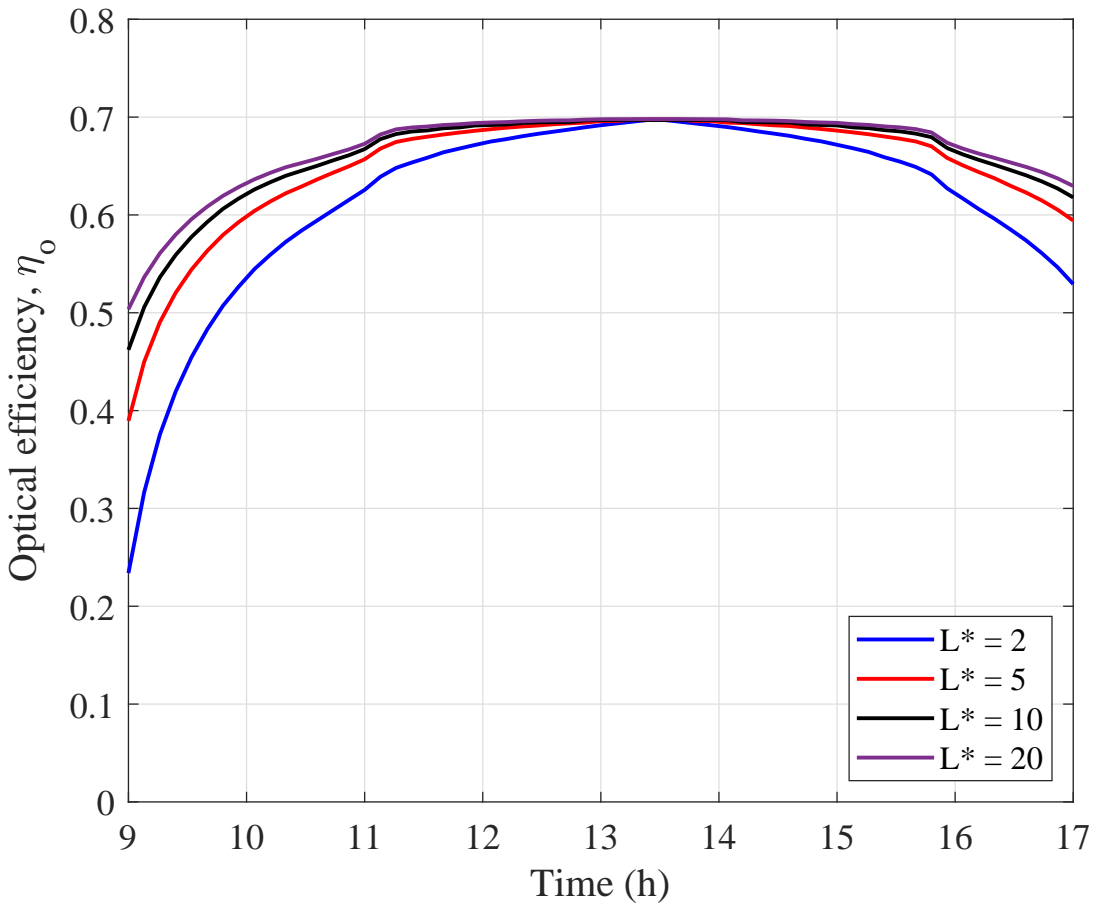
[picture p295: page 1]
Time (h); Optical efficiency,
