fsguerreiro/My_thesis/figs/opt-avg-hts-eps-converted-to.pdf

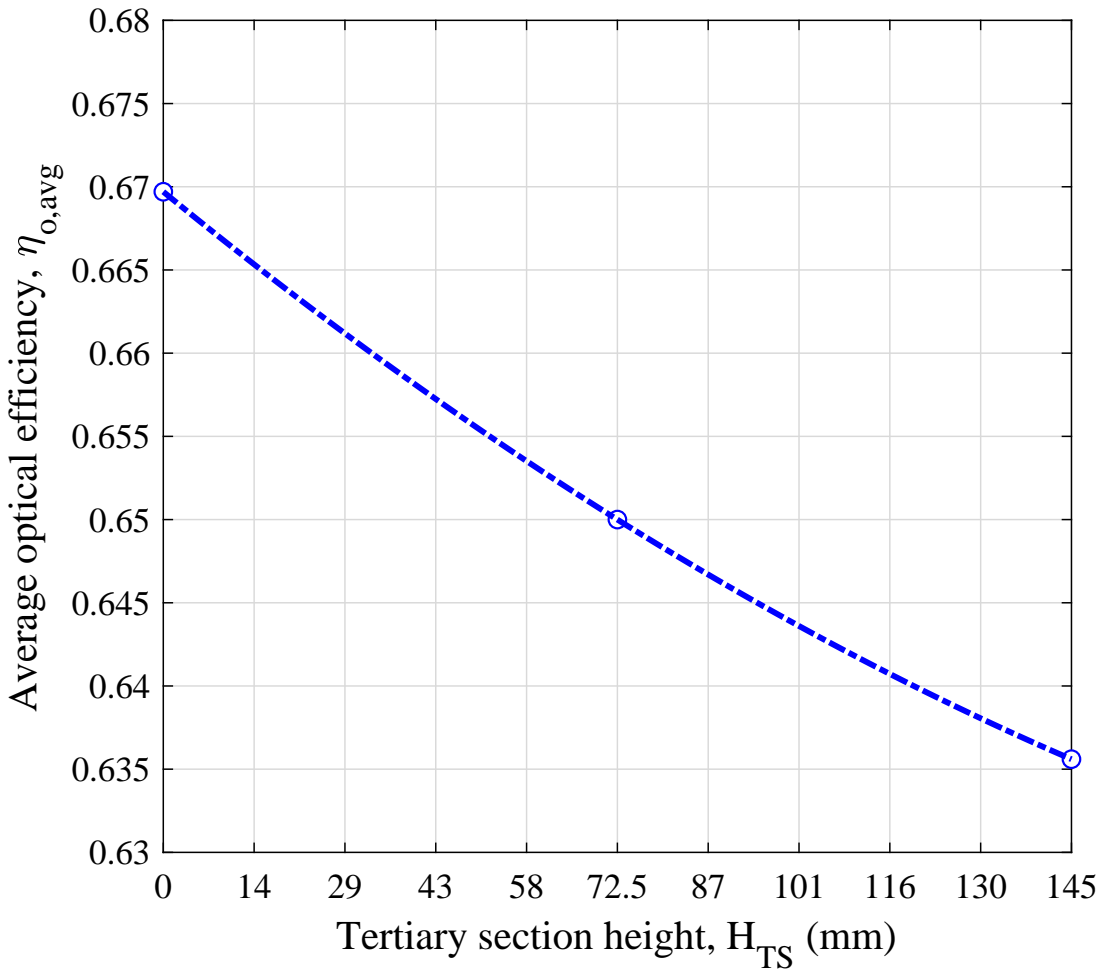
[picture p296: page 1]

Average optical efficiency, o,avg

Tertiary section height, HTS (mm)
