fsguerreiro/My_thesis/figs/opt-eff-3hts-eps-converted-to.pdf

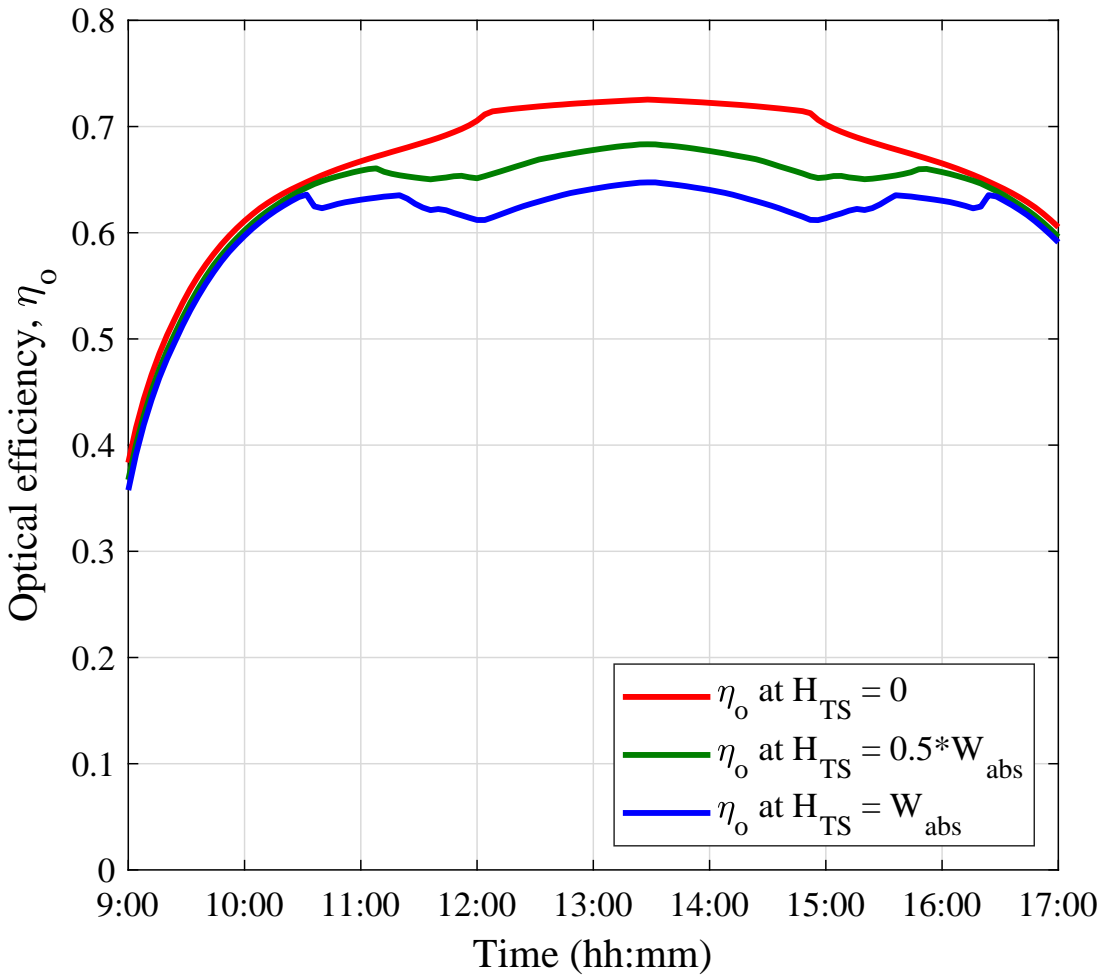
[picture p297: page 1]
Optical efficiency,

at HTS = 0 o at HTS = 0.5*Wabs o

at HTS = Wabs o

Time (hh:mm)
